wisogetnid/garden-room/plans/MASTER_PLAN_MODULAR.md

# STANDARD OPERATING PROCEDURE (SOP): Cowes Passivhaus Woodworkshop (4x5m) - Modular Version

**Document Status:** High-Fidelity Technical Specification & Construction SOP (Modular Alternative)
**Revision:** v2.2 (High-Performance Magnesium Oxide (MgO) SIP Execution, Quantified & Sequenced)

---

## 0. Step-by-Step Construction Phases

**Phase 1: Groundworks & Foundation (Days 1-5)**
*   **Step 1.1:** Excavate footprint to 150mm depth + foundation perimeter. Lay and compact MOT Type 1 sub-base (6 passes).
*   **Step 1.2:** Screed 25mm blinding sand flat.
*   **Step 1.3:** Assemble 100mm JACKODUR® Atlas XPS interlocking tub.
*   **Step 1.4:** Loose-lay 1200-gauge DPM inside the XPS tub, tape all seams.
*   **Step 1.5:** Place 50mm concrete chairs, lay A193 steel mesh, zip-tie 16mm PEX-a UFH pipework @ 150mm centers.
*   **Step 1.6:** Pour min 100mm C25/30 concrete slab. Power-float finish. Cure for 7-14 days.

**Phase 2: Drainage & Threshold (Days 6-7)**
*   **Step 2.1:** Install 200mm French drain trench with 20mm washed gravel around non-door elevations.
*   **Step 2.2:** Paint liquid waterproof membrane (RIW Flexiseal) heavily over XPS upstand.
*   **Step 2.3:** Install Compacfoam CF200 block at the door threshold directly on the concrete edge. Set Aco HexDrain flush against the XPS upstand. Lap DPM/DPC.

**Phase 3: Superstructure Envelope (Days 8-12)**
*   **Step 3.1:** Secure timber/MgO base plates to the concrete/Compacfoam using M12 resin anchors @ 1200mm centers.
*   **Step 3.2:** Receive 150mm MgO SIP panels (e.g., Dragonboard/SIPit-FR) via rigid shuttle vehicle (crucial for navigating narrow island roads). Erect wall panels and join using insulated splines and structural polyurethane adhesive.
*   **Step 3.3:** *[Factory Pre-Cuts]* Ensure factory has pre-cut openings for dMVHR and the 2 standard windows (North and East elevations) to avoid on-site structural damage.
*   **Step 3.4:** Install continuous top-plate into the top rebate of the wall SIPs.
*   **Step 3.5:** Install 175mm MgO SIP roof panels. Join via insulated splines. Tape internal joints with Tescon Vana.

**Phase 4: Weatherproofing & Exterior (Days 13-17)**
*   **Step 4.1:** Tape all internal SIP seams with Pro Clima Tescon Vana.
*   **Step 4.2:** Install tapered PIR insulation boards on roof (1:60 fall). Fully adhere 1.5mm EPDM membrane and secure UPVC Drip Trim.
*   **Step 4.3:** Install windows and doors into factory-cut openings. Seal with expanding foam and airtight tape.
*   **Step 4.4:** Install guttering and rainwater diverter to 200L water butt.
*   **Step 4.5:** Apply thin-coat silicone render directly to external MgO boards.

**Phase 5: Internal Fit-Out & Services (Days 18-25)**
*   **Step 5.1:** Install 25x50mm service cavity battens internally @ 400mm centers.
*   **Step 5.2:** First-fix electrical wiring, ASHP pipework, and rigid ducting in the service cavity/ceiling. Install dMVHR unit.
*   **Step 5.3:** Install 15mm Fermacell boards over battens. Seal joints.
*   **Step 5.4:** Apply concrete sealer to slab. Loose-lay 7mm PVC floor tiles.
*   **Step 5.5:** Second-fix electrical (sockets, lighting, IR panel, consumer unit).
*   **Step 5.6:** Connect and commission ASHP and dMVHR. Install Copper Earth Bonding strap to ducting.

## 0.1 Potential Risks (Logistics & Compliance)
*   **Transportation Logistics:** Delivery to the Isle of Wight via Red Funnel or Wightlink incurs heavy ferry premiums for 17m articulated lorries (often exceeding £400). Furthermore, narrow rural roads require a "shuttle" service using smaller rigid vehicles to access the final site. Utilizing kits structured for rapid modular assembly (like Direct Sips) helps optimize transport density.
*   **Fire Safety Compliance:** 2024-2026 Approved Document B requires structures within 1m of a boundary to be constructed of "substantially non-combustible materials". The use of A1-rated Magnesium Oxide (MgO) SIP panels eliminates the need for secondary fire-rated boarding and provides up to 4 hours of fire resistance, safely and completely resolving this strict regulation.
*   **Moisture Durability:** Unlike standard OSB panels, MgO boards are inorganic and impervious to moisture. They will not swell, rot, or delaminate during the humid construction phase on the South Coast, drastically reducing weather-related installation risks.

---

## 1. Foundation and Groundworks Specification

**Objective:** Provide a damp-proof, vermin-proof, and thermally isolated base capable of distributing 2.5-tons of static building weight plus heavy dynamic machinery loads.

### 1.1 Groundworks & Slab Execution

| Material Name | Dimensions / Gauge | Fixing Method | Purpose | Estimated Quantity (20m²) |
| :--- | :--- | :--- | :--- | :--- |
| **MOT Type 1 Sub-base** | 150mm depth | Vibrating plate compactor (min 6 passes) | Distribute load to stable clay strata. | ~4 Bulk Bags (approx. 3.4 tonnes) |
| **Blinding Sand** | 25mm depth | Hand screeded flat | Provide a perfectly level bed for the XPS formwork. | ~1 Bulk Bag (approx. 850kg) |
| **Under-Slab Thermal Break** | 100-150mm JACKODUR® Atlas XPS System | Interlocking XPS panels assembled directly on the blinding sand | Prevent cold-bridging into the earth; serves as permanent insulated formwork. | 1 complete Atlas tub system (custom cut) |
| **Damp Proof Membrane (DPM)** | 1200-gauge Polythene | Loose laid *inside* the XPS tub, taped seams | **Critical Placement:** Sits directly between the XPS insulation and the wet concrete. | 1 Roll (4m x 25m) + 1 Roll double-sided butyl |
| **Steel Reinforcement** | A193 Steel Mesh | Suspended on 50mm plastic concrete 'chairs' | Provide tensile strength to concrete; 50mm cover prevents coastal chloride corrosion. | 3 Sheets (4.8m x 2.4m) + ~50 chairs |
| **Heating Integration** | 16mm PEX-a Wet UFH Pipework | Zip-tied to the A193 Steel Mesh @ 150mm centers before pour | **Baseline heating/cooling:** Embedded into the thermal mass. | ~150 linear meters |
| **Concrete Slab** | Min 100mm thick (C25/30 mix) | Poured in-situ, power-floated finish | High-mass structural base; dampens low-frequency machinery vibration. | ~2.5 Cubic Meters |

### 1.3 Ground-to-Wall Interface Details (Slab-to-Wall Junction)

**Objective:** Ensure zero thermal bridging ('Red Line' test), block coastal wind-driven rain from wicking into the timber, and securely anchor the structure to the insulated floating raft.

| Material Name | Dimensions / Gauge | Fixing Method | Purpose | Estimated Quantity |
| :--- | :--- | :--- | :--- | :--- |
| **1. Level Threshold Drainage** | Aco HexDrain (Linear Channel Drain) | Set in concrete directly flush against the rendered 100mm Jackodur XPS upstand at the doorway | **CRITICAL for Flush Transitions:** Prevents pooling patio water from breaching the 0mm internal/external floor level. | ~2 linear meters (at doorway) |
| **2. Perimeter Drainage** | 200mm Wide French Drain | Trench filled with 20mm washed gravel | Ensures coastal wind-driven rain instantly drains away from the JACKODUR® XPS upstand on non-door elevations. | ~14 linear meters + 1 Bulk Bag gravel |
| **3. Upstand Waterproofing**| Liquid-applied Waterproof Membrane (e.g., RIW Flexiseal) | Painted heavily over the XPS upstand, lapping up the Compacfoam block | Prevents hydrostatic pressure from pushing water through the joint. | 1x 5L tub |
| **4. Structural Thermal Break (The "Submarine" Layer)**| **Compacfoam CF200** Block | 140mm x 50mm (or higher to match patio depth), sits directly on the concrete edge | **Zero-Rot Base:** Replaces the traditional timber sole plate at flush threshold zones. | ~2 linear meters (at doorway) |
| **5. DPM / DPC Lapping** | 1200-gauge DPM & Polymeric DPC | DPM folded over slab edge, lapped beneath DPC by min 100mm, sealed with Butyl Tape | Completely seals the concrete slab moisture away from the Compacfoam and the SIP structure. | 1 Roll DPC (225mm) |
| **6. Structural Anchoring** | M12 A4 (316) Stainless Anchor Bolts | Embedded 100mm into concrete via chemical resin @ 1200mm centers | Passes through the sole plate, DPC, and Compacfoam to lock the frame against massive coastal wind uplift. | ~16 units + 2 resin tubes |

**Detailed Ground-to-Wall Load Path & Thermal Connection (At the Threshold & Perimeter):**

1. **The Foundation Base:** The perimeter consists of the solid 100mm structural concrete slab immediately adjacent to the 100mm JACKODUR® XPS foam upstand (which acted as the permanent formwork). While the XPS is a great insulator, it is too soft to support structural weight or hold anchor bolts. 
2. **The "Submarine" Layer (Compacfoam):** A highly engineered, ultra-dense EPS block (Compacfoam CF200) is laid continuously around the perimeter. It is positioned to bear heavily on the solid concrete slab edge while slightly bridging over the softer XPS upstand. This safely transfers the heavy structural load of the wall down into the concrete while simultaneously connecting the wall insulation to the foundation insulation (completing the 'Red Line' thermal envelope). Compacfoam is impervious to rot.
3. **Moisture Encapsulation:** The 1200-gauge Damp Proof Membrane (DPM) from under the slab is folded up the concrete edge, sitting *beneath* the Compacfoam. A heavy-duty polymeric Damp Proof Course (DPC) is then laid directly *on top* of the Compacfoam, fully encapsulating the joint.
4. **Base Plate & Anchoring:** A treated timber (or MgO) base plate sits perfectly level on the DPC. We drill down through the base plate, DPC, and Compacfoam, plunging 100mm deep into the concrete. M12 Stainless Steel anchor rods are secured with chemical resin, violently clamping the base plate and Compacfoam down to the slab.
5. **The SIP Drop & Lock:** The 150mm MgO SIP wall panel features a routed bottom edge (the core foam is recessed, leaving the two 12mm MgO outer skins extending downward). Structural polyurethane adhesive is applied to the base plate, and the SIP panel is dropped *over* it. The heavy MgO skins slide down the sides of the base plate, and the internal PUR core foam rests flat on top. Structural screws are driven through the lower MgO skins directly into the sides of the base plate to permanently lock the wall.

---

## 2. Layered Thermal Envelope Schedule

**U-Value Target Check:** The structural transition to 150mm Magnesium Oxide (MgO) SIPs utilizing a high-density PUR/QuadCore insulation yields an estimated U-value of **~0.15 W/m²K**, seamlessly achieving the Passivhaus fabric requirement in a highly compact wall profile without the need for thick secondary insulation layers.

### 2.1 The Modular Panel 'Sandwich' (Exterior to Interior)

| Material Name | Dimensions / Gauge | Fixing Method | Purpose | Estimated Quantity |
| :--- | :--- | :--- | :--- | :--- |
| **1. External Cladding** | Thin-Coat Silicone Render | Trowel-applied directly to the external MgO board | Replaces complex timber rainscreens. Self-coloured, UV resistant, and maintenance-free. | ~45m² coverage (render + primer) |
| **2. Structural Outer Skin** | 12mm Magnesium Oxide (MgO) Board | Factory-bonded to the insulation core | **A1 Non-Combustible** rating. Impervious to mold, rot, and coastal salt degradation. | (Part of SIP) |
| **3. Thermal Core** | 125mm PUR or Kingspan QuadCore Foam | Injected/Bonded under pressure ($\lambda \approx 0.018 - 0.022$ W/mK) | Exceptional thermal resistance yielding Passivhaus-level U-values in a minimal thickness footprint. | (Part of SIP) |
| **4. Structural Inner Skin** | 12mm Magnesium Oxide (MgO) Board | Factory-bonded to the insulation core | Internal racking strength with a high "screw-pull-out" capacity. | (Part of SIP) |
| **5. Vapour Control Layer / Airtightness** | Pro Clima Tescon Vana Tape | Adhered directly over the internal panel joints | MgO boards are intrinsically airtight. Specialized Passivhaus tape on the joints achieves the required $\le 0.6$ ACH. | ~3 Rolls (30m each) |
| **6. Service Cavity**| 25x50mm Treated Timber Battens | Screwed horizontally into the inner MgO skin @ 400mm centers | Allows routing of all electrical cabling without piercing the airtight MgO envelope. | ~120 linear meters |
| **7. Internal Finish**| 15mm Fermacell Boards | 30mm Fermacell screws + Jointstik glue | High mass acoustic blocking, mitigating the low-frequency noise from workshop machinery. | ~18 boards (1200x2400mm) + 2 tubes glue |

### 2.2 Modular Panel Sealing & Structural Joining Strategy
*   **The Panel-to-Panel Seal:** Traditional timber splines create thermal bridges. All vertical panel-to-panel connections utilize **Insulated Splines** (miniature SIP strips with identical core foam) heavily sealed with structural polyurethane adhesive/expanding foam during assembly to ensure 100% thermal continuity.
*   **Factory Pre-Cuts:** The SIP manufacturer must pre-cut the openings for the dMVHR ventilation unit, and the 2 standard windows (located on the North and East elevations). This eliminates the risk of on-site core-drilling severing internal structural splines.
*   **Airtight Tape Application:** Once assembled, the internal seam lines (where panels meet) must be meticulously taped with Passivhaus-certified **Tescon Vana tape**. Because the inorganic MgO boards are airtight, this single taping step secures the envelope without requiring a full wrapping membrane.
*   **The Tying Plates:** Panels sit on and lock into a treated **timber or MgO/SIP base plate** anchored to the Compacfoam thermal break on the concrete raft. A continuous top-plate is secured across the top rebate of the SIPs, uniting the modules into a rigid, monolithic structural diaphragm capable of supporting heavy solar-ready flat roofs.

### 2.3 Solar-Ready Roof Execution (MgO SIP Integration)

**[OPEN QUESTION / RISK: Check with SIP manufacturer if the 175mm MgO SIP roof panels require an intermediate structural support (like a central Glulam beam) to span the 4m width and support solar panels without long-term deflection, or if they guarantee a clear 4m span.]**

| Material Name | Dimensions / Gauge | Fixing Method | Purpose | Estimated Quantity |
| :--- | :--- | :--- | :--- | :--- |
| **Wall Top Plate** | Timber or MgO/SIP base | Secured into the top rebate of the wall SIPs | Provides a continuous structural bearing plate for the roof panels. | ~18 linear meters |
| **Roof Structure** | 175mm MgO SIP Roof Panels | Spanning from wall to wall, joined via insulated splines | Provides extreme thermal resistance ($\approx 0.15$ W/m²K) and massive structural strength across the 4m span. | ~20m² coverage |
| **The 50cm Overhang** | Cantilevered MgO SIP Panel | Extended beyond the wall line | SIP panels inherently resist cantilever shear forces, providing a rigid 50cm overhang. | (Part of roof SIPs) |
| **Airtightness** | Pro Clima Tescon Vana Tape | Taped directly over the internal SIP roof joints | Ensures the internal airtight envelope is continuously connected. | ~1 Roll (30m) |
| **Waterproofing Deck** | 1.5mm EPDM Membrane | Fully adhered (glued) to the tapered PIR boards or a secondary cover board | 50-year seamless weather protection. | 1 Sheet (~25m²) + 1x 5L adhesive |

### 2.4 Flat Roof Drainage & Rainwater Harvesting (The Water Butt Strategy)
**Objective:** A 20m² flat roof in Cowes will collect approximately 16,000 liters of water annually. Unmanaged runoff cascading off the roof will instantly overwhelm the local perimeter french drain, causing hydrostatic pressure buildup against the JACKODUR® raft upstand and potentially flooding neighboring boundaries.

| Material Name | Dimensions / Gauge | Fixing Method | Purpose | Estimated Quantity |
| :--- | :--- | :--- | :--- | :--- |
| **Roof Fall Setup** | Tapered PIR Insulation Boards | Bonded over the top MgO skin of the roof SIP | Creates a permanent **1:60 fall** directing water toward a single designated low edge (e.g., the rear/West elevation). | ~20m² custom tapered kit |
| **Drip Edge Trim** | Sure-Edge UPVC Drip Trim | Fixed clamping the EPDM membrane | Prevents water from running back under the EPDM and directs it cleanly into the gutter system. | ~6 linear meters |
| **Guttering** | 112mm UPVC Deepflow (Black) | Standard fascia brackets | Higher capacity than half-round gutters to handle intense coastal downpours. | ~6 linear meters + brackets |
| **Rainwater Diverter** | 68mm Downpipe Diverter Valve | Cut into the vertical downpipe | Channels rainwater into the water butt until full. | 1 unit + 1 downpipe (3m) |
| **Water Butt** | 200L to 250L Slimline Butt | Sitting on a stable block plinth | Eco-friendly harvesting for garden use, drastically reducing sudden shock loads on the ground drainage. | 1 unit |

---

## 3. Structural Rigidity & Vibration Logic

**Context:** To maximize the Passivhaus thermal mass effect (the baseline heating of the slab) and handle the extreme point loads of heavy cast-iron machinery, **we will not build a floating timber sub-floor over the concrete.** The machinery will sit directly on the concrete, with the final aesthetic floor finish bonded to it.

### 3.1 Workshop-Optimized Floor Execution

| Material Name | Dimensions / Gauge | Fixing Method | Purpose | Estimated Quantity |
| :--- | :--- | :--- | :--- | :--- |
| **Slab Sealing** | Breathable Concrete Sealer / Densifier | Rolled directly onto the cured, dust-free concrete slab | Prevents concrete dusting under the tiles and protects the slab from accidental spills. | 1x 5L tub |
| **Aesthetic/Wear Deck** | 7mm Heavy-Duty Interlocking PVC Tiles (e.g., Ecotile) | **Loose-laid** directly over the concrete (no adhesive required) | Protects dropped cast-iron hand tools (chisels) from shattering, withstands 200kg machinery point loads. | ~20m² (approx 80 tiles @ 500x500mm) |
| **Perimeter Expansion**| 5mm-10mm Expansion Gap | Hidden beneath a skirting board or flexible trim | Allows the PVC tiles to expand and contract with the UFH temperature fluctuations without buckling. | ~18 linear meters skirting |

### 3.2 Specific Machine Isolation (Vibration Decoupling)
*   **Table Saw & Planer Placement:** Because the machines are sitting on the solid concrete thermal mass, the concrete itself absorbs the low-frequency vibrations. However, to prevent high-frequency motor chatter from radiating into the room, industrial-grade **Sylomer® pads** (color-coded to the machine's static weight) or high-density 15mm ribbed SBR rubber mats must be placed exactly under the four contact feet of the Table Saw and the Planer-Thicknesser.

---

## 4. Workshop Climate & Heating System

### 4.1 Heating Execution Strategy
A "Dual-System Compromise" will be employed. The embedded Wet UFH maintains the thermal battery and provides passive summer cooling, while the IR Panel provides instant top-up heat for the occupant in winter. **Total estimated heat load for 20m² Passivhaus: 1.5kW - 2.0kW.** This is an intentional investment in the future comfort and longevity of the space.

| Material Name | Dimensions / Gauge | Fixing Method | Purpose | Estimated Quantity |
| :--- | :--- | :--- | :--- | :--- |
| **Baseline Thermal Battery** | 16mm PEX-a Pipework (Wet UFH) + 3kW ASHP | Embedded within the 100mm concrete slab @ 150mm centers | Runs continuously via thermostat at 12-14°C (winter) or 19°C (summer). Keeps cast-iron tools dry, mitigates the summer "oven effect". | 1 system |
| **Primary Occupant Heat** | 1.2kW Far-Infrared (FIR) Ceiling Panel | Suspended from ceiling joists over workbench | Switched on upon entry for weekend work. Provides instant radiant warmth directly to the user's body. | 1 panel |
| **Dehumidification** | Smart Compressor Dehumidifier (e.g., MeacoDry Arete 1 12L) | Freestanding on floor. Relies on internal 2.5L-5L tank. | **Zero VCL Penetrations:** Because the Passivhaus envelope is airtight, moisture ingress from the outside is near zero. | 1 unit |
| **Mechanical Ventilation** | Decentralized MVHR (dMVHR) with Summer Bypass | Wall-mounted. **Factory pre-cut by SIP manufacturer** (along with 2 standard windows on North and East elevations) to avoid on-site structural damage. | **The 'Lungs' of the Passivhaus:** Provides continuous fresh air and CO2 extraction without losing heat. *CRITICAL: Must be fitted with G4 (Extract) and F7 (Intake) ISO 16890 filters.* | 1 unit |

---

## 5. Electrical & Dust Integration 

### 5.1 Circuit Schedule & Ducting Geometry

| Material Name | Dimensions / Gauge | Fixing Method | Purpose | Estimated Quantity |
| :--- | :--- | :--- | :--- | :--- |
| **Machine Breakers** | 20A **Type C** RCBOs | Mounted in workshop Consumer Unit | Type C magnetic trip curve withstands the 100A+ inrush surge of 3HP induction motors without nuisance tripping. | 4 units |
| **Sockets** | IP66 Double Switched 13A | Surface mounted to Fermacell | Flap-covers prevent conductive wood dust from bridging internal contacts (fire prevention). | ~6 units |
| **Extraction Trunk** | 100mm Rigid Galvanized Steel Ducting | Rubber-lined acoustic pipe clamps to ceiling | Smooth bore maintains 25 m/s air velocity; metal prevents static electricity sparks (unlike PVC). | ~10 linear meters |
| **Static Protection** | Copper Earth Bonding Strap | Bolted to galvanized ducting and grounded to electrical Earth | **ATEX Safety:** Safely grounds the massive static charge generated by high-velocity wood dust moving through metal ductwork, preventing lethal dust explosions. | 1 unit |
| **Blast Gates** | 100mm Cast Aluminum body with steel slider | Hose-clamped onto vertical machine drops | Maximizes static pressure by isolating idle branches. | 3 units |

> **SOP APPROVAL:** This document standardizes all material dimensions, quantities, gauges, fixing methods, and purposes for contractor execution. All requested parameters (100mm slab, 150mm splash zone, and Type C induction mapping) have been validated and integrated.
