wisogetnid/garden-room/prompts/orchestration.md

@architect: Update the Master Plan with the new [specific change, e.g., external wall insulation specs].

Once finished: @foreman, review the Architect's changes and rework the Step-by-Step execution plan. Ensure the weekend tasks are still viable and that we don't leave the timber frame exposed to Cowes' coastal rain while the user is at work during the week.
