wisogetnid/garden-room/prompts/workshop-research-areas.md

## High-Performance Insulation for Year-Round Workshop Use

This prompt focuses on "Phase Change" and "Vapour Control"—essential for a room that goes from cold (daytime) to warm (evening) quickly.

    Prompt for @librarian:
    "Research a 'High-Thermal-Inertia' insulation strategy for a 20m² workshop in Cowes, UK.

        Compare PIR Boards (100mm+) vs. Superior Multi-foil (e.g., SuperFOIL SF40) for evening use. Calculate the 'Warm-up Time' for each when using a 2kW heater in 5°C external temperatures.

        Document the 'Dew Point' risk for a coastal workshop. When I turn on the heat in the evening, where will the condensation form? Research the necessity of a continuous, taped Vapour Control Layer (VCL) on the warm side to protect cast-iron tool tables from 'flash rusting.'

        Research 'Cold Roof' vs. 'Warm Roof' construction for a 5-degree pitch. Which is less prone to interstitial condensation in the humid Isle of Wight climate?

        Find specs for Breathable Membranes (e.g., Tyvek Housewrap) that offer high salt-spray resistance for coastal locations.
        Save to research/insulation_and_climate.md."

## Planning & Permitted Development (PD)

Cowes has specific areas of Conservation and Article 4 Directions (where PD rights are removed). This prompt forces the agent to check the local Isle of Wight Council rules.

    Prompt for @librarian:
    "Conduct a legal audit for a 4x5m (20m²) detached outbuilding in Cowes, Isle of Wight.

        Verify Permitted Development (Class E) height limits: Confirm the 2.5m total height rule if within 2m of a boundary.

        Check the Isle of Wight Council Planning Portal for 'Article 4 Directions' in Cowes that might restrict outbuildings.

        Research the 'Incidental Use' clause: Does a 'Professional Woodworking Workshop' (potentially generating noise/dust) still qualify as 'incidental,' or does it risk being classified as 'Business Use' requiring Full Planning?

        Document Building Regulations Part L and Part P: Since the room is 20m², it is exempt from most Regs unless it’s within 1m of a boundary. Find the 'Non-combustible cladding' requirements (Part B) for buildings between 15m² and 30m² sited near a fence.
        Save to research/planning_and_regs.md."

## Acoustic & Environmental Impact (The "Good Neighbor" Research)

Since you’ll be working weekends and evenings, noise from a planer or table saw will be highly noticeable in a quiet residential area of Cowes.

    Prompt for @librarian:
    "Research noise mitigation strategies for a residential woodworking shop.

        Find the Rw (Weighted Sound Reduction Index) for a standard timber wall vs. one with Acoustic Mineral Wool (e.g., Rockwool RWA45) and double-layer 15mm Soundbloc plasterboard.

        Document 'Vibration Decoupling' for the floor: Research using 'Resilient Bars' or 'U-Boats' for joists to stop tool vibrations traveling through the ground to the neighbor's house.

        Research 'Acoustic Hoods' for dust extractors and air-intake silencers.

        Find local Cowes/IOW noise ordinance 'quiet hours' to ensure weekend work is compliant.
        Save to research/acoustic_strategy.md."

## Structural Rigidity & Vibration Damping

A standard garden room floor will "bounce" when a 200kg table saw or planer starts up. This ruins precision and creates noise.

    Prompt for @librarian:
    "Research industrial floor specifications for timber-frame workshops.

        Compare Double-Joisting (300mm centers) vs. Engineered I-Joists for a 4m span to eliminate deflection.

        Document the use of Anti-vibration pads (e.g., Sylomer) between the machinery and the floor.

        Research 'Torsion Box' floor construction for maximum rigidity in small footprints.

        Analyze the impact of a 100mm reinforced concrete 'floating' hearth for heavy machinery vs. a standard 22mm P5 chipboard deck.
        Save to research/structural_vibration.md."

## Power & Electrical Load Management

Woodworking tools like thicknessers and dust extractors have high "startup surges" that can trip standard domestic breakers.

    Prompt for @librarian:
    "Conduct a deep dive into Workshop Electrical Systems (UK BS 7671 2026 standards).

        Research Motor Start-up Currents (Inrush Current) for 3HP induction motors and the necessity of Type C or Type D Breakers (MCBs) to prevent nuisance tripping.

        Document the requirements for a Sub-Main Feed from the house: Calculate the voltage drop for a 25m run of 10mm² or 16mm² SWA (Steel Wire Armoured) cable under a 40A load.

        Research 'Emergency Stop' (E-Stop) circuit integration—is a 'shunted' trip for the whole workshop required for safety?

        Analyze the placement of Dust-proof (IP66) sockets to prevent sawdust ingress causing shorts.
        Save to research/electrical_and_machinery.md."

## Dust Extraction & Air Quality (COSHH Compliance)

In a 20m² space, fine dust (MDF/Hardwood) becomes a health and explosion risk within minutes without a proper "Local Exhaust Ventilation" (LEV) system.

    Prompt for @librarian:
    "Analyze dust management systems for small-scale workshops.

        Compare Single-Stage Bag Extractors vs. Two-Stage Cyclones. Find the CFM (Cubic Feet per Minute) requirements for a 100mm duct run over 5 meters.

        Research 'Static Dissipative' Ducting (Grounding)—document the risk of static discharge in PVC pipes causing sawdust explosions.

        Find specs for M-Class or HEPA filtration units that recycle air back into the room to maintain heat vs. venting outside.

        Research ambient air cleaners (overhead units) and their effectiveness in a 50m³ volume.
        Save to research/dust_extraction_physics.md."

## Foundation & Soil Mechanics (The "Ground" Deep-Dive)

    Prompt for @librarian:
    "Research soil-specific structural risks for 2026. Compare Ground Screws (specifically Grade S235 steel or better) against Mini-piles and Concrete Rafts.

        Find the 'heave' risk and 'shrink-swell' data for clay-heavy soils in the UK/Northern Europe.

        Document the necessary torque requirements for ground screws to support a timber-frame building with a live/dead load of 250kg/m².

        Research sub-floor ventilation—how many air bricks or what size of a 'void' is required to prevent joist rot in a 12m² building?
        Save to research/foundations_structural.md."

## The "Smart" Envelope (Energy & Automation 2026)

    Prompt for @librarian:
    "Investigate 2026 smart-glass and high-spec glazing trends.

        Compare Vacuum Insulated Glazing (VIG) vs. Triple Glazing. Find the U-value difference and the weight-per-square-meter (to see if the timber frame needs extra bracing).

        Research Matter-compatible motorized blind systems that can be integrated into the window frame during construction.

        Find the cost-benefit of Solar Reflective Coatings for South-facing garden rooms to prevent the 'greenhouse effect' without using AC.
        Save to research/glazing_and_automation.md."

## Thermal Mass vs. Instant Heat (Climate Strategy)

    Prompt for @librarian:
    "Analyze the physics of heating a small, detached timber structure.

        Compare Infrared (IR) Heating Panels (radiant) vs. Air-to-Air Heat Pumps (convection).

        Specifically research 'Heat Up Time' vs. 'Energy Usage' for a building that is used 8 hours a day vs. one used 24/7.

        Look for data on Phase Change Materials (PCM)—can we add a small amount of thermal mass to a timber wall to keep it warm at night?
        Save to research/climate_control_strategy.md."

## The "Sustainability Scorecard" (Materials & Toxins)

    Prompt for @librarian:
    "Conduct a sustainability and health audit of common garden room materials.

        Research the VOC (Volatile Organic Compound) levels in OSB/3 vs. Plywood vs. Medite Tricoya.

        Compare the Embodied Carbon of Siberian Larch cladding (imported) vs. Thermally Modified British Ash or Box Profile Steel.

        Find the 'End of Life' recyclability of EPDM rubber vs. Zinc roofing.
        Save to research/sustainability_audit.md."

## The Moisture & Rust Management Prompt

    Prompt for @librarian:
    "Research a comprehensive 'Moisture & Anti-Corrosion' strategy for a 20m² timber workshop in the coastal environment of Cowes, Isle of Wight.

        The 'Dew Point' Analysis: Calculate the condensation risk for a building that is unheated during the day but heated to 18°C in the evenings. Where is the dew point likely to sit in a wall with 100mm PIR insulation?

        Membrane Specification:

            Compare Vapour Control Layers (VCL) vs. Intelligent/Variable Membranes (e.g., pro clima INTELLO) that can dry towards the inside in summer.

            Specify a Marine-Grade Breather Membrane for the external side that resists salt-spray degradation.

        Tool Protection (Micro-climates):

            Research the use of Desiccant Dehumidifiers (which work at low temperatures) vs. Compressor models for a workshop environment.

            Investigate 'GoldenRod' style dehumidifier heaters for enclosed tool cabinets.

        Ventilation vs. Rust:

            Document the trade-off between Passive Vents (which bring in salty, humid air) and a Mechanical Ventilation Heat Recovery (MVHR) unit for a small 20m² space.

            Analyze how Dust Accumulation acts as a 'sponge' for coastal moisture and accelerates tool corrosion.

        Floor & Ground Moisture:

            Specify the overlap and sealing requirements for the Damp Proof Membrane (DPM) to the Damp Proof Course (DPC) on a timber-sole plate.
            Save findings to research/moisture_and_rust_prevention.md."
