wisogetnid/garden-room/plans/first-draft.md

# **Technical Engineering and Implementation Analysis for a High-Efficiency Insulated Raft Foundation in Cowes**

This technical plan details the construction of a high-efficiency insulated raft foundation for a 4m x 5m wood workshop in Cowes, Isle of Wight. Utilizing the Jackodur Atlas system, this design provides a thermal-bridge-free envelope suitable for Passivhaus-standard performance, optimized for a manual, solo build with restricted site access.

## **1\. Geotechnical Context: Cowes Clay**

The site in Cowes is characterized by cohesive clay (Hamstead Member and Bembridge Marls), which is susceptible to seasonal volume changes.1 A raft foundation is appropriate as it "floats" on the soil, distributing loads evenly to minimize differential settlement in reactive clay. To ensure stability, the structure is decoupled from the clay via a non-frost-susceptible hardcore base, and a specialized drainage system is used to allow for a flush ground-level finish.

## **2\. Technical Specification and Build-Up (Flush Finish)**

This specification is designed for a flush ground-level finish to provide seamless access while maintaining a super-insulated envelope for humidity control.

| Layer | Thickness | Material/Technical Detail |
| :---- | :---- | :---- |
| **Concrete Slab** | 150mm | Reinforced C25/30 mix; serves as the thermal mass for the UFH system.3 |
| **Separation Layer (DPM)** | \<1mm | 1200-gauge DPM placed **over** the insulation to prevent grout loss and act as a moisture barrier. |
| **Main Insulation** | 150mm | Jackodur Atlas XPS ($R\_D \\approx 4.25 \\text{ m}^2\\text{K/W}$); eliminates thermal bridging. |
| **Blinding Layer** | 25mm | Sharp sand; provides a precision-leveled substrate for the insulation elements. |
| **Sub-Base** | 150mm | MOT Type 1; compacted in two 75mm layers for maximum stability. |
| **Total Build-Up** | **475mm** | Total vertical depth from Finished Floor Level (FFL) to the substrate. |

### **Weather-Proofing & Access Strategy**

* **Flush Finish:** The slab is set flush with the ground for aesthetics and access.  
* **Perimeter French Drain:** A 150mm-wide trench filled with 16/32mm clean filter gravel surrounds the structure to break the capillary bridge and direct surface water to the hardcore layer.  
* **Linear Threshold Drain:** An ACO linear drain is installed at the doorway to provide a solid bridge for heavy tools while intercepting water runoff.

## **3\. Logistical Engineering: The Manual Transit Challenge**

Moving materials 30m via a wheelbarrow-width path requires strict volume management.

### **Excavation Volume and Effort**

The Jackodur system requires a 40cm "over-dig" beyond the slab edge for the perimeter elements, creating a 4.8m x 5.8m footprint ($27.84 \\text{ m}^2$).5

* **Total Excavation Depth:** 475mm below natural ground level.  
* **Undisturbed Volume (Bank):** \~13.22 $\\text{m}^3$ of clay subsoil.  
* **Bulked Volume (Loose):** Clay expands by \~30% when disturbed. Total loose material: **\~17.2 $\\text{m}^3$**.6  
* **Transport Logistics:** Moving 17.2 $\\text{m}^3$ with an 85L barrow loaded to 50L (0.05 $\\text{m}^3$) requires approximately **344 round trips**.8  
* **Estimated Duration:** At a rate of 1 $\\text{m}^3$ per 5–8 hours in stiff clay, excavation will take **85 to 135 man-hours**.10

## **4\. Work-Plan: Phased Implementation**

### **Phase 1: Substrate Preparation & Drainage**

1. **Datum Setting:** Establish the FFL using a laser level, flush with the highest natural ground point.  
2. **Manual Dig-Out:** Excavate the area to 475mm depth. Create a 150mm shoulder for the gravel drain and a deeper pocket at the door for the linear drain bedding.  
3. **Hardcore:** Lay 150mm of MOT Type 1 in two 75mm lifts. Compact each lift thoroughly with a hired petrol wacker plate.  
4. **Blinding:** Apply 25mm of sharp sand. Level to a tolerance of $+/- 1$ cm over 5m to ensure the Jackodur boards fit without gaps.5

### **Phase 2: Insulation, Membrane & UFH**

1. **Jackodur Installation:** Assemble the 150mm Jackodur Atlas perimeter and area elements according to the custom plan.  
2. **DPM Separation Layer:** Install the 1200-gauge DPM **over** the top of the insulation boards. Lap the DPM up the inside of the vertical formwork upstands and secure it so it can eventually be joined to the wall's DPC.5  
3. **Reinforcement:** Place A393 steel mesh on 40/50mm grade plate spacers (wide bases prevent membrane punctures).12  
4. **UFH Piping:** Secure the 16mm pipe to the mesh at 200mm centers. Pressure test the 100m loop to 6 bar for 24 hours before the pour.14

### **Phase 3: Threshold & Concrete**

1. **Linear Drain:** Bed the threshold drain channel on 50mm of concrete at the doorway. Ensure the grate is 3-5mm below the slab level.  
2. **Line Pump Pour:** Pump 3.5 $\\text{m}^3$ of C25/30 concrete from the parking area via a 30m flexible hose.16  
3. **Finishing:** Level the concrete flush with the Jackodur formwork and the threshold drain edge.5  
4. **Perimeter Fill:** Once set, fill the remaining 150mm trench with 16/32mm clean filter gravel.

## **5\. Tools, Consumables, and Price Points (Isle of Wight Estimates)**

| Item | Quantity/Spec | Est. Cost (inc. VAT) | Source |
| :---- | :---- | :---- | :---- |
| **Jackodur Atlas (150mm)** | 20 $\\text{m}^2$ System | £2,300 \- £2,700 |  |
| **MOT Type 1** | 10 Bulk Bags | £550 \- £620 | 18 |
| **Sharp Sand** | 1 Bulk Bag | £62 \- £68 | 20 |
| **A393 Steel Mesh** | 4 Sheets (2.0m x 3.6m) | £250 \- £320 | 22 |
| **Concrete C25/30** | 3.5 $\\text{m}^3$ (inc. pump mix) | £550 \- £650 | 24 |
| **Concrete Line Pump** | 1 Day Hire | £280 \- £350 | 25 |
| **Linear Threshold Drain** | 1m Kit \+ Connectors | £50 \- £80 |  |
| **Filter Gravel (16/32mm)** | 1 Bulk Bag | £65 \- £75 | 21 |
| **Soil/Clay Skips** | 4 x 6-yard Inert Skips | £760 \- £820 | 27 |
| **Wacker Plate Hire** | Weekend Hire | £80 \- £100 | 29 |
| **1200g DPM Roll** | 4m x 20m | £40 \- £60 | 31 |
| **UFH 16mm Pipe & Manifold** | 120m Coil \+ 2-Port | £250 \- £350 | 33 |
| **Total Est. Budget** |  | **£5,337 \- £6,273** |  |

#### **Works cited**

1. Geology as a control on landslides on the Isle of Wight: an overview \- NERC Open Research Archive, accessed February 22, 2026, [https://nora.nerc.ac.uk/id/eprint/16091/1/Jenkins\_Landslides\_PGEOLA-D-11-00038R1.pdf](https://nora.nerc.ac.uk/id/eprint/16091/1/Jenkins_Landslides_PGEOLA-D-11-00038R1.pdf)  
2. Coastal Slope Stability at Cowes and Gurnard, Isle of Wight, accessed February 22, 2026, [https://digitalservices.iow.gov.uk/documents/download/coastal-slope-stability-at-cowes-and-gurnard-isle-of-wight-advice-to-homeowners-leaflet](https://digitalservices.iow.gov.uk/documents/download/coastal-slope-stability-at-cowes-and-gurnard-isle-of-wight-advice-to-homeowners-leaflet)  
3. Concrete Cost per m³ \- Concretecalculate.co.uk, accessed February 22, 2026, [https://concretecalculate.co.uk/concrete-cost-estimators/concrete-cost-per-m%C2%B3/](https://concretecalculate.co.uk/concrete-cost-estimators/concrete-cost-per-m%C2%B3/)  
4. How Much Does Ready Mix Concrete Cost? \- MyBuilder, accessed February 22, 2026, [https://www.mybuilder.com/new-build/price-guides/ready-mix-concrete-cost](https://www.mybuilder.com/new-build/price-guides/ready-mix-concrete-cost)  
5. bewi\_jackodur-atlas\_training.pdf  
6. Bulking Spoil Volume In Excavations \[Free Online Calculator\] \- THS Concepts, accessed February 22, 2026, [https://www.ths-concepts.co.uk/how-to-calculate-earthwork-bulking/](https://www.ths-concepts.co.uk/how-to-calculate-earthwork-bulking/)  
7. Material Density Tables to Help Estimate Earthwork Volumes | Cat | Caterpillar, accessed February 22, 2026, [https://www.cat.com/en\_US/articles/ci-articles/earthwork-volumes-reference-tables.html](https://www.cat.com/en_US/articles/ci-articles/earthwork-volumes-reference-tables.html)  
8. How many wheelbarrows make one cubic? \- Quora, accessed February 22, 2026, [https://www.quora.com/How-many-wheelbarrows-make-one-cubic](https://www.quora.com/How-many-wheelbarrows-make-one-cubic)  
9. 4\. Earthmoving Methods, accessed February 22, 2026, [https://www.fao.org/fishery/docs/CDrom/FAO\_Training/FAO\_Training/General/x6708e/x6708e04.htm](https://www.fao.org/fishery/docs/CDrom/FAO_Training/FAO_Training/General/x6708e/x6708e04.htm)  
10. Manual excavation duration \- 1 Cu. Mtr. \- Planning Planet, accessed February 22, 2026, [https://planningplanet.com/forums/planning-scheduling-programming-discussion/560899/manual-excavation-duration-1-cu-mtr](https://planningplanet.com/forums/planning-scheduling-programming-discussion/560899/manual-excavation-duration-1-cu-mtr)  
11. Excavation Man Hours Guide | PDF | Manufactured Goods | Transport \- Scribd, accessed February 22, 2026, [https://www.scribd.com/document/505106326/EXCAVATION-MAN-HOUR](https://www.scribd.com/document/505106326/EXCAVATION-MAN-HOUR)  
12. 40/50mm Plastic Grade Plate Spacers \- Builder Depot, accessed February 22, 2026, [https://www.builderdepot.co.uk/40-50mm-plastic-grade-plate-spacers](https://www.builderdepot.co.uk/40-50mm-plastic-grade-plate-spacers)  
13. 10mm A393 Steel Reinforcement Mesh 1200mm x 2400mm \- Builder Depot, accessed February 22, 2026, [https://www.builderdepot.co.uk/10mm-a393-high-tensile-steel-reinforcement-mesh-sheet-1200mm-x-2400mm](https://www.builderdepot.co.uk/10mm-a393-high-tensile-steel-reinforcement-mesh-sheet-1200mm-x-2400mm)  
14. Water Underfloor Heating Guide & Installation Instructions \- The Floor Heating Warehouse, accessed February 22, 2026, [https://www.thefloorheatingwarehouse.co.uk/underfloor-heating-guide/](https://www.thefloorheatingwarehouse.co.uk/underfloor-heating-guide/)  
15. Sizing UFH systems when using heat pumps \- P\&H Engineering, accessed February 22, 2026, [https://www.pandhengineering.co.uk/advice/sizing-ufh-systems-when-using-heat-pumps](https://www.pandhengineering.co.uk/advice/sizing-ufh-systems-when-using-heat-pumps)  
16. Concrete Pump Hire | 2 Brothers Concrete & Pumping, accessed February 22, 2026, [https://www.2brothers.uk/services/concrete-pump-hire](https://www.2brothers.uk/services/concrete-pump-hire)  
17. Concrete Pumping Alton \- 01420 370 247, accessed February 22, 2026, [https://www.concrete247.com/services/concrete-pump-hire-alton](https://www.concrete247.com/services/concrete-pump-hire-alton)  
18. Type 1 MOT Granite \- Bulk Bags \- Mick George, accessed February 22, 2026, [https://www.mickgeorge.co.uk/product/aggregates/bulk-bags/type-1-mot-granite](https://www.mickgeorge.co.uk/product/aggregates/bulk-bags/type-1-mot-granite)  
19. MOT Type 1 Sub Base Bulk Bag \- Trade Superstore Online, accessed February 22, 2026, [https://www.tradesuperstoreonline.co.uk/products/g-938251](https://www.tradesuperstoreonline.co.uk/products/g-938251)  
20. 0-4mm Grit Sharp Sand \- Bulk Bag only £47.00 \- KPT Timber, accessed February 22, 2026, [https://www.kpttimber.co.uk/bulk-bags/0-4mm-grit-sharp-sand/](https://www.kpttimber.co.uk/bulk-bags/0-4mm-grit-sharp-sand/)  
21. Building Materials and Aggregates \- Isle of Wight, accessed February 22, 2026, [https://www.westwightskips.com/building-materials/](https://www.westwightskips.com/building-materials/)  
22. A393 Reinforcing Mesh 10mm Dia Bar 3.6mx2m \- Lawsons, accessed February 22, 2026, [https://www.lawsons.co.uk/a393-reinforcing-mesh-10mm-dia-bar-36mx2m-g10060010](https://www.lawsons.co.uk/a393-reinforcing-mesh-10mm-dia-bar-36mx2m-g10060010)  
23. A393 Mesh \- In Stock Now | 10mm Rebar Mesh | RPO \- Reinforcement Products Online, accessed February 22, 2026, [https://www.reinforcementproductsonline.co.uk/a393-standard-mesh.html](https://www.reinforcementproductsonline.co.uk/a393-standard-mesh.html)  
24. Ready Mix Concrete Prices London 2026, accessed February 22, 2026, [https://rmsconcrete.co.uk/ready-mix-concrete-prices-2026/](https://rmsconcrete.co.uk/ready-mix-concrete-prices-2026/)  
25. Ready Mix Concrete: Cost Breakdown 2026 | Try Our Job Estimator Tool \- Checkatrade, accessed February 22, 2026, [https://www.checkatrade.com/blog/cost-guides/ready-mix-concrete-cost/](https://www.checkatrade.com/blog/cost-guides/ready-mix-concrete-cost/)  
26. uk line pump pricing, accessed February 22, 2026, [http://concretepumping.com/topic/uk-line-pump-pricing](http://concretepumping.com/topic/uk-line-pump-pricing)  
27. Isle of Wight Skip Hire, accessed February 22, 2026, [https://www.westwightskips.com/skip-hire-on-the-isle-of-wight/](https://www.westwightskips.com/skip-hire-on-the-isle-of-wight/)  
28. Skip Hire Prices \- Isle of Wight Skip Hire, accessed February 22, 2026, [https://www.isleofwightskiphire.co.uk/skip-prices/](https://www.isleofwightskiphire.co.uk/skip-prices/)  
29. Wacker Medium Petrol Compactor Plate \- Island Hire Centre, accessed February 22, 2026, [https://www.islandhirecentre.co.uk/product/56/Medium-Petrol-Compactor-Plate/](https://www.islandhirecentre.co.uk/product/56/Medium-Petrol-Compactor-Plate/)  
30. Tool hire | TradePoint, accessed February 22, 2026, [https://www.trade-point.co.uk/tool-hire.cat](https://www.trade-point.co.uk/tool-hire.cat)  
31. Visqueen Radon R400 Membrane 4m x 20m (80m2) | insulationuk.co.uk, accessed February 22, 2026, [https://www.insulationuk.co.uk/products/visqueen-radon-r400-membrane-4m-x-25m-100sqm](https://www.insulationuk.co.uk/products/visqueen-radon-r400-membrane-4m-x-25m-100sqm)  
32. Visqueen Radon Membrane R400 (4m x 20m) \- Drainage & Civils Direct, accessed February 22, 2026, [https://drainageandcivilsdirect.co.uk/product/visqueen-radon-membrane-r400-4m-x-20m/](https://drainageandcivilsdirect.co.uk/product/visqueen-radon-membrane-r400-4m-x-20m/)  
33. 20m2 Water Underfloor Heating Kit \- Renewable Products Warehouse, accessed February 22, 2026, [https://renewableproductswarehouse.co.uk/products/20m2-underfloor-heating-kit](https://renewableproductswarehouse.co.uk/products/20m2-underfloor-heating-kit)  
34. Single Circuit Mixing Underfloor Manifold Valve Unit \- Up To 20m2, accessed February 22, 2026, [https://theunderfloorheatingsite.co.uk/shop/water-under-floor-heating/underfloor-heating-manifolds/single-circuit-mixing-valve-unit-up-to-20m2/](https://theunderfloorheatingsite.co.uk/shop/water-under-floor-heating/underfloor-heating-manifolds/single-circuit-mixing-valve-unit-up-to-20m2/)
