wisogetnid/garden-room/research/passivhaus-requirements-research.md

# **Technical Specification and Certification Roadmap: Elevating the Cowes Woodworkshop to Passive House Standards**

The realization of the Cowes Passivhaus Woodworkshop, as outlined in the provided master plan, represents an ambitious intersection of industrial utility and high-performance building science. Achieving the Passive House standard for a small-scale, detached structure requires a rigorous departure from conventional UK garden room construction. While traditional outbuildings are often exempted from the stringent thermal requirements of Approved Document Part L, the commitment to the Passive House standard necessitates a holistic, fabric-first strategy that addresses the unique thermodynamic challenges inherent in small buildings.1 At the core of this endeavor is the fundamental requirement to minimize energy demand for heating and cooling to less than 15 kWh/m² per year, while ensuring a level of airtightness—specifically $\\leq 0.6$ air changes per hour at 50 Pascals—that is nearly twenty times more demanding than standard UK building regulations.4  
The physics of small-scale structures introduces a significant hurdle known as the surface-area-to-volume ($A/V$) ratio. In larger buildings, the ratio of the external envelope to the internal heated volume is relatively low, providing a natural buffer against heat loss. However, a garden workshop typically possesses a high $A/V$ ratio, meaning there is a larger proportional "skin" through which energy can be transferred. This physical reality dictates that for the Cowes workshop to achieve certification, its insulation levels must be significantly higher than those of a larger detached house to compensate for the higher relative heat loss.7 This report analyzes the existing master plan against the international Passive House criteria, providing detailed engineering pathways to ensure the structure meets the rigorous demands of the Passive House Institute.2

## **The Thermodynamics of Small-Scale Detached Structures**

When assessing the feasibility of Passive House standards for the workshop, one must first address the "small house problem." In building modeling, energy demand is often expressed as a function of the treated floor area. For a structure like the Cowes workshop, which may occupy a footprint of only 20 to 30 square meters, the heat loss through every junction, window frame, and door threshold becomes disproportionately significant.10 The Passive House Planning Package (PHPP) accounts for these non-linearities, but it often reveals that smaller buildings require "super-insulation" thicknesses approaching 300mm to 400mm to achieve the same annual heating demand as a larger building with 200mm of insulation.7  
The environmental context of Cowes, located on the Isle of Wight, adds a layer of complexity regarding maritime humidity and wind loading. High wind speeds increase the pressure differential across the building envelope, which can exacerbate any minor leaks in the air barrier.12 Consequently, the airtightness strategy must not only meet the $n\_{50} \= 0.6$ ACH threshold but must also be robust enough to withstand fluctuating coastal pressures without degrading over time.14

| Metric | Passive House Requirement | UK Building Regulations (Part L 2021\) | Cowes Workshop Target |
| :---- | :---- | :---- | :---- |
| Space Heating Demand | $\\leq 15$ kWh/m²/year | $\\approx 40$ \- $60$ kWh/m²/year | $\\leq 15$ kWh/m²/year |
| Primary Energy Demand | $\\leq 60$ kWh/m²/year | N/A | $\\leq 60$ kWh/m²/year |
| Airtightness ($n\_{50}$) | $\\leq 0.6$ ACH @ 50 Pa | $8.0$ $\\text{m}^3/(\\text{h}\\cdot\\text{m}^2)$ | $0.6$ ACH @ 50 Pa |
| Thermal Comfort | $\\leq 10\\%$ hours $\> 25^{\\circ}\\text{C}$ | No specific limit | $\\leq 5\\%$ hours $\> 25^{\\circ}\\text{C}$ |
| Typical Wall U-Value | $0.10 \- 0.15$ W/m²K | $0.18$ W/m²K | $0.14$ W/m²K |

4

## **Substructure and Foundation Engineering**

The master plan specifies the use of the JACKODUR® Atlas XPS System, which is a critical choice for Passive House certification. Conventional foundations often create a massive thermal bridge where the floor slab meets the external walls, allowing heat to conduct directly into the ground.7 The Atlas system solves this by creating an "insulated tub" that completely decouples the structural concrete from the soil.3 This eliminates the perimeter cold bridge and ensures the slab itself becomes a thermal battery, stabilizing the internal temperature.18  
The choice of 150mm of MOT Type 1 sub-base, compacted to distribute loads to the clay strata, provides the necessary structural stability for heavy woodworking machinery.3 In a woodworking context, vibration control is as important as thermal performance. The master plan’s inclusion of Sylomer® pads or SBR rubber mats to decouple machinery from the power-floated concrete slab is a sophisticated measure that protects the building’s airtight seals from mechanical fatigue.3 Continuous vibration could potentially stress the taped joints of the vapor control layer (VCL), making this decoupling essential for long-term airtightness.14  
Moisture management at the foundation level is achieved through a 1200-gauge Polythene Damp Proof Membrane (DPM) with taped seams.1 For Passive House certification, this membrane must be perfectly integrated with the wall’s VCL to form a continuous air barrier. The transition from the floor membrane to the wall VCL is a frequent failure point in blower door tests; therefore, a specialized airtightness tape, such as Pro Clima Tescon Vana, must be used at this junction.3

## **Hybrid Wall Construction: Multi-Foil and Fiber Integration**

The wall assembly described in the master plan is a multi-functional system designed to optimize thermal resistance while maintaining hygrothermal safety.3 The 140mm C24 timber studs, infilled with Rockwool RW3, provide the primary structural and acoustic core.3 However, timber studs themselves have a thermal conductivity ($\\lambda \\approx 0.13 \\text{ W/mK}$) that is significantly higher than the insulation between them ($\\lambda \\approx 0.035 \\text{ W/mK}$), creating what is known as a "repeating thermal bridge".11  
To mitigate this, the master plan incorporates 50mm of rigid wood fiber board applied externally.3 This layer acts as a continuous thermal wrap, "shading" the timber studs from the external environment and significantly reducing the overall U-value of the wall.22 Wood fiber is uniquely suited for this application because it is "vapor-open," allowing moisture within the frame to migrate safely to the outside, thus preventing mold or rot.21  
The integration of SuperFOIL SF19+ multifoil insulation is the technical catalyst that brings the wall U-value down to the target 0.14 W/m²K.3 Multifoil insulation addresses three modes of heat transfer: conduction through its internal wadding, convection through the air gaps it requires, and radiation through its nano-coated foil layers.25 In a maritime climate like Cowes, the radiant barrier property is particularly valuable, as it reflects solar heat gain during summer months, reducing the cooling load on the air source heat pump.27

| Layer | Material | Function | Thickness |
| :---- | :---- | :---- | :---- |
| External Cladding | James Hardie Fibre Cement | Fire-rated rainscreen | 8-10mm |
| Ventilation Path | Timber Battens | Moisture evaporation | 25mm |
| External Insulation | Wood Fibre Board | Thermal bridge elimination | 50mm |
| Core Structure | C24 Timber / Rockwool RW3 | Structure and acoustics | 140mm |
| Radiant Barrier | SuperFOIL SF19+ | Radiation and VCL | 45mm |
| Interior Board | Fermacell | Fire and acoustic mass | 15mm |

1

## **Roof Design: Warm Roof Physics and Solar Future-Proofing**

The workshop’s roof is specified as a "warm roof" design, utilizing 150mm of rigid PIR boards.3 In a warm roof configuration, the insulation is placed above the structural joists, keeping the entire timber structure at a consistent, warm temperature.1 This is superior to "cold roof" designs common in garden rooms, which require complex ventilation paths to prevent condensation within the joist space.1 For Passive House compliance, the roof must achieve a U-value of approximately 0.11 to 0.15 W/m²K, which the 150mm PIR thickness supports.16  
The master plan’s specification of 47x150mm C24 joists at 400mm centers is a critical forward-looking decision.3 Standard roof joists are often spaced at 600mm, but the closer centers are necessary to support the significant dead load of a future solar photovoltaic (PV) array.3 Because the workshop aims for high performance, solar energy will be vital to offset the electrical loads of heavy machinery and the air source heat pump.4  
Waterproofing is provided by a 1.5mm EPDM membrane with a 50-year life expectancy.3 EPDM is highly durable but requires careful detailing at the eaves to maintain the continuity of the airtight layer. The tapered PIR boards, creating a 1:60 fall, ensure that rainwater is efficiently harvested into 200L–250L water butts, aligning the building with broader sustainable water management goals.3

## **The "Red Line" Strategy for Airtightness and Vapor Control**

The most rigorous aspect of Passive House certification is the airtightness requirement of $\\leq 0.6$ air changes per hour ($n\_{50}$).5 This is not merely an energy-saving measure; it is essential for the protection of the building's fabric. If warm, moist indoor air leaks into the cold structure, it will condense, leading to interstitial condensation and structural decay.12  
The master plan utilizes Pro Clima Intello Plus as the primary vapor control and airtightness layer.3 Intello Plus is an "intelligent" membrane; its vapor resistance varies depending on the average humidity.19 In the winter, it becomes more resistant to protect the timber frame from moisture ingress; in the summer, it becomes more permeable to allow the wall to dry toward the inside if necessary.19 This dual-action behavior is particularly important in a woodworking workshop where moisture levels can spike during finishing or wood drying processes.32  
To achieve the 0.6 ACH target, the "Red Line" method must be employed during the design phase. An architect traces a continuous line around the building’s section to represent the air barrier.13 Every time the line is broken—for a pipe, a wire, or a window—a specific detail must be drawn to seal that penetration. In the workshop, the primary penetrations will include:

1. **Electrics:** Sockets should be surface-mounted on the internal Fermacell board to avoid puncturing the VCL, as specified in the master plan’s use of IP66 surface-mounted sockets.3  
2. **HVAC:** The air source heat pump lines and MVHR ducts must use specialized EPDM grommets where they pass through the envelope.14  
3. **Dust Extraction:** If venting outside, this creates a massive $100\\text{mm}$ to $150\\text{mm}$ hole in the air barrier, which requires a specialized airtight damper.35

| Component | Airtightness Material | Typical Failure Point |
| :---- | :---- | :---- |
| Floor to Wall | Tescon Vana Tape | Creases in the membrane at corners |
| Wall to Roof | Intello Plus Overlap | Insufficient adhesive pressure |
| Windows/Doors | Contega Fivo Tape | Incorrect seal to the frame profile |
| Pipe Penetrations | Kaflex/Roflex Grommets | Sizing the grommet too large for the pipe |

14

## **Fenestration: Triple-Glazing and Frame Thermal Performance**

In a garden room, windows and doors are traditionally the weakest thermal links.20 To reach Passive House standards, the workshop must move beyond standard double-glazing. Passive House windows are characterized by whole-window U-values ($U\_w$) of less than 0.8 W/m²K.5 This is achieved through triple-glazing with two low-emissivity coatings and insulated spacers that reduce heat loss at the glass edge.29  
The frames themselves must be highly insulated. Brands such as Internorm, Norrsken, and AT-ECO provide frames made from timber-aluminum composites or uPVC with integrated thermal breaks.37 The master plan notes the importance of compliant doors and windows with safety glazing.3 For a woodworking workshop, the choice of window opening style is critical; "Tilt and Turn" windows are often preferred because they utilize compression seals that provide a more airtight closure than standard sliding or outward-opening casements.19  
A secondary benefit of these high-performance windows is acoustic insulation. The triple-pane configuration, combined with the airtight seals, will significantly reduce the noise of machinery escaping the workshop, which is a vital consideration for garden buildings in residential areas.1

## **Mechanical Ventilation with Heat Recovery (MVHR) and IAQ**

In a highly airtight building, natural ventilation through gaps and cracks is non-existent. Without mechanical ventilation, carbon dioxide, humidity, and pollutants would quickly reach dangerous levels.32 An MVHR system is the mandatory "lung" of a Passive House.42 It extracts stale air and uses its heat to warm incoming fresh air with an efficiency of up to 90%.42  
For the Cowes workshop, the MVHR system must be sized for the volume of the space and the number of occupants. A standard rate of 30 $\\text{m}^3/\\text{h}$ per person is recommended, but in a workshop, the system may need to handle additional particulate filtration.31 The system should include F7 pollen filters to remove external pollutants and protect the heat exchanger from workshop dust.32  
Furthermore, the master plan includes a 1.2kW Far-Infrared (FIR) Ceiling Panel.3 Infrared heat does not warm the air; it warms objects and people directly. This is an ideal complement to an MVHR system because it provides instant comfort for the woodworker even if the air temperature is set to a lower "baseline" of $12\\text{-}14^{\\circ}\\text{C}$ to save energy.3

## **The Industrial Extraction Paradox: Dust vs. Airtightness**

The most significant challenge for a woodworking workshop pursuing Passive House standards is the Local Exhaust Ventilation (LEV) system. Woodworking machinery requires a high-volume dust extractor, which typically moves air at rates between 350 and 900 CFM.48 In an airtight Passive House, if this air is extracted and vented outside, the building will instantly depressurize. This creates a vacuum that can prevent doors from opening, strain the extractor motor, and potentially backdraft any combustion appliances in the main house if they are on a shared system.36

### **Strategy 1: The Internal Recirculating System**

The most efficient approach is to use an extractor with a high-efficiency filter (M-Class or H-Class) that cleans the air and returns it directly to the workshop.33 This keeps the air pressure balanced and preserves the energy used to heat the air.33 The master plan’s emphasis on heavy-mass Fermacell boards and Rockwool insulation will help dampen the noise from an internal extractor.3

### **Strategy 2: Motorized Makeup Air**

If the extractor must vent outside—for example, when using high-VOC finishes or sprays—the building must have an automated makeup air system.49 This involves a motorized damper, such as the Broan MD6TU or MD10TU, which is interlocked with the dust extractor.36 When the extractor turns on, the damper opens to allow fresh outdoor air in at the same rate, preventing depressurization.49 This air should ideally be filtered and tempered to maintain the workshop's comfort levels.49

| Extractor Type | Pros | Cons | Passive House Suitability |
| :---- | :---- | :---- | :---- |
| Internal Recirculating | Retains 100% of heat; maintains pressure | Requires high-grade HEPA filters | High |
| External Vent (Open) | Removes all odors and fine dust | Causes vacuum; loses all heat | Low |
| External Vent (with Damper) | Balanced pressure; high air quality | Higher capital cost; energy loss | Medium |

33

## **Energy Modeling and Internal Heat Gains (IHG)**

The success of a Passive House design is verified through the Passive House Planning Package (PHPP).2 For the Cowes workshop, the modeling must accurately account for the heat generated by woodworking machinery.56 A 3HP table saw or a large wood lathe generates significant sensible heat while running.56 In the winter, these "internal heat gains" (IHG) are beneficial, as they reduce the need for the underfloor heating system.47 However, in the summer, these gains can push the workshop toward overheating.10  
The master plan’s North-facing overhang is an excellent passive design feature that limits direct solar gain while allowing diffuse northern light, which is ideal for woodworking.3 However, the PHPP model will need to verify the risk of overheating during peak summer work sessions. The use of the power-floated concrete slab as high-mass storage is essential here; it can absorb the daytime heat from machinery and release it at night via the MVHR’s "summer bypass" or through night-time purge ventilation.3

## **Planning Permission and Building Regulations in the UK**

Building a garden room in the UK requires adherence to two sets of rules: Planning Permission (which governs aesthetics and location) and Building Regulations (which govern safety and performance).1

### **Permitted Development and Height Constraints**

Under Permitted Development rules, a garden room within 2 meters of a boundary is strictly capped at a total height of 2.5 meters.1 This is a major challenge for a Passive House build because the thick insulation required for the floor (JACKODUR Atlas) and the roof (150mm PIR) can easily take up 500mm to 600mm of the total height.3 A designer must carefully balance the foundation depth and roof pitch to ensure a usable internal ceiling height while remaining under the 2.5m legal limit.59 If the workshop is moved more than 2 meters from the boundary, the height limit increases to 3m for a flat roof or 4m for a dual-pitched roof, which is far more conducive to a high-performance build.59

### **Non-Combustibility and Boundary Rules**

For a garden room between 15 and 30 square meters that is within 1 meter of a boundary, building regulations (Part B) require the structure to be built of "substantially non-combustible materials" to prevent fire spread.30 The master plan’s use of James Hardie Fibre Cement Plank (A2 Fire-rated) for the cladding and Rockwool RW3 (non-combustible) for the wall core is an excellent strategy for compliance in tight garden spaces.1

## **Summary and Implementation Roadmap**

The Cowes Passivhaus Woodworkshop is an achievable goal that requires meticulous attention to the "unseen" details of the building envelope.2 The current master plan provides a robust foundation, particularly with the choice of JACKODUR Atlas XPS and the Pro Clima Intello Plus membrane.3 To finalize the certification path, the following steps are recommended:

1. **PHPP Calculation:** Perform a site-specific energy balance to confirm the insulation thicknesses and window specifications.54  
2. **Airtightness Detailing:** Create a 3D airtightness plan, specifically focusing on the interface between the concrete slab, the timber sole plate, and the Intello Plus membrane.14  
3. **Extraction Design:** Finalize the LEV strategy. A recirculating cyclone with a HEPA filter is the preferred choice for a Passive House environment.33  
4. **Window Specification:** Select a certified triple-glazed window system with a $U\_w$ value $\\leq 0.8$ W/m²K.19  
5. **Interim Testing:** Schedule a blower door test once the air barrier is complete but before the Fermacell boards are installed.14

By following this roadmap, the Cowes workshop will achieve a level of comfort and efficiency that far exceeds standard UK construction, providing a durable and sustainable workspace for decades to come.

#### **Works cited**

1. Garden Room Insulation Guide | Stay Comfortable All Year Round, accessed March 10, 2026, [https://www.buyinsulationonline.co.uk/blog/a-comprehensive-guide-to-garden-room-insulation-in-the-uk](https://www.buyinsulationonline.co.uk/blog/a-comprehensive-guide-to-garden-room-insulation-in-the-uk)  
2. What is Passivhaus?, accessed March 10, 2026, [https://www.passivhaustrust.org.uk/what\_is\_passivhaus.php](https://www.passivhaustrust.org.uk/what_is_passivhaus.php)  
3. MASTER\_PLAN.md  
4. Passivhaus Standard vs Building Regulations \- what are the differences? \- Arbor Architects, accessed March 10, 2026, [https://www.arborarchitects.co.uk/journal/passivhausandbuildingregulations](https://www.arborarchitects.co.uk/journal/passivhausandbuildingregulations)  
5. The complete guide to Passivhaus \- elemental, accessed March 10, 2026, [https://elementallondon.show/features/the-complete-guide-to-passivhaus/](https://elementallondon.show/features/the-complete-guide-to-passivhaus/)  
6. Building for Comfort and Efficiency: Passive House Design and Ventilation \- Fantech, accessed March 10, 2026, [https://www.fantech.net/en-us/expertise/fantech-5-hub/blog/comfort/passive\_house\_design\_and\_ventilation](https://www.fantech.net/en-us/expertise/fantech-5-hub/blog/comfort/passive_house_design_and_ventilation)  
7. Passivhaus \- MDPI, accessed March 10, 2026, [https://www.mdpi.com/2673-8392/1/1/5](https://www.mdpi.com/2673-8392/1/1/5)  
8. What shape is particularly advantageous for a passive house? \- e-genius, accessed March 10, 2026, [https://www.e-genius.at/fileadmin/user\_upload/lernfelder/energieeffiziente\_gebaeudekonzepte/alt/en/web/what\_shape\_is\_particularly\_advantageous\_for\_a\_passive\_house.html](https://www.e-genius.at/fileadmin/user_upload/lernfelder/energieeffiziente_gebaeudekonzepte/alt/en/web/what_shape_is_particularly_advantageous_for_a_passive_house.ht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)  
9. BSD-025: The Passive House (Passivhaus) Standard—A comparison to other cold climate low-energy houses | buildingscience.com, accessed March 10, 2026, [https://buildingscience.com/documents/insights/bsi-025-the-passivhaus-passive-house-standard](https://buildingscience.com/documents/insights/bsi-025-the-passivhaus-passive-house-standard)  
10. Technical Guidance \- Internal Heat Gain Assumptions in PHPP \- Passivhaus Trust, accessed March 10, 2026, [https://www.passivhaustrust.org.uk/guidance\_detail.php?gId=26](https://www.passivhaustrust.org.uk/guidance_detail.php?gId=26)  
11. Thermal insulation \[Passipedia EN\], accessed March 10, 2026, [https://passipedia.org/planning/thermal\_protection/integrated\_thermal\_protection](https://passipedia.org/planning/thermal_protection/integrated_thermal_protection)  
12. Passivhaus Airtightness Testing Guide | PDF | Condensation \- Scribd, accessed March 10, 2026, [https://www.scribd.com/document/344476273/Passivhaus-Airtightness-Guide](https://www.scribd.com/document/344476273/Passivhaus-Airtightness-Guide)  
13. Airtightness and air pressure testing in accordance with the Passivhaus standard, accessed March 10, 2026, [https://www.passivhaustrust.org.uk/UserFiles/File/Technical%20Papers/BRE\_Passivhaus\_Airtightness\_Guide.pdf](https://www.passivhaustrust.org.uk/UserFiles/File/Technical%20Papers/BRE_Passivhaus_Airtightness_Guide.pdf)  
14. Airtightness \- Passivhaus Trust, accessed March 10, 2026, [https://passivhaustrust.org.uk/UserFiles/File/Technical%20Papers/How%20to%20Build%202023/HowToBuild-Ch6.pdf](https://passivhaustrust.org.uk/UserFiles/File/Technical%20Papers/How%20to%20Build%202023/HowToBuild-Ch6.pdf)  
15. What is Airtightness and Why is it Important in a Passivhaus?, accessed March 10, 2026, [https://www.passivhausassociation.com.au/news/what-is-airtightness-and-why-is-it-important-in-a-passivhaus-7gfma](https://www.passivhausassociation.com.au/news/what-is-airtightness-and-why-is-it-important-in-a-passivhaus-7gfma)  
16. Building Regs U Values \- Insulation4Less, accessed March 10, 2026, [https://insulation4less.co.uk/blogs/guides-and-news/building-regs-u-values](https://insulation4less.co.uk/blogs/guides-and-news/building-regs-u-values)  
17. Thermal Bridging Guide | Building Performance Network, accessed March 10, 2026, [https://building-performance.network/wp-content/uploads/2023/03/Thermal-Bridging-Guide-ZCH.pdf](https://building-performance.network/wp-content/uploads/2023/03/Thermal-Bridging-Guide-ZCH.pdf)  
18. How to Build a Passivhaus, accessed March 10, 2026, [https://www.passivhaustrust.org.uk/UserFiles/File/Technical%20Papers/ROT/How%20to%20build%20a%20Passivhaus\_Chapters%201%20to%204(2).pdf](https://www.passivhaustrust.org.uk/UserFiles/File/Technical%20Papers/ROT/How%20to%20build%20a%20Passivhaus_Chapters%201%20to%204\(2\).pdf)  
19. What is Passivhaus & Our 6 Steps to Achieving a Passivhaus Build \- PYC Group, accessed March 10, 2026, [https://pycgroup.co.uk/what-is-passivhaus-our-6-steps-to-achieving-a-passivhaus-build/](https://pycgroup.co.uk/what-is-passivhaus-our-6-steps-to-achieving-a-passivhaus-build/)  
20. Passivhaus Windows UK | Passive House Doors UK \- Wolf Line, accessed March 10, 2026, [https://www.wolfline.co.uk/passivhaus-windows-doors/](https://www.wolfline.co.uk/passivhaus-windows-doors/)  
21. How to build a Passivhaus (second edition) | Passivhaus Trust ..., accessed March 10, 2026, [https://www.passivhaustrust.org.uk/UserFiles/File/Technical%20Papers/How%20to%20Build%202023/HowToBuild-Ch7.pdf](https://www.passivhaustrust.org.uk/UserFiles/File/Technical%20Papers/How%20to%20Build%202023/HowToBuild-Ch7.pdf)  
22. Wood Fibre Insulation: Cross Laminated Timber Applications \- GreenSpec, accessed March 10, 2026, [http://www.greenspec.co.uk/building-design/woodfibre-xlam-wall/](http://www.greenspec.co.uk/building-design/woodfibre-xlam-wall/)  
23. TimberBoard Wood Fiber Insulation | TimberHP, accessed March 10, 2026, [https://www.timberhp.com/products/timberboard](https://www.timberhp.com/products/timberboard)  
24. Superfoil SF19+ | Versatile Use | Nationwide Delivery \- National Insulation Supplies, accessed March 10, 2026, [https://www.nationalinsulationsupplies.com/products/superfoil-sf19-45mm-10m-x-1-2mm](https://www.nationalinsulationsupplies.com/products/superfoil-sf19-45mm-10m-x-1-2mm)  
25. SuperFOIL SF19+: Advanced Multifoil Insulation for Enhanced Efficiency, accessed March 10, 2026, [https://www.superfoil.co.uk/products/multifoil-insulation/sf19/](https://www.superfoil.co.uk/products/multifoil-insulation/sf19/)  
26. SuperFOIL SF19+ Multi-layer Foil Insulation \- Roofing Megastore, accessed March 10, 2026, [https://www.roofingmegastore.co.uk/superfoil-sf19-multi-layer-foil-insulation.html](https://www.roofingmegastore.co.uk/superfoil-sf19-multi-layer-foil-insulation.html)  
27. SuperFOIL \- Roof Giant, accessed March 10, 2026, [https://www.roofgiant.com/resources/files/brochure\_19.pdf](https://www.roofgiant.com/resources/files/brochure_19.pdf)  
28. SuperFoil SF19+ and SF40 Insulation | Warmer Solutions, accessed March 10, 2026, [https://www.warmersolutions.co.uk/superfoil-insulation/](https://www.warmersolutions.co.uk/superfoil-insulation/)  
29. U-Value Calculator (Walls, Floors & Roofs) \- Concretecalculate.co.uk, accessed March 10, 2026, [https://concretecalculate.co.uk/building-regulations-calculators/u-value-calculator-walls-floors-roofs/](https://concretecalculate.co.uk/building-regulations-calculators/u-value-calculator-walls-floors-roofs/)  
30. Do You Need Building Regulations for Garden Rooms \- My Outhouse, accessed March 10, 2026, [https://myouthouse.co.uk/blog/garden-room-building-regulations/](https://myouthouse.co.uk/blog/garden-room-building-regulations/)  
31. 8 Building services \- How to build a Passivhaus (second edition ..., accessed March 10, 2026, [https://passivhaustrust.org.uk/UserFiles/File/Technical%20Papers/How%20to%20Build%202023/HowToBuild-Ch8.pdf](https://passivhaustrust.org.uk/UserFiles/File/Technical%20Papers/How%20to%20Build%202023/HowToBuild-Ch8.pdf)  
32. PASSIVBLOG: How Passive House Can Improve Indoor Air Quality \- Australian Passivhaus Association, accessed March 10, 2026, [https://www.passivhausassociation.com.au/news/passivblog-a-breath-of-fresh-air-how-passive-house-can-improve-indoor-air-quality](https://www.passivhausassociation.com.au/news/passivblog-a-breath-of-fresh-air-how-passive-house-can-improve-indoor-air-quality)  
33. Effective Dust Extraction for Cabinetmaking Workshops, accessed March 10, 2026, [https://dustarrest.com/blogs/dust-knowledge-hub/effective-dust-extraction-for-cabinetmaking-workshops](https://dustarrest.com/blogs/dust-knowledge-hub/effective-dust-extraction-for-cabinetmaking-workshops)  
34. Passive House Air Tightness, accessed March 10, 2026, [https://passivehouse.com/former\_conferences/Passive\_House\_E/airtightness\_06.html](https://passivehouse.com/former_conferences/Passive_House_E/airtightness_06.html)  
35. Dust collector outside : r/woodworking \- Reddit, accessed March 10, 2026, [https://www.reddit.com/r/woodworking/comments/1e2pcp8/dust\_collector\_outside/](https://www.reddit.com/r/woodworking/comments/1e2pcp8/dust_collector_outside/)  
36. 6-Inch Universal Automatic Make-Up Air Damper with Pressure Sensor Kit \- Broan-NuTone, accessed March 10, 2026, [https://www.broan-nutone.com/en-us/accessory/md6tu](https://www.broan-nutone.com/en-us/accessory/md6tu)  
37. Passive House Glazing | Future-Ready Homes \- AT ECO Windows & Doors Limited, accessed March 10, 2026, [https://www.at-eco.co.uk/solutions/passive-house-windows-doors-energy-efficient.html](https://www.at-eco.co.uk/solutions/passive-house-windows-doors-energy-efficient.html)  
38. Passive House Triple Glazed Windows from Norrsken, accessed March 10, 2026, [https://www.norrsken.co.uk/collections/passive-house-windows](https://www.norrsken.co.uk/collections/passive-house-windows)  
39. Passive House Triple Glazed Doors from Norrsken, accessed March 10, 2026, [https://www.norrsken.co.uk/collections/passive-house-doors](https://www.norrsken.co.uk/collections/passive-house-doors)  
40. Member Directory • Passivhaus Trust, accessed March 10, 2026, [https://passivhaus.uk/directory/](https://passivhaus.uk/directory/)  
41. Passivhaus Windows & Doors \- Internorm UK, accessed March 10, 2026, [https://uk.internorm.com/passivhaus/](https://uk.internorm.com/passivhaus/)  
42. Mechanical Ventilation Heat Recovery | Efficient Airflow for Passive Homes \- Malvern B\&B, accessed March 10, 2026, [https://www.malvernbandb.com/blog/mechanical-ventilation-heat-recovery](https://www.malvernbandb.com/blog/mechanical-ventilation-heat-recovery)  
43. Passivhaus and MVHR Heat Recovery Ventilation \- HRV Group, accessed March 10, 2026, [https://www.hrv-group.com/blog/passivhaus-accredited-mvhr-heat-recovery](https://www.hrv-group.com/blog/passivhaus-accredited-mvhr-heat-recovery)  
44. Vento Mini Single Room Heat Recovery Ventilation Unit | HRV \- Blauberg UK, accessed March 10, 2026, [https://www.blauberg.co.uk/blauberg-mini-air-decentralised-heat-recovery-unit-single-wall-mounted-d-mvhr-ventilator-smart-wifi-control](https://www.blauberg.co.uk/blauberg-mini-air-decentralised-heat-recovery-unit-single-wall-mounted-d-mvhr-ventilator-smart-wifi-control)  
45. Passive House schools – How to go about it \[Passipedia EN\], accessed March 10, 2026, [https://passipedia.org/planning/non-residential\_passive\_house\_buildings/passive\_house\_schools/how\_go\_about\_it](https://passipedia.org/planning/non-residential_passive_house_buildings/passive_house_schools/how_go_about_it)  
46. The Ultimate MVHR Guide \- Paul Heat Recovery, accessed March 10, 2026, [https://www.paulheatrecovery.co.uk/information-on-domestic-ventilation-and-mvhr/mvhr-guide/](https://www.paulheatrecovery.co.uk/information-on-domestic-ventilation-and-mvhr/mvhr-guide/)  
47. Passive house 101, accessed March 10, 2026, [https://localimpactdesign.ca/passive-house/](https://localimpactdesign.ca/passive-house/)  
48. Setting Up the Best Woodworking Dust Collection System, accessed March 10, 2026, [https://www.rockler.com/learn/dust-collection](https://www.rockler.com/learn/dust-collection)  
49. Kitchen Makeup Air: Code-Compliant Ventilation for Tight Homes \- Fantech, accessed March 10, 2026, [https://www.fantech.net/en-us/expertise/fantech-5-hub/blog/safety/if-the-home-is-built-tight-you-need-to-provide-makeup-air](https://www.fantech.net/en-us/expertise/fantech-5-hub/blog/safety/if-the-home-is-built-tight-you-need-to-provide-makeup-air)  
50. Beginner with a small garage \- what are my dust collection options? : r/BeginnerWoodWorking \- Reddit, accessed March 10, 2026, [https://www.reddit.com/r/BeginnerWoodWorking/comments/vz4fq6/beginner\_with\_a\_small\_garage\_what\_are\_my\_dust/](https://www.reddit.com/r/BeginnerWoodWorking/comments/vz4fq6/beginner_with_a_small_garage_what_are_my_dust/)  
51. Wood Working Shop Air Dust \- Merit Research Journals, accessed March 10, 2026, [https://meritresearchjournals.org/articles/pdf/840428102024](https://meritresearchjournals.org/articles/pdf/840428102024)  
52. Makeup air in a Passive House \- Sustainable Engineering Ltd., accessed March 10, 2026, [https://sustainableengineering.co.nz/makeup-air-in-a-passive-house/](https://sustainableengineering.co.nz/makeup-air-in-a-passive-house/)  
53. Broan® 6" Universal Automatic Make-Up Air Damper with Pressure Sensor Kit | Hudson Appliance, accessed March 10, 2026, [https://www.hudsonappliance.com/product/broan-6-universal-automatic-make-up-air-damper-with-pressure-sensor-kit-md6tu-315959](https://www.hudsonappliance.com/product/broan-6-universal-automatic-make-up-air-damper-with-pressure-sensor-kit-md6tu-315959)  
54. Passive House Planning Package (PHPP), accessed March 10, 2026, [https://passivehouse.com/en/home/planning-tools/](https://passivehouse.com/en/home/planning-tools/)  
55. Utilising PHPP as a tool to design low-energy homes \- Allan Corfield Architects, accessed March 10, 2026, [https://acarchitects.biz/self-build-blog/phpp-tool-low-energy-design-ph-cat](https://acarchitects.biz/self-build-blog/phpp-tool-low-energy-design-ph-cat)  
56. INTERNAL HEAT GAINS (IHG) \- Energy-Models.com, accessed March 10, 2026, [https://energy-models.com/internal-heat-gains-ihg](https://energy-models.com/internal-heat-gains-ihg)  
57. PB 41: Planning tools for the summer situation in non-residential buildings \- Passipedia, accessed March 10, 2026, [https://passipedia.org/phi\_publications/pb\_41/planning\_tools\_for\_the\_summer\_situation\_in\_non-residential\_buildings](https://passipedia.org/phi_publications/pb_41/planning_tools_for_the_summer_situation_in_non-residential_buildings)  
58. Passivhaus Overheating: Design it out \- 86 \- Paul McAlister Architects, accessed March 10, 2026, [https://www.pmcarchitects.com/sustainability-information-blog-content/passivhaus-overheating-design-it-out](https://www.pmcarchitects.com/sustainability-information-blog-content/passivhaus-overheating-design-it-out)  
59. Garden Room Building Regulations UK: Complete Guide, accessed March 10, 2026, [https://www.harperlatterarchitects.co.uk/post/garden-room-building-regulations-uk-complete-guide](https://www.harperlatterarchitects.co.uk/post/garden-room-building-regulations-uk-complete-guide)  
60. Planning Permission \- Outbuildings \- Planning Portal, accessed March 10, 2026, [https://www.planningportal.co.uk/permission/common-projects/outbuildings/planning-permission/](https://www.planningportal.co.uk/permission/common-projects/outbuildings/planning-permission/)  
61. Garden Room Building Regs UK: What You Need to Know (2025 Guide) | Arkiplan, accessed March 10, 2026, [https://arkiplan.co.uk/2025/08/29/garden-room-building-regs-uk/](https://arkiplan.co.uk/2025/08/29/garden-room-building-regs-uk/)  
62. Good Practice Guide to Airtightness | Passivhaus Trust, accessed March 10, 2026, [https://www.passivhaustrust.org.uk/UserFiles/File/Technical%20Papers/Good%20Practice%20Guide%20to%20Airtightness%20v10.6-compressed(1).pdf](https://www.passivhaustrust.org.uk/UserFiles/File/Technical%20Papers/Good%20Practice%20Guide%20to%20Airtightness%20v10.6-compressed\(1\).pdf)  
63. Air Tightness in Passive House Design | Resources | Wilson Architectural Design, accessed March 10, 2026, [https://www.wilsonarchitecturaldesign.com/resources/air-tightness-in-passive-house-design](https://www.wilsonarchitecturaldesign.com/resources/air-tightness-in-passive-house-design)
