wisogetnid/garden-room/research/passivhaus-diy-research.md

# **High-Performance Timber Envelope Strategies for DIY Passivhaus Construction: A Comprehensive Technical Analysis of Wall and Roof Systems**

The pursuit of the Passivhaus standard within the context of self-build and DIY construction represents a significant convergence of high-performance building science and decentralized manufacturing. For the modern self-builder, particularly one operating within the constraints of timber-based materials and the avoidance of wet-trade masonry or concrete wall construction, the challenge lies in achieving stringent thermal and airtightness targets through accessible, precision-engineered assemblies. The Passivhaus standard is not merely an energy-efficiency target but a holistic quality assurance framework that ensures occupant comfort, structural longevity, and minimal operational carbon. This report evaluates advanced timber-based wall and roof strategies, scrutinizing the material science, structural logic, and assembly sequences necessary to meet these goals through DIY-compatible methods.

## **Technical Foundations: The Passivhaus Performance Mandate**

To evaluate construction strategies effectively, the baseline performance metrics of the Passivhaus standard must be contrasted with standard UK Building Regulations. As of 2024 and 2025, the UK’s Approved Document L (Part L) has tightened limiting U-values for new dwellings to 0.18 W/m²K for walls and 0.11 W/m²K for roofs.1 However, these regulatory minimums often fall short of the holistic energy balance required by the Passivhaus Institute (PHI). The Passivhaus standard typically requires external wall and roof U-values to sit between 0.10 and 0.15 W/m²K, depending on the specific climate zone.3  
The fundamental equation governing these requirements is the thermal transmittance, expressed as the U-value:

$$U \= \\frac{1}{R\_{si} \+ \\sum \\frac{d\_n}{\\lambda\_n} \+ R\_{se}}$$  
Where $R\_{si}$ and $R\_{se}$ represent internal and external surface resistances, $d\_n$ is the thickness of each material layer in meters, and $\\lambda\_n$ is the thermal conductivity in W/mK. For timber structures, the calculation must also account for the "thermal bridge" effect of structural members, where solid timber ($\\lambda \\approx 0.13$) conducts heat more readily than insulation ($\\lambda \\approx 0.038$).3

### **Comparative Performance Standards 2025**

| Performance Metric | UK Building Regs (Part L 2025\) | Passivhaus Standard (Typical) |
| :---- | :---- | :---- |
| **Wall U-Value** | 0.18 W/m²K | 0.10 – 0.15 W/m²K |
| **Roof U-Value** | 0.11 W/m²K | 0.10 – 0.15 W/m²K |
| **Airtightness (n50)** | 8.0 m³/h·m² @ 50Pa | ≤ 0.6 ACH @ 50Pa |
| **Annual Space Heating Demand** | \~100 – 120 kWh/m²/yr | ≤ 15 kWh/m²/yr |
| **Primary Energy Demand** | N/A | ≤ 135 kWh/m²/yr |
| **Thermal Comfort Range** | N/A | 17°C – 25°C Year-round |

Sources:.1  
The divergence in airtightness requirements is the most critical factor for DIYers. Achieving 0.6 air changes per hour (ACH) requires a continuous, unbroken "red-line" around the building envelope, where every junction between walls, roofs, and floors is meticulously sealed.4 This transition from "loose" construction to a precision-sealed chassis is the primary hurdle for non-professional builders.

## **Structural Strategies: Timber-Based Systems for DIY Assembly**

The requirement to avoid bricks and concrete for walls directs the focus toward four primary timber-based strategies: The Larsen Truss (Twin-Wall), Structural Insulated Panels (SIPs), the WikiHouse (CNC-modular), and the Beattie Passive (Flying Factory) system.

### **The Larsen Truss and Twin-Wall Methodology**

The Larsen Truss is a non-structural or semi-structural outer frame attached to a primary load-bearing inner wall, creating a deep cavity for insulation while minimizing thermal bridging.7 In a typical DIY application, the inner 140mm stud wall provides the structural capacity, while an outer 90mm stud is connected via plywood webs or gussets.7  
The thermal efficiency of the Larsen Truss is significantly higher than that of standard I-joists. Research into thermal bypass indicates that while a standard I-joist provides a continuous path for heat through its solid OSB web, the intermittent gussets of a Larsen Truss reduce this pathway.8 For every $100 spent on nominal R-value, a Larsen Truss delivers approximately $92.50 of actual performance, whereas an I-joist may only deliver $81.10.8 This 10% performance gap is critical when aiming for the 0.10 W/m²K threshold.  
From a DIY perspective, Larsen Trusses can be fabricated on-site using basic carpentry tools or ordered as pre-fabricated panels from specialists like Broadaxe or Timber Innovations.7 These panels often utilize Warmcel (cellulose) insulation, which is blown into the 300mm to 400mm cavities to achieve U-values ranging from 0.13 down to 0.09 W/m²K.7

### **WikiHouse: The Digital Modular Paradigm**

The WikiHouse system, specifically the Skylark 250 series, represents the most accessible "high-tech" solution for the DIYer. It utilizes 18mm spruce plywood or OSB3, precision-cut by CNC machines into interlocking blocks.11 These blocks are assembled off-site or on-site using timber "bow-tie" connectors and mallets, effectively removing the need for traditional framing skills.13  
The Skylark 250 system provides a wall thickness capable of holding 250mm of insulation, achieving a default U-value of 0.14 W/m²K.11 This value can be further improved by adding an external layer of rigid wood fiber insulation board before cladding.16 The modular nature of WikiHouse allows for rapid on-site assembly; a small team can erect a structural chassis in days, provided the foundations (typically screw piles) are level to within \+/- 10mm.12

### **Structural Insulated Panels (SIPs)**

SIPs consist of a rigid insulation core (typically EPS or Polyurethane) sandwiched between two structural OSB skins.17 SIPs are inherently airtight due to their bonded construction and minimal jointing compared to stud frames.17 For a self-builder, SIPs arrive as a "kit" of pre-cut panels that slot together using splines, which significantly reduces the risk of on-site errors in insulation installation.18  
However, SIPs present challenges for the DIYer committed to bio-based materials. Most SIPs use petrochemically derived insulation, and modifications on-site are difficult due to the precision-engineered nature of the panels.18 Furthermore, SIPs require robust mechanical ventilation because the building is essentially "wrapped in plastic," providing zero moisture-buffering capacity compared to wood-fiber or cellulose-based systems.18

### **Beattie Passive and the Flying Factory**

The Beattie Passive system is the first in the UK to achieve full certification for a complete building system from the Passivhaus Institute.5 It utilizes a patented twin-stud timber frame that creates a continuous insulation void around the entire building—walls, roof, and floor—effectively creating an unbroken "tea-cosy" effect.5  
The "Flying Factory" model is particularly relevant for the DIYer or community group. Beattie Passive provides the design, training, and specialized equipment to set up a temporary manufacturing facility on or near the build site.20 This allows semi-skilled labor to manufacture high-performance panels that consistently achieve U-values of 0.11 W/m²K and airtightness levels of 0.6 ACH or better.5

## **Bio-Based Insulation Materials: Science and Application**

In a timber-based Passivhaus, the choice of insulation governs not only the thermal transmittance but also the moisture health and acoustic performance of the structure. Bio-based materials like wood fiber, cellulose, and hemp are preferred for their hygroscopic properties and high specific heat capacity.

### **Wood Fiber Insulation**

Wood fiber is produced from forestry by-products and is available as flexible batts (for friction-fitting between studs) or rigid boards (for external sheathing and sarking).22  
The specific heat capacity of wood fiber ($c \\approx 2100$ J/kgK) is significantly higher than that of mineral wool or synthetic foams.22 This provides a high "decrement delay" or phase shift, where solar heat gain absorbed by the roof or walls during the day takes many hours to reach the interior, keeping the building cool in summer—a critical issue in lightweight timber construction.23

| Wood Fiber Product Type | Typical λ-Value (W/mK) | Common Applications | DIY Handling |
| :---- | :---- | :---- | :---- |
| **Flexible Batts (e.g., SteicoFlex)** | 0.036 – 0.038 | Between studs/rafters | Easy: Friction fit, cut with saw/knife |
| **Rigid Sheathing Board** | 0.040 – 0.048 | External wall wrap, render carrier | Moderate: Requires mechanical fixings |
| **Sarking Board (T\&G)** | 0.042 – 0.050 | External roof layer, wind-tightness | Moderate: Interlocking joints |
| **Loose-Fill (Floc)** | 0.038 – 0.040 | Blown into deep wall/roof cavities | Professional/Specialized Rental |

Sources:.22

### **Cellulose (Recycled Newspaper)**

Cellulose, often sold under brands like Warmcel, is the industry standard for deep-cavity timber framing. It is treated with natural boron salts for fire, rot, and pest resistance.7 In a Passivhaus context, cellulose is preferred because it can be blown into cavities at high densities ($\>45$ kg/m³), which prevents settlement and ensures that every nook and cranny of a complex twin-wall junction is filled.7  
For DIYers, the density is key. If the cellulose is too loose, it will settle over time, creating a thermal bridge at the top of the wall. Professional injection is common, but machines like the X-Floc Minifant are available for hire for the competent self-builder.28

### **Hygroscopic Performance and "Breathing" Construction**

A "vapor-open" or "breathing" wall construction allows moisture vapor to migrate through the structure without condensing into liquid water, which causes rot in timber.22 This is achieved by placing materials with high vapor resistance (the VCL) on the warm internal side and increasingly vapor-permeable materials toward the cold external side.25 Natural fibers are hygroscopic, meaning they can safely hold a certain amount of moisture and release it when conditions allow, providing a moisture "buffer" that synthetic foams cannot offer.22

## **Airtightness: The DIY "Red-Line" Challenge**

Airtightness is the single most common failure point for DIY Passivhaus projects. The goal of 0.6 ACH @ 50Pa requires a level of attention to detail that exceeds traditional UK building culture.

### **The Airtightness Layer Options**

In timber frame construction, the airtightness layer is usually one of three things:

1. **Intelligent Membranes**: Specialized films like Pro Clima Intello Plus that vary their vapor permeability based on humidity.33  
2. **Structural Boarding**: Taped OSB (Oriented Strand Board) on the internal face of the studs.25  
3. **Parged Masonry**: Not applicable to the user’s timber-only request, but relevant for understanding the standard.35

For the DIYer, the "Intello" system is often preferred because the transparent or semi-translucent nature of some membranes allows for visual inspection of the insulation behind it before closing the walls.33

### **Taping and Sealing Junctions**

Every penetration through the airtightness layer must be sealed with specialized tapes and grommets. Tapes like Pro Clima Tescon Vana are engineered for a 100-year lifespan and can bond to timber, OSB, and membranes.34  
Critical DIY Sealing Checklist:

* **The Sole Plate**: The junction between the timber wall and the foundation. This requires an EPDM gasket or specialized butyl tape (e.g., Tescon Naideck) to prevent air "ghosting" under the wall.13  
* **Service Penetrations**: Every pipe or cable passing through the VCL must have a dedicated EPDM grommet. Using tape alone around a moving pipe often fails over time.33  
* **Window and Door Frames**: Using pre-folded tapes (e.g., Tescon Profect) to manage the internal and external corners where the frame meets the structural opening.37  
* **The Service Void**: A 38mm battened zone between the VCL and the final plasterboard lining is essential. This allows cables and sockets to be installed without puncturing the airtightness layer.25

## **Roof Strategies: The "Warm Roof" vs. "Cold Roof"**

In a Passivhaus, the traditional UK "cold roof" (insulation at the ceiling level with a ventilated attic) is generally avoided because it creates complex airtightness junctions at the eaves and makes the attic space useless for mechanical systems like MVHR.

### **The Warm Roof Sequence**

A "warm roof" configuration places the insulation on top of and between the rafters, keeping the structural timber inside the thermal envelope.26

1. **Internal Support**: 9mm OSB or a reinforced membrane is fixed to the underside of the rafters.26  
2. **Cavity Fill**: Flexible wood fiber or cellulose is installed between the rafters. It is vital to cut batts 10-15mm wider than the cavity to ensure a "snug" friction fit with no air gaps.26  
3. **Over-Insulation**: Tongue-and-groove wood fiber sarking boards are laid over the rafters. These boards provide a secondary layer of insulation that "breaks" the thermal bridge of the rafters.23  
4. **Weatherproofing**: A breathable roofing membrane is laid over the boards, followed by counter-battens and the final roof finish.26

### **Roof-to-Wall Junctions**

The "tea-cosy" principle requires that the insulation in the wall meets the insulation in the roof without interruption. In a Larsen Truss or Beattie Passive system, the pumped insulation flows continuously from the wall cavity into the roof cavity.5 For DIY systems using batts, the builder must ensure that the insulation in the eaves is packed tightly to remove any "cold spots" that could lead to condensation.26

## **Foundation Synergy: The "No Concrete" Challenge**

While the user requested no concrete for walls, traditional foundations are almost always concrete. However, for lightweight timber structures, screw pile foundations (helical piles) offer a robust, DIY-friendly, and concrete-free alternative.

### **Screw Pile Technology**

Screw piles are galvanized steel columns with a helical screw at the end, driven into the ground to a verified torque.41 They are ideal for DIYers because:

* **No Excavation**: There is no need for deep trenches or the removal of tons of soil.41  
* **Immediate Loading**: Unlike concrete, which takes weeks to cure, a timber frame can be built on screw piles the same day they are installed.42  
* **Accuracy**: In the Isle of Wight, specialist ground screw contractors use hydraulic machinery to install piles with extreme precision, providing a level base for WikiHouse or timber frames.44

### **The Timber Ground Floor**

Once the screw piles are in place, a timber ring beam or sole plate is installed to support a suspended timber ground floor.13 This floor can be designed as a deep timber box (similar to the wall blocks) and filled with 300mm+ of cellulose or wood fiber to achieve the Passivhaus U-value of 0.10 W/m²K.6

## **Isle of Wight Context: Logistics and Sourcing**

Building a Passivhaus on the Isle of Wight introduces specific logistical constraints regarding material delivery and specialist merchants.

### **Specialist Material Sourcing**

Most Passivhaus-specific materials (Intello membranes, wood fiber, cellulose) must be sourced from mainland distributors like Ecological Building Systems or Ecomerchant and shipped via ferry.22

| Logistical Consideration | Isle of Wight Solution |
| :---- | :---- |
| **Freight Carriers** | Ferryspeed, Wightlink, Breakwells (Specialists in DIY shipping) |
| **Local Timber Merchants** | West Cowes Timber, Sydenhams, RVN Building Supplies |
| **Foundations** | Specialist ground screw contractors |
| **Ferry Routes** | Portsmouth to Fishbourne, Lymington to Yarmouth, Southampton to Cowes |

Sources:.44  
For the DIYer, consolidating orders into full lorry loads is essential to minimize the high cost of ferry transit.46 Coordination with local merchants like Sydenhams for standard C24 structural timber and OSB can be supplemented by specialized mainland deliveries for the high-performance "skin" of the building.50

## **DIY Practicalities: Skill Acquisition and Tooling**

Successfully building a Passivhaus requires a shift from "general building" to "precision assembly."

### **The "Airtightness Champion" Role**

In most Passivhaus builds, one person is designated as the "Airtightness Champion." Their role is to inspect every single piece of tape, every grommet, and every junction before it is covered by plasterboard. For a DIYer, this means self-policing with a critical eye.

### **Specialized Tooling for DIYers**

* **Insulation Saws**: Standard wood saws tear natural fibers. Specialized serrated insulation saws are needed for clean cuts in wood fiber batts.23  
* **Pressure Tools (Pressfix)**: Essential for ensuring that airtightness tape is fully bonded to the substrate; the adhesive on high-performance tapes is pressure-activated.37  
* **Moisture Meters**: Used to ensure that the timber frame is below 20% moisture content (ideally 12-15%) before the airtightness layer is installed and the building is "sealed".12  
* **Blower Door Rental**: Competent DIYers often rent a blower door kit mid-build to find and fix leaks before the final certification test.28

## **Economic and Ecological Trade-offs**

A common pitfall in Passivhaus design is the pursuit of ultra-low U-values at the expense of embodied carbon.

### **Embodied Carbon of Insulation**

While a 100mm layer of PIR foam ($\\lambda \\approx 0.022$) outperforms 100mm of wood fiber ($\\lambda \\approx 0.038$), the carbon footprint of the foam is massive. Wood fiber and cellulose actually sequester carbon, locking it into the building fabric for decades.11 For the self-builder, the slightly thicker walls required by natural fibers (e.g., 400mm vs. 300mm) are usually a worthwhile trade-off for a "carbon-negative" structure.7

### **The "Slightly More" Rule**

Passivhaus construction typically costs 10-15% more than traditional builds due to the cost of triple glazing, MVHR, and high-quality membranes.5 However, recent data suggests this gap is closing as traditional building costs soar.21 For the DIYer, the labor savings of systems like WikiHouse or the Beattie Passive "Flying Factory" can offset the higher material costs, making a Passivhaus build comparable in budget to a standard "code-minimum" home.11

## **Detailed Assembly: The WikiHouse Skylark 250 Case Study**

To illustrate the integration of these strategies, the assembly of a WikiHouse Skylark 250 chassis serves as a blueprint for the "No Concrete/No Bricks" DIYer.

### **Phase 1: Substructure and Sole Plates**

The foundation piles are installed and capped with a timber "ring beam" or "rails".13 These rails are typically C24 structural softwood.13 The rails must be perfectly level; any deviation here will multiply as the wall blocks are stacked. The rails are fixed to the screw piles or slab using concrete anchor bolts or specialized brackets like those from Rothoblaas.13

### **Phase 2: Floor and Wall Blocks**

The floor blocks are dropped into place over the rails and secured. The wall blocks follow a 600mm grid system.12 Each block is connected using timber bow-ties malleted flush with the interior and exterior panels.13 Window and door blocks are inserted into the pattern, with lintels sized according to structural engineering guides.15

### **Phase 3: The Roof and Ridge Beam**

For a pitched roof (standard 42 degrees), a glulam ridge beam is installed into pre-cut notches in the gable wall blocks.13 Roof blocks are then lifted (by a team or a "genie lift") and secured to the wall blocks using bow-ties.12 This creates a structurally stable "interlocked box".13

### **Phase 4: Insulation and Sealing**

Once the chassis is complete, the cavities are filled with insulation.12 WikiHouse recommends moisture-free, non-combustible materials like recycled plastic rolls or mineral wool, though wood fiber batts are a superior sustainable choice.12 The structure is then wrapped in a breathable external membrane (wind-tightness) and an internal airtight VCL (airtightness).12

## **The Role of MVHR in Timber Passivhaus**

It is a common myth that you cannot open windows in a Passivhaus.58 However, because the building is so airtight, it requires Mechanical Ventilation with Heat Recovery (MVHR) to maintain air quality.4  
The MVHR system works by:

1. **Extracting**: Stale, moist air is pulled from "wet" rooms (kitchens, bathrooms).  
2. **Heat Exchange**: This warm air passes through a heat exchanger, warming up the cold, fresh air being pulled from outside.  
3. **Supplying**: The fresh, pre-warmed air is delivered to living rooms and bedrooms.

For the timber DIYer, the MVHR ducting must be planned early. Systems like the Posi-Joist (metal web joists) or the service voids in WikiHouse blocks are designed to facilitate these ducts without cutting through structural members.6

## **Conclusion: Synthesizing the DIY Path**

The construction of a Passivhaus using timber-based, DIY-friendly methods is a viable and increasingly popular route for the modern self-builder. By leveraging the thermal decoupling of the Larsen Truss, the digital precision of WikiHouse, or the certified continuity of the Beattie Passive system, the DIYer can bypass the environmental and logistical burdens of traditional masonry and concrete.  
Success in this endeavor is predicated on a "Fabric First" approach:

* **Prioritize Insulation Quality**: Using bio-based materials like wood fiber and cellulose to ensure hygroscopic health and thermal buffering.22  
* **Enforce Airtightness Integrity**: Adopting a "red-line" philosophy where the airtightness layer is treated as the most critical structural component.4  
* **Utilize Precision Foundations**: Employing screw piles to provide a level, sustainable, and concrete-free base for the timber chassis.41  
* **Manage Logistics**: Especially in island settings like the Isle of Wight, planning for consolidated specialist deliveries to manage costs and ensure material compatibility.46

The timber-based Passivhaus is more than a low-energy building; it is a high-performance carbon-sequestering envelope that offers unparalleled living comfort while empowering the self-builder through modern, accessible construction technology. By following the rigorous detailing required for airtightness and thermal bridging, the DIY builder can deliver a structure that not only meets the challenges of 2025 regulations but provides a durable, healthy home for the next century.

#### **Works cited**

1. Building Regs U Values \- Insulation4Less, accessed March 10, 2026, [https://insulation4less.co.uk/blogs/guides-and-news/building-regs-u-values](https://insulation4less.co.uk/blogs/guides-and-news/building-regs-u-values)  
2. Building Regulations U Values Explained \- Plans Made Easy, accessed March 10, 2026, [https://plansmadeeasy.org/building-regulations-u-values/](https://plansmadeeasy.org/building-regulations-u-values/)  
3. Thermal insulation \[Passipedia EN\], accessed March 10, 2026, [https://passipedia.org/planning/thermal\_protection/integrated\_thermal\_protection](https://passipedia.org/planning/thermal_protection/integrated_thermal_protection)  
4. Passivhaus Standard vs Building Regulations \- what are the differences? \- Arbor Architects, accessed March 10, 2026, [https://www.arborarchitects.co.uk/journal/passivhausandbuildingregulations](https://www.arborarchitects.co.uk/journal/passivhausandbuildingregulations)  
5. Should I Use A Certified Passivhaus Build System? \- With Beattie ..., accessed March 10, 2026, [https://acarchitects.biz/self-build-blog/passivhaus-beattie-passive](https://acarchitects.biz/self-build-blog/passivhaus-beattie-passive)  
6. Passive Roof \- MBC Timber Frame, accessed March 10, 2026, [https://mbctimberframe.co.uk/passive-roof/](https://mbctimberframe.co.uk/passive-roof/)  
7. Our Building System — Broadaxe Timber Frames, accessed March 10, 2026, [https://www.broadaxetimberframes.co.uk/our-building-system](https://www.broadaxetimberframes.co.uk/our-building-system)  
8. Thermal bridging of I-Joist vs Larsen Truss \- Emu Passive, accessed March 10, 2026, [https://emupassive.com/thermal-bridging-of-i-joist-vs-larsen-truss/](https://emupassive.com/thermal-bridging-of-i-joist-vs-larsen-truss/)  
9. Larsen System | Timber Innovations, accessed March 10, 2026, [https://timberinnovations.co.uk/build-systems/larsen-system/](https://timberinnovations.co.uk/build-systems/larsen-system/)  
10. Passivhaus Timber Frame Building System \- Beattie, accessed March 10, 2026, [https://www.beattie.io/timber-frame-system/](https://www.beattie.io/timber-frame-system/)  
11. Product \- WikiHouse, accessed March 10, 2026, [https://www.wikihouse.cc/product](https://www.wikihouse.cc/product)  
12. WikiHouse Skylark Technical Specification 2025.indd, accessed March 10, 2026, [https://cdn.prod.website-files.com/6118e2d27c92cc41c39747a0/6734731aafda7cecf84adcfe\_2dadfc7234da4d7ad229f722fcb018d4\_WikiHouse%20Skylark%20Technical%20Specification%202025.pdf](https://cdn.prod.website-files.com/6118e2d27c92cc41c39747a0/6734731aafda7cecf84adcfe_2dadfc7234da4d7ad229f722fcb018d4_WikiHouse%20Skylark%20Technical%20Specification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)  
13. WikiHouse assembly, accessed March 10, 2026, [https://www.wikihouse.cc/assembly/wikihouse-assembly](https://www.wikihouse.cc/assembly/wikihouse-assembly)  
14. Skylark 250 blocks \- WikiHouse, accessed March 10, 2026, [https://www.wikihouse.cc/blocks/skylark-250](https://www.wikihouse.cc/blocks/skylark-250)  
15. Designing for WikiHouse, accessed March 10, 2026, [https://www.wikihouse.cc/design/designing-for-wikihouse](https://www.wikihouse.cc/design/designing-for-wikihouse)  
16. Insulation \- WikiHouse, accessed March 10, 2026, [https://www.wikihouse.cc/design/insulation](https://www.wikihouse.cc/design/insulation)  
17. Building with structural insulated panels: A beginner's guide \- Homebuilding & Renovating, accessed March 10, 2026, [https://www.homebuilding.co.uk/advice/structural-insulated-panels](https://www.homebuilding.co.uk/advice/structural-insulated-panels)  
18. 10 Pros & Cons of SIPs in Self Build Homes \- thistle architecture, accessed March 10, 2026, [https://www.thistlearchitecture.co.uk/self-build-sips-construction](https://www.thistlearchitecture.co.uk/self-build-sips-construction)  
19. Wikihouse vs. SIP kits \- About WikiHouse \- WikiHouse, accessed March 10, 2026, [https://community.wikihouse.cc/t/wikihouse-vs-sip-kits/685](https://community.wikihouse.cc/t/wikihouse-vs-sip-kits/685)  
20. Beattie Passive's Flying Factory \- Constructing Excellence, accessed March 10, 2026, [https://constructingexcellence.org.uk/beattie-passives-flying-factory/](https://constructingexcellence.org.uk/beattie-passives-flying-factory/)  
21. Safety net \- passivehouseplus.co.uk, accessed March 10, 2026, [https://passivehouseplus.co.uk/magazine/feature/safety-net](https://passivehouseplus.co.uk/magazine/feature/safety-net)  
22. Natural Insulation \- A Sustainable Alternative for Any Building, accessed March 10, 2026, [https://www.ecologicalbuildingsystems.com/post/natural-insulation-sustainable-alternative-any-building](https://www.ecologicalbuildingsystems.com/post/natural-insulation-sustainable-alternative-any-building)  
23. Wood Fibre Insulation: Your Guide to Eco-Friendly Home Comfort, accessed March 10, 2026, [https://www.buyinsulationonline.co.uk/blog/wood-fibre-insulation](https://www.buyinsulationonline.co.uk/blog/wood-fibre-insulation)  
24. The Ultimate Guide To Natural, Eco Friendly Insulation \- Ecomerchant, accessed March 10, 2026, [https://www.ecomerchant.co.uk/eco-friendly-insulation-guide](https://www.ecomerchant.co.uk/eco-friendly-insulation-guide)  
25. Wood Fibre Insulation: Timber Frame Applications \- GreenSpec, accessed March 10, 2026, [http://www.greenspec.co.uk/building-design/woodfibre-timber-frame-wall/](http://www.greenspec.co.uk/building-design/woodfibre-timber-frame-wall/)  
26. How to insulate a pitched roof using wood fibre insulation \- Back to Earth, accessed March 10, 2026, [https://www.backtoearth.co.uk/guide/how-to-insulate-a-pitched-roof-using-wood-fibre-insulation/](https://www.backtoearth.co.uk/guide/how-to-insulate-a-pitched-roof-using-wood-fibre-insulation/)  
27. Technical \- The Science Behind the Beattie Build System, accessed March 10, 2026, [https://www.beattie.io/technical/](https://www.beattie.io/technical/)  
28. X-Floc UK: Home, accessed March 10, 2026, [https://x-floc.co.uk/](https://x-floc.co.uk/)  
29. Aeroflocker Hire \- Portable Industrial Blown Electrostatic Flocking System, accessed March 10, 2026, [https://www.theflockingshop.co.uk/Aeroflocker-Hire---Portable-Industrial-Blown-System](https://www.theflockingshop.co.uk/Aeroflocker-Hire---Portable-Industrial-Blown-System)  
30. Airtightness systems | pro clima international, accessed March 10, 2026, [https://proclima.com/products/internal-sealing](https://proclima.com/products/internal-sealing)  
31. Top Natural Insulation Materials UK for Sustainable Home Solutions, accessed March 10, 2026, [https://eco-renovation.co.uk/top-natural-insulation-materials-uk-for-sustainable-home-solutions/](https://eco-renovation.co.uk/top-natural-insulation-materials-uk-for-sustainable-home-solutions/)  
32. A Sustainable Approach to Build Insulated External Timber Frame Walls for Passive Houses Using Natural and Waste Materials \- MDPI, accessed March 10, 2026, [https://www.mdpi.com/1999-4907/13/4/522](https://www.mdpi.com/1999-4907/13/4/522)  
33. Pro Clima Airtightness & Windtightness Solutions for Buildings, accessed March 10, 2026, [https://www.ecomerchant.co.uk/brands/pro-clima.html](https://www.ecomerchant.co.uk/brands/pro-clima.html)  
34. Pro Clima \- Airtightness & Windtightness Solutions for Buildings, accessed March 10, 2026, [https://www.ecologicalbuildingsystems.com/shop-by-brand/pro-clima](https://www.ecologicalbuildingsystems.com/shop-by-brand/pro-clima)  
35. How to Build a Passivhaus, accessed March 10, 2026, [https://www.passivhaustrust.org.uk/UserFiles/File/Technical%20Papers/ROT/How%20to%20build%20a%20Passivhaus\_Chapters%201%20to%204(2).pdf](https://www.passivhaustrust.org.uk/UserFiles/File/Technical%20Papers/ROT/How%20to%20build%20a%20Passivhaus_Chapters%201%20to%204\(2\).pdf)  
36. tescon vana \- Ty Mawr Lime, accessed March 10, 2026, [https://www.lime.org.uk/tescon-vana.html](https://www.lime.org.uk/tescon-vana.html)  
37. Pro Clima Tapes \- Ultimate Insulation Supplies, accessed March 10, 2026, [https://www.ultimate-insulation.co.uk/collections/pro-clima-tapes](https://www.ultimate-insulation.co.uk/collections/pro-clima-tapes)  
38. MBC TIMBER FRAME, accessed March 10, 2026, [https://mbctimberframe.co.uk/wp-content/uploads/130979-MBC\_TIMBER-FOLDERS\_-.pdf](https://mbctimberframe.co.uk/wp-content/uploads/130979-MBC_TIMBER-FOLDERS_-.pdf)  
39. Build a Warm Flat Roof the Right Way \- YouTube, accessed March 10, 2026, [https://www.youtube.com/watch?v=xWRLCWmqT50](https://www.youtube.com/watch?v=xWRLCWmqT50)  
40. how to construct walls to passive house \- Green Building Forum, accessed March 10, 2026, [https://www.greenbuildingforum.co.uk/newforum/comments.php?DiscussionID=6441](https://www.greenbuildingforum.co.uk/newforum/comments.php?DiscussionID=6441)  
41. Screw Pile Foundations That Protect Your Yard \- Western Timber Frame, accessed March 10, 2026, [https://www.westerntimberframe.com/screw-pile-foundations-that-protect-your-yard/](https://www.westerntimberframe.com/screw-pile-foundations-that-protect-your-yard/)  
42. Foundations for Timber Frame Houses – Why Screw Piles?, accessed March 10, 2026, [https://www.winkelmann-construction.com/en/presse-center/posts/foundations-for-wooden-and-frame-houses](https://www.winkelmann-construction.com/en/presse-center/posts/foundations-for-wooden-and-frame-houses)  
43. Residential Screw Piling, accessed March 10, 2026, [https://www.ultimatescrewpiling.co.uk/residential-screw-piling](https://www.ultimatescrewpiling.co.uk/residential-screw-piling)  
44. Ground Screw Foundations installed on the Isle of Wight, accessed March 10, 2026, [https://islandgroundscrews.co.uk/](https://islandgroundscrews.co.uk/)  
45. GroundPlug \- Screw Piles Home Foundation, accessed March 10, 2026, [https://groundplug.co.uk/application-homes/](https://groundplug.co.uk/application-homes/)  
46. Isle of Wight Freight \- Ferryspeed, accessed March 10, 2026, [https://www.ferryspeed.com/freight-services/isle-of-wight-freight-shipping/](https://www.ferryspeed.com/freight-services/isle-of-wight-freight-shipping/)  
47. Freight ferry travel to and from the Isle of Wight \- Wightlink, accessed March 10, 2026, [https://www.wightlink.co.uk/services/freight](https://www.wightlink.co.uk/services/freight)  
48. transporting goods between England and the Isle of Wight \- Freightlink, accessed March 10, 2026, [https://www.freightlink.co.uk/knowledge/articles/over-600000-tonnes-cargo-transporting-goods-between-england-and-isle-wight](https://www.freightlink.co.uk/knowledge/articles/over-600000-tonnes-cargo-transporting-goods-between-england-and-isle-wight)  
49. West Cowes Timber – Isle of Wight – For all your timber and fencing needs, accessed March 10, 2026, [https://westcowestimber.co.uk/](https://westcowestimber.co.uk/)  
50. Fence Panels Near Me in Newport, Isle Of Wight | Yell Marketplace, accessed March 10, 2026, [https://www.yell.com/s/fence+panels-newport-isle+of+wight.html](https://www.yell.com/s/fence+panels-newport-isle+of+wight.html)  
51. Builders Merchants in Cowes \- Surrey's Business Directory, accessed March 10, 2026, [https://directory.getsurrey.co.uk/search/cowes/builders-merchants](https://directory.getsurrey.co.uk/search/cowes/builders-merchants)  
52. Shipping Building Materials \- Managed Logistics, accessed March 10, 2026, [https://www.translogisticsinc.com/shipping-building-materials](https://www.translogisticsinc.com/shipping-building-materials)  
53. Timber Merchants in Cowes, Isle Of Wight \- Directory, accessed March 10, 2026, [https://directory.somersetlive.co.uk/search/cowes%2Cisle-of-wight/timber-merchants](https://directory.somersetlive.co.uk/search/cowes%2Cisle-of-wight/timber-merchants)  
54. Technical specifications, accessed March 10, 2026, [https://cdn.prod.website-files.com/6118e2d27c92cc41c39747a0/6734731aafda7cecf84adcfe\_WikiHouse%20Skylark%20Technical%20Specification%202025.pdf](https://cdn.prod.website-files.com/6118e2d27c92cc41c39747a0/6734731aafda7cecf84adcfe_WikiHouse%20Skylark%20Technical%20Specification%202025.pdf)  
55. Hire Equipment \- Netceed, accessed March 10, 2026, [https://uk-store.netceed.com/hire-equipment](https://uk-store.netceed.com/hire-equipment)  
56. The Future Benefits of Offsite Construction \- A. Proctor Group, accessed March 10, 2026, [https://files.proctorgroup.com/assets/white-papers/proctors-the-future-benefits-of-offsite-construction-white-paper.pdf](https://files.proctorgroup.com/assets/white-papers/proctors-the-future-benefits-of-offsite-construction-white-paper.pdf)  
57. How the WikiHouse structure works, accessed March 10, 2026, [https://www.wikihouse.cc/design/how-the-structure-works](https://www.wikihouse.cc/design/how-the-structure-works)  
58. Benefits \- Why Choose the Beattie Passivhaus System, accessed March 10, 2026, [https://www.beattie.io/benefits/](https://www.beattie.io/benefits/)
