wisogetnid/garden-room/research/compacfoam_perimeter_examples.md

# Compacfoam CF200 Sole Plate & Threshold Examples

| Source Type | Manufacturer/Author | Confidence Rating (1-5) | Summary | URL |
| :--- | :--- | :---: | :--- | :--- |
| **Manufacturer Specs** | Compacfoam UK | 5 | Official manufacturer documentation specifying Compacfoam for "thermally separated sill supports" and "load transfer elements in timber frame construction." | [Compacfoam Timber Construction](https://compacfoam.com/uk/area-of-application/timber-construction/) |
| **Technical Guidance** | Passivhaus Trust | 5 | "How to Build a Passivhaus (Ch.7)" detailing standard practices for minimizing thermal bridging at solid timber sole plates. | [How to Build a Passivhaus](https://www.passivhaustrust.org.uk/UserFiles/File/Technical%20Papers/How%20to%20Build%202023/HowToBuild-Ch7.pdf) |
| **Supplier Documentation** | 21 Degrees (formerly Green Building Store) | 5 | Details CF200 rigid thermoplastic insulation usage for structural thermal bridging, particularly beneath structural thresholds. | [21 Degrees Compacfoam](https://www.21degrees.com/compacfoam/) |
| **Builder / Case Study** | Self Build Blog (Passivhaus) | 4 | Real-world example of a builder routing and installing Compacfoam 200 under a structural threshold on a concrete slab to eliminate the thermal bridge. | [Self Build Blog: Compacfoam](https://selfbuild.blog/tag/compacfoam/) |
| **Technical Discussion** | BuildHub Forum | 4 | Deep-dive discussion among self-builders/architects dissecting Green Building Store's standard Compacfoam threshold details and how it interacts with the timber frame. | [BuildHub Compacfoam Threshold Detail](https://forum.buildhub.org.uk/topic/35802-compacfoam-threshold-detail-whats-actually-happening-here/) |
