wisogetnid/garden-room/research/mvhr-research.md

# **Technical Design and Regulatory Compliance of Mechanical Ventilation with Heat Recovery in Airtight Timber Workshops**

## **Introduction: The Modern Garden Workshop and the Environmental Control Challenge**

The construction of modern, high-performance garden outbuildings and workshops in the United Kingdom has undergone a significant architectural shift.1 Driven by the demand for year-round operational comfort and the necessity of structural longevity, modern timber outbuildings are designed around highly insulated, airtight envelopes.1 These envelopes utilize rigid board, foil-backed, or cavity-fill insulation, premium double-glazed fenestration, and continuous vapor barriers to eliminate thermal bridging, drafts, and moisture ingress.1  
While these passive measures succeed in regulating temperature and preventing external dampness, they simultaneously introduce severe indoor air quality hazards when the space is utilized as a woodworking workshop.1 Woodworking processes inherently generate dense volumes of particulate matter and release volatile organic compounds (VOCs) from stains, glues, and finishes.5 In an airtight envelope, these contaminants cannot escape through traditional leakage paths.6  
Relying on natural ventilation, such as opening windows or trickle vents, is highly inefficient in a conditioned workshop.1 It compromises the thermal barrier, causes rapid heat loss in winter, and introduces raw outdoor humidity that causes structural movement and volumetric distortion in stored timber.1  
To reconcile energy efficiency with health and safety, Mechanical Ventilation with Heat Recovery (MVHR) is increasingly integrated into modern workshop designs.10 However, implementing MVHR in a woodworking environment is not a simple plug-and-play task.12 It requires a sophisticated understanding of particulate dynamics, mechanical pressure balancing, multi-stage filtration cascades, and strict alignment with UK building and occupational health regulations.8

## **Wood Dust Particulates: Physical Characterization and Pathological Hazards**

Engineers must treat wood dust not merely as a housekeeping nuisance, but as a severe health hazard and a highly volatile combustible material.5 Wood dust is physically categorized into three distinct fractions based on aerodynamic diameter: coarse, fine, and respirable.5

### **Physical and Pathological Classification of Woodworking Byproducts**

Coarse dust consists of visible shavings and large wood chips produced during high-volume cutting, planing, and jointing operations.5 Due to its high mass, coarse dust settles rapidly out of the air.5 While less dangerous to deep lung tissue, it remains a primary cause of ocular irritation, upper respiratory tract inflammation in the trachea and nasal passages, and mechanical skin abrasion.5 Furthermore, dry wood dust acts as a strong skin desiccant, stripping the skin of its natural moisture barrier and increasing a worker's vulnerability to secondary dermal infections and localized allergic contact dermatitis.5  
Fine dust comprises particles smaller than  ().5 These particles are light enough to remain suspended in the air for hours under normal workshop convection currents.5 Fine dust easily bypasses the primary mechanical filtration mechanisms of the human upper airway, such as nasal hair and mucous membranes, depositing directly within the bronchial passages.5  
Respirable dust represents the most hazardous particulate fraction, consisting of microscopic particles smaller than  () down to .5 These particles are invisible to the naked eye under normal lighting.5 When inhaled, respirable dust penetrates deep into the alveolar regions of the lungs, where it cannot be easily cleared by natural biological defense mechanisms.5 Over time, repeated exposure to respirable dust leads to irreversible tissue scarring, occupational asthma, chronic obstructive pulmonary disease (COPD), and sino-nasal carcinomas.5

### **Chemical and Combustion Hazards in the Workshop Envelope**

The introduction of chemical processes adds gaseous toxicity to particulate hazards.5 The application of solvents, stains, finishes, and wood glues releases highly concentrated VOCs.5 Standard High-Volume Low-Pressure (HVLP) spraying systems, even when operated inside specialized spray tents, atomize these finishes into ultra-fine droplets.12 This atomized overspray remains suspended as a thin haze, depositing a chemical dust layer across all workshop surfaces and presenting an immediate inhalation risk.12  
Furthermore, these chemical processes present extreme fire and explosion risks.5 Fine wood dust suspended in a closed, airtight space forms a highly explosive dust-to-air mixture.14 Standard domestic vacuum cleaners are unsafe for this environment because their high-speed motor brushes and ungrounded plastic hoses generate significant static electricity, acting as direct ignition sources for a dust explosion.14  
Similarly, oily rags used to apply stains and finishes present a spontaneous combustion hazard.19 The drying process of these oils is exothermic; if rags are left piled together, the heat of oxidation cannot escape, leading to spontaneous ignition.19 This chemical reaction requires workshops to maintain a minimum temperature of  to ensure proper curing of finishes while enforcing safe, airtight disposal protocols.19

## **De-Integration: Decoupling Residential and Woodworking Ventilation Envelopes**

A critical error in residential and outbuilding design is the physical integration of a woodworking workshop's ventilation ductwork into a central, whole-house MVHR system.4 Building services guidelines dictate that workshops must be completely decoupled from residential ventilation loops.4

### **The Core-Contamination Risk and Filter Blinding**

Integrating a workshop into a home's central MVHR loop introduces severe contamination risks.4 Despite the placement of extract grilles with standard media, fine and respirable wood dust will inevitably bypass domestic-grade filters.8 This dust enters the return ductwork and accumulates inside the central heat recovery core.4  
As wood dust coats the heat exchanger plates, it acts as an insulator, drastically reducing thermal efficiency.4 This accumulation also poses a major fire hazard within the duct network and provides a breeding ground for mold and fungi when exposed to damp extract air from kitchens and bathrooms.4 Over time, cross-contamination can occur, distributing fine dust and chemical VOC vapors from the workshop into the fresh air stream delivered to residential bedrooms and living areas.4

### **Thermal Draft Induction and Volumetric Imbalance**

Whole-house MVHR systems are calibrated for balanced volumetric flow rates and a homogeneous thermal envelope.8 Extracting air from an unheated or lightly heated outbuilding workshop lowers the mean temperature of the return air entering the centralized heat exchanger.8  
This drop in return air temperature reduces the temperature of the fresh supply air distributed to the house, causing cold drafts and increasing the home's overall heating load.8 Conversely, if the central MVHR supplies warm air to an unoccupied workshop, it creates a net thermal loss from the residential space.8  
To mitigate these risks, the workshop must be treated as an isolated zone.8 For conditioned, airtight workshops, localized d-MVHR systems represent the correct technical standard.4 These wall-through units provide balanced fresh air supply and extraction, recovering heat directly within the local envelope and maintaining a separate, safe boundary from the home.4

## **Fluid Dynamics and Thermodynamic Pressure Management**

Designing a ventilation system for a woodworking outbuilding requires precise fluid dynamic calculations to determine volumetric flow rates, air change targets, and pressure balances.4

### **Volumetric Airflow Calculations**

The primary ventilation rate is determined by the Air Changes per Hour (ACH) required to dilute airborne contaminants.4 The fresh air ventilation rate  in cubic meters per hour () is calculated as:  
  
Where  is the net internal volume of the workshop in cubic meters.4 To convert this to the imperial volumetric flow rate in cubic feet per minute (), the equation is structured as:  
  
Where  is the net workshop volume in cubic feet ().4  
For a high-specification garden timber workshop matching a standard  container or modular frame footprint ( length,  width, and  ceiling height) 24, the volume is calculated as:  
  
The ventilation system must operate across two distinct mechanical states based on workshop activity 4:

* **Standby Mode:** When the workshop is unoccupied, a rate of  to  is maintained to control humidity, prevent condensation, and protect stored timber from moisture fluctuations.1  
* **Active Operational Mode:** During active woodworking, a target of  (within the standard recommended range of  to ) is required to continuously dilute airborne particulates and solvent VOCs.4

Applying the active operational mode target of  to the  workshop 4:  
  


### **Pressure Balance and Local Exhaust Ventilation (LEV) Conflicts**

This calculated flow rate represents the fresh air exchange needed for general dilution.4 However, a severe pressure-balance conflict occurs when a Local Exhaust Ventilation (LEV) system, such as a stationary dust collector or a portable extractor, is activated.5  
A standard  to  workshop dust collector typically moves between  () and  ().16 If the extraction system discharges its filtered air directly out of the building envelope, it will create a massive negative pressure gradient inside an airtight workshop.4 This negative pressure can easily exceed .7 Under these conditions, the d-MVHR unit's constant-flow fans will stall, air will be pulled rapidly through microscopic leaks in the building joints, and moisture-laden outdoor air will bypass the heat exchanger, leading to localized draft risks and interstitial condensation.3  
To resolve this conflict, woodworking dust collection must rely on high-efficiency, closed-loop recirculating filtration systems.28 By cleaning the extracted air and returning it directly to the workshop, the pressure balance is maintained (), and heated air is preserved within the thermal envelope.28  
If chemical processes or paint spraying require the LEV to exhaust outdoors, a synchronized mechanical makeup air system must be installed.27 This system utilizes a motorized damper that opens in tandem with the exhaust blower, providing a low-resistance pathway for fresh, tempered makeup air.27  


## **The Multi-Stage Filtration Cascade: Engineering the Intake and Extract Safeguards**

Integrating an MVHR system into a woodworking environment requires a multi-stage filtration strategy to protect the heat recovery core and maintain high indoor air quality.32 Relying solely on the standard filters built into MVHR units is inadequate.12 These standard filters will saturate and clog within hours, reducing airflow, causing fan motors to overheat, and risking system failure.12  
To prevent this, workshops must implement a multi-stage filtration cascade.33 This system consists of three distinct stages, starting with point-of-source capture and ending with ambient air filtration.5

### **The Three Stages of Filtration**

First, source capture serves as the primary line of defense.5 Standard power tools must be connected to dedicated extraction systems, such as a vacuum or dust extractor.5 For hand sanding and portable power tools, high-performance dust extractors (such as the Festool CT MIDI I HEPA, CT 26, or CT 36\) are highly effective.12 These units capture nearly  of fine wood dust at the point of generation, preventing it from escaping into the general room air.12  
Furthermore, to eliminate ignition hazards, all extraction hoses and ductwork must be structurally bonded and grounded to dissipate static electricity.14  
Second, inline pre-filtration is required on the extract ductwork before air enters the MVHR unit.33 Placing a galvanized steel inline filter box (such as a Blauberg KFBK or a Ducting Express unit) in the extract duct run protects the heat exchanger core from dust buildup.33  
To minimize static pressure resistance, the filter box must be oversized relative to the duct diameter.25 For example, a  duct run should utilize a larger filter housing, such as a  box with a pleated V-bank or bag filter configuration.33  
The pre-filtration stages must follow a strict sequence:

* **Stage 1 (Coarse Pre-filtration):** A low-cost, disposable ISO Coarse / G4 pleated panel filter captures large particles ().32 This filter acts as a sacrificial barrier, protecting the secondary fine filters from premature blinding.34  
* **Stage 2 (Fine Filtration):** An ISO ePM1 / F7 pocket or bag filter (such as the Ruck FT 125 with an LFT 05 F7 bag filter) captures fine and respirable particulates down to .38 This stage features a high dust-holding capacity (typically ), ensuring long-term system operation before requiring replacement.39  
* **Stage 3 (HEPA / VOC Filtration):** An optional H13 HEPA and active carbon filter can be integrated into the cascade to capture sub-micron particulates and neutralize chemical odors and VOCs.16

Third, secondary ambient air filtration manages any remaining airborne dust that escapes source capture.5 High-volume, ceiling-mounted air purifiers (such as the Jet AFS-1000C or the WEN series) continuously recirculate and clean the workshop air.12  
As a highly cost-effective alternative, many small-scale woodworkers build DIY ambient air filtration boxes.25 These setups pair an inline duct fan (such as an  high-efficacy fan) or a three-speed box fan (such as the Air King 9723\) with a deep, pleated furnace filter.43  
A standard DIY configuration utilizes a deep  MERV 13 pleated filter, with a cheap  MERV 8 pre-filter placed in front of it.43 The deep  filter provides a massive surface area (often up to  of pleated media), which significantly lowers static resistance and prevents the rapid blinding common in standard, thin domestic HEPA filters.25

## **UK Regulatory Compliance, Building Controls, and Occupational Safety**

Operating a woodworking workshop in the United Kingdom requires compliance with two primary regulatory frameworks: Building Regulations Part F and the Control of Substances Hazardous to Health (COSHH) Regulations.15

### **Building Regulations Part F (Ventilation)**

Approved Document F is split into two volumes: Volume 1 governs domestic dwellings, while Volume 2 applies to buildings other than dwellings.46 A detached garden workshop operates in a regulatory grey area.47 Under Part F1(1), adequate ventilation must be provided for people in the building.6 However, Requirement F1 does not apply to spaces where people do not normally go, areas used solely for storage, or garages used solely in connection with a single dwelling.47  
Once a garden structure is insulated, heated, and utilized regularly as a workshop, it is no longer exempt.1 If the workshop is operated as a commercial business, it must comply fully with Approved Document F: Volume 2, which mandates specific fresh air supply rates (typically  or  based on occupancy).48 Furthermore, any mechanical ventilation system must undergo physical air-flow rate testing and balancing by a certified engineer using a UKAS-calibrated anemometer.49 The commissioning certificate must be submitted to Building Control to verify that the actual air exchange matches the design performance.49

### **COSHH Regulations and LEV Compliance**

Under the Control of Substances Hazardous to Health Regulations 2002 (COSHH), wood dust is classified as a hazardous substance with a statutory Workplace Exposure Limit (WEL) defined in the HSE's EH40 publication.18 In 2020, the WEL for mixed wood dust was reduced to a maximum of  over an 8-hour Time-Weighted Average (TWA).18 Employers are legally obligated to reduce dust exposure to as low a level as is reasonably practicable.52

### **Summary of UK Statutory Ventilation and Extraction Regulations**

| Regulation | Scope | Specific Mandate | Testing Frequency |
| :---- | :---- | :---- | :---- |
| **COSHH Regulation 7** 51 | Exposure Control | Mandates the prevention or control of exposure to hazardous substances like wood dust.18 | Ongoing operational compliance.35 |
| **COSHH Regulation 9** 51 | Maintenance of Controls | Mandates that LEV systems (fixed plant and portable extractors) are kept in efficient working order.13 | Daily/weekly visual checks.51 |
| **COSHH Thorough Examination** 18 | LEV Systems | Mandates a Thorough Examination and Test (TExT) of all LEV and on-tool extraction equipment.13 | **Every 14 Months** (12 months recommended for woodworking).18 |
| **EH40 (HSE Standards)** 18 | Exposure Limits | Sets maximum limits for airborne dust concentration:  for wood dust.35 | Annual or periodic personal air sampling.35 |
| **Part F (Volume 2\)** 46 | Non-Domestic Ventilation | Dictates minimum fresh air supply rates and background air change validation.48 | Commisioning at install, plus periodic servicing.23 |

Under COSHH Regulation 9, any engineering control—including fixed ducted extraction systems and portable "on-tool" dust extractors—must undergo a Thorough Examination and Test (TExT) at least once every 14 months by a competent person.13 For professional woodworking facilities, Health and Safety Executive (HSE) guidance recommends reducing this interval to 12 months due to the rapid wear and abrasive nature of wood dust.53 Visual checks of hoods, ducting, and filters must be logged daily or weekly.51  
Failure to conduct and document these tests is a serious breach of health and safety law.13 This can result in HSE "Fee for Intervention" costs, improvement or prohibition notices, substantial corporate fines, and the invalidation of employer's liability insurance policies.53

## **Decentralized MVHR Technical Comparison and System Selection**

When selecting a decentralized MVHR unit for a highly insulated garden workshop, engineers must compare physical parameters, thermal efficiencies, and filtration capabilities.10 The Zehnder ComfoAir 70 and the Brink Air 70 are the two primary European wall-through units suitable for this application.54

### **Technical Performance Metrics of Selected d-MVHR Units**

| Design Parameter | Zehnder ComfoAir 70 | Brink Air 70 |
| :---- | :---- | :---- |
| **Maximum Airflow Capacity** | **** () 55 |  () 57 |
| **Heat Exchanger Type** | Enthalpy (Sensible & Latent) 55 | Counter-Flow (Sensible Only) 56 |
| **Thermal Efficiency (Sensible)** | Up to  55 | Up to  61 |
| **Humidity Recovery (Latent)** | Up to  55 | Negligible (unless equipped with optional rotor) 61 |
| **Power Consumption Range** | **** to  55 |  to  56 |
| **Low-Temperature Frost Limit** | **** (without preheater) 55 |  (automatic preheater activation) 56 |
| **Minimum Wall Thickness** | **** (expandable to ) 55 |  (with sleeve kits up to ) 56 |
| **Core Hole Diameter Required** | Approximately  55 | Approximately  55 |

### **Enthalpy Exchange vs. Counter-Flow Heat Exchange**

The Zehnder ComfoAir 70 utilizes a highly specialized enthalpy heat exchanger core.55 The enthalpy membrane allows for the simultaneous transfer of both sensible heat and latent water vapor between the extract and supply air streams.54  
This moisture recovery provides a major engineering benefit in a timber workshop 55:

* **Elimination of Condensate Drainage:** Standard heat recovery units generate significant condensation inside the cabinet as warm, moist exhaust air is cooled.21 This requires running a freeze-protected drain line through an external wall.62 Enthalpy cores transfer this moisture back to the dry incoming air, eliminating condensate run-off and preventing moisture streaks from staining the external facade of the building.55  
* **Prevention of Core Freezing:** Moisture transfer allows the Zehnder ComfoAir 70 to operate down to  without requiring an energy-intensive electric preheater.55 If temperatures drop lower, the unit activates frost protection down to  before entering standby mode.55  
* **timber Equilibrium Moisture Content (EMC) Control:** Wood is highly hygroscopic, swelling or shrinking in response to relative humidity.9 By recovering humidity in winter and rejecting it in summer, enthalpy exchange keeps the workshop's relative humidity within the optimal  to  range.9 This prevents stored timber from warping, cracking, or moving during projects.9

The Brink Air 70 utilizes a high-efficiency counter-flow sensible heat exchanger.56 While it achieves slightly higher peak thermal efficiency () 61, it does not transfer moisture.56 It relies on a built-in electric preheater to prevent core freezing when temperatures drop below .56  
The Brink unit is highly modular and can be paired with the "Pure Induct" air purification module, which uses ionization to trap fine dust and ultra-fine nanoparticles, keeping its static resistance lower than a traditional HEPA filter.60

## **Localized Procurement, Logistics, and Services on the Isle of Wight**

Executing an MVHR project on the Isle of Wight requires working with ventilation specialists who understand both the logistical challenges of island transit and the requirements of local Building Control officers.22

### **Accredited Regional Providers and Commissioning Engineers**

| Provider Name | Head Office / Regional Base | Core Services and Accreditations |
| :---- | :---- | :---- |
| **Island HVAC Systems** 23 | Isle of Wight (Local) 23 | • Turnkey design, supply, and installation 23 • BPEC-certified engineering and commissioning 23 • Part F airflow compliance testing and certification 23 • COSHH LEV system testing, maintenance, and repairs 23 |
| **EnviroVent** 22 | Isle of Wight / Hampshire 22 | • Vince Ward (Local Specialist): 07720 629601 22 • Email: vward@envirovent.com 22 • Free on-site surveys and air quality assessments 22 • Supply of UK-manufactured d-MVHR and PIV systems 22 |
| **Evolve Design & Build** 11 | Southsea, Portsmouth (PO4 9PR) 11 | • Phone: 07989 481389 11 • Email: evolvedesignbuildtony@gmail.com 11 • NICEIC-certified installations and commissioning 11 • Part F compliance testing for the South Coast region 11 |
| **Cinergi** 64 | Hampshire 64 | • Phone: 0800 321 3142 64 • Solid and semi-flexible radial ductwork installations 64 • Over 40 years of mechanical and electrical engineering experience 64 |

### **The Critical Role of Local BPEC Commissioning**

The isolation of the Isle of Wight makes direct on-island engineering support highly valuable.22 While many outbuilding workshops are constructed as DIY projects, the mechanical ventilation system must still be physically commissioned to comply with Building Control.23  
BPEC-qualified engineers from Island HVAC Systems can perform commissioning-only services for DIY installations.23 The commissioning process involves physically measuring and balancing the supply and extract airflow rates using a calibrated anemometer, ensuring the system meets Part F requirements.23  
Once verified, the engineer issues a Part F Commissioning Certificate, which is submitted to Building Control to confirm building compliance.23 For commercial workshops, these local engineers also provide the annual LEV testing required to maintain COSHH compliance.18

## **Comprehensive System Selection and Installation Blueprint**

To establish an energy-efficient, safe, and legally compliant garden woodworking workshop, the following design and installation blueprint must be executed:

* **De-integrate the Workshop Ventilation:** Never connect the workshop to the main house MVHR system.4 Treat the timber workshop as an independent airtight thermal envelope with its own dedicated decentralized MVHR unit (e.g., Zehnder ComfoAir 70\) to provide fresh air and control moisture.21  
* **Implement a Closed-Loop LEV System:** For tool-point dust extraction, utilize a high-efficiency dust collector or extractor that recirculates cleaned air back into the workshop.28 Ensure the collector utilizes an M-class or HEPA-grade canister filter to capture dangerous fine particulates down to .12 Recirculation prevents negative pressure drops that would stall the MVHR and draw damp air into the timber structure.3  
* **Install a Multi-Stage Inline Filter Box:** Position a galvanized steel inline filter box (such as a  Blauberg KFBK or Ruck FT) on the extract line of the d-MVHR unit.33 Use a disposable G4 pleated pre-filter to catch coarse particles, followed by an F7 pocket filter to trap fine dust.32 This cascade protects the enthalpy heat exchanger from dust buildup, preserving heat recovery performance and preventing fire hazards.8  
* **Engage Island-Based Professionals:** Contract a qualified local firm, such as Island HVAC Systems, to perform BPEC-certified balancing, commissioning, and Part F testing.23 Ensure they issue a formal airflow verification report for Building Control.49  
* **Schedule Regular Maintenance:** For commercial workshops, schedule a professional Thorough Examination and Test (TExT) of the LEV system every 12 to 14 months to maintain COSHH compliance.13 Maintain a written log of daily and weekly visual checks of filters, hood performance, and pressure gauges.35 Ensure the d-MVHR enthalpy core is washed with water and internal filters are replaced at least twice a year.55

#### **Works cited**

1. Insulated Garden Workshops | Year-Round Comfort Guaranteed, accessed May 23, 2026, [https://www.noahgardenrooms.co.uk/insulated-garden-workshops/](https://www.noahgardenrooms.co.uk/insulated-garden-workshops/)  
2. Insulated Workshops \- The Garden Room & Annexe Guide, accessed May 23, 2026, [https://www.thegardenroomguide.co.uk/types-of-garden-room/insulated-workshops/](https://www.thegardenroomguide.co.uk/types-of-garden-room/insulated-workshops/)  
3. Renovating with Passive House components \- outPHit, accessed May 23, 2026, [https://outphit.eu/media/filer\_public/6b/80/6b80ee50-72d6-4fae-87c6-fd801fa7c9ef/enerphit\_renovating\_with\_passive\_house\_components.pdf](https://outphit.eu/media/filer_public/6b/80/6b80ee50-72d6-4fae-87c6-fd801fa7c9ef/enerphit_renovating_with_passive_house_components.pdf)  
4. Garage Ventilation: How to Ventilate Garages and Workshops Safely \- Rise, accessed May 23, 2026, [https://www.buildwithrise.com/stories/garage-ventilation-how-to-ventilate-garages-and-workshops-safely](https://www.buildwithrise.com/stories/garage-ventilation-how-to-ventilate-garages-and-workshops-safely)  
5. Air Quality Control in Woodworking \- Eldridge USA, accessed May 23, 2026, [https://eldridgeusa.com/blog/air-quality-control-in-woodworking/](https://eldridgeusa.com/blog/air-quality-control-in-woodworking/)  
6. Part F Building Regulations Ventilation requirements for indoor air quality \- Marley, accessed May 23, 2026, [https://www.marley.co.uk/blog/part-f-building-regulations-ventilation-requirements-for-indoor-air-quality](https://www.marley.co.uk/blog/part-f-building-regulations-ventilation-requirements-for-indoor-air-quality)  
7. Do Airtight Houses Need Makeup Air? \- Energy Vanguard, accessed May 23, 2026, [https://www.energyvanguard.com/blog/do-airtight-houses-need-makeup-air/](https://www.energyvanguard.com/blog/do-airtight-houses-need-makeup-air/)  
8. MHVR and high volumes of dust \- Green Building Forum, accessed May 23, 2026, [https://www.greenbuildingforum.co.uk/newforum/comments.php?DiscussionID=9780](https://www.greenbuildingforum.co.uk/newforum/comments.php?DiscussionID=9780)  
9. Garage Climate Control for Woodworking: Temperature and Humidity Tips \- tempCube, accessed May 23, 2026, [https://tempcube.io/blogs/temperature-humidity/garage-climate-control-for-woodworking-temperature-and-humidity-tips](https://tempcube.io/blogs/temperature-humidity/garage-climate-control-for-woodworking-temperature-and-humidity-tips)  
10. Dust Free Living: How MVHR Systems Combat Dust in Your Home \- Filters Direct, accessed May 23, 2026, [https://filtersdirect.uk/dust-free-living/](https://filtersdirect.uk/dust-free-living/)  
11. MVHR Installations | Portsmouth & Hants \- Evolve Design & Build, accessed May 23, 2026, [https://www.evolvedesignbuild.co.uk/mvhr](https://www.evolvedesignbuild.co.uk/mvhr)  
12. Getting a workshop dust air purifier/dust collector : r/woodworking \- Reddit, accessed May 23, 2026, [https://www.reddit.com/r/woodworking/comments/1r919ll/getting\_a\_workshop\_dust\_air\_purifierdust\_collector/](https://www.reddit.com/r/woodworking/comments/1r919ll/getting_a_workshop_dust_air_purifierdust_collector/)  
13. Portable Dust Extractor LEV Thorough Examination Guide \- Velocity Safety, accessed May 23, 2026, [https://velocitysafety.co.uk/blog/portable-dust-extractor-lev-thorough-examination/](https://velocitysafety.co.uk/blog/portable-dust-extractor-lev-thorough-examination/)  
14. Dust Collection in Woodworking Shops: Compliance, Cleanup, and What Most Facilities Get Wrong \- Eurovac, accessed May 23, 2026, [https://www.eurovac.com/learn/topic/vehicle-exhaust/dust-collection-in-woodworking-shops-compliance-cleanup-and-what-most-facilities-get-wrong/](https://www.eurovac.com/learn/topic/vehicle-exhaust/dust-collection-in-woodworking-shops-compliance-cleanup-and-what-most-facilities-get-wrong/)  
15. Overview \- Ventilation in the workplace \- HSE, accessed May 23, 2026, [https://www.hse.gov.uk/ventilation/](https://www.hse.gov.uk/ventilation/)  
16. 7 Best Woodshop Air Purifiers for Sawdust & Smoke \- Your Elegant Bar, accessed May 23, 2026, [https://yourelegantbar.com/blogs/cigars/best-woodshop-air-purifiers-for-sawdust-smoke](https://yourelegantbar.com/blogs/cigars/best-woodshop-air-purifiers-for-sawdust-smoke)  
17. MVHR air quality, putting an air-purifier / filter inline \- Green Building Forum, accessed May 23, 2026, [https://www.greenbuildingforum.co.uk/newforum/comments.php?DiscussionID=17841](https://www.greenbuildingforum.co.uk/newforum/comments.php?DiscussionID=17841)  
18. LEV Testing in Woodworking: What Affects Dust Control Over Time \- Vent Tech, accessed May 23, 2026, [https://www.vent-tech.co.uk/lev-testing-in-woodworking-what-affects-dust-control-over-time/](https://www.vent-tech.co.uk/lev-testing-in-woodworking-what-affects-dust-control-over-time/)  
19. 5 considerations for setting up workshop ventilation | TIMBER MART, accessed May 23, 2026, [https://timbermart.ca/en/5-considerations-for-setting-up-workshop-ventilation/](https://timbermart.ca/en/5-considerations-for-setting-up-workshop-ventilation/)  
20. How do I create an air tight barrier between my basement workshop and furnace?, accessed May 23, 2026, [https://www.woodtalkonline.com/topic/10187-how-do-i-create-an-air-tight-barrier-between-my-basement-workshop-and-furnace/](https://www.woodtalkonline.com/topic/10187-how-do-i-create-an-air-tight-barrier-between-my-basement-workshop-and-furnace/)  
21. Integrated Garage and MVHR \- Green Building Forum, accessed May 23, 2026, [https://www.greenbuildingforum.co.uk/newforum/comments.php?DiscussionID=9043](https://www.greenbuildingforum.co.uk/newforum/comments.php?DiscussionID=9043)  
22. Ventilation Specialist in Isle of Wight \- Envirovent, accessed May 23, 2026, [https://www.envirovent.com/services/find-a-local-ventilation-specialist/local-specialist/isle-of-wight/](https://www.envirovent.com/services/find-a-local-ventilation-specialist/local-specialist/isle-of-wight/)  
23. Fresh indoor air \- Mvhr, Commissioning \- Island HVAC systems, accessed May 23, 2026, [https://islandhvacsystems.co.uk/ventilation-1](https://islandhvacsystems.co.uk/ventilation-1)  
24. Bespoke Container Conversions Manufactured in the UK \- KC Modular Buildings, accessed May 23, 2026, [https://kcmodularbuildings.co.uk/container-conversions/](https://kcmodularbuildings.co.uk/container-conversions/)  
25. Combined dust collector / air filter : r/woodworking \- Reddit, accessed May 23, 2026, [https://www.reddit.com/r/woodworking/comments/1865htf/combined\_dust\_collector\_air\_filter/](https://www.reddit.com/r/woodworking/comments/1865htf/combined_dust_collector_air_filter/)  
26. Dust Collection & Air Filtration \- Woodcraft, accessed May 23, 2026, [https://www.woodcraft.com/collections/dust-collection-air-filtration](https://www.woodcraft.com/collections/dust-collection-air-filtration)  
27. Makeup Air \- Vent Tech, accessed May 23, 2026, [https://venttech.com/residential-services/makeup-air](https://venttech.com/residential-services/makeup-air)  
28. Extraction Systems Woodworking, accessed May 23, 2026, [https://alko-extractiontechnology.com/en/applications/wood/](https://alko-extractiontechnology.com/en/applications/wood/)  
29. Recirculating cooker hoods – possibilities and challenges, accessed May 23, 2026, [https://www.aivc.org/system/files/BSH\_Recirculation%20Cooker%20Hoods\_Urban%20Home%20Ventilation%20Workshop%20Oslo2.pdf](https://www.aivc.org/system/files/BSH_Recirculation%20Cooker%20Hoods_Urban%20Home%20Ventilation%20Workshop%20Oslo2.pdf)  
30. Industrial Air Make-up Air Units, accessed May 23, 2026, [https://www.airdynamics.net/industrial-makeup-air-systems/](https://www.airdynamics.net/industrial-makeup-air-systems/)  
31. Understanding Makeup Air Systems: The Key to Efficient Kitchen Ventilation \- Proline Range Hoods, accessed May 23, 2026, [https://prolinerangehoods.com/blogs/news/understanding-makeup-air](https://prolinerangehoods.com/blogs/news/understanding-makeup-air)  
32. Anti Pollen Filter Set – Zehnder ComfoAir Q/E | Zehnder Original, accessed May 23, 2026, [https://shop.zehndergroup.com/be-en/product/zehnder-filterset-comfoairq-anti-pollen](https://shop.zehndergroup.com/be-en/product/zehnder-filterset-comfoairq-anti-pollen)  
33. Inline Filter Boxes and Spare Filters | Ducting Express, accessed May 23, 2026, [https://www.ducting-express.co.uk/category/ducting-fittings/inline-filter-box](https://www.ducting-express.co.uk/category/ducting-fittings/inline-filter-box)  
34. Using a Household Air Purifier in My Woodshop? : r/BeginnerWoodWorking \- Reddit, accessed May 23, 2026, [https://www.reddit.com/r/BeginnerWoodWorking/comments/1iwckf1/using\_a\_household\_air\_purifier\_in\_my\_woodshop/](https://www.reddit.com/r/BeginnerWoodWorking/comments/1iwckf1/using_a_household_air_purifier_in_my_woodshop/)  
35. Understanding COSHH Regulations for Dust, accessed May 23, 2026, [https://dustarrest.com/blogs/dust-knowledge-hub/understanding-coshh-regulations-for-dust](https://dustarrest.com/blogs/dust-knowledge-hub/understanding-coshh-regulations-for-dust)  
36. Blauberg Inline Air Filter Box G4 Ventilation Duct Filter 4" 5" 6" 8" 10" 12" | eBay UK, accessed May 23, 2026, [https://www.ebay.co.uk/itm/166573987599](https://www.ebay.co.uk/itm/166573987599)  
37. Inline Filter Box 125mm With G4 Filter Media \- Ducting Express, accessed May 23, 2026, [https://www.ducting-express.co.uk/product/inline-filter-box-125mm-with-g4-filter-media](https://www.ducting-express.co.uk/product/inline-filter-box-125mm-with-g4-filter-media)  
38. Ruck® air filter box for bag filter 125 mm \- FT 125 65112843 | Ventilationland, accessed May 23, 2026, [https://www.ventilationland.co.uk/en\_GB/p/ruck-r-air-filter-box-for-bag-filter-125-mm-ft-125/8325/](https://www.ventilationland.co.uk/en_GB/p/ruck-r-air-filter-box-for-bag-filter-125-mm-ft-125/8325/)  
39. LFBR 200 F7 \- Helios \- In-line Air Filter Box | L\&B Fans & Ducting Store, accessed May 23, 2026, [https://www.lbfans.co.uk/product/lfbr-200-f7-helios-in-line-air-filter-box/](https://www.lbfans.co.uk/product/lfbr-200-f7-helios-in-line-air-filter-box/)  
40. Inline Filter Boxes \- HVACQuick, accessed May 23, 2026, [https://www.hvacquick.com/products/residential/Air-Filters/Inline-Filter-Boxes](https://www.hvacquick.com/products/residential/Air-Filters/Inline-Filter-Boxes)  
41. 6 Inch 3-Layer Air Filter Box With HEPA & Carbon Filter \- For Inline Duct Fans, 300 CFM, accessed May 23, 2026, [https://www.nexus3foundation.org/reviews/product/424968](https://www.nexus3foundation.org/reviews/product/424968)  
42. Woodworking Air Filtration Systems | Air Cleaners for Workshops | JET Tools, accessed May 23, 2026, [https://jettools.com/woodworking/air-filtration](https://jettools.com/woodworking/air-filtration)  
43. PSA: Use 5 inch filters for your cheap box fan wood dust setups : r/woodworking \- Reddit, accessed May 23, 2026, [https://www.reddit.com/r/woodworking/comments/mwhqdg/psa\_use\_5\_inch\_filters\_for\_your\_cheap\_box\_fan/](https://www.reddit.com/r/woodworking/comments/mwhqdg/psa_use_5_inch_filters_for_your_cheap_box_fan/)  
44. How to make a wood shop AIR filtration system \- YouTube, accessed May 23, 2026, [https://www.youtube.com/watch?v=2N7xCF-uuDA](https://www.youtube.com/watch?v=2N7xCF-uuDA)  
45. Wood Dust's worst enemy \- air filtration \- YouTube, accessed May 23, 2026, [https://www.youtube.com/watch?v=hGKiG7W0Ng8](https://www.youtube.com/watch?v=hGKiG7W0Ng8)  
46. Ventilation: Approved Document F \- GOV.UK, accessed May 23, 2026, [https://www.gov.uk/government/publications/ventilation-approved-document-f](https://www.gov.uk/government/publications/ventilation-approved-document-f)  
47. Approved Document F: Volume 2 applies to buildings other than dwellings \- GOV.UK, accessed May 23, 2026, [https://assets.publishing.service.gov.uk/media/62a761edd3bf7f03667c667e/ADF2\_revised.pdf](https://assets.publishing.service.gov.uk/media/62a761edd3bf7f03667c667e/ADF2_revised.pdf)  
48. approved-document-f-2006.pdf \- For the Building Control Professional, accessed May 23, 2026, [https://buildingcontrol4us.co.uk/wp-content/uploads/2024/12/approved-document-f-2006.pdf](https://buildingcontrol4us.co.uk/wp-content/uploads/2024/12/approved-document-f-2006.pdf)  
49. Part F Ventilation Testing and Commissioning Certificate \- Building Performance Surveys, accessed May 23, 2026, [https://buildcomply.co.uk/services/part-f-ventilation-testing-and-commissioning-certificate](https://buildcomply.co.uk/services/part-f-ventilation-testing-and-commissioning-certificate)  
50. Part F \- Barbour ABI, accessed May 23, 2026, [https://barbour-abi.com/glossary/part-f/](https://barbour-abi.com/glossary/part-f/)  
51. COSHH LEV Testing | LEV Compliance | Dust Particles | South West \- Western Air Ducts, accessed May 23, 2026, [https://westernairducts.co.uk/coshh-lev/](https://westernairducts.co.uk/coshh-lev/)  
52. Legal Requirements For Wood Dust Extraction | TM Machinery, accessed May 23, 2026, [https://tmmachinery.co.uk/legal-requirements-for-wood-dust-extraction/](https://tmmachinery.co.uk/legal-requirements-for-wood-dust-extraction/)  
53. What Is COSHH LEV Testing and Why Does Every Employer Need to Know About It?, accessed May 23, 2026, [https://www.premierlev.com/blog/what-is-coshh-lev-testing-and-why-does-every-employer-need-to-know-about-it](https://www.premierlev.com/blog/what-is-coshh-lev-testing-and-why-does-every-employer-need-to-know-about-it)  
54. Zehnder ComfoAir 70, accessed May 23, 2026, [https://www.international.zehnder-systems.com/en/comfortable-indoor-ventilation/products/units/decentralised-ventilation-units/zehnder-comfoair-70](https://www.international.zehnder-systems.com/en/comfortable-indoor-ventilation/products/units/decentralised-ventilation-units/zehnder-comfoair-70)  
55. Zehnder ComfoAir 70, accessed May 23, 2026, [https://zehnderamerica.com/wp-content/uploads/2024/08/CA-70-Technical-Specifications.pdf](https://zehnderamerica.com/wp-content/uploads/2024/08/CA-70-Technical-Specifications.pdf)  
56. Air 70 \- Brink Climate Systems, accessed May 23, 2026, [https://www.brinkclimatesystems.nl/documenten/air-70-installation-instructions-gb-614397.pdf](https://www.brinkclimatesystems.nl/documenten/air-70-installation-instructions-gb-614397.pdf)  
57. Brink Mechanical Ventilation with Heat Recovery Units, accessed May 23, 2026, [https://www.brinkhrv.com/MVHR-Machines](https://www.brinkhrv.com/MVHR-Machines)  
58. Wall-mounted HRV Zehnder ComfoAir 70 (without mounting shell) \- Majaelpo.lv, accessed May 23, 2026, [https://elpo2.com/products/zehnder-comfoair-70](https://elpo2.com/products/zehnder-comfoair-70)  
59. Zehnder ComfoAir 70, accessed May 23, 2026, [https://www.zehnder.co.uk/en/indoor-ventilation/solutions/mechanical-ventilation-with-heat-recovery/zehnder-comfoair-70](https://www.zehnder.co.uk/en/indoor-ventilation/solutions/mechanical-ventilation-with-heat-recovery/zehnder-comfoair-70)  
60. Healthy, comfortable and energy-efficient ventilation \- Brink Climate Systems, accessed May 23, 2026, [https://www.brinkclimatesystems.nl/documenten/ventilation-systems-healthy-comfortable-and-energy-efficient-ventilation.pdf](https://www.brinkclimatesystems.nl/documenten/ventilation-systems-healthy-comfortable-and-energy-efficient-ventilation.pdf)  
61. FLAIR-RANGE \- Brink Climate Systems, accessed May 23, 2026, [https://www.brinkclimatesystems.nl/documenten/flair-series-always-the-most-excellent-air-in-the-home-614751.pdf](https://www.brinkclimatesystems.nl/documenten/flair-series-always-the-most-excellent-air-in-the-home-614751.pdf)  
62. Condensation from pipes to MVHR \- suggestions? \- Green Building Forum, accessed May 23, 2026, [https://www.greenbuildingforum.co.uk/newforum/comments.php?DiscussionID=17703](https://www.greenbuildingforum.co.uk/newforum/comments.php?DiscussionID=17703)  
63. ComfoAir 70 | Zehnder America, accessed May 23, 2026, [https://zehnderamerica.com/wp-content/uploads/2024/08/ComfoAir-70-Install-Manual-2017.08.30.pdf](https://zehnderamerica.com/wp-content/uploads/2024/08/ComfoAir-70-Install-Manual-2017.08.30.pdf)  
64. Mechanical Ventilation Heat Recovery (MVHR) \- Cinergi, accessed May 23, 2026, [https://cinergi.co.uk/services/mechanical-ventilation-heat-recovery-mvhr-installers/](https://cinergi.co.uk/services/mechanical-ventilation-heat-recovery-mvhr-installers/)

[image1]: <>

[image2]: <>

[image3]: <>

[image4]: <>

[image5]: <>

[image6]: <>

[image7]: <>

[image8]: <>

[image9]: <>

[image10]: <>

[image11]: <>

[image12]: <>

[image13]: <>

[image14]: <>

[image15]: <>

[image16]: <>

[image17]: <>

[image18]: <>

[image19]: <>

[image20]: <>

[image21]: <>

[image22]: <>

[image23]: <>

[image24]: <>

[image25]: <>

[image26]: <>

[image27]: <>

[image28]: <>

[image29]: <>

[image30]: <>

[image31]: <>

[image32]: <>

[image33]: <>

[image34]: <>

[image35]: <>

[image36]: <>

[image37]: <>

[image38]: <>

[image39]: <>

[image40]: <>

[image41]: <>

[image42]: <>

[image43]: <>

[image44]: <>

[image45]: <>

[image46]: <>

[image47]: <>

[image48]: <>

[image49]: <>

[image50]: <>

[image51]: <>

[image52]: <>

[image53]: <>

[image54]: <>

[image55]: <>

[image56]: <>

[image57]: <>

[image58]: <>

[image59]: <>

[image60]: <>

[image61]: <>

[image62]: <>

[image63]: <>

[image64]: <>

[image65]: <>

[image66]: <>

[image67]: <>

[image68]: <>

[image69]: <>

[image70]: <>

[image71]: <>

[image72]: <>

[image73]: <>
