wisogetnid/garden-room/research/sip-foundation-review.md

# **Technical Evaluation of the Structural and Geotechnical Integrity of Insulated Raft Foundations for Structural Insulated Panel Construction**

## **Comprehensive Framework for High-Performance Foundation Engineering**

The evolution of modern construction methodologies, particularly the shift toward high-performance building envelopes such as Structural Insulated Panels (SIPs), necessitates a concomitant advancement in foundation design. The traditional reliance on strip or trench-fill foundations is increasingly viewed as anachronistic in the context of energy-efficient design, primarily due to the inherent difficulty in eliminating thermal bridges at the floor-to-wall junction.1 The proposed master plan, which specifies a 150mm hardcore layer and a 100mm steel-reinforced concrete slab integrated with the Jackodur Atlas floating raft insulation system, represents a contemporary approach to foundation engineering.3 However, the validation of such a specification requires a multi-dimensional analysis that accounts for structural mechanics, building physics, geotechnical stability in specific regions like the Isle of Wight, and the additional gravitational and environmental stresses imposed by rooftop solar arrays.5  
The fundamental challenge in validating this specification lies in the intersection of lightweight superstructure requirements and the rigorous performance standards of Eurocode 2 and NHBC guidelines.8 While SIP buildings are notably lighter than traditional masonry structures, they are significantly more sensitive to differential settlement.10 The Jackodur Atlas system, utilizing high-density extruded polystyrene (XPS), offers a robust thermal and structural solution, but its efficacy is contingent upon the underlying sub-base preparation and the slab's ability to distribute loads without excessive deflection or cracking.1 This report provides an exhaustive technical validation of the proposed foundation components, examining the adequacy of the hardcore depth, the structural limits of a 100mm reinforced slab, and the complex interactions between the insulation system and the geotechnical environment.

## **Geotechnical Dynamics of the Isle of Wight: Clay Soils and Movement Risks**

The suitability of a raft foundation is inextricably linked to the underlying soil conditions. The Isle of Wight presents a complex geological landscape, characterized by significant deposits of Cretaceous and Palaeogene clays, including London Clay, Gault Clay, and Bembridge Marls.6 These clay formations are notorious for their shrink-swell potential, a characteristic where the soil volume fluctuates in response to moisture content.6

## **Shrink-Swell Potential and Foundation Depth**

Clay soils in southern England frequently experience seasonal moisture changes. During dry summer months, clays desiccate and shrink, while winter rainfall leads to saturation and expansion.6 This movement can reach up to 150mm in combined horizontal and vertical displacement, posing a severe risk to shallow foundations.6 For a SIP structure, which relies on precise joint alignments for airtightness, even minor differential settlement can be catastrophic.10

| Soil Type | Shrink-Swell Potential | Recommended Foundation Depth |
| :---- | :---- | :---- |
| London Clay | High | 900mm to 1,500mm 13 |
| Gault Clay | Significant | 1,000mm+ 14 |
| Bembridge Marls | Moderate to High | 750mm to 1,200mm 12 |
| Valley Gravel | Low | 600mm to 900mm 13 |

The proposed specification must ensure that the total depth of the foundation system—comprising the concrete, insulation, and hardcore—reaches a stable stratum or incorporates measures to mitigate frost heave and moisture sensitivity.14 UK building regulations typically mandate a minimum depth of 450mm below finished ground level to protect against frost damage.14 In clay-rich areas of the Isle of Wight, this depth often needs to be significantly greater to bypass the active moisture zone.7

## **Landslide and Slope Stability Considerations**

In addition to shrink-swell risks, the Isle of Wight’s geology is prone to landsliding, particularly where clay-rich units like the Wealden Group or Vectis Formation are exposed.17 While a raft foundation is excellent at distributing loads and minimizing localized failure, its placement on or near sloped ground requires careful analysis to prevent sliding failure.11 The Jackodur Atlas system’s BBA certificate explicitly requires that sliding resistance for lightweight structures be accounted for in the structural design, especially when lateral loads from wind or seismic activity are present.11

## **Structural Principles of the Jackodur Atlas System**

The Jackodur Atlas system represents a departure from traditional foundation methods by integrating load-bearing thermal insulation directly beneath the structural concrete slab.4 This configuration creates a "floating" raft, where the entire building mass is supported by the compressive strength of the XPS boards.2

## **Material Science of Extruded Polystyrene (XPS)**

The selection of XPS over expanded polystyrene (EPS) is a critical engineering decision. XPS is produced via an extrusion process that results in a closed-cell structure with no internal voids.19 This molecular arrangement provides superior moisture resistance, which is vital for long-term thermal and structural performance below ground.1

| Property | XPS (Jackodur Atlas) | Standard EPS |
| :---- | :---- | :---- |
| Water Absorption (Immersion) | \< 1% 1 | up to 10% 1 |
| Compressive Strength (10% def.) | 300, 500, or 700 kPa 20 | Typically 70-150 kPa 1 |
| Thermal Conductivity ($\\lambda\_D$) | 0.027 to 0.038 W/(m·K) 1 | 0.034 to 0.051 W/(m·K) 1 |
| Resistance to Freeze-Thaw | High 19 | Lower 1 |

XPS's ability to maintain its thermal conductivity even in the presence of groundwater (up to a depth of 3.5m) ensures that the building’s energy performance remains consistent over its 50-year design life.16 For most residential SIP applications, the Jackodur KF300 grade is adequate, providing a long-term design stress (compressive creep) of $130 \\, kPa$ at less than 2% deformation.22

## **Elimination of Thermal Bridging**

The primary architectural advantage of the Jackodur Atlas system is the elimination of the thermal bridge at the floor-slab-to-wall junction.1 By using interlocking Side and Formwork Elements, the insulation forms a continuous envelope that meets the external wall insulation (EWI) or SIP cladding.1 This is particularly relevant for the Isle of Wight’s coastal climate, where minimizing heat loss is essential for meeting rigorous thermal regulations such as the UK’s Part L or Passive House standards.1

## **Technical Validation of the 150mm Hardcore Layer**

The sub-base preparation is the foundation of the foundation. Its role is to provide a uniform bearing surface, manage moisture, and prevent frost from penetrating the ground beneath the raft.16

## **Compaction and Load Distribution**

A 150mm hardcore layer, typically composed of MOT Type 1 crushed stone, is a standard specification for residential extensions and smaller structures.3 For a raft foundation, the hardcore must be compacted in layers to ensure it can support the building load without settlement.14 The thickness of 150mm is generally sufficient for the bearing requirements of a lightweight SIP building, provided the underlying soil (the formation level) is competent.3  
However, the efficacy of the hardcore is contingent on the total thickness of the foundation system. In areas susceptible to frost, the "hardcore has to comply with the requirements of the planner/structural engineer" and should be non-frost susceptible.23 If the local frost penetration depth exceeds the combined thickness of the slab and hardcore, the 150mm layer may be insufficient unless additional frost insulation (a frost skirt) is employed.16

## **The Necessity of a Leveling Blinding Layer**

The Jackodur Atlas installation guide emphasizes a strict level tolerance of $\\pm 1 \\, cm$ over $5 \\, m$ for the sub-base.1 Achieving this level of precision with raw 150mm hardcore is practically impossible. Therefore, the specification must include a leveling layer—often referred to as a blinding layer—composed of 50mm of sharp sand or fine grit (e.g., 4/8mm).1

| Sub-base Component | Typical Thickness | Purpose |
| :---- | :---- | :---- |
| Compacted Hardcore | 150mm 3 | Load distribution and capillary break.24 |
| Sand/Grit Blinding | 50mm 1 | Leveling for insulation boards and protection against puncture.1 |
| DPM (1200 gauge) | \< 1mm | Vapor barrier and protection against rising damp.3 |

Without this blinding layer, the XPS boards of the Jackodur Atlas system may be subjected to uneven point loads from the crushed stone, potentially leading to localized crushing or gaps in the insulation joints that compromise the thermal envelope.2

## **Capillary Action and Moisture Management**

The 150mm hardcore layer acts as an essential capillary break, preventing groundwater from being drawn up to the underside of the insulation.26 In the context of the Isle of Wight’s clay soils, which can hold significant moisture, this layer is vital to prevent the insulation from sitting in standing water, which could lead to perimeter heat loss or, in extreme cases, the decay of the SIP sole plate due to moisture travel.26

## **Structural Analysis of the 100mm Reinforced Concrete Slab**

The proposal for a 100mm reinforced concrete slab is the most structurally sensitive aspect of the master plan. While 100mm is often considered a minimum baseline for ground-bearing slabs, its use as a structural raft for a SIP building requires rigorous validation.8

## **Raft Slab Mechanics and Thickness Standards**

A raft foundation is designed to span potential soft spots in the soil and distribute loads across the entire building footprint.28 The thickness of the slab determines its stiffness and its ability to resist bending moments.9

| Standard/Source | Typical/Minimum Thickness | Context |
| :---- | :---- | :---- |
| Jackodur Atlas BBA Cert | 200mm or 250mm 11 | Typical depths for certified residential builds. |
| NHBC Chapter 5.1 | 100mm 8 | Minimum for ground-bearing substructures. |
| Eurocode 2 | 125mm 9 | General minimum for floor slabs in buildings. |
| Single-Storey Extension | 150mm 14 | Recommended for modern extensions. |
| Proposed Plan | 100mm | Minimum possible; structurally sensitive. |

A 100mm slab is significantly thinner than the "typical" 200mm depths specified in the Jackodur Atlas BBA documentation.11 While technically possible for very light structures, the structural engineer must confirm that a 100mm slab can resist the bending and punching shear forces generated by the SIP walls and internal point loads without excessive deflection.11

## **Eurocode 2 Compliance and Concrete Cover**

The most significant constraint on a 100mm slab is the requirement for "concrete cover." Steel reinforcement must be encased in a specific depth of concrete to protect it from corrosion and fire.9 According to Eurocode 2 and NHBC guidelines, the nominal cover ($C\_{nom}$) is the sum of the minimum cover ($C\_{min}$) and an allowance for deviation ($\\Delta C\_{dev}$).9  
For a slab cast against a DPM on sand blinding, the standard cover requirements are:

* **Bottom Cover:** 40mm.9  
* **Top Cover:** 20mm to 30mm.9

In a 100mm slab, the internal space remaining for reinforcement is extremely limited:

$$100 \\, mm (Total) \- 40 \\, mm (Bottom) \- 25 \\, mm (Top) \= 35 \\, mm (Reinforcement Space)$$  
This 35mm must accommodate the thickness of the steel mesh and any required spacing between layers. For a raft foundation that must resist both upward soil pressure and downward wall loads, two layers of mesh (top and bottom) are often required.11 It is physically impossible to fit two layers of A393 or similar mesh into a 35mm space while maintaining the required spacing for aggregate flow and structural bond.33 Consequently, a 100mm slab is usually restricted to a single layer of mesh, which may be insufficient for a structural raft subject to varying moments.29

## **Concrete Grade and Performance**

To maintain the structural integrity of a thin slab, the concrete grade must be high. The Jackodur Atlas system specifies a strength class of **C32/40**.11 This mix provides the necessary compressive strength and durability, but it cannot compensate for the lack of sectional depth if the slab is subjected to significant bending forces from the SIP structure or the solar array.9

## **Structural Insulated Panel (SIP) Loading Characteristics**

SIP buildings are unique in their structural behavior. They act as "stressed skin" panels, where the OSB faces take axial and shear loads, while the core prevents buckling.10

## **Axial and Line Loads**

SIP walls create continuous line loads along the foundation perimeter.10 For a raft foundation, this is ideal as it distributes the load across the entire footprint of the Jackodur Atlas system.3 A typical 142mm or 150mm SIP panel has a high axial load capacity, often exceeding 2500 lbs per lineal foot (PLF), depending on height.36

| SIP Thickness | Panel Weight (kg/m2) | Axial Load Capacity (PLF \- 8ft height) |
| :---- | :---- | :---- |
| 100 mm | 15-18 37 | 2,750 36 |
| 150 mm | 22-26 37 | 4,000 36 |
| 200 mm | 30-33 37 | 4,000+ 36 |

While the weight of the SIP building itself is low compared to masonry, the foundation must be perfectly level. SIPs have very little tolerance for differential settlement; if the foundation shifts, the panel joints may open, leading to moisture infiltration, mold, and rot in the OSB facings.10 This reinforces the need for a stiff, robust foundation, even if the building is "light".10

## **Point Loads and Internal Framing**

Many SIP designs include internal point loads from ridge beams or floor joists.39 These concentrated loads can create significant pressure on a 100mm slab, increasing the risk of punching shear.29 If the master plan includes such features, the 100mm slab may require localized thickening (downstand beams) within the Jackodur system to safely transfer these loads to the XPS insulation.15

## **Impact of Rooftop Solar Arrays on Foundation Specifications**

The inclusion of a solar panel array on a SIP building introduces additional dead and live loads that must be accounted for in the structural validation.

## **Gravitational Dead Loads**

A standard solar panel array adds permanent weight to the roof structure. On average, a complete solar installation adds 2 to 4 pounds per square foot ($10$ to $20 \\, kg/m^2$) to the roof.5

| System Type | Added Weight (psf) | Total Load for 400 ft2 System |
| :---- | :---- | :---- |
| Anchored (Sloped Roof) | 2 to 4 5 | 800 to 1,600 lbs 5 |
| Ballasted (Flat Roof) | 5 to 10 42 | 2,000 to 4,000 lbs 42 |

For a single-family dwelling, an additional 1,000 to 2,000 lbs of dead load distributed over the perimeter walls is manageable for a raft foundation. However, the structural engineer must ensure that these loads do not exceed the $83 \\, kPa$ serviceability limit of the Jackodur Atlas insulation, particularly in areas where internal walls or posts support the roof.11

## **Environmental Live Loads: Snow and Wind**

The primary risk associated with solar panels is not the panels themselves, but how they interact with environmental loads.

1. **Snow Drifting:** Solar panels can act as barriers, causing snow to drift and accumulate in localized areas.5 This increases the downward pressure on the SIP walls and, consequently, the foundation.  
2. **Wind Uplift and Lateral Forces:** On the Isle of Wight, which is highly exposed to coastal winds, solar panels can experience significant wind uplift.5 These forces create lateral stresses on the foundation. Because SIP structures are lightweight, the foundation must provide enough mass to resist sliding or overturning.5

A 100mm slab may not provide sufficient "dead weight" to counteract wind uplift on a high-exposure site if the building has a large roof area and a high number of solar panels.5

## **Thermal Performance and Energy Standards**

The Jackodur Atlas system is a high-performance solution designed for buildings aiming for Passive House or Net-Zero standards.3

## **U-Value Calculations**

The thickness of the "Surface Element" (the insulation beneath the slab) is determined by the target U-value.1 For a SIP building, where the walls often achieve U-values of $0.15$ to $0.19 \\, W/m^2K$, the foundation should ideally match or exceed this performance to prevent a thermal weak point.3

| Insulation Thickness | U-Value (W/m2K) | Energy Rating |
| :---- | :---- | :---- |
| 100mm | \~0.35 | Building Regs Minimum 1 |
| 200mm | \~0.18 | High Performance 3 |
| 300mm | \~0.12 | Passive House Standard 1 |

The proposed master plan should specify the required thickness of the Jackodur Surface Elements to align with the building's overall energy strategy. Using a thicker insulation layer (e.g., 200mm) adds very little to the construction cost but significantly reduces long-term heating requirements.1

## **Moisture and Sole Plate Decay Risks**

A historical risk with insulated foundations is the potential for moisture to travel between the insulation and the concrete, leading to the decay of the timber sole plate in SIP or timber frame structures.26 The Jackodur Atlas system mitigates this through its tongue-and-groove joints and the use of a DPM (PE film) above the insulation to prevent cement slurry from filling joints during the pour.16 It is vital that the sole plate is positioned at least 150mm above the external ground level to prevent moisture ingress from driving rain or splashing.26

## **Execution and Installation Protocol**

The success of the Jackodur Atlas system depends on meticulous site preparation and installation.1

## **Sub-base Tolerance and Blinding**

The preparation begins with the compaction of the hardcore. Following compaction, the 50mm blinding layer is leveled using steel bars and a straight edge to achieve the required $\\pm 1 \\, cm$ tolerance.1 Any imperfections in this surface will translate into gaps between the interlocking XPS elements, creating thermal bridges and potential structural instability.1

## **Installation Sequence**

1. **Setting Out:** The building footprint is marked with a tolerance for the thickness of the insulation elements.23  
2. **Corner and Side Elements:** The initial corner element is placed, followed by the Side Elements, which form the perimeter of the raft.1  
3. **Formwork Elements:** The vertical formwork elements are inserted into the grooves of the side elements, providing the shuttering for the concrete pour.1  
4. **Surface Elements:** The horizontal surface elements are laid in a bond pattern, tightly against one another.16  
5. **DPM and Reinforcement:** A 1200 gauge DPM is laid over the insulation, and the steel mesh reinforcement is placed on bar chairs to ensure correct cover.3  
6. **Concrete Pour:** The C32/40 concrete is poured to the specific height of the Atlas formwork, compacted, and leveled.11

## **Bracing for Thick Slabs**

If the concrete thickness exceeds 300mm, vertical bracing is required every 1.2 meters to prevent the formwork from bowing under the hydrostatic pressure of the wet concrete.19 While the proposed 100mm slab does not reach this threshold, it still requires careful pouring to avoid displacing the Side Elements.19

## **Conclusion and Strategic Validation of Specifications**

The validation of the master plan foundation specification reveals a high-performance system that requires two specific adjustments to meet structural and regulatory standards.

## **Final Validation of the 150mm Hardcore Layer**

The 150mm hardcore layer is **conditionally adequate** as a structural sub-base for a lightweight SIP building.3 However, it is **insufficient** in isolation for the Jackodur Atlas system.

* **Correction Required:** The specification must include a 50mm leveling blinding layer of sand or grit on top of the hardcore to meet the $\\pm 1 \\, cm$ tolerance required for the interlocking insulation.1  
* **Geotechnical Note:** On the Isle of Wight’s clay soils, the total depth of the foundation (hardcore \+ insulation \+ concrete) should be reviewed by the structural engineer to ensure it reaches below the active moisture zone or incorporates a frost skirt.13

## **Final Validation of the 100mm Reinforced Concrete Slab**

The 100mm concrete floor is **structurally high-risk** and likely fails to meet Eurocode 2 standards for reinforced concrete.9

* **The Reinforcement Dilemma:** A 100mm slab cannot accommodate the top and bottom mesh layers required for a structural raft while maintaining the mandated concrete cover (40mm bottom, 25mm top).9  
* **Solar Loads:** While the solar panels add manageable weight, the reduction in sectional depth (100mm vs. typical 200mm) makes the slab vulnerable to cracking under uneven environmental loads like snow drifting or wind uplift.5  
* **Recommendation:** The concrete slab thickness should be increased to a minimum of **150mm to 200mm**. This allows for the installation of two mesh layers (e.g., A393) with correct cover, providing the stiffness required to support the SIP structure and solar array while ensuring the long-term durability of the foundation.9

## **Integration with Jackodur Atlas**

The use of the Jackodur Atlas system is **strongly validated** for this project.3 It provides the thermal continuity necessary for a high-performance SIP building and is an NHBC-accepted solution.4 By increasing the slab thickness to 150-200mm and adding the necessary blinding layer to the sub-base, the foundation will meet all structural, thermal, and regulatory requirements for the master plan, providing a stable and energy-efficient base for the SIP building and its renewable energy systems.

#### **Works cited**

1. The Structural Insulated Passive Slab Formwork System. \- BEWI, accessed March 20, 2026, [https://bewi.com/wp-content/uploads/2024/09/Atlas-Catalogue.pdf](https://bewi.com/wp-content/uploads/2024/09/Atlas-Catalogue.pdf)  
2. Perimeter insulation of foundation slab \- JACKON Insulation, accessed March 20, 2026, [https://www.jackon-insulation.com/applications/detail/perimeter-insulation-of-foundation-slab](https://www.jackon-insulation.com/applications/detail/perimeter-insulation-of-foundation-slab)  
3. SIPs Foundations \- ICF Building Solutions, accessed March 20, 2026, [https://www.icfbuildingsolutions.co.uk/sips-foundations/](https://www.icfbuildingsolutions.co.uk/sips-foundations/)  
4. JACKODUR® Atlas \- JACKON Insulation, accessed March 20, 2026, [https://www.jackon-insulation.com/products/detail/jackodur-atlas](https://www.jackon-insulation.com/products/detail/jackodur-atlas)  
5. How to run a structural load analysis for rooftop PV racking \- Anern Store, accessed March 20, 2026, [https://www.anernstore.com/blogs/diy-solar-guides/pv-racking-roof-load-analysis](https://www.anernstore.com/blogs/diy-solar-guides/pv-racking-roof-load-analysis)  
6. Buildings on Clay \- Building Conservation Directory, accessed March 20, 2026, [https://www.buildingconservation.com/articles/buildclay/buildclay.htm](https://www.buildingconservation.com/articles/buildclay/buildclay.htm)  
7. Foundation Solutions for Clay Soil in Southern England, accessed March 20, 2026, [https://speedeck.uk/news/all-articles/clay-soils-southern-england/](https://speedeck.uk/news/all-articles/clay-soils-southern-england/)  
8. accessed March 20, 2026, [https://www.newbuildinspections.com/knowledgebase/nhbc-standards-chapter-5-1-substructure-and-ground-bearing-floors/\#:\~:text=The%20concrete%20used%20for%20ground,sufficient%20structural%20capacity%20and%20longevity.](https://www.newbuildinspections.com/knowledgebase/nhbc-standards-chapter-5-1-substructure-and-ground-bearing-floors/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,sufficient%20structural%20capacity%20and%20longevity.)  
9. Minimum Thickness of Concrete Elements \- Heaton Manufacturing, accessed March 20, 2026, [https://heatonmanufacturing.co.uk/minimum-thickness-of-concrete-elements/](https://heatonmanufacturing.co.uk/minimum-thickness-of-concrete-elements/)  
10. Structural Insulated Panels (SIPs) | WBDG \- Whole Building Design Guide, accessed March 20, 2026, [https://www.wbdg.org/resources/structural-insulated-panels-sips](https://www.wbdg.org/resources/structural-insulated-panels-sips)  
11. JACKODUR Atlas Foundation Insulation System \- BEWI, accessed March 20, 2026, [https://bewi.com/wp-content/uploads/2023/11/Jackodur-Atlas-BBA-5812ps1i2.pdf](https://bewi.com/wp-content/uploads/2023/11/Jackodur-Atlas-BBA-5812ps1i2.pdf)  
12. Isle of Wight \- Geology, Introduction by Ian West., accessed March 20, 2026, [https://wessexcoastgeology.soton.ac.uk/wight.htm](https://wessexcoastgeology.soton.ac.uk/wight.htm)  
13. Minimum Depth of Foundations | UK Building Regulations Explained, accessed March 20, 2026, [https://southernfoundationspiling.co.uk/blog/minimum-foundation-depth/](https://southernfoundationspiling.co.uk/blog/minimum-foundation-depth/)  
14. Minimum depth of foundations for building regulations UK \- UK Underpinning Solutions, accessed March 20, 2026, [https://ukunderpinningsolutions.co.uk/blog/minimum-depth-of-foundation-for-building-regulations-uk/](https://ukunderpinningsolutions.co.uk/blog/minimum-depth-of-foundation-for-building-regulations-uk/)  
15. Minimum Foundation Depths for UK Buildings Regulations \- Extension Architecture, accessed March 20, 2026, [https://extensionarchitecture.co.uk/blog/minimum-foundation-depths-for-uk-buildings-regulations/](https://extensionarchitecture.co.uk/blog/minimum-foundation-depths-for-uk-buildings-regulations/)  
16. Insulation beneath the floor slab., accessed March 20, 2026, [https://www.jackon-insulation.com/downloads-service/download/jackodur-insulation-beneath-the-floor-slab](https://www.jackon-insulation.com/downloads-service/download/jackodur-insulation-beneath-the-floor-slab)  
17. Geology as a control on landslides on the Isle of Wight: an overview \- NERC Open Research Archive, accessed March 20, 2026, [https://nora.nerc.ac.uk/id/eprint/16091/1/Jenkins\_Landslides\_PGEOLA-D-11-00038R1.pdf](https://nora.nerc.ac.uk/id/eprint/16091/1/Jenkins_Landslides_PGEOLA-D-11-00038R1.pdf)  
18. JACKODUR® Atlas floor slab insulation system, accessed March 20, 2026, [https://www.jackon-insulation.com/applications/detail/jackodur-atlas-floor-slab-insulation-system](https://www.jackon-insulation.com/applications/detail/jackodur-atlas-floor-slab-insulation-system)  
19. Jackodur® Atlas Foundation System | BEWI, accessed March 20, 2026, [https://bewi.com/products/jackodur-atlas?lang=en-gb](https://bewi.com/products/jackodur-atlas?lang=en-gb)  
20. Thermal insulation for structural use. \- Civils Store, accessed March 20, 2026, [https://www.civilsstore.co.uk/content/large/products/6929847013e461.04760525.pdf](https://www.civilsstore.co.uk/content/large/products/6929847013e461.04760525.pdf)  
21. JACKODUR® Atlas: Quick and affordable foundation insulation with click system, accessed March 20, 2026, [https://stedenbouw.nl/en/general/jackodur-atlas-quick-and-affordable-foundation-insulation-with-click-system/](https://stedenbouw.nl/en/general/jackodur-atlas-quick-and-affordable-foundation-insulation-with-click-system/)  
22. JACKODUR Atlas \- JACKON Insulation, accessed March 20, 2026, [https://www.jackon-insulation.com/downloads-service/download/jackodur-atlas](https://www.jackon-insulation.com/downloads-service/download/jackodur-atlas)  
23. Perfect floor slab insulation for every type of house., accessed March 20, 2026, [https://www.jackon-insulation.com/downloads-service/download/jackodur-atlas-edge-system](https://www.jackon-insulation.com/downloads-service/download/jackodur-atlas-edge-system)  
24. A Guide to Building Foundations \- Heidelberg Materials UK, accessed March 20, 2026, [https://www.heidelbergmaterials.co.uk/en/ready-mixed-concrete/technical-information/building-foundation-guide](https://www.heidelbergmaterials.co.uk/en/ready-mixed-concrete/technical-information/building-foundation-guide)  
25. Building Foundations \- UK Common Practice | RPO \- Reinforcement Products Online, accessed March 20, 2026, [https://www.reinforcementproductsonline.co.uk/news/building-foundations-uk-common-practice/](https://www.reinforcementproductsonline.co.uk/news/building-foundations-uk-common-practice/)  
26. Foundation options on SIPS house \- Green Building Forum, accessed March 20, 2026, [https://www.greenbuildingforum.co.uk/newforum/comments.php?DiscussionID=7029](https://www.greenbuildingforum.co.uk/newforum/comments.php?DiscussionID=7029)  
27. What is a Raft Slab \- Cornell Engineers, accessed March 20, 2026, [https://cornellengineers.com.au/what-is-a-raft-slab/](https://cornellengineers.com.au/what-is-a-raft-slab/)  
28. Raft Foundations: Engineers' Insights on Using Them, accessed March 20, 2026, [https://sussexstructuralengineers.co.uk/raft-foundations-engineers-insights/](https://sussexstructuralengineers.co.uk/raft-foundations-engineers-insights/)  
29. Raft Foundation Design for Heavy Loads and Low Bearing Capacity Soils, accessed March 20, 2026, [https://fsm.how/building-maintenance/raft-foundation-design-heavy-loads-soils/](https://fsm.how/building-maintenance/raft-foundation-design-heavy-loads-soils/)  
30. How Thick Should a Concrete Slab Be?, accessed March 20, 2026, [https://barrowmixconcrete.com/how-thick-should-a-concrete-slab-be/](https://barrowmixconcrete.com/how-thick-should-a-concrete-slab-be/)  
31. Minimum Depth of Foundations Building Regulations UK, accessed March 20, 2026, [https://lillylewarne.co.uk/minimum-depth-foundations-uk/](https://lillylewarne.co.uk/minimum-depth-foundations-uk/)  
32. Upgrading Existing Concrete Structures with Aestuver ® Fire Protection Boards, accessed March 20, 2026, [https://www.aestuver.com/en/concrete-fire-protection](https://www.aestuver.com/en/concrete-fire-protection)  
33. Chapter 5\. Concrete Design and Construction Details \- datcp, accessed March 20, 2026, [https://datcp.wi.gov/Documents/CDSChapter5.pdf](https://datcp.wi.gov/Documents/CDSChapter5.pdf)  
34. Double-Layer Reinforcement in Reinforced Concrete \- Darda GmbH, accessed March 20, 2026, [https://www.darda.de/en/knowledge/double-layer-reinforcement](https://www.darda.de/en/knowledge/double-layer-reinforcement)  
35. How much rebar overlap can I have for concrete pad? : r/DIYUK \- Reddit, accessed March 20, 2026, [https://www.reddit.com/r/DIYUK/comments/1cnxnm9/how\_much\_rebar\_overlap\_can\_i\_have\_for\_concrete\_pad/](https://www.reddit.com/r/DIYUK/comments/1cnxnm9/how_much_rebar_overlap_can_i_have_for_concrete_pad/)  
36. Load Design Chart \- Big Sky R-Control SIPs, accessed March 20, 2026, [https://bigskyrcontrol.com/media/2684/r-control-load-design-chart.pdf](https://bigskyrcontrol.com/media/2684/r-control-load-design-chart.pdf)  
37. LOAD CHARTS \- Premier SIPS, accessed March 20, 2026, [https://sips.premierbuildingsystems.com/hubfs/Premier%20SIPS/Content%20Resources/Technical%20Docs/PSIPS\_LoadCharts\_7-22.pdf](https://sips.premierbuildingsystems.com/hubfs/Premier%20SIPS/Content%20Resources/Technical%20Docs/PSIPS_LoadCharts_7-22.pdf)  
38. Structural Insulated Panels (SIPs), accessed March 20, 2026, [https://sipbuilduk.co.uk/wp-content/uploads/2023/09/SIPs-data-sheet-final-2022.pdf](https://sipbuilduk.co.uk/wp-content/uploads/2023/09/SIPs-data-sheet-final-2022.pdf)  
39. Structural Insulated Panels (SIPs) \- Building America Solution Center, accessed March 20, 2026, [https://basc.pnnl.gov/resource-guides/structural-insulated-panels-sips](https://basc.pnnl.gov/resource-guides/structural-insulated-panels-sips)  
40. Understanding Roof Load Capacity for Solar Panels | KPost Company, accessed March 20, 2026, [https://kpostcompany.com/understanding-roof-load-capacity-for-solar-panels/](https://kpostcompany.com/understanding-roof-load-capacity-for-solar-panels/)  
41. Homeowner's Guide to Solar Panel Weight, accessed March 20, 2026, [https://www.solarenergyworld.com/blog/solar-faqs/solar-panel-weight-guide/](https://www.solarenergyworld.com/blog/solar-faqs/solar-panel-weight-guide/)  
42. Solar loads? : r/StructuralEngineering \- Reddit, accessed March 20, 2026, [https://www.reddit.com/r/StructuralEngineering/comments/1m12aqy/solar\_loads/](https://www.reddit.com/r/StructuralEngineering/comments/1m12aqy/solar_loads/)  
43. Dead load vs. live load: why lightweight solar matters \- LONGi Solar, accessed March 20, 2026, [https://eu.longi.com/blog/lightweight-panel-planning-understanding-dead-load-vs-live-load-in-rooftop-solar](https://eu.longi.com/blog/lightweight-panel-planning-understanding-dead-load-vs-live-load-in-rooftop-solar)  
44. Inquiry for JACKODUR® Atlas \- JACKON Insulation, accessed March 20, 2026, [https://www.jackon-insulation.com/downloads-service/request-jackodur-atlas](https://www.jackon-insulation.com/downloads-service/request-jackodur-atlas)
