wisogetnid/garden-room/research/iow-sip-research.md

# **Technical and Strategic Evaluation of Structural Insulated Panel Manufacturing and Implementation for the Isle of Wight Construction Sector**

The contemporary construction environment in the United Kingdom is characterized by a rapid shift toward Offsite Manufacturing (OSM) and Modern Methods of Construction (MMC). Central to this transformation is the Structural Insulated Panel (SIP), a high-performance building system that integrates structural capacity and thermal insulation into a single, factory-produced component. For stakeholders on the Isle of Wight, the adoption of SIP technology presents a unique opportunity to overcome traditional logistical barriers, such as the "island premium" on labor and materials, while meeting the increasingly stringent energy efficiency requirements of the 2025 Future Homes Standard and Passivhaus principles. This report provides an exhaustive analysis of the manufacturing landscape, technical specifications, fire safety protocols, and economic considerations for SIP implementation on the Isle of Wight and the broader South Coast.

## **The Regional Manufacturing Landscape and Proximity Analysis**

The viability of a SIP project on the Isle of Wight is heavily dictated by the proximity of the manufacturing facility to the Solent crossing points. Transporting oversized, pre-fabricated components requires careful coordination with ferry operators such as Red Funnel and Wightlink, where the costs are influenced by vehicle length, weight, and the timing of crossings.

## **Primary Regional Manufacturers: The Hampshire and South Coast Cluster**

With the removal of local island-based manufacturing options, the most geographically advantageous partners are now located in the Hampshire and New Forest regions, primarily utilizing the Lymington-Yarmouth or Southampton-East Cowes routes.

* **New Forest SIPs Ltd:** Based in Lymington, they represent the most critical local partner for Isle of Wight projects. Operating from a dedicated workshop facility, they provide end-to-end services including bespoke design, precision manufacturing, and professional installation.1 Their proximity to the Lymington-Yarmouth ferry route minimizes transit times and allows for responsive site support. They specialize in high-performance polyurethane (PUR) cores with 12mm Oriented Strand Board (OSB/3) facings.  
* **Direct Sips:** Headquartered in Blackburn but maintaining a robust support network across Hampshire (specifically Southampton, Portsmouth, and Winchester), they specialize in modular flat-pack kits optimized for transport efficiency. Their kits are designed for rapid assembly, which is vital when managing narrow island site access and limited construction windows.

Historically, SIPs Panels Ltd (SPL) was a prominent player in the Lymington area, but the company entered extraordinary voluntary liquidation in April 2024\.4 This transition underscores the necessity for self-builders to prioritize manufacturers with long-term financial stability and audited certifications such as STA Assure.

## **National Manufacturers and Specialist Suppliers**

For projects requiring specific certified systems or high-volume production, national manufacturers provide established delivery routes to the South Coast.

| Manufacturer | Core Location | Technical Specialization | Market Focus |
| :---- | :---- | :---- | :---- |
| Sips UK | Northamptonshire | Five-axis CNC machining, Large-scale production | Architects, Developers, Garden Buildings |
| Sips Eco Panels | Fife, Scotland | Passivhaus-aligned splines, EPS-core systems | New Builds, Commercial, Nationwide 6 |
| Future Rooms | Gloucester | SIP Garden Rooms & Offices, IOW installation services | Garden Offices, Studios, Annexes |
| Cave Innovations | Durham | "Pre-clad" composite SIP garden buildings | DIY Garden Buildings, Low Maintenance |
| UltraSIPs | UK-Wide | Online configurator and U-value calculators | DIY Self-Builders, Rapid Prototyping |

## **Integrated External Cladding and Finishing Solutions**

A major evolution in modular SIPs is the shift toward "integrated" cladding, where the external finish is either factory-applied or supplied as a complete, coordinated kit. This reduces on-site labor and ensures the building is weatherproofed immediately upon erection.

## **Factory-Applied and Pre-Clad Systems**

Certain manufacturers provide panels where the cladding is integrated during the manufacturing process to minimize on-site finishing:

* **Composite Pre-Clad Walls (Cave Innovations):** For garden room applications, Cave Innovations provides walls that are "provided pre-clad" with UV-stable composite cladding. This eliminates the need for site-applied finishes, allowing 2-3 people to assemble a complete, finished structure quickly.  
* **Eurocell Garden Rooms:** These units utilize composite SIP panels with integrated low-maintenance finishes available in 10 colors, ensuring the building is maintenance-free from day one.  
* **MgO Board Systems:** While not always "pre-finished" with timber, panels faced with Magnesium Oxide (MgO) from suppliers like Dragonboard serve as a high-durability external sheathing that is "decoration ready." These can be directly rendered or painted without the need for additional plywood sheathing.

## **"Full Exterior" and "Shell" Kits**

For self-builders who want a single point of responsibility without factory-bonded cladding, "Full Exterior Kits" provide all necessary finishing materials as a bundle:

* **Direct Sips Exterior Kits:** These include the SIP structure, breathable membrane, battens, and exterior cladding (timber or composite). This ensures all components are dimensionally compatible and delivered as a single package to the site.  
* **Future SIPs Wall Systems:** They offer a Building Regulations compliant wall build-up that specifies the cladding, batten size, and breather membrane as an integrated technical assembly to ensure moisture management and fire safety.

## **Structural Composition and Durability Standards**

A standard UK-manufactured SIP consists of an insulating core—typically Expanded Polystyrene (EPS), Polyurethane (PUR), or Polyisocyanurate (PIR)—sandwiched between two structural facings of OSB/3 or Magnesium Oxide (MgO).

## **Material Integrity and Lifespan**

The British Board of Agrément (BBA) typically certifies SIP systems for a minimum design life of 60 years, provided the installation remains weathertight. Reliability on the Isle of Wight is further complicated by the coastal climate. High salt content and wind-driven rain necessitate a rigorous external envelope strategy.

* **OSB Systems:** Require an immediate application of a breathable membrane (e.g., TF200) after erection to prevent moisture ingress.  
* **MgO Systems:** Offer superior moisture resistance as the boards are inorganic, impervious to water, and do not swell or delaminate in high humidity.

## **Passivhaus Alignment and Thermal Performance**

The Passivhaus standard requires opaque building elements to achieve a U-value of $\\leq 0.15 \\, W/m^2K$. SIPs are uniquely equipped for this due to the minimization of thermal bridging.

| Panel Thickness (mm) | Core Material | Typical U-Value (W/m2K) | Passivhaus Suitability |
| :---- | :---- | :---- | :---- |
| 122mm | PIR/PUR | 0.209 | High Performance |
| 142mm | PIR/PUR | 0.13 \- 0.17 | Aligned with Passivhaus 6 |
| 172mm | PIR/PUR | 0.144 | Exceeds Passivhaus |
| 197mm \- 219mm | EPS/PUR | 0.10 \- 0.13 | Ultra-Low Energy |

## **Fire Resistance and Regulatory Compliance**

In the wake of the Building Safety Act 2022 and 2024-2026 updates to Approved Document B, fire resistance is a critical specification.

## **Fire Performance Ratings (REI)**

Traditional OSB SIPs are typically Class 3 for surface spread of flame. To achieve REI30 or REI60 ratings (30 or 60 minutes of load-bearing fire resistance), the "through-wall" build-up usually requires one or two layers of fire-rated plasterboard (Type F) internally.

## **Magnesium Oxide (MgO) as a Non-Combustible Alternative**

MgO SIPs (e.g., from Dragonboard or SIPit-FR) feature A1-rated non-combustible facings. These panels can achieve up to **4 hours** of fire resistance, making them ideal for high-risk boundaries or multi-occupancy structures.

## **Fire Safety Regulations for 2024-2026**

* **Boundary Distances:** For garden rooms between 15 and 30 square meters, structures within 1 meter of a boundary must be built from "substantially non-combustible materials."  
* **2025/2026 Updates:** Approved Document B updates focus on transitioning to BS EN 13501 classifications and introducing mandatory second staircases for residential buildings over 18m.

## **Economic Modeling: Costs and Logistics for the Isle of Wight**

## **Material and Component Costs (2025/2026 Estimates)**

| Panel Type | Dimensions | Price (ex. VAT) | Price (inc. VAT) |
| :---- | :---- | :---- | :---- |
| OSB SIP 119mm | 1.2m x 2.4m | £102.24 | £122.69 |
| OSB SIP 144mm | 1.2m x 2.4m | £108.63 | £130.36 |
| MgO SIP 100mm | 1.2m x 2.4m | £103.00 | £123.60 |
| MgO SIP 115mm | 1.2m x 2.7m | £119.00 | £142.80 |

Turnkey project costs for a detached SIP home are estimated at approximately £1,377 per square meter.

## **Transport and Ferry Logistics**

For island projects, ferry fees represent a major pass-through expense. A 17-meter articulated lorry crossing via Red Funnel or Wightlink can incur significant fees, often exceeding £400 for a return car crossing and substantially more for freight.

* **Site Access:** Narrow rural roads on the Isle of Wight often require a "shuttle" service, where panels are transferred to smaller rigid vehicles for final delivery.  
* **Haulage:** Standard haulage is roughly $2 to $4 per mile from factory to port.

## **Conclusion: Strategic Recommendations for Isle of Wight Projects**

The adoption of Structural Insulated Panels on the Isle of Wight requires a sophisticated response to logistical and environmental challenges.

* **Manufacturer Selection:** Prioritize **New Forest SIPs** (Lymington) for proximity and bespoke installation expertise on the island.  
* **Integrated Cladding:** For rapid builds and garden rooms, select "pre-clad" systems from **Cave Innovations** or **Eurocell** to minimize site labor and ensure immediate weather protection in the Solent's humid environment.  
* **Safety & Compliance:** Use **MgO-faced panels** for any structure within 1m of a boundary to meet "substantially non-combustible" requirements without needing secondary fire-rated cladding.  
* **Moisture Management:** Ensure the "through-wall" build-up includes a high-performance breathable membrane and a ventilated rainscreen cavity to achieve the target 60-year design life.

#### **Works cited**

1. SIPs Contractors in Bournemouth, SIPs Installation in Hampshire, accessed March 17, 2026, [https://www.newforestsips.co.uk/](https://www.newforestsips.co.uk/)  
2. SIPs Manufacturing in Salisbury, Hampshire, Southampton, Bournemouth and All Surrounds, accessed March 17, 2026, [https://www.newforestsips.co.uk/sips-manufacturing.html](https://www.newforestsips.co.uk/sips-manufacturing.html)  
3. Garden Room Building Regs UK: What You Need to Know (2025 Guide) \- Arkiplan, accessed March 17, 2026, [https://arkiplan.co.uk/2025/08/29/garden-room-building-regs-uk/](https://arkiplan.co.uk/2025/08/29/garden-room-building-regs-uk/)  
4. SIPs Panels Ltd., accessed March 17, 2026, [https://sips-panels.co.uk/](https://sips-panels.co.uk/)  
5. SIPS PANELS LTD filing history \- Find and update company information, accessed March 17, 2026, [https://find-and-update.company-information.service.gov.uk/company/10267902/filing-history](https://find-and-update.company-information.service.gov.uk/company/10267902/filing-history)  
6. Eco-friendly SIP panels for New Build Homes, accessed March 17, 2026, [https://www.sipsecopanels.co.uk/new-builds/](https://www.sipsecopanels.co.uk/new-builds/)  
7. SIPs Panels Direct | SIPs Eco Panels, accessed March 17, 2026, [https://www.sipsdirect.co.uk/](https://www.sipsdirect.co.uk/)  
8. Hemsec SIPs panels achieve FR30 & update FR60 in new fire resistance tests to BS EN 1365-1:2012, accessed March 17, 2026, [https://hemsec.com/hemsec-sips-panels-achieve-fr30-update-fr60-in-new-fore-resistance-tests-to-bs-en-1365-1-2012/](https://hemsec.com/hemsec-sips-panels-achieve-fr30-update-fr60-in-new-fore-resistance-tests-to-bs-en-1365-1-2012/)
