wisogetnid/garden-room/research/modular-research.md

# **Advanced Modular Construction Strategies for High-Performance Garden Structures: A Technical Transition from Timber Framing to Passivhaus-Compliant Non-Combustible Systems**

The architectural paradigm for garden rooms is currently transitioning from a focus on seasonal utility to year-round, high-performance occupancy. This evolution necessitates a fundamental departure from traditional timber frame construction, which often presents limitations regarding fire safety, thermal consistency, and long-term maintenance in the face of moisture and salt-laden coastal atmospheres. The contemporary garden room context requires a building envelope that not only satisfies the rigorous criteria of the Passivhaus standard—characterized by exceptional airtightness and thermal bridge-free design—but also adheres to stringent fire safety regulations, particularly when structures are positioned within close proximity to property boundaries. To address these multifaceted demands, modular construction strategies utilizing advanced materials such as Magnesium Oxide (MgO) Structural Insulated Panels (SIPs), Insulated Concrete Formwork (ICF), and pre-finished architectural metal panels have emerged as superior alternatives to the legacy timber solution. These systems provide the precision of factory-controlled manufacturing, ensuring that the performance targets calculated during the design phase are accurately realized on-site, effectively bridging the performance gap often found in traditional construction.

## **The Technological Imperative for Modular Transition**

The move away from traditional timber framing toward modern methods of construction (MMC) is driven by the requirement for predictable structural and thermal performance. Timber frame construction, while historically proven, relies heavily on the skill of site labour to ensure the continuity of insulation and the integrity of the airtightness layer.1 In a garden room context, where the structure is exposed on all sides to environmental stressors, even minor defects in the vapor control layer or gaps in the insulation can lead to significant thermal bypassing and eventual structural decay.2 Modular systems, by contrast, are fabricated to millimetre tolerances in controlled environments, which significantly reduces the risk of on-site build error.4  
Modular construction generally bifurcates into panellised systems, where two-dimensional components are assembled on-site, and volumetric modularity, where three-dimensional units are delivered nearly 95% complete.6 For the specific constraints of the garden room context—often characterized by restricted residential access and the logistical challenges of the Isle of Wight—panellised modular systems such as MgO SIPs or ICF offer the optimal balance of off-site precision and on-site manoeuvrability.5 These systems allow for the rapid enclosure of the building envelope, often within days, minimizing site disruption and protecting internal finishes from the unpredictable UK climate.5

## **Comparative Assessment of Construction Paradigms**

| Feature | Traditional Timber Frame | Volumetric Modular | Panellised SIPs (MgO) | Insulated Concrete Formwork (ICF) |
| :---- | :---- | :---- | :---- | :---- |
| **Speed of Enclosure** | Weeks | Days | Days | Moderate |
| **Airtightness Potential** | Variable (Site Dependent) | High (Factory Controlled) | Exceptional (Inherent) | High (Monolithic) |
| **Fire Safety Rating** | Combustible (Class D/E) | Varies by Finish | Non-Combustible (Class A1) | Non-Combustible (4+ Hours) |
| **Moisture Resistance** | Susceptible to Rot | Moderate | Exceptional (Anti-microbial) | Exceptional (Hydrophobic) |
| **Maintenance Need** | High (Staining/Painting) | Low (Integrated Finish) | Minimal (Integrated Finish) | Low (Render/Clad) |
| **Thermal Mass** | Low | Low | Low | High |
| **Site Access Needs** | High Flexibility | Restricted (Crane) | Moderate (Manual Handling) | Moderate (Pump/Agitator) |

The transition to modularity also addresses the critical "Performance Gap" which is the disparity between designed energy performance and real-world outcomes. Research indicates that certified Passivhaus buildings, which rely on the geometric accuracy inherent in modular systems, show little to no performance gap compared to traditional builds.14 This predictability is essential for the long-term economic viability of the structure, ensuring that heating and cooling demands remain negligible throughout the lifecycle of the building.9

## **Passivhaus Physics and the Garden Room Envelope**

The Passivhaus standard is defined by five key technical pillars: high-quality insulation, thermal bridge-free design, airtightness, high-performance glazing, and mechanical ventilation with heat recovery (MVHR).9 In a small-scale garden room, the high surface-area-to-volume ratio makes heat loss through the building fabric much more significant than in a larger residential unit.16 Consequently, achieving the standard requires $U$-values for the walls, roof, and floor to typically fall between $0.10$ and $0.15 W/m^2K$.4  
Thermal bridges—areas where heat can easily bypass the insulation layer—are the primary cause of thermal failure in garden structures. In traditional timber frames, every structural stud acts as a thermal bridge, conducting heat faster than the surrounding insulation.2 Modular SIPs overcome this by using a continuous insulation core, with interlocking splines that maintain thermal continuity across the entire envelope.5 When these panels are manufactured with advanced insulation cores such as Kingspan’s QuadCore technology or BASF’s Elastapor PUR foam, the thermal conductivity ($\\lambda$) can be as low as $0.018 W/m \\cdot K$ to $0.019 W/m \\cdot K$, allowing for slimmer wall profiles while exceeding Passivhaus targets.18

## **Thermal Performance Metrics of Advanced Modular Cores**

| Core Material | Thermal Conductivity (λ) | Thickness for U=0.15 | Thickness for U=0.10 |
| :---- | :---- | :---- | :---- |
| **Traditional EPS** | $0.038 W/m \\cdot K$ | $250 mm$ | $380 mm$ |
| **Graphite-EPS (Neopor)** | $0.030 W/m \\cdot K$ | $200 mm$ | $300 mm$ |
| **PIR / PUR Foam** | $0.022 W/m \\cdot K$ | $145 mm$ | $220 mm$ |
| **Kingspan QuadCore** | $0.018 W/m \\cdot K$ | $120 mm$ | $180 mm$ |
| **Phenolic (Kooltherm)** | $0.020 W/m \\cdot K$ | $130 mm$ | $200 mm$ |

Achieving airtightness of $\\leq 0.6$ ACH @ 50 Pa is equally critical for Passivhaus compliance.14 Modular panels assist in this requirement by serving as a robust primary air barrier. In MgO SIP systems, the inorganic boards themselves are virtually airtight, meaning the focus of the airtightness strategy shifts entirely to the sealing of the factory-precision joints.4 This contrasts with timber frames, where the airtightness relies on a flexible membrane that can be easily punctured during the installation of services or by building movement over time.16

## **The Science of Magnesium Oxide (MgO) Structural Insulated Panels**

As a replacement for timber-faced SIPs, Magnesium Oxide (MgO) panels offer a unique combination of structural strength, fire non-combustibility, and moisture resilience. MgO board is a mineral-based building product manufactured from magnesium oxide, magnesium chloride (or sulfate), perlite, and fiberglass mesh.25 During the manufacturing process, these components undergo an exothermic reaction that creates a stone-like lattice, providing a material that is significantly more durable than Oriented Strand Board (OSB) or gypsum-based products.25  
The application of MgO boards to SIP technology creates a composite panel where the inorganic skins provide structural racking strength and fire protection, while the foam core provides thermal resistance.4 These panels are specifically engineered for high-performance building envelopes where the structure must meet Passivhaus standards while remaining impervious to environmental degradation.22

## **Structural and Fire Resilience of MgO SIPs**

MgO boards are classified as Euroclass A1 or A2-s1,d0, meaning they are non-combustible and do not contribute to flame spread, smoke production, or flaming droplets.28 This fire safety profile is a critical second-order insight: in the garden room context, using an A1-rated modular panel allows for the structure to be built close to property boundaries without the need for additional, heavy-duty fire cladding.13 Furthermore, MgO panels exhibit superior impact resistance and "screw-pull-out" strength, making them ideal for high-traffic or high-use spaces such as garden gyms or professional workshops.26

| Metric | MgO Board Performance | OSB Performance |
| :---- | :---- | :---- |
| **Fire Rating** | A1 (Non-Combustible) | D/E (Combustible) |
| **Reaction to Fire** | Zero Flame Spread | High Spread / Smoke |
| **Moisture Absorption** | Very Low | High (Swelling/Rot) |
| **Racking Strength** | High | Moderate |
| **Surface Finish** | Ready for Paint/Render | Requires Cladding/Batten |
| **VOC Emissions** | Zero | Potential Formaldehyde |

MgO is also chemically stable and does not support the growth of mold, mildew, or rot, even in humid environments.22 This makes it particularly suited to the Isle of Wight’s coastal climate, where airborne moisture and salt can quickly degrade organic materials such as timber.5 Unlike OSB, which can delaminate or swell when exposed to moisture during the build process, MgO panels remain dimensionally stable and structurally intact.5

## **Advanced Metal-Faced Architectural Panels for Minimal Maintenance**

For the user requiring minimal external cladding, pre-finished insulated metal panels (IMPs) provide a high-performance alternative to traditional construction. Manufacturers such as Kingspan and Joris Ide produce modular wall panels where the insulation core is factory-bonded between two structural skins of coated steel or aluminium.34 These systems offer an "all-in-one" solution where the structural skin also serves as the final exterior finish.21

## **Kingspan QuadCore AWP (Architectural Wall Panels)**

The QuadCore AWP system is designed for high-performance envelopes where aesthetic flexibility and speed of installation are paramount.18 These panels use a secret-fix interlocking joint that hides all fasteners within the joint of the panel, creating a clean, architectural finish with minimal effort.21

1. **Thermal Efficiency**: The QuadCore insulation core achieves an $R$-value of 8.0 per inch, which is roughly twice the performance of mineral fiber insulation.20 A $150 mm$ panel thickness achieves a $U$-value of $0.12 W/m^2K$, which is ideal for meeting Passivhaus fabric targets without excessive wall depth.18  
2. **Fire Performance**: While the PIR or QuadCore cores are technically combustible, they are classified as Euroclass B-s1,d0, indicating very limited contribution to fire and zero flaming droplets.21 For high-risk applications, mineral wool core variants like Kingspan’s K-Roc provide an A1 non-combustible rating.40  
3. **Aesthetics and Minimal Cladding**: The panels are available in various profiles, including Micro-rib, EuroBox, Flat, and Plank.18 These profiles can mimic the look of high-end zinc or timber cladding without the associated maintenance costs.35

## **Coastal Resilience and Finishing Systems**

The Isle of Wight’s proximity to the sea necessitates finishing systems that can withstand salt spray and high UV exposure. Kingspan’s Spectrum and Altaris coating systems are specifically engineered for coastal environments, offering warranties of up to 40 years.42 These coatings use metal alloy substrates that provide maximum resistance to corrosion on scratches and cut edges, ensuring that the garden room maintains its aesthetic integrity for decades.42

| Coating System | Durability Profile | Coastal Zone Suitability | Warranty |
| :---- | :---- | :---- | :---- |
| **Kingspan XL Forté** | High-build plastisol | Moderate | 25-30 Years |
| **Kingspan Spectrum** | Smooth polyurethane | High (Within 1km of coast) | Up to 40 Years |
| **PVDF** | Chemical/UV resistant | High | 25 Years |
| **Anodised Aluminium** | Natural oxide layer | Exceptional | 40+ Years |

## **Insulated Concrete Formwork (ICF) as a Heavyweight Alternative**

While SIPs and metal panels are lightweight modular solutions, Insulated Concrete Formwork (ICF) provides a heavyweight modular alternative that excels in thermal mass and acoustic insulation.3 ICF consists of interlocking blocks or panels of Expanded Polystyrene (EPS) or Neopor that are stacked on-site and filled with reinforced concrete.23

## **Thermal Mass and Passivhaus Synergy**

One of the challenges of lightweight construction (like timber or standard SIPs) is the lack of thermal mass, which can lead to overheating in the summer months if solar gain is not carefully controlled.16 ICF solves this by integrating the thermal mass of the concrete into the insulated envelope.3 The concrete core absorbs solar energy during the day and releases it at night, creating a "thermal flywheel" that stabilizes internal temperatures.3 This is particularly beneficial for the garden room context, where occupants may not want to manage complex shading or active cooling systems.16

## **Acoustic Performance and Privacy**

A garden room used as a professional office or studio requires high levels of acoustic insulation.43 The monolithic concrete core of an ICF wall provides superior sound attenuation compared to lightweight framing.3 A standard ICF wall can achieve a sound reduction index ($R\_w$) of over $50 dB$, effectively silencing the external garden environment and providing a tranquil internal space.32

## **Structural Fire Safety of ICF**

ICF is arguably the most fire-resistant modular strategy available. The concrete core is inherently non-combustible and can withstand intense heat for over four hours without losing structural integrity.3 Even though the EPS forms are technically combustible, they are manufactured with flame retardants that cause the foam to melt away from heat rather than ignite, leaving the concrete core intact as a fire barrier.3

| Property | ICF Performance | Timber Performance |
| :---- | :---- | :---- |
| **Fire Rating** | 2-4 Hours (ASTM E119) | 30-60 Minutes |
| **Acoustic Reduction** | $R\_w \> 50 dB$ | $R\_w \\approx 30-35 dB$ |
| **Thermal Mass** | High | Very Low |
| **Wall Thickness** | $250-300 mm$ | $150-200 mm$ |
| **Site Waste** | Minimal (Precision Forms) | High (Offcuts) |

## **Fire Safety Engineering and Boundary Wall Compliance**

A primary constraint for garden room construction in the UK is the proximity to property boundaries. Building Regulations (Part B) mandate that external walls within one meter of a boundary must provide a minimum of one-hour fire resistance from both sides to prevent fire spread.13 Traditional timber frames often require expensive and thick fire-rated cladding boards to meet this requirement.13

## **The Role of A1-Rated Modular Systems**

Transitioning to A1-rated modular systems like MgO SIPs or Mineral Wool-cored metal panels eliminates the need for remedial fire-cladding.4 For example, Dragonboard MgO SIPs have achieved up to four hours of fire resistance in load-bearing tests, far exceeding the regulatory requirements for domestic outbuildings.29 This simplifies the construction process and allows for a thinner wall profile, maximizing the usable internal space of the garden room.2

## **Smoke and Toxicity Management**

In a fire event, the primary cause of death is often smoke inhalation rather than the flames themselves.32 Inorganic modular materials like MgO and mineral wool are particularly safe in this regard, as they do not produce toxic smoke or flaming droplets when exposed to extreme temperatures.25 Kingspan’s QuadCore insulation, while organic, is engineered to produce up to 85% less smoke than traditional PUR or PIR cores, providing a middle ground for projects where metallic finishes are preferred over mineral boards.20

## **Minimal External Cladding: Integrated and Thin-Coat Solutions**

The user's requirement for minimal external cladding is a significant driver in material selection. Conventional builds require a complex assembly of membranes, battens, and cladding panels (such as Western Red Cedar or Larch), which are not only labour-intensive to install but require ongoing maintenance to prevent weathering and decay.13

## **Direct-Applied Render Systems**

MgO boards act as a superior render carrier compared to timber or cement-particle boards.26 Because MgO is dimensionally stable and does not expand or contract with moisture, thin-coat silicone or mineral renders can be applied directly to the board's surface.5 These render systems are self-coloured and ultra-violet (UV) resistant, meaning they never require painting and provide a seamless, contemporary finish that is both impact-resistant and breathable.49

## **Pre-Finished Composite and Metal Panels**

As discussed, pre-finished metal panels like those from Kingspan or Joris Ide remove the need for cladding entirely.35 For a more "organic" aesthetic with modular speed, composite wood-polymer cladding can be factory-applied to modular units.58 However, for the Isle of Wight context, the most durable "cladding-free" solution is the use of through-coloured mineral boards or pre-coated aluminium panels.48

## **Brick Slip Systems for Modular Envelopes**

Where a traditional aesthetic is required without the weight of full masonry, modular brick slip systems (e.g., Wetherby’s TotalWall or BrickBoard) allow real clay brick tiles to be adhesively bonded to a non-combustible modular backing board.49 These systems provide the durability and visual appeal of brickwork with the rapid installation and thermal efficiency of a SIP or steel-frame system.49

| Minimal Cladding Option | Material Composition | Maintenance Requirement | Fire Rating |
| :---- | :---- | :---- | :---- |
| **Direct Silicone Render** | Silicone-based thin coat | Zero (Self-Cleaning) | A2-s1,d0 |
| **Pre-Finished Metal** | Coated Steel/Aluminium | Periodic Wash | B-s1,d0 to A1 |
| **Through-Coloured MgO** | Mineral pigment in board | Zero | A1 |
| **Brick Slip System** | Clay slip on mineral board | Zero | A1 |
| **Fibre Cement Siding** | Cement/Cellulose | Low (Occasional wash) | A2 |

## **Manufacturing, Logistics, and the Isle of Wight Context**

The success of a modular garden room project on the Isle of Wight is heavily dependent on local supply chain logistics and the adaptability of the construction system to site constraints. Volumetric modularity, while fast, can be challenging on the island due to the cost of ferry transport for oversized units and the requirement for heavy-duty craning in residential areas.7

## **Local Manufacturing: MTL Ltd (Sandown, Isle of Wight)**

The presence of a local manufacturer, MTL Ltd (based in Sandown, PO36), provides a significant strategic advantage for island-based projects.4 MTL specializes in Magnesium Oxide (MgO) SIP panels and provides a fully integrated build system designed to meet Passivhaus standards.4 Sourcing from a local manufacturer eliminates the logistical complexities of the Solent crossing and allows for more frequent site support during the assembly phase.4

## **Site-Level Logistics and Ground Conditions**

The modular panels are typically delivered in manageable sizes (e.g., $1.2 m \\times 2.4 m$ or $1.2 m \\times 2.7 m$), allowing them to be hand-carried through narrow side gates or garden paths where crane access is impossible.4 Furthermore, the lightweight nature of SIPs allows for the use of low-impact foundation systems such as ground screws or concrete pad systems.10 Ground screws are particularly effective on the Isle of Wight as they can be installed quickly on sloped or uneven garden terrain without the need for extensive excavation or heavy concrete mixers.55

## **Technical Synthesis and Strategic Recommendations**

The transition from a timber frame to a high-performance modular strategy for the garden room context requires a synthesis of thermal physics, material science, and regulatory compliance. The evidence indicates that the optimal replacement for a timber frame is the Magnesium Oxide (MgO) Structural Insulated Panel (SIP) system.

## **Why MgO SIPs are the Superior Replacement**

MgO SIPs address the user’s requirements more comprehensively than any other modular system:

* **Passivhaus Performance**: By utilizing a high-density PUR or QuadCore insulation core, MgO SIPs achieve the $0.10$ to $0.15 U$-values necessary for Passivhaus, while the factory-precision joints and inorganic skins provide a superior airtightness layer compared to timber membranes.4  
* **Fire Safety**: The A1 non-combustible rating of the MgO skins provides a "boundary-ready" solution that is safer and more compliant than timber, without requiring additional fire-cladding.4  
* **Minimal Cladding**: The boards are moisture-stable and dimensionally consistent, allowing for the direct application of low-maintenance renders or high-performance paints, which significantly reduces the build depth and ongoing maintenance effort.5

## **Strategic Implementation Pathway**

For the implementation of the garden room described in the master plan, the following technical pathway is recommended:

1. **System Specification**: Utilize a $150 mm$ to $175 mm$ thick MgO SIP panel for walls and roof to achieve a $U$-value of $\\approx 0.15 W/m^2K$. For the floor, an insulated concrete raft or an 18mm tongue-and-groove MgO board over a SIP base is recommended to eliminate thermal bridging at the foundation level.4  
2. **Manufacturer Selection**: Prioritize local manufacturing through MTL Ltd in Sandown to minimize transport risks and support the Isle of Wight economy.4  
3. **Airtightness Detailing**: Use a high-performance spline system (such as the "Econex" connection) and Passivhaus-certified airtightness tapes on all internal panel joints to achieve $\\leq 0.6$ ACH.4  
4. **External Finish**: Apply a thin-coat silicone render directly to the MgO surface for a maintenance-free, contemporary finish that is durable in the coastal environment.49  
5. **Environmental Control**: Integrate a decentralized MVHR system to ensure constant fresh air and prevent internal humidity buildup in the highly airtight structure.9

By adopting this modular strategy, the garden room will evolve from a simple outbuilding into a high-performance, fire-safe, and durable architectural asset that fully realizes the potential of the Passivhaus standard in a modern, maintenance-free envelope.

#### **Works cited**

1. SIPs vs Timber Frame: Which Garden Room Construction Method Wins?, accessed March 16, 2026, [https://www.oecogardenrooms.co.uk/blog/sips-vs-timber-frame-which-garden-room-construction-method-wins.html](https://www.oecogardenrooms.co.uk/blog/sips-vs-timber-frame-which-garden-room-construction-method-wins.html)  
2. SIPs vs Timber Frame \- SIP Kits UK, accessed March 16, 2026, [https://www.sipkitsuk.com/information-centre/sips-vs-timber-frame/](https://www.sipkitsuk.com/information-centre/sips-vs-timber-frame/)  
3. Structural Insulated Panels (SIPs) Vs. Insulated Concrete Forms (ICFs) \- Fox Blocks, accessed March 16, 2026, [https://www.foxblocks.com/blog/sip-vs-icf](https://www.foxblocks.com/blog/sip-vs-icf)  
4. High-Quality MgO SIP Panels | MTL Ltd's Advanced Building Solutions, accessed March 16, 2026, [https://www.mtlsips.com/ourpanels](https://www.mtlsips.com/ourpanels)  
5. Why Use MgO SIP Panels, accessed March 16, 2026, [https://www.mtlsips.com/whyuse](https://www.mtlsips.com/whyuse)  
6. Guide to Modern Methods of Construction \- Partel, accessed March 16, 2026, [https://www.partel.com/blogs/news/guide-to-modern-methods-of-construction](https://www.partel.com/blogs/news/guide-to-modern-methods-of-construction)  
7. Modular Offsite Construction \- Rollalong, accessed March 16, 2026, [https://rollalong.co.uk/what-we-do/modular-construction/](https://rollalong.co.uk/what-we-do/modular-construction/)  
8. UK Modular Construction Benefits \- Why Go Modular?, accessed March 16, 2026, [https://www.go-modular.co.uk/why-go-modular](https://www.go-modular.co.uk/why-go-modular)  
9. Timber Frame vs Modular House \- Which Build Method is Best? \- Beattie Passivhaus, accessed March 16, 2026, [https://www.beattie.io/timber-frame-vs-modular-house/](https://www.beattie.io/timber-frame-vs-modular-house/)  
10. Our Building Process | Quality Prep A Room In The Garden, accessed March 16, 2026, [https://aroominthegarden.co.uk/how-we-build/](https://aroominthegarden.co.uk/how-we-build/)  
11. What are SIP Panels? Structural Insulated Panels Explained \- My Outhouse, accessed March 16, 2026, [https://myouthouse.co.uk/blog/what-are-sip-panels/](https://myouthouse.co.uk/blog/what-are-sip-panels/)  
12. SIP Kits UK: Structural Insulated Panels | Garden Room Kits, accessed March 16, 2026, [https://www.sipkitsuk.com/](https://www.sipkitsuk.com/)  
13. Structural Insulated Panels | Future SIPs, accessed March 16, 2026, [https://www.futuresips.co.uk/product/sip-panels/](https://www.futuresips.co.uk/product/sip-panels/)  
14. Understanding the Passivhaus Standard | Kingspan GB, accessed March 16, 2026, [https://www.kingspan.com/gb/en/knowledge-articles/understanding-the-passivhaus-standard/](https://www.kingspan.com/gb/en/knowledge-articles/understanding-the-passivhaus-standard/)  
15. Fully-insulated SIPs Garden Rooms & Offices | SipsEcoPanels, accessed March 16, 2026, [https://www.sipsecopanels.co.uk/sips-garden-rooms/](https://www.sipsecopanels.co.uk/sips-garden-rooms/)  
16. How to Build a Passivhaus, accessed March 16, 2026, [https://www.passivhaustrust.org.uk/UserFiles/File/Technical%20Papers/ROT/How%20to%20build%20a%20Passivhaus\_Chapters%201%20to%204(2).pdf](https://www.passivhaustrust.org.uk/UserFiles/File/Technical%20Papers/ROT/How%20to%20build%20a%20Passivhaus_Chapters%201%20to%204\(2\).pdf)  
17. Rules of Thumb \- Passivhaus Trust, accessed March 16, 2026, [https://www.passivhaustrust.org.uk/UserFiles/File/Technical%20Papers/ROT/01\_03\_2015\_Rules%20of%20Thumb%20Guide%20Chapter%201%20to%204%20compressed.pdf](https://www.passivhaustrust.org.uk/UserFiles/File/Technical%20Papers/ROT/01_03_2015_Rules%20of%20Thumb%20Guide%20Chapter%201%20to%204%20compressed.pdf)  
18. QuadCore® AWP Wall Panel Product Data Sheet \- Kingspan, accessed March 16, 2026, [https://www.kingspan.com/content/dam/kingspan/kip-west/wall-panels/quadcore-awp-wall-panel/kingspan-quadcore-awp-wall-panel-data-sheet-en-gb-ie.pdf](https://www.kingspan.com/content/dam/kingspan/kip-west/wall-panels/quadcore-awp-wall-panel/kingspan-quadcore-awp-wall-panel-data-sheet-en-gb-ie.pdf)  
19. SIP Panels & SIPs Building Kits UK | Future SIPs, accessed March 16, 2026, [https://www.futuresips.co.uk/](https://www.futuresips.co.uk/)  
20. QuadCore® Technology | Kingspan US, accessed March 16, 2026, [https://www.kingspan.com/us/en/business-groups/kingspan-insulated-panels/quadcore/](https://www.kingspan.com/us/en/business-groups/kingspan-insulated-panels/quadcore/)  
21. KS AWP QuadCore® Architectural Wall Panel Product Data Sheet \- Kingspan, accessed March 16, 2026, [https://www.kingspan.com/content/dam/kingspan/kip-ceer/ks-south-ceme/downloads-ceme/ks-awp-quadcore-wall-panel-product-data-sheet.pdf](https://www.kingspan.com/content/dam/kingspan/kip-ceer/ks-south-ceme/downloads-ceme/ks-awp-quadcore-wall-panel-product-data-sheet.pdf)  
22. MTL Ltd | Isle of Wight | MgO SIPS Building Systems | Energy-Efficient Construction |, accessed March 16, 2026, [https://www.mtlsips.com/](https://www.mtlsips.com/)  
23. SIPs vs ICF | Imagine Architecture \- Passive House Certified Tauranga, New Plymouth, accessed March 16, 2026, [https://www.imaginearchitecture.co.nz/post/sips-vs-icf-which-building-system-best-supports-passivhaus-design](https://www.imaginearchitecture.co.nz/post/sips-vs-icf-which-building-system-best-supports-passivhaus-design)  
24. Passivhaus Insulation and Airtightness: A Guide for UK Readers, accessed March 16, 2026, [https://www.buyinsulationonline.co.uk/blog/passivhaus-insulation-and-airtightness-a-guide-for-uk-readers](https://www.buyinsulationonline.co.uk/blog/passivhaus-insulation-and-airtightness-a-guide-for-uk-readers)  
25. 7 Best Fire Resistant Wall Panels That Meet Building Codes in 2025 \- MgO boards, accessed March 16, 2026, [https://www.magmatrixboards.com/post/7-best-fire-resistant-wall-panels-that-meet-building-codes-in-2025](https://www.magmatrixboards.com/post/7-best-fire-resistant-wall-panels-that-meet-building-codes-in-2025)  
26. MGO Board \- Magnesium Oxide Panels \- UK Plywood Suppliers, accessed March 16, 2026, [https://www.spp.co.uk/mgo-magnesium-oxide-panels](https://www.spp.co.uk/mgo-magnesium-oxide-panels)  
27. MgO Board MagPanel® | Versatile Building Products | Ambient®, accessed March 16, 2026, [https://www.ambientbp.com/mgo-magnesium-oxide-boards-magboard.php](https://www.ambientbp.com/mgo-magnesium-oxide-boards-magboard.php)  
28. Magnesium Oxide Board for UK Construction, accessed March 16, 2026, [https://magnesium-oxide-board.com/mgo-board-uk/](https://magnesium-oxide-board.com/mgo-board-uk/)  
29. Structural Insulated Panel | SIPs Eco Panels for Buildings \- Dragonboard, accessed March 16, 2026, [https://dragonboard.co.uk/structural-insulated-panel/](https://dragonboard.co.uk/structural-insulated-panel/)  
30. Magnesium Oxide Boards, MgO Panels & Wallboards, accessed March 16, 2026, [https://www.magpanelmgo.com/magnesium-oxide-boards](https://www.magpanelmgo.com/magnesium-oxide-boards)  
31. Magply Magnesium Oxysulfate (MGO) Boards 12mm x 2400mm x 1200mm, accessed March 16, 2026, [https://www.ecomerchant.co.uk/magply-magnesium-oxysulfate-mgo-boards.html](https://www.ecomerchant.co.uk/magply-magnesium-oxysulfate-mgo-boards.html)  
32. Fire-certified Modular Buildings For Hire And Sale \- Pickerings, accessed March 16, 2026, [https://www.pickeringshire.co.uk/products/fire-safety-building-solutions/fire-certified-modular-buildings](https://www.pickeringshire.co.uk/products/fire-safety-building-solutions/fire-certified-modular-buildings)  
33. MgO Panel Benefits, accessed March 16, 2026, [https://usmgo.co/benefits/](https://usmgo.co/benefits/)  
34. QuadCore® KS Series | Kingspan US, accessed March 16, 2026, [https://www.kingspan.com/us/en/products/insulated-panel-systems/wall-panel-systems/quadcore-ks-series/](https://www.kingspan.com/us/en/products/insulated-panel-systems/wall-panel-systems/quadcore-ks-series/)  
35. QuadCore AWP Wall Panel | Kingspan GB, accessed March 16, 2026, [https://www.kingspan.com/gb/en/products/insulated-panels/wall-panels/quadcore-awp-wall-panel/](https://www.kingspan.com/gb/en/products/insulated-panels/wall-panels/quadcore-awp-wall-panel/)  
36. Insulated panels | Joris Ide United Kingdom, accessed March 16, 2026, [https://www.joriside.com/en-gb/product-overview-joris-ide/product-overview/insulated-panels](https://www.joriside.com/en-gb/product-overview-joris-ide/product-overview/insulated-panels)  
37. Insulated Panels | Kingspan GB, accessed March 16, 2026, [https://www.kingspan.com/gb/en/products/insulated-panels/](https://www.kingspan.com/gb/en/products/insulated-panels/)  
38. Kingspan Insulated Metal Panels: Superior Thermal Performance for Energy-Efficient Buildings, accessed March 16, 2026, [https://www.kingspan.com/us/en/knowledge-articles/insulated-metal-panels-thermal-performance/](https://www.kingspan.com/us/en/knowledge-articles/insulated-metal-panels-thermal-performance/)  
39. Insulated Metal Panels | Kingspan US, accessed March 16, 2026, [https://www.kingspan.com/us/en/products/insulated-panel-systems/](https://www.kingspan.com/us/en/products/insulated-panel-systems/)  
40. Fire Safety | Kingspan GB, accessed March 16, 2026, [https://www.kingspan.com/gb/en/Fire-safety/](https://www.kingspan.com/gb/en/Fire-safety/)  
41. Fire Performance of Insulated Panels | Kingspan GB, accessed March 16, 2026, [https://www.kingspan.com/gb/en/knowledge-articles/fire-performance-of-insulated-panels/](https://www.kingspan.com/gb/en/knowledge-articles/fire-performance-of-insulated-panels/)  
42. Colours & Coatings | Kingspan, accessed March 16, 2026, [https://www.kingspan.com/content/dam/kingspan/kip-west/kingspan-colours-and-coatings-brochure-en-gb-ie.pdf](https://www.kingspan.com/content/dam/kingspan/kip-west/kingspan-colours-and-coatings-brochure-en-gb-ie.pdf)  
43. What is the difference between a structural insulated panel (SIP) and an insulated concrete forms (ICF)? | TruTeam, accessed March 16, 2026, [https://www.truteam.com/education/what-is-the-difference-between-a-structural-insulated-panel-sip-and-an-insulated-concrete-forms-icf/](https://www.truteam.com/education/what-is-the-difference-between-a-structural-insulated-panel-sip-and-an-insulated-concrete-forms-icf/)  
44. Comparing SIP Homes vs. ICF Homes | Mighty Small Homes, accessed March 16, 2026, [https://www.mightysmallhomes.com/blog/sips-vs-icf-house-kits/](https://www.mightysmallhomes.com/blog/sips-vs-icf-house-kits/)  
45. In This Ring: SIPs VS ICFs \- Enercept, accessed March 16, 2026, [https://enercept.com/in-this-ring-sips-vs-icfs/](https://enercept.com/in-this-ring-sips-vs-icfs/)  
46. Fireline Wall Systems | Modular Fireproof and Fire Walls, accessed March 16, 2026, [https://alliedmodular.com/products/fireline-wall-system/](https://alliedmodular.com/products/fireline-wall-system/)  
47. When it comes to fire safety, just how safe is modular construction? \- Elite Systems GB, accessed March 16, 2026, [https://www.elitesystemsgb.co.uk/blog/modular-construction-fire-safety](https://www.elitesystemsgb.co.uk/blog/modular-construction-fire-safety)  
48. Luxe Clad A1® FS \- Insulated Flat Spandrel Panels \- NBS Source, accessed March 16, 2026, [https://source.thenbs.com/product/luxe-clad-a1-fs-insulated-flat-spandrel-panels/6EcJeSoybR7iJgCaNHE3kD/bz4kHA3qrK1sAZm8UKZ94Y](https://source.thenbs.com/product/luxe-clad-a1-fs-insulated-flat-spandrel-panels/6EcJeSoybR7iJgCaNHE3kD/bz4kHA3qrK1sAZm8UKZ94Y)  
49. A1 Non-Combustible EWI Systems \- Wetherby Wall Systems Ltd, accessed March 16, 2026, [https://www.wall-systems.co.uk/systems-solutions/a1-non-combustible-ewi-system/](https://www.wall-systems.co.uk/systems-solutions/a1-non-combustible-ewi-system/)  
50. DragonBoard: Home Page, accessed March 16, 2026, [https://dragonboard.com/](https://dragonboard.com/)  
51. Structural insulated panels (SIPs) \- Hemsec, accessed March 16, 2026, [https://hemsec.com/products/structural-insulated-panels-sips/](https://hemsec.com/products/structural-insulated-panels-sips/)  
52. External Wall Panels | Strong External Wall Insulation Board, accessed March 16, 2026, [https://dragonboard.co.uk/service/external-wall-panels/](https://dragonboard.co.uk/service/external-wall-panels/)  
53. A1 Cladding, A1 & A2 Rated Rainscreen Cladding \- Sotech Optima, accessed March 16, 2026, [https://sotech-optima.co.uk/a1-cladding-2-0/](https://sotech-optima.co.uk/a1-cladding-2-0/)  
54. Garden Room & Studio Specifications \- gyd modular, accessed March 16, 2026, [https://gydmodular.co.uk/garden-room-specifications/](https://gydmodular.co.uk/garden-room-specifications/)  
55. Premium Garden Room Build Specification | Hideaway Garden Rooms Surrey, accessed March 16, 2026, [https://www.hideawaygardenrooms.com/build-specification](https://www.hideawaygardenrooms.com/build-specification)  
56. TotalWall System \- 2 Hour Fire Test \- Wetherby Wall Systems Ltd, accessed March 16, 2026, [https://www.wall-systems.co.uk/systems-solutions/totalwall-system/](https://www.wall-systems.co.uk/systems-solutions/totalwall-system/)  
57. SOQEL A2 \- Fully Fire-Tested EWI System for below-DPC & Base Areas, accessed March 16, 2026, [https://www.wall-systems.co.uk/soqel/](https://www.wall-systems.co.uk/soqel/)  
58. Garden Studios Southampton | Garden Rooms, accessed March 16, 2026, [https://www.southampton-gardenrooms.co.uk/garden-studios-southampton/](https://www.southampton-gardenrooms.co.uk/garden-studios-southampton/)  
59. Garden Rooms and Studios from Composite Garden Buildings, accessed March 16, 2026, [https://www.compositegardenbuildings.co.uk/](https://www.compositegardenbuildings.co.uk/)  
60. ULT 3 Insulated Spandrel Panels \- Metalline, accessed March 16, 2026, [https://www.metalline.co.uk/products/ultima-3/](https://www.metalline.co.uk/products/ultima-3/)  
61. Aluminium Insulated Panels | FINSPAN-A1 \- Finish Facades, accessed March 16, 2026, [https://www.finishfacades.co.uk/cwct-rainscreen-systems/aluminium-spandrel-panel/](https://www.finishfacades.co.uk/cwct-rainscreen-systems/aluminium-spandrel-panel/)  
62. Brick Slip Systems | Pilgrim Construction Solutions, accessed March 16, 2026, [https://pilgrimcs.co.uk/brick-slip-systems/](https://pilgrimcs.co.uk/brick-slip-systems/)  
63. Contact | SIPS, accessed March 16, 2026, [https://www.mtlsips.com/blank-2](https://www.mtlsips.com/blank-2)
