wisogetnid/garden-room/research/future-homes-standard-research.md

# **Technical Analysis of the UK Future Homes Standard and its Strategic Application for High-Performance Garden Workshops**

The landscape of British residential construction is currently undergoing its most profound transformation since the introduction of the first building regulations, driven by the statutory requirement for the United Kingdom to achieve Net Zero carbon emissions by 2050\. At the heart of this transition is the Future Homes Standard (FHS), a rigorous regulatory framework scheduled for full implementation in 2025, with a transition period extending into 2027 and 2028\.1 The FHS is not merely a set of incremental improvements to existing codes; it represents a paradigm shift toward a "Zero-Carbon Ready" built environment where structures are designed to be decoupled from fossil fuels and optimized for high fabric efficiency.1 For specialized projects such as the proposed 20-square-meter garden workshop in Cowes, the FHS provides both a mandatory regulatory backdrop and a voluntary technical blueprint for achieving Passivhaus-level performance.4 This project, characterized by its focus on hand-tool woodworking and the critical need for humidity control to protect high-carbon steel tools, requires a synthesis of advanced building science, logistical ingenuity due to restricted site access, and strict adherence to fire safety protocols mandated for boundary constructions.4

## **The Regulatory Evolution and Strategic Timeline of the Future Homes Standard**

The genesis of the Future Homes Standard lies in the government’s commitment to reducing carbon emissions from new homes by 75-80% compared to the 2013 standards.2 This objective is achieved through a multi-faceted revision of the Approved Documents, specifically Part L (Conservation of Fuel and Power), Part F (Ventilation), and the newly introduced Part O (Overheating).7 The implementation timeline is critical for developers and DIY builders alike, as it dictates the shifting legal requirements for energy performance and heating technology.

| Milestone Date | Regulatory Action and Impact | Significance for Outbuildings |
| :---- | :---- | :---- |
| Autumn 2025 | Publication of final FHS regulations.1 | Establishes the definitive technical targets for fabric and air quality. |
| June 2025 | Solar PV becomes a functional requirement for many new builds.2 | Impacts the design of workshop roofs for future renewable integration. |
| December 2026 | FHS regulations become statutory law.1 | Mandatory compliance for any project without existing permits. |
| December 2027 | End of transition period.1 | All new residential-class structures must meet FHS. |
| 2028 onwards | Requirement for low-carbon heating plans at build outset.1 | Ensures long-term decoupling from the gas grid. |

While the FHS primary focus is on dwellings, the technical updates to Part L and Part F have immediate implications for outbuildings larger than 15 square meters, especially those intended for regular occupation or specialized use.6 The Cowes workshop, at 20 square meters, sits within a regulatory "middle ground" where it must navigate the intersection of Permitted Development rights and mandatory Building Control for aspects such as electrical safety (Part P) and fire protection (Part B) when sited near a boundary.8

## **Structural Integrity and Logistical Optimization in Restricted Sites**

The workshop project in Cowes faces significant logistical hurdles, specifically a 30-meter transit path with a width limited to a standard wheelbarrow.4 In the context of the Future Homes Standard, which emphasizes high-performance building fabric, the choice of construction material is dictated not only by thermal efficiency but by the "transportability" of the components. Traditional masonry construction is rendered impractical by the sheer volume and weight of materials required, which would lead to hundreds of man-hours of manual transit.10  
Structural Insulated Panels (SIPs) emerge as the optimal solution for this context. SIPs are precision-engineered off-site, consisting of an insulating foam core—typically Expanded Polystyrene (EPS) or Extruded Polystyrene (XPS)—sandwiched between two layers of Oriented Strand Board (OSB).12 The lightweight nature of these panels (available in thicknesses such as 142mm or 172mm) allows them to be moved by hand or wheelbarrow through narrow passages.10 Furthermore, SIPs align perfectly with the FHS goal of "Zero-Carbon Ready" homes because they are inherently more airtight than traditional timber frames and minimize thermal bridging due to the continuous nature of the insulation core.11  
The structural performance of SIPs is characterized by their composite action. Under loading, the OSB skins act as the flange of an I-beam, while the foam core acts as the web, providing exceptional strength-to-weight ratios.12 For a DIY builder in Cowes, using SIPs reduces on-site construction time and minimizes waste, both of which are key tenets of sustainable modern construction.10 The panels are joined using timber splines or insulated splines, which maintain the continuity of the thermal envelope—a requirement that becomes increasingly difficult to meet as the FHS pushes toward U-values as low as 0.11 $W/m^2K$ for roofs and 0.15 $W/m^2K$ for walls.2

## **Advanced Thermal Engineering and Material Science**

The Cowes workshop aims for a performance standard similar to "Passive House" (Passivhaus), which is significantly more rigorous than even the upcoming Future Homes Standard.4 While the FHS focuses on carbon reduction and "zero-carbon readiness," Passivhaus focuses on absolute energy demand, limiting annual space heating to 15 $kWh/m^2/year$.5 To bridge the gap between these standards in a small 20-square-meter footprint, the builder must employ advanced insulation materials that offer high R-values without excessive thickness.

| Material Type | Thermal Conductivity (λ) | Suitability for Restricted Access | Fire Performance |
| :---- | :---- | :---- | :---- |
| Polyisocyanurate (PIR) | 0.022 $W/mK$ 17 | High; lightweight boards. | Class E/F (Combustible).17 |
| Wood Fibre Board | 0.038 $W/mK$ 18 | Medium; bulky but sustainable. | Better summer heat delay.18 |
| Aerogel | 0.015 $W/mK$ 17 | Very High; ultra-thin blankets. | Class A1 (Non-combustible).19 |
| Vacuum Insulation Panels (VIPs) | 0.007 $W/mK$ 17 | Low; fragile, cannot be cut. | Highest performance per mm.17 |

For the Cowes project, where the boundary height restriction of 2.5 meters limits the total depth of the roof and floor build-up, material selection becomes a game of millimeters.4 A traditional "cold roof" or thick mineral wool assembly might consume 300mm of vertical space, whereas a high-performance SIP or PIR-based assembly could achieve superior U-values in half that thickness.10 Aerogel blankets, although expensive (costing 8-10 times more than rigid foam), could be strategically utilized in thermal bridge junctions, such as window reveals and door frames, to ensure the continuity of the thermal envelope without compromising the clear opening of the North-facing French patio doors.4

## **Airtightness and the Science of Humidity Control**

A central requirement for the Cowes workshop is the control of humidity to prevent the corrosion of hand tools.4 This is not merely a comfort issue but a material science challenge. High-carbon steel, often found in high-quality chisels and planes, is highly susceptible to oxidation when the relative humidity (RH) exceeds 60% or when rapid temperature changes lead to condensation on metallic surfaces.23 The FHS 2025 standard moves the airtightness target from the current 8 $m^3/(h \\cdot m^2)$ toward a more stringent 3 $m^3/(h \\cdot m^2)$ at 50 Pa, which is a necessary step toward the 0.6 ACH (Air Changes per Hour) required by Passivhaus.2  
Achieving this level of airtightness in a DIY garden room requires a "Red Line" strategy: a single, continuous air barrier must encompass the entire heated volume.26 For the Cowes builder, this involves meticulously taping the joints of the SIP panels and using specialized EPDM grommets for any electrical or ventilation penetrations.22 The OSB skins of the SIPs act as a primary air barrier, but their performance is only as good as the seal at the junctions.12  
The relationship between airtightness and humidity is managed through the vapor control layer (VCL). In a workshop environment, where moisture is generated primarily through occupant respiration and the hygroscopic release from wood stocks, the VCL must be positioned on the "warm side" of the insulation to prevent water vapor from diffusing into the structural elements and condensing.26 This is particularly critical in the Isle of Wight's maritime climate, where outdoor humidity is frequently high. An airtight building envelope allows for a controlled internal environment where the humidity can be actively managed by mechanical systems, rather than being subject to the unpredictable infiltration of moist outdoor air through gaps and cracks.7

## **Mechanical Ventilation with Heat Recovery (MVHR) and Air Quality**

As buildings become increasingly airtight under the FHS and Passivhaus standards, natural "leakage" ventilation is replaced by Mechanical Ventilation with Heat Recovery (MVHR).2 In the context of a 20-square-meter wood workshop, MVHR is not a luxury but a functional necessity. The system extracts stale, moisture-laden air and replaces it with filtered fresh air, recovering up to 90% of the heat from the exhaust stream to pre-warm the intake.5  
For the Cowes project, the integration of MVHR must account for wood dust management. While the builder uses primarily hand tools, fine particulates are still generated during sanding or finishing. Standard domestic MVHR units are not designed for industrial dust loads; therefore, a multi-stage filtration strategy is required.30

1. **ISO 16890 Filtration Standards:** The system should utilize filters graded under the ISO 16890 standard, which replaced the old EN 779 classes.31  
2. **Filter Class Selection:** A G4 (coarse) filter should be used as a sacrificial pre-filter on the extract side to protect the heat exchanger from wood fibers, while an F7 (fine/pollen) filter on the intake side ensures that the internal air is free of external pollutants and allergens.30  
3. **Pressure Drop ($\\Delta P$):** Higher grade filters like F7 or HEPA introduce more resistance. The MVHR unit must be powerful enough to overcome this pressure drop without excessive noise or energy consumption, which is a common failure point in "cheap" ventilation systems.30

In a woodworking environment, the MVHR system provides the baseline ventilation required by Part F, but it should be supplemented by an ambient air cleaner (ambient filter) that circulates the workshop air through a fine filter (e.g., 1-micron or HEPA) approximately 6 times per hour to capture airborne dust that escapes source extraction.34 This combination ensures that the air quality meets health standards while maintaining the stable relative humidity (40-60%) necessary for both tool preservation and the dimensional stability of the wood projects.23

## **Environmental Stabilization and Corrosion Prevention**

The preservation of high-value hand tools in the Cowes workshop requires a sophisticated understanding of the interaction between temperature, humidity, and metallic surfaces. Corrosion on carbon steel occurs when the surface temperature drops below the dew point of the surrounding air, leading to the formation of a liquid water film.25 The FHS approach of super-insulation and airtightness creates a "thermal fly-wheel" effect, where internal temperatures remain stable even as outdoor temperatures fluctuate, significantly reducing the risk of dew point condensation.3  
To supplement the building fabric, several proactive measures can be integrated into the workshop design:

* **Low-Carbon Heating:** The FHS effectively mandates heat pumps as the primary heat source.1 For a small workshop, a small air-to-air heat pump (air conditioning unit) provides high efficiency ($\\text{COP} \> 3.0$) and serves as a powerful dehumidifier during the damp Isle of Wight winters.38  
* **Radiant Infrared Heating:** Unlike convective heaters that warm the air, infrared (IR) panels warm the objects (and tools) directly. Maintaining the tool surfaces at a slightly higher temperature than the air is an effective strategy to prevent condensation.40  
* **Corrosion Inhibitors:** For tools stored in cabinets, the use of Vapor Phase Corrosion Inhibitors (VpCI) or anti-corrosion emitters can provide a secondary layer of protection by forming a monomolecular protective layer on the metal.25

The workshop's North/North-East orientation for the French doors is strategically advantageous for a woodworker. It provides consistent, diffuse light—minimizing the harsh shadows and glare of direct Southern sun—while also reducing the risk of summer overheating, a concern addressed by Part O of the building regulations.4 This orientation, combined with triple glazing (U-values $\\approx$ 0.8 $W/m^2K$), ensures that the largest thermal aperture in the building does not become a major source of heat loss or uncontrolled solar gain.3

## **Renewables and the "Zero-Carbon Ready" Mandate**

The Future Homes Standard explicitly aims for "Zero-Carbon Ready" homes, meaning they are designed to operate without carbon emissions as the UK electricity grid continues to decarbonize.1 For the Cowes workshop, this involves the future integration of solar photovoltaic (PV) panels and battery storage.4  
The FHS 2025 notional building specification includes a solar PV array, and recent government consultations have proposed making solar panels a functional requirement for many new structures.2 For a 20-square-meter roof, a well-designed PV array could generate between 2,000 and 3,000 $kWh$ per year. Since the primary usage pattern of the workshop is evenings and weekends, a battery storage system is essential to bridge the gap between daytime generation and evening consumption.4 This configuration not only reduces the carbon footprint to nearly zero but also provides energy security and protection against fluctuating electricity prices.1

## **Fire Safety and Boundary Construction Constraints**

A critical constraint for the Cowes workshop is its location bordering neighboring fences to the south and west.4 Under UK Building Regulations, specifically Part B (Fire Safety), outbuildings between 15 and 30 square meters that are within 1 meter of a boundary must be constructed "substantially of non-combustible materials".46 This regulation is designed to prevent "boundary creep," where a fire in one garden room could easily spread to a neighbor's property or fence.  
The choice of cladding is therefore heavily restricted. Traditional timber cladding, such as untreated cedar or larch, typically carries a Euroclass D or E fire rating, which is insufficient for boundary construction.47 To comply with the regulations and ensure safety, the builder has two primary options:

1. **Fiber-Cement Cladding:** Products like Cedral Click are manufactured from a mixture of cement, sand, and cellulose fibers. They offer an A2-s1, d0 fire rating (limited combustibility) and are highly resistant to rot, insects, and decay.46 This material mimics the aesthetic of painted timber but satisfies the "non-combustible" requirement of the planning portal and building control.47  
2. **Fire-Treated Timber:** Natural timber can be vacuum-pressure impregnated with fire retardants to achieve a Euroclass B rating. While this allows for a "natural" wood look, it is more expensive and requires periodic maintenance to ensure the fire-retardant properties are not leached out by the weather.47

Given the DIY nature of the project and the restricted access, fiber-cement boards are generally preferred as they are pre-finished, dimensionally stable, and provide a 50-year life expectancy with minimal upkeep.46

## **Foundation Engineering for Restricted Access and Flush Thresholds**

The intention to keep the interior floor level with the exterior patio presents a complex foundation challenge, particularly when managing soil moisture and thermal bridging.4 In a Passivhaus-style build, the floor insulation must be continuous with the wall insulation to eliminate the "cold bridge" at the floor-to-wall junction.5

| Foundation Type | Logistical Impact (Restricted Access) | Suitability for Flush Patio | Risk Factors |
| :---- | :---- | :---- | :---- |
| Concrete Slab | Very Low; requires 2-3 $m^3$ of manual transit. | High; easy to set height. | High thermal mass; hard to insulate perfectly.51 |
| Ground Screws | Very High; lightweight, manual install. | Medium; requires timber sub-frame. | No curing time; eco-friendly.51 |
| Paving Slabs | High; modular and easy to move. | High; adjustable. | Prone to subsidence if not on deep hardcore.52 |

For the Cowes workshop, ground screws offer a highly attractive alternative to traditional concrete.51 They can be installed by a single person or a small team without heavy machinery, and they provide a stable base for a timber or SIP sub-floor.51 To achieve a flush threshold with the patio, the ground screws are driven to a precise depth, allowing the top of the structural floor (including insulation and finish) to align perfectly with the exterior surface. This approach also allows for an "air gap" beneath the structure, preventing rising damp and providing ventilation to the underside of the floor joists—a critical factor in the longevity of any timber-based outbuilding.53

## **The Physics of Heat Transfer and Moisture Content in Woodworking**

A deep research into the FHS requires an analysis of the underlying physics that govern the workshop's performance. For a 20sqm structure, the total heat loss can be calculated using the simplified formula:

$$Q \= (U\_{fabric} \\cdot A \+ \\rho \\cdot c\_p \\cdot \\dot{V}) \\cdot \\Delta T$$  
Where $U\_{fabric}$ is the average U-value of the walls, roof, and floor, $A$ is the total surface area, $\\rho$ and $c\_p$ are the density and specific heat capacity of air, and $\\dot{V}$ is the ventilation rate.5 In an FHS-compliant build, the $U \\cdot A$ component is minimized through super-insulation, and the ventilation loss is minimized through the heat recovery efficiency of the MVHR unit.5  
For the woodworker, the "Equilibrium Moisture Content" (EMC) of the timber is the most important metric. Wood's MC is a function of the ambient temperature and relative humidity. At 20°C and 50% RH, wood will reach an EMC of approximately 9%.24 If the RH fluctuates between 30% and 70%, the wood will constantly "breathe," leading to dimensional changes that can ruin precision joinery.23

$$MC \\approx f(T, RH)$$  
By achieving the airtightness and thermal stability mandated by the FHS and Passivhaus, the Cowes builder creates a "climate-controlled" envelope where the EMC of the wood stock and the dew point of the tool surfaces are under total control.24 This proactive engineering is the key to a successful workshop that serves its primary purpose: the creation of lasting wood products and the protection of the precision tools used to make them.55

## **Conclusions and Expert Recommendations for the Cowes Workshop**

The integration of the Future Homes Standard into the Cowes workshop project provides a rigorous framework for success. While the FHS sets the baseline for carbon reduction and energy efficiency, the project's ambition to reach Passivhaus levels of performance ensures that the critical functional requirements of a wood workshop—humidity control, air quality, and thermal comfort—are met with a high degree of confidence.  
The restricted site access dictates a lightweight, modular approach, making SIPs and ground screws the most logical structural choices. The proximity to boundaries necessitates the use of fiber-cement cladding to satisfy Part B fire safety regulations. Finally, the specialized nature of hand-tool woodworking requires a sophisticated mechanical ventilation and environmental control strategy that goes beyond standard domestic requirements, incorporating high-level filtration and active humidity management.  
By treating the garden room not as a "shed" but as a precision-engineered piece of the UK’s future housing stock, the builder in Cowes will create a facility that is not only "Zero-Carbon Ready" but is optimized for the craftsmanship it is intended to house. The alignment with the FHS ensures that the building is future-proofed against rising energy costs, changing climate conditions, and evolving national standards, setting a benchmark for high-performance DIY outbuildings in the UK.

#### **Works cited**

1. Future Homes Standard & Building Regulations & Changes 2025 ..., accessed March 8, 2026, [https://kensa.co.uk/housing-developments/future-homes-standard](https://kensa.co.uk/housing-developments/future-homes-standard)  
2. Future Homes Standard — Complete Guide | HEM Guide, accessed March 8, 2026, [https://home-energy-model.co.uk/future-homes-standard/](https://home-energy-model.co.uk/future-homes-standard/)  
3. The Future Homes Standard 2025 explained \- Norrsken, accessed March 8, 2026, [https://www.norrsken.co.uk/blogs/regulations/the-future-homes-standard-2025-explained](https://www.norrsken.co.uk/blogs/regulations/the-future-homes-standard-2025-explained)  
4. workshop-research-context.md  
5. Building Certification PHI \- Passive House Institute, accessed March 8, 2026, [https://passivehouse.com/en/home/building-certification/](https://passivehouse.com/en/home/building-certification/)  
6. Garden Room Building Regulations for UK Homes in 2025, accessed March 8, 2026, [https://www.gardenroomsolutionsltd.co.uk/news/garden-room-building-regulations-for-uk-homes-in-2025/](https://www.gardenroomsolutionsltd.co.uk/news/garden-room-building-regulations-for-uk-homes-in-2025/)  
7. How the Future Homes Standard 2025 Will Transform Building ..., accessed March 8, 2026, [https://enviroscreen.org.uk/the-future-homes-standard-2025-will-transform-buildings/](https://enviroscreen.org.uk/the-future-homes-standard-2025-will-transform-buildings/)  
8. Navigating Building Regulations for Garden Room Construction ..., accessed March 8, 2026, [https://smartbuildprojects.co.uk/blog/navigating-building-regulations-for-garden-room-construction/](https://smartbuildprojects.co.uk/blog/navigating-building-regulations-for-garden-room-construction/)  
9. Outbuildings: Enhancing Your Outdoor Space \- Plans Made Easy, accessed March 8, 2026, [https://plansmadeeasy.org/outbuildings/](https://plansmadeeasy.org/outbuildings/)  
10. Small, Challenging Plots and SIPs Construction, accessed March 8, 2026, [https://www.clays.com/knowledge-hub/small-challenging-plots-and-sips-construction](https://www.clays.com/knowledge-hub/small-challenging-plots-and-sips-construction)  
11. SIP Kits UK: Structural Insulated Panels | Garden Room Kits, accessed March 8, 2026, [https://www.sipkitsuk.com/](https://www.sipkitsuk.com/)  
12. SIP Panels & SIPs Building Kits UK | Future SIPs, accessed March 8, 2026, [https://www.futuresips.co.uk/](https://www.futuresips.co.uk/)  
13. Blank SIP Panels | SIPS DIRECT – We Cut to Size for DIY and Trade, accessed March 8, 2026, [https://www.sipsdirect.co.uk/blank-sip-panels-sips-direct-we-cut-to-size-for-diy-and-trade/](https://www.sipsdirect.co.uk/blank-sip-panels-sips-direct-we-cut-to-size-for-diy-and-trade/)  
14. Specification Tips Around U-Values for Passivhaus Certified Windows, accessed March 8, 2026, [https://window.rehau.com/uk-en/specification-tips-passivhaus](https://window.rehau.com/uk-en/specification-tips-passivhaus)  
15. Passivhaus Standard vs Building Regulations \- what are the differences? \- Arbor Architects, accessed March 8, 2026, [https://www.arborarchitects.co.uk/journal/passivhausandbuildingregulations](https://www.arborarchitects.co.uk/journal/passivhausandbuildingregulations)  
16. BSD-025: The Passive House (Passivhaus) Standard—A comparison to other cold climate low-energy houses | buildingscience.com, accessed March 8, 2026, [https://buildingscience.com/documents/insights/bsi-025-the-passivhaus-passive-house-standard](https://buildingscience.com/documents/insights/bsi-025-the-passivhaus-passive-house-standard)  
17. The Definitive Guide to the Thinnest Wall Insulation for UK Homes, accessed March 8, 2026, [https://www.buyinsulationonline.co.uk/blog/the-definitive-guide-to-the-thinnest-wall-insulation-for-uk-homes](https://www.buyinsulationonline.co.uk/blog/the-definitive-guide-to-the-thinnest-wall-insulation-for-uk-homes)  
18. Comparing Flat Roof Insulation Thicknesses QA \- GBE \- Green Building Encyclopaedia, accessed March 8, 2026, [https://greenbuildingencyclopaedia.uk/uncategorized/comparing-flat-roof-insulation-thicknesses-qa/](https://greenbuildingencyclopaedia.uk/uncategorized/comparing-flat-roof-insulation-thicknesses-qa/)  
19. Aerogel vs Traditional Insulation: Technical Comparison, Thickness & Costs, accessed March 8, 2026, [https://ecohaus.hr/gb/blog/news/aerogel-vs-traditional-insulation-technical-comparison-costs-and-when-it-really-pays-off](https://ecohaus.hr/gb/blog/news/aerogel-vs-traditional-insulation-technical-comparison-costs-and-when-it-really-pays-off)  
20. Innovations in Insulation: Why Aerogels and Vacuum Insulated Panels Are Interesting—But Why Massachusetts Homeowners Still Choose Rigid Foam, accessed March 8, 2026, [https://greeninsulationgroup.com/innovations-in-insulation-why-aerogels-and-vacuum-insulated-panels-are-interesting-but-why-massachusetts-homeowners-still-choose-rig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](https://greeninsulationgroup.com/innovations-in-insulation-why-aerogels-and-vacuum-insulated-panels-are-interesting-but-why-massachusetts-homeowners-still-choose-rig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)  
21. Outbuildings in Your Garden: Planning Rules Explained, accessed March 8, 2026, [https://www.planninggeek.co.uk/gpdo/house/outbuildings/](https://www.planninggeek.co.uk/gpdo/house/outbuildings/)  
22. Self-Build House Extension Using SIP Panels : r/DIYUK \- Reddit, accessed March 8, 2026, [https://www.reddit.com/r/DIYUK/comments/1oytxw3/selfbuild\_house\_extension\_using\_sip\_panels/](https://www.reddit.com/r/DIYUK/comments/1oytxw3/selfbuild_house_extension_using_sip_panels/)  
23. Humidity Control for Timber Working and Storage \- Sealpump Engineering Ltd, accessed March 8, 2026, [https://www.sealpump.com/humidity-control-for-timber-working-and-storage/](https://www.sealpump.com/humidity-control-for-timber-working-and-storage/)  
24. Why Humidify... For Woodworking \- Condair, accessed March 8, 2026, [https://www.condair.com/humidifiers-for-woodworking](https://www.condair.com/humidifiers-for-woodworking)  
25. 5 Ways to Prevent Tool Corrosion in Humid Environments | HUB Industrial Supply, accessed March 8, 2026, [https://www.hubindustrial.com/resources/tool-maintenance-and-optimization/5-ways-to-prevent-tool-corrosion-in-humid-environments.html](https://www.hubindustrial.com/resources/tool-maintenance-and-optimization/5-ways-to-prevent-tool-corrosion-in-humid-environments.html)  
26. Airtightness and air pressure testing in accordance with the Passivhaus standard, accessed March 8, 2026, [https://www.passivhaustrust.org.uk/UserFiles/File/Technical%20Papers/BRE\_Passivhaus\_Airtightness\_Guide.pdf](https://www.passivhaustrust.org.uk/UserFiles/File/Technical%20Papers/BRE_Passivhaus_Airtightness_Guide.pdf)  
27. Create an Airtight Home: Getting Airtightness Right in Self Builds \- Build It, accessed March 8, 2026, [https://www.self-build.co.uk/eco-design-guide-make-house-airtight/](https://www.self-build.co.uk/eco-design-guide-make-house-airtight/)  
28. Workshop Ventilation System: What to Know? | United Enertech, accessed March 8, 2026, [https://unitedenertech.com/news/workshop-ventilation-system](https://unitedenertech.com/news/workshop-ventilation-system)  
29. Different MVHR Filter Types Explained, accessed March 8, 2026, [https://filtersdirect.uk/mvhr-filter-types-explained/](https://filtersdirect.uk/mvhr-filter-types-explained/)  
30. The meaning and difference between G4 and F7 filters, accessed March 8, 2026, [https://rukatech-filter.de/en/blogs/news/meaning-difference-g4-f7-filter](https://rukatech-filter.de/en/blogs/news/meaning-difference-g4-f7-filter)  
31. Filter Class Table – G4, F7 & HEPA According to ISO 16890 \- CarbonActive, accessed March 8, 2026, [https://carbonactive.com/en/insights/cannabis-insights/filter-class-table-g4-f7-hepa-iso-16890/](https://carbonactive.com/en/insights/cannabis-insights/filter-class-table-g4-f7-hepa-iso-16890/)  
32. F7 and G4 filters: What are the differences? \- Deltrian, accessed March 8, 2026, [https://www.deltrian.com/news/article/f7-filter-g4-filter](https://www.deltrian.com/news/article/f7-filter-g4-filter)  
33. MVHR Filters Overview \- Paul Heat Recovery, accessed March 8, 2026, [https://www.paulheatrecovery.co.uk/mvhr-and-mev-ducting-components/mvhr-filters/](https://www.paulheatrecovery.co.uk/mvhr-and-mev-ducting-components/mvhr-filters/)  
34. Dust Extraction Buyers Guide What Type of Extractor Should I Use?, accessed March 8, 2026, [https://www.machinery4wood.co.uk/extraimages/Buyers%20Guide%20to%20Dust%20Extraction.pdf](https://www.machinery4wood.co.uk/extraimages/Buyers%20Guide%20to%20Dust%20Extraction.pdf)  
35. Dust Extractor | Dust Extraction For Your Workshop | Buying Guide \- Axminster Tools, accessed March 8, 2026, [https://www.axminstertools.com/ideas-advice/dust-extractors/](https://www.axminstertools.com/ideas-advice/dust-extractors/)  
36. How to Protect Your Tools from Humidity and Heat in Austin's Climate, accessed March 8, 2026, [https://affordableportable.com/how-to-protect-your-tools-from-humidity-and-heat-in-austins-climate/](https://affordableportable.com/how-to-protect-your-tools-from-humidity-and-heat-in-austins-climate/)  
37. Garage conditioning to keep machinery from rusting? : r/woodworking \- Reddit, accessed March 8, 2026, [https://www.reddit.com/r/woodworking/comments/196bjub/garage\_conditioning\_to\_keep\_machinery\_from\_rusting/](https://www.reddit.com/r/woodworking/comments/196bjub/garage_conditioning_to_keep_machinery_from_rusting/)  
38. Low Carbon Heating Options for UK Homes: A Guide to Warmth and Sustainability, accessed March 8, 2026, [https://www.sl-energy.co.uk/low-carbon-heating-options-for-uk/](https://www.sl-energy.co.uk/low-carbon-heating-options-for-uk/)  
39. Low Carbon Heating Systems \- EndoTherm, accessed March 8, 2026, [https://www.endotherm.co.uk/low-carbon-heating/](https://www.endotherm.co.uk/low-carbon-heating/)  
40. Energy-Efficient Workshop Heating \- Climate & Heating Systems by Schwank, accessed March 8, 2026, [https://schwank.co.uk/energy-efficient-workshop-heating/](https://schwank.co.uk/energy-efficient-workshop-heating/)  
41. Efficient Workshop Heater Solutions | Winrow Ltd, accessed March 8, 2026, [https://www.winrowltd.co.uk/workshop-heaters](https://www.winrowltd.co.uk/workshop-heaters)  
42. Budget Heating for Your Workshop or Garage \- Heatingpoint, accessed March 8, 2026, [https://heatingpoint.com/advice-centre/blog/budget-heating-for-workshops-and-garages/](https://heatingpoint.com/advice-centre/blog/budget-heating-for-workshops-and-garages/)  
43. Anti-Corrosion Emitters \- Lee Valley Tools, accessed March 8, 2026, [https://www.leevalley.com/en-ca/shop/tools/workshop/tool-maintenance/59367-anti-corrosion-emitters](https://www.leevalley.com/en-ca/shop/tools/workshop/tool-maintenance/59367-anti-corrosion-emitters)  
44. The Future Homes and Buildings Standards: 2023 consultation \- GOV.UK, accessed March 8, 2026, [https://www.gov.uk/government/consultations/the-future-homes-and-buildings-standards-2023-consultation/the-future-homes-and-buildings-standards-2023-consultation](https://www.gov.uk/government/consultations/the-future-homes-and-buildings-standards-2023-consultation/the-future-homes-and-buildings-standards-2023-consultation)  
45. Passivhaus Compared to the Proposed FHS 2025, accessed March 8, 2026, [https://passivhaus.uk/wp-content/uploads/2025/03/PH-compared-to-FHS-2025-v1.2-250320.pdf](https://passivhaus.uk/wp-content/uploads/2025/03/PH-compared-to-FHS-2025-v1.2-250320.pdf)  
46. Building regulation compliant garden office, accessed March 8, 2026, [https://www.gardenofficeguide.co.uk/building-regulation-compliant-garden-office/](https://www.gardenofficeguide.co.uk/building-regulation-compliant-garden-office/)  
47. Garden Building Fire Safety and Cladding Fire Ratings \- Oilcanfinish Outdoor Living, accessed March 8, 2026, [https://oilcanfinish.com/2022/01/10/garden-building-cladding-fire-ratings/](https://oilcanfinish.com/2022/01/10/garden-building-cladding-fire-ratings/)  
48. Fire Resistant Cladding | Cladco, accessed March 8, 2026, [https://www.cladco.co.uk/blog/post/fire-resistant-cladding](https://www.cladco.co.uk/blog/post/fire-resistant-cladding)  
49. Extend your living space with a Cedral garden room \- Cedral, accessed March 8, 2026, [https://www.cedral.world/en-gb/cladding/blog/236729/extend-your-living-space-with-a-cedral-garden-room/](https://www.cedral.world/en-gb/cladding/blog/236729/extend-your-living-space-with-a-cedral-garden-room/)  
50. Timber Cladding Fire Retardancy \- Hewins Oak, accessed March 8, 2026, [https://hewinsoak.com/help/articles/37-timber-cladding-fire-retardancy](https://hewinsoak.com/help/articles/37-timber-cladding-fire-retardancy)  
51. How To Prepare A Foundation For A Garden Room, accessed March 8, 2026, [https://gardenhouse24.ie/blog/how-to-prepare-a-foundation-for-a-garden-room/](https://gardenhouse24.ie/blog/how-to-prepare-a-foundation-for-a-garden-room/)  
52. Guide To Garden Room Foundations From Rubicon, accessed March 8, 2026, [https://www.rubicongardenrooms.co.uk/blogs/blog/garden-room-foundations-1](https://www.rubicongardenrooms.co.uk/blogs/blog/garden-room-foundations-1)  
53. Build on a Solid Foundation | Freedom Room, accessed March 8, 2026, [https://freedomroom.com/pages/build-on-a-solid-foundation-for-your-freedom-room](https://freedomroom.com/pages/build-on-a-solid-foundation-for-your-freedom-room)  
54. How to Build a Garden Room Base – Step by Step Guide & Ideas, accessed March 8, 2026, [https://www.leisurebuildings.com/how-to-build-garden-room-base-ideas-guide/](https://www.leisurebuildings.com/how-to-build-garden-room-base-ideas-guide/)  
55. Wood humidity control in production | Airtec A/S, accessed March 8, 2026, [https://airtecsolutions.com/productive-benefits/wood](https://airtecsolutions.com/productive-benefits/wood)  
56. Woodworking Humidification Systems \- Fogco, accessed March 8, 2026, [https://fogco.com/humidification-systems/woodworking/](https://fogco.com/humidification-systems/woodworking/)  
57. Mastering Climate Control on the Job Site: Essential Tips for Woodworkers, accessed March 8, 2026, [https://awinet.org/mastering-climate-control-on-the-job-site-essential-tips-for-woodworkers-to-maintain-wood-quality/](https://awinet.org/mastering-climate-control-on-the-job-site-essential-tips-for-woodworkers-to-maintain-wood-quality/)
