wisogetnid/garden-room/research/glazing-research.md

# **Technical Specification and Strategic Integration of Fenestration Systems for Coastal Garden Workshops: A Case Study of Cowes, Isle of Wight**

The architectural development of a garden room workshop in Cowes, England, presents a sophisticated set of environmental and regulatory challenges that necessitate a high-performance approach to glazing and window design. Given its location on the northern tip of the Isle of Wight, the site is characterized by an aggressive maritime microclimate, high humidity, and significant salt-laden aerosols originating from the Solent. Furthermore, the specific site constraints—including 1.8-meter boundary fences on the south and west elevations, a north-facing primary entrance, and an east-facing view toward a neighboring property—demand a nuanced strategy for solar gain, thermal retention, and privacy management. The following report provides an exhaustive technical analysis of material resilience, glazing technologies, and compliance strategies, specifically tailored for a professional-grade workshop environment.

## **Material Resilience in Aggressive Coastal Environments**

The selection of window frame materials in Cowes is primarily dictated by the electrochemical interactions between the building envelope and the coastal atmosphere. Salt-laden air, common along the Solent coastline, accelerates the wear and tear of standard window frames and fittings through the deposition of salt crystals which, when combined with moisture, create a corrosive electrolytic film.1 This process is particularly damaging to standard metals and organic finishes, leading to pitting, blistering, and structural failure over time.4

### **Aluminum and Marine-Grade Performance**

For structures requiring slim sightlines and large glazed spans—common in modern workshop designs—aluminum is often the preferred substrate due to its high strength-to-weight ratio.2 However, raw or standard-anodized aluminum is insufficient for the Cowes environment. The technical requirement for this project is marine-grade, powder-coated aluminum, which provides a specialized protective envelope against salt air.4  
Marine-grade powder coating is more than an aesthetic layer; it is a thick, continuous barrier designed to resist the penetration of chloride ions. The application process ensures high UV stability, preventing the "chalking" or fading that often occurs when finishes are exposed to the high levels of reflected sunlight typical of seaside locations.2 When properly specified, these frames can maintain their structural integrity and appearance for up to 45 years, provided they are subjected to a routine cleaning regime.4

### **uPVC and Composite Alternatives**

As a non-conductive polymer, uPVC (unplasticised polyvinyl chloride) offers a naturally immune alternative to salt corrosion, moisture, and UV damage.6 Unlike timber or aluminum, uPVC does not rot, rust, or warp in response to humidity fluctuations, making it a highly cost-effective and low-maintenance choice for coastal outbuildings.1 Modern uPVC frames utilize multi-chambered profiles that provide excellent thermal insulation, often achieving A+ energy ratings.2  
For a workshop environment where aesthetic continuity with the main dwelling is required, composite frames—combining timber interiors for thermal performance with aluminum or uPVC exteriors for weather resistance—offer a premium solution.7 These systems leverage the natural insulation of wood while shielding the vulnerable organic material behind a protective coastal-grade cladding.7

| Material Property | Marine-Grade Aluminum | High-Performance uPVC | Composite (Timber/Alu) |
| :---- | :---- | :---- | :---- |
| **Corrosion Resistance** | Superior (with coating) 4 | Immune 7 | High 7 |
| **Structural Integrity** | Highest (Slim profiles) 2 | Moderate 7 | High 7 |
| **Thermal Conductivity** | Moderate (with thermal break) 2 | Low 6 | Lowest 7 |
| **Expected Lifespan** | 40–45 Years 6 | 20–25 Years 6 | 30–40 Years 7 |
| **Maintenance Level** | Low (Rinse every 3 months) 2 | Lowest 7 | Moderate 7 |

### **Metallurgy of Coastal Hardware**

The reliability of a workshop's fenestration depends heavily on its moving parts. In Cowes, standard 304-grade stainless steel hardware is prone to "tea staining" and pitting due to its lack of molybdenum. The mandatory specification for hinges, handles, and locks is 316 Marine Grade Stainless Steel.8 The chemical composition of 316-grade steel, which includes approximately 2-3% molybdenum, significantly increases resistance to chloride-induced corrosion.9 Brands such as Coastal BLU offer 316-grade hardware that is salt-spray tested for over 1,000 hours, ensuring that window stays and tilt-and-turn handles remain operational in the harsh maritime air.10

## **Strategic Light Capture and Shadow Mitigation**

The presence of 1.8-meter fences on the south and west boundaries of the garden room workshop presents a significant challenge to daylighting. In the northern hemisphere, the south elevation is the primary source of consistent, high-intensity sunlight and passive solar gain.13 A fence of this height, particularly if positioned close to the building, will cast long shadows during the winter months when the solar altitude is low.16

### **Solar Geometry and Clerestory Windows**

To circumvent the shadow cast by boundary fencing, the design must prioritize high-level glazing. Clerestory windows—horizontal panes positioned near the roofline—allow for the capture of direct sunlight that passes over the 1.8m fence line.15 This strategy is particularly effective for workshops, as it ensures that natural light reaches deep into the interior space while preserving lower wall areas for equipment mounting and storage.15  
In Cowes, the winter sun sits at a low angle (approximately 16 degrees at noon during the winter solstice). A 1.8m fence positioned 2 meters from the building would cast a shadow approximately 6.2 meters long, potentially shading the entire lower half of the garden room. By placing the sill of the south-facing windows above the 1.8m threshold, the workshop can maintain direct solar access throughout the year, reducing the need for artificial lighting and contributing to passive heating.15

### **Reflective Surfaces and Fencing Strategies**

The impact of high fences can be further mitigated through the use of light-colored or reflective materials. Pale or white-painted fences can reflect ambient light into the workshop through lower windows, softening the harsh shadows created by direct sunlight.16 Furthermore, replacing solid fence panels with lattice or open-slat designs (where privacy allows) can permit filtered, "dappled" light to enter the garden space, reducing the "closed-in" feeling of a small, fenced plot.16

## **Glazing Technology: Thermal Performance and Solar Control**

The 2025 updates to Part L of the Building Regulations introduce more stringent U-value requirements for outbuildings and extensions, moving toward a "Future Homes Standard" that prioritizes fabric energy efficiency.23 For the Cowes workshop, the glazing must not only admit light but also prevent excessive heat loss during the winter and minimize solar overheating during the summer.23

### **Triple Glazing vs. Vacuum Insulated Glazing (VIG)**

The choice between triple glazing and Vacuum Insulated Glazing (VIG) is central to the workshop’s thermal strategy. Triple glazing achieves low U-values (typically 0.6 to 1.0 $W/m^2K$) through the use of three panes of glass and two gas-filled cavities.26 However, triple glazing is heavy and requires thick frames (often 36mm-44mm), which can be structurally demanding and aesthetically bulky.26  
Vacuum Insulated Glazing, such as the Fineo system, represents a significant technological advancement. By replacing the gas-filled cavity with a microscopic 0.1mm vacuum gap, VIG can achieve a U-value of 0.7 $W/m^2K$ with a total thickness of only 7.7mm.26 This allows the glazing to be fitted into slimmer, more elegant frames while providing thermal performance that exceeds triple glazing.28 Furthermore, VIG offers superior light transmission (up to 15% more daylight than triple glazing) and better solar heat gain ($g$-value), which is vital for the south-facing windows aiming to capture low winter sun.26

| Glazing Type | U-Value (W/m2K) | Thickness (mm) | Light Transmission | Acoustic Reduction (dB) |
| :---- | :---- | :---- | :---- | :---- |
| **Standard Double** | 1.2 – 1.4 30 | 24 – 28 | \~80% | 30 – 32 |
| **High-Spec Triple** | 0.6 – 0.8 27 | 36 – 44 | 71% 26 | 32 – 35 28 |
| **Vacuum (Fineo)** | 0.4 – 0.7 27 | 7.7 – 10 | 80% 26 | 35 – 39 26 |

### **North-Facing Door and Thermal Breaks**

The north-facing door represents a major point of thermal vulnerability. North-facing elevations receive no direct sunlight, meaning the door will be a consistent source of heat loss through conduction.13 To mitigate this, a thermally broken frame is essential. A thermal break consists of a non-conductive material (such as polyamide, resin, or fiberglass) placed between the inner and outer sections of the door frame.31 This barrier interrupts the flow of thermal energy, preventing the interior frame from becoming cold enough to cause condensation—a critical factor for protecting workshop tools from moisture damage.31

## **Privacy Management and Neighbor Proximity**

The eastern elevation of the workshop faces the garden and a neighboring house, requiring a balance between the desire for an expansive view and the necessity of privacy. In suburban contexts like Cowes, "overlooking" issues can lead to planning disputes or neighbor tension, especially if the workshop floor is raised above the natural ground level.36

### **Switchable Smart Glass and Directional Glazing**

For the east-facing view, switchable smart glass (PDLC technology) provides a dynamic solution. This glass can transition from clear to opaque at the touch of a button, allowing the occupant to maintain a connection to the garden when desired or to ensure total privacy during sensitive work.37 Switchable glass is more durable than surface-applied films, as the liquid crystal layer is laminated between two sheets of tempered glass, protecting it from the moisture and dust typical of a workshop environment.38  
Alternatively, "directional glazing" or obscured glass can be used on the eastern side to permit light while blocking direct sightlines.36 Sandblasted or acid-etched glass provides a permanent frosted effect that scatters light, ensuring the workshop remains bright without exposing the interior.40 If a view is preferred, "one-way" mirror glass can be utilized, though its effectiveness depends on the lighting differential between the interior and exterior.42

### **Natural Screening and Sightline Control**

Beyond the glass itself, site-level screening can manage privacy concerns. Pleached trees—where the canopy is trained on a high-level frame—can provide a "green fence" above the 1.8m boundary line, blocking views from the neighbor's first-floor windows without taking up significant garden space.22 Similarly, the use of lattice panels atop the existing fence can add height and support climbing plants, further obscuring the workshop's eastern view while maintaining airflow.22

## **Regulatory Compliance: The 2025 Standards**

The construction of a garden room workshop in Cowes must adhere to the UK Building Regulations, specifically Parts L (Energy), K (Safety), and A (Structure).

### **Part L: The 25% Glazing Rule and Compensatory Measures**

Under Part L 2025, the total area of windows, doors, and rooflights in an extension or non-exempt outbuilding should typically not exceed 25% of the internal floor area.25 For a workshop that requires significant natural light, exceeding this limit is often necessary. To comply while exceeding the 25% threshold, the designer must demonstrate through SAP 10 (Standard Assessment Procedure) calculations that the overall energy performance of the building is not compromised.25  
This is achieved through compensatory measures, such as:

1. **Enhanced Fabric Insulation:** Increasing the thickness of insulation in the walls, floor, and roof to achieve U-values significantly lower than the minimum requirements (e.g., $0.12 W/m^2K$ for the roof instead of the mandatory $0.16 W/m^2K$).30  
2. **Superior Glazing:** Utilizing VIG or Krypton-filled triple glazing to minimize the heat loss through the glass panes themselves.25  
3. **Airtightness:** Ensuring professional sealing of all window and door junctions to reduce uncontrolled air infiltration.23

### **Part K: Safety and Impact Protection**

Safety glazing is mandatory in "critical locations" as defined by Part K. This includes all glass below 800mm from the floor and glass in or near doors up to 1500mm.23 The glass must be either toughened (BS EN 12150\) or laminated (BS EN ISO 12543), with permanent marking to certify its standard.23 In a workshop, laminated glass is often preferred for its ability to hold together upon impact, providing a higher degree of security and preventing glass shards from contaminating work areas.30

### **Part A: Structural Wind Loading in Cowes**

The coastal location of Cowes necessitates a rigorous assessment of wind loading. The Solent area is subject to high wind speeds and pressure changes during coastal storms.4 The glazing and frame systems must be engineered to withstand these lateral loads without excessive deflection, which could otherwise lead to seal failure or frame distortion.23 Professional installers typically design to a minimum wind loading of $0.6-0.65 kN/m^2$, ensuring that the large expanses of glass remain stable in all weather conditions.47

## **Lighting Ergonomics and Workspace Optimization**

The lighting strategy for a workshop must integrate natural light capture with high-quality artificial sources to ensure a safe and productive work environment.

### **Managing Glare and Task Illumination**

While natural light is essential for well-being, direct sunlight on work surfaces can cause significant glare and eyestrain.20 Positioning workbenches perpendicular to windows allows the light to hit the surface from the side, minimizing reflections on tools and digital screens.20 The north-facing door and any north-facing auxiliary windows are valuable here, as they provide consistent, soft, and diffused light throughout the day, which is ideal for color-sensitive tasks.13

### **Artificial Lighting and Color Rendering**

Artificial lighting should supplement the natural light capture. For a professional workshop, LED fixtures with a high Color Rendering Index (CRI) of 90 or above are recommended to ensure that colors appear accurate and true.20 The color temperature of the lighting should be tailored to the function: cooler tones (4000K-5000K) are best for alert, focused work, while warmer tones (2700K-3000K) can be used for relaxation areas.20

| Lighting Type | Temperature (K) | Function in Workshop | Recommended Placement |
| :---- | :---- | :---- | :---- |
| **Daylight LED** | 5000K – 6500K | High-detail task work 49 | Overhead panels 20 |
| **Cool White** | 3500K – 4500K | General alertness/focus 49 | Ambient ceiling spots 19 |
| **Warm White** | 2700K – 3000K | Relaxation/Evening use 48 | Floor lamps/Accent strips 21 |

## **Maintenance Protocols for Coastal Longevity**

The aggressive salt air of Cowes requires a proactive maintenance schedule to prevent the deterioration of the window systems.

### **Cleaning Regimes and Material Care**

The primary defense against coastal corrosion is regular rinsing with fresh water.3 This washes away the salt deposits before they can accumulate and react with the metal surfaces. For more thorough cleaning, a non-abrasive solution of warm water, mild soap, and a small amount of vinegar is effective at dissolving salt crusts without etching the glass.50

* **Quarterly Rinsing:** Every three months, the exterior of all frames and glass should be hosed down with fresh water, particularly after high-wind events that carry sea spray inland.2  
* **Hardware Lubrication:** Moving parts such as hinges and locks should be lubricated every six months with a silicone-based spray, which resists the accumulation of salt and dust better than oil-based alternatives.3  
* **Seal Inspection:** Weather stripping and seals should be inspected annually for signs of shrinkage or cracking, as any breach in the seal will allow salt air to reach the internal mechanisms of the window.3

## **Technical Synthesis and Strategic Implementation**

The successful design of the Cowes garden room workshop hinges on a "system-wide" approach to fenestration. By combining marine-grade aluminum frames with Vacuum Insulated Glazing (VIG), the building can achieve high levels of natural light through south-facing clerestory windows while maintaining a high-performance thermal envelope that exceeds the 2025 Building Regulations.  
The use of 316-grade stainless steel hardware ensures long-term operational reliability in the salt-laden Solent air, while switchable smart glass on the eastern elevation manages privacy concerns with the neighboring property without sacrificing daylight. By integrating these advanced materials and strategies, the workshop will function as a durable, energy-efficient, and professional space that capitalizes on its garden setting while mitigating the significant site-specific challenges of its coastal location.  
The final strategy must prioritize:

1. **South Elevation:** High-level clerestory VIG windows to clear the 1.8m fence and maximize winter solar gain.  
2. **East Elevation:** Switchable smart glass to manage the "overlooking" conflict with the neighbor while providing a connection to the garden.  
3. **North Elevation:** A thermally broken door with a high-insulation core to prevent conductive heat loss and condensation.  
4. **Materiality:** 316-grade hardware and marine-grade powder-coated aluminum to resist the Solent’s corrosive microclimate.

Through this meticulous selection and integration of fenestration technologies, the Cowes garden room workshop will be established as a benchmark for high-performance outbuilding design in the modern regulatory and environmental landscape.

#### **Works cited**

1. How To Choose Durable Window Frames For Coastal Homes, accessed March 8, 2026, [https://www.accoladewindows.co.uk/durable-window-frames-coastal-homes/](https://www.accoladewindows.co.uk/durable-window-frames-coastal-homes/)  
2. Coastal Considerations: Choosing Windows for South Wales Seafront Properties, accessed March 8, 2026, [https://www.futureglazewindows.co.uk/blog/coastal-windows](https://www.futureglazewindows.co.uk/blog/coastal-windows)  
3. How Coastal Homes Can Prevent Corrosion of Window Hardware & Hinges, accessed March 8, 2026, [https://clearmaxwindows.com/post/how-coastal-homes-can-prevent-corrosion-of-window-hardware-hinges/](https://clearmaxwindows.com/post/how-coastal-homes-can-prevent-corrosion-of-window-hardware-hinges/)  
4. What Is the Best Window Type for Coastal Homes? | UK Doors Online, accessed March 8, 2026, [https://www.ukdoorsonline.co.uk/what-is-the-best-window-type-for-coastal-homes/](https://www.ukdoorsonline.co.uk/what-is-the-best-window-type-for-coastal-homes/)  
5. How To Prevent Saltwater Damage to Windows | Absolute Window & Door, accessed March 8, 2026, [https://www.absolutewindowanddoor.net/blog/the-impact-of-saltwater-corrosion-on-coastal-home-windows-prevention-tips/](https://www.absolutewindowanddoor.net/blog/the-impact-of-saltwater-corrosion-on-coastal-home-windows-prevention-tips/)  
6. Protect Your Home From Coastal Elements | Premier Windows & Doors \- UK.COM, accessed March 8, 2026, [https://www.premierwindows.uk.com/news/protect-your-home-destructive-coastal-elements](https://www.premierwindows.uk.com/news/protect-your-home-destructive-coastal-elements)  
7. What Are the Best Window Frames for Coastal Areas?, accessed March 8, 2026, [https://www.windoworldltd.co.uk/what-are-the-best-window-frames-for-coastal-areas/](https://www.windoworldltd.co.uk/what-are-the-best-window-frames-for-coastal-areas/)  
8. 316 Marine Grade Stainless Steel \- Coastal Specialist Ironmongery, accessed March 8, 2026, [https://www.coastal-group.com/Brochures/LIT-BRO-Coastal-BLU-Book\_WEB.pdf](https://www.coastal-group.com/Brochures/LIT-BRO-Coastal-BLU-Book_WEB.pdf)  
9. 316 Marine Grade Stainless Steel \- Window-warehouse.co.uk, accessed March 8, 2026, [https://www.window-warehouse.co.uk/app/uploads/2022/02/LIT-CAT-BLU-B06\_LR.pdf](https://www.window-warehouse.co.uk/app/uploads/2022/02/LIT-CAT-BLU-B06_LR.pdf)  
10. 316 Marine-Grade Stainless Steel...Spotlight On \- Suffolk Latch Company, accessed March 8, 2026, [https://www.suffolklatchcompany.com/blogs/news/spotlight-316-marine-grade-stainless-steel-built-to-perform-and-impress](https://www.suffolklatchcompany.com/blogs/news/spotlight-316-marine-grade-stainless-steel-built-to-perform-and-impress)  
11. BLU Tilt & Turn Window Handle 32.5 x 69 x 14mm 316 Satin Stainless Steel \- M Brock, accessed March 8, 2026, [https://mbrock.co.uk/product/blu-tilt-turn-window-handle-32-5-x-69-x-14mm-316-satin-stainless-steel/](https://mbrock.co.uk/product/blu-tilt-turn-window-handle-32-5-x-69-x-14mm-316-satin-stainless-steel/)  
12. Stainless Steel Door & Window Furniture \- BLU® | Coastal Group, accessed March 8, 2026, [https://www.coastal-group.com/brand/blu-hardware](https://www.coastal-group.com/brand/blu-hardware)  
13. Maximizing Natural Light: Tips for Optimizing Window Placement and Design, accessed March 8, 2026, [https://www.windowmakeoveratlanta.com/maximizing-natural-light-tips-for-optimizing-window-placement-and-design/](https://www.windowmakeoveratlanta.com/maximizing-natural-light-tips-for-optimizing-window-placement-and-design/)  
14. Maximize Natural Light in Your Home with Strategic Window Placement, accessed March 8, 2026, [https://wmgb.com/blog/maximize-natural-light-in-your-home-with-strategic-window-placement/](https://wmgb.com/blog/maximize-natural-light-in-your-home-with-strategic-window-placement/)  
15. Maximizing Natural Light with Window Installation \- Florida Window & Door Solutions, accessed March 8, 2026, [https://www.floridawds.com/maximizing-natural-light-with-window-installation/](https://www.floridawds.com/maximizing-natural-light-with-window-installation/)  
16. Fence Placement Strategies to Optimize Light for Thriving Plants, accessed March 8, 2026, [https://perryfencing.com/fence-placement-strategies-to-optimize-light-for-thriving-plants/](https://perryfencing.com/fence-placement-strategies-to-optimize-light-for-thriving-plants/)  
17. 5\. Technical specifications | schoolbuildings.vic.gov.au \- Victorian School Building Authority, accessed March 8, 2026, [https://www.schoolbuildings.vic.gov.au/building-quality-standards-handbook/technical-specifications](https://www.schoolbuildings.vic.gov.au/building-quality-standards-handbook/technical-specifications)  
18. Installation Appearance Plan \- NAVFAC Pacific, accessed March 8, 2026, [https://pacific.navfac.navy.mil/Portals/72/Marianas/Documents/MCBG%20Installation%20Appearance%20Plan%20APR2011.pdf](https://pacific.navfac.navy.mil/Portals/72/Marianas/Documents/MCBG%20Installation%20Appearance%20Plan%20APR2011.pdf)  
19. Garden Room Lighting Ideas & Layout Tips | Hawksbeck, accessed March 8, 2026, [https://hawksbeck.co.uk/making-the-most-of-shorter-days-lighting-layout-tips-for-garden-rooms/](https://hawksbeck.co.uk/making-the-most-of-shorter-days-lighting-layout-tips-for-garden-rooms/)  
20. Lighting Design Tips for Your Garden Studio Room, accessed March 8, 2026, [https://essexgardenstudios.co.uk/lighting-design-tips-for-your-garden-studio-room/](https://essexgardenstudios.co.uk/lighting-design-tips-for-your-garden-studio-room/)  
21. Utilising Lighting That Effectively Suits Day And Night In Your Garden Room, accessed March 8, 2026, [https://southwalesgardenrooms.co.uk/utilising-lighting-that-effectively-suits-day-and-night-in-your-garden-room/](https://southwalesgardenrooms.co.uk/utilising-lighting-that-effectively-suits-day-and-night-in-your-garden-room/)  
22. Creative Ways To Screen Your Garden from Overlooking Neighbours, accessed March 8, 2026, [https://heathlandscapes.co.uk/blog/screen-garden-from-overlooking-neighbours/](https://heathlandscapes.co.uk/blog/screen-garden-from-overlooking-neighbours/)  
23. UK Building Regulations for Large Glass Openings (2025 Guide), accessed March 8, 2026, [https://cherwellwindows.co.uk/blog/building-regulations-large-glass-openings-uk-2025/](https://cherwellwindows.co.uk/blog/building-regulations-large-glass-openings-uk-2025/)  
24. UK Building Regulations Part L Windows Renovation 2025 | A Homeowner's Guide, accessed March 8, 2026, [https://cherwellwindows.co.uk/blog/uk-building-regulations-part-l-windows-renovation-2025/](https://cherwellwindows.co.uk/blog/uk-building-regulations-part-l-windows-renovation-2025/)  
25. The 25% Glazing Limit: How Much Glass Can You Have in a UK Extension?, accessed March 8, 2026, [https://skylights-rooflanterns.co.uk/blogs/news/the-25-glazing-limit-how-much-glass-can-i-have-in-my-extension](https://skylights-rooflanterns.co.uk/blogs/news/the-25-glazing-limit-how-much-glass-can-i-have-in-my-extension)  
26. Vacuum Glazing or Triple Glazing: There's Only One Winner, accessed March 8, 2026, [https://fineo-vacuum-glazing.co.uk/vacuum-glazing-or-triple-glazing/](https://fineo-vacuum-glazing.co.uk/vacuum-glazing-or-triple-glazing/)  
27. Insulated glass and thermal efficiency: A comprehensive guide \- Six Over Six Windows, accessed March 8, 2026, [https://sixoversixwindows.co.uk/blog/insulated-glass/](https://sixoversixwindows.co.uk/blog/insulated-glass/)  
28. Triple glazing vs vacuum insulated glazing \- Parsons Joinery, accessed March 8, 2026, [https://parsonsjoinery.com/blog/triple-glazing-versus-vacuum-insulated-glazing](https://parsonsjoinery.com/blog/triple-glazing-versus-vacuum-insulated-glazing)  
29. Benefits of Vacuum Glazing Vs Triple Glazing | George Barnsdale, accessed March 8, 2026, [https://www.georgebarnsdale.co.uk/blog/vacuum-glazing-vs-triple-glazing-which-is-best/](https://www.georgebarnsdale.co.uk/blog/vacuum-glazing-vs-triple-glazing-which-is-best/)  
30. Building Regulations for Glass Extensions: What Your Installer Must Get Right, accessed March 8, 2026, [https://www.roomoutside.com/glass-extension-building-regulations-guide/](https://www.roomoutside.com/glass-extension-building-regulations-guide/)  
31. Thermal Break in Doors: What you need to know\! \- DAWSON, accessed March 8, 2026, [https://www.dawsonmetal.com/thermal-break](https://www.dawsonmetal.com/thermal-break)  
32. The Science Behind Thermal Break Doors \- Window Works Co., accessed March 8, 2026, [https://www.windowworksnc.com/the-science-behind-thermal-break-doors-how-they-work-to-improve-your-homes-energy-efficiency/](https://www.windowworksnc.com/the-science-behind-thermal-break-doors-how-they-work-to-improve-your-homes-energy-efficiency/)  
33. Understanding Thermal Breaks in Building and Construction \- Kawneer, accessed March 8, 2026, [https://www.kawneer.com/news/understanding-thermal-breaks-in-building-and-construction/](https://www.kawneer.com/news/understanding-thermal-breaks-in-building-and-construction/)  
34. Structural Thermal Breaks for Building Efficiency \- Armatherm, accessed March 8, 2026, [https://www.armatherm.com/structural-thermal-breaks-enhancing-building-efficiency-and-sustainability/](https://www.armatherm.com/structural-thermal-breaks-enhancing-building-efficiency-and-sustainability/)  
35. Thermally Broken Doors | Statement Pivot & Hinge Front Doors \- Modern Steel Doors, accessed March 8, 2026, [https://modernsteeldoors.com/thermally-broken-doors/](https://modernsteeldoors.com/thermally-broken-doors/)  
36. Overlooking and Privacy Issues With Garden Rooms \- My Outhouse, accessed March 8, 2026, [https://myouthouse.co.uk/blog/overlooking-and-privacy-issues-with-garden-rooms/](https://myouthouse.co.uk/blog/overlooking-and-privacy-issues-with-garden-rooms/)  
37. Clarity-View | Switchable Privacy Glass, accessed March 8, 2026, [https://www.privacyglasssolutions.com/products/clarity-view-switchable-privacy-glass/](https://www.privacyglasssolutions.com/products/clarity-view-switchable-privacy-glass/)  
38. Why You Should Opt for Switchable Glass and Window Film \- smartprivacyglass.net, accessed March 8, 2026, [https://www.smartprivacyglass.net/post/why-switchable-glass](https://www.smartprivacyglass.net/post/why-switchable-glass)  
39. Which Switchable Glass Product Is Best For Me? Smart Glass or Smart Film?, accessed March 8, 2026, [https://www.smartglasscountry.com/news/difference-smart-glass-or-smart-film](https://www.smartglasscountry.com/news/difference-smart-glass-or-smart-film)  
40. Optimizing Window Placement: Boosting Aesthetics & Light \- Tom's River Door & Window, accessed March 8, 2026, [https://tomsriverdoorandwindow.com/blog/optimizing-window-placement-boosting-aesthetics-light/](https://tomsriverdoorandwindow.com/blog/optimizing-window-placement-boosting-aesthetics-light/)  
41. Residential \- Privacy Glass Solution, accessed March 8, 2026, [https://www.privacyglasssolutions.com/residential/](https://www.privacyglasssolutions.com/residential/)  
42. One-Way-Mirror Film or Glass: Which to Choose? \- window tint installer, accessed March 8, 2026, [https://mgtfilms.com/blog/one-way-mirror-film-or-glass-which-to-choose/](https://mgtfilms.com/blog/one-way-mirror-film-or-glass-which-to-choose/)  
43. A designer's guide to creating privacy in the garden with tips on how to screen your garden from overlooking neighbours, accessed March 8, 2026, [https://www.gardensillustrated.com/garden-design/garden-privacy-ideas](https://www.gardensillustrated.com/garden-design/garden-privacy-ideas)  
44. Landscaping for Privacy \- Harmony in the Garden, accessed March 8, 2026, [https://harmonyinthegarden.com/2021/05/landscaping-for-privacy/](https://harmonyinthegarden.com/2021/05/landscaping-for-privacy/)  
45. What can I do if the glazing in my extension exceeds to allowed 25%?, accessed March 8, 2026, [https://cncbuildingcontrol.gov.uk/faqs/can-galzing-extension-exceeds-allowed-25/](https://cncbuildingcontrol.gov.uk/faqs/can-galzing-extension-exceeds-allowed-25/)  
46. Building Regulations Part L1 | Architectural Glazing to New Build Dwellings | IQ Glass, accessed March 8, 2026, [https://www.iqglassuk.com/technical-advice/building-regulations-part-l1-architectural-glazing-to-new-build-dwellings/s88691/](https://www.iqglassuk.com/technical-advice/building-regulations-part-l1-architectural-glazing-to-new-build-dwellings/s88691/)  
47. Wind Resistance and Loading for Architectural Glazing \- Technical Article | IQ Glass, accessed March 8, 2026, [https://www.iqglassuk.com/technical-advice/architectural-glazing-wind-resistance-and-loading/s88403/](https://www.iqglassuk.com/technical-advice/architectural-glazing-wind-resistance-and-loading/s88403/)  
48. Creative Lighting Ideas for Garden Rooms and Offices \- Summerhouse24 Ireland, accessed March 8, 2026, [https://summerhouse24.ie/blog/lights-for-garden-rooms/](https://summerhouse24.ie/blog/lights-for-garden-rooms/)  
49. Illuminating Your Garden Room: Tips from Into The Garden, accessed March 8, 2026, [https://intothegardenroom.com/lluminating-your-garden-room-ideas/](https://intothegardenroom.com/lluminating-your-garden-room-ideas/)  
50. Prevent Salt Water Damage on Home Windows, accessed March 8, 2026, [https://www.advancemyhome.com/how-salt-water-is-damaging-your-windows/](https://www.advancemyhome.com/how-salt-water-is-damaging-your-windows/)  
51. How Salt Air Creates Unique Coastal Window Cleaning Problems in Westcliff-on-Sea, accessed March 8, 2026, [https://canveywindowcleaners.co.uk/coastal-window-cleaning-problems/](https://canveywindowcleaners.co.uk/coastal-window-cleaning-problems/)
