wisogetnid/garden-room/research/warm-roof-research.md

# **High-Performance Structural Integration of Warm Roof Systems and Cantilevered Junctions for Solar-Ready Timber Frame Garden Rooms**

The contemporary garden room has transcended its origins as a seasonal outbuilding to become a sophisticated extension of the primary residence, requiring rigorous architectural standards for thermal efficiency, structural integrity, and long-term durability. Central to this evolution is the implementation of the warm roof system, a design strategy that places the primary thermal barrier above the structural deck, effectively maintaining the building’s timber skeleton within the conditioned envelope. This configuration is particularly advantageous for multi-functional spaces where internal volume and ceiling height are prioritized. When such a structure is specified with a 50cm north-facing overhang and the requirement for future solar panel integration, the design complexity increases significantly. The lack of direct solar drying on a north-facing aspect, combined with the substantial cantilever and the localized point loads of a photovoltaic (PV) array, necessitates a meticulous approach to material selection and junction detailing to ensure the building performs optimally over its fifty-year design life.1

## **Theoretical Foundations of Warm Roof Thermodynamics and Layering**

The thermodynamic superiority of the warm roof system in a timber frame context is rooted in its management of the dew point. In traditional cold roof constructions, the insulation is fitted between the rafters, necessitating a ventilated cavity of at least 50mm above the insulation to mitigate the risk of interstitial condensation. Conversely, the warm roof "wraps" the structural timber in a continuous thermal blanket, shifting the dew point to the exterior of the structural deck. This arrangement eliminates the need for cross-flow ventilation, which is often difficult to achieve effectively in low-profile garden rooms where height is restricted by Permitted Development rules.2  
The standard architectural build-up for a high-specification warm roof begins with the structural rafters, which, for a project of this nature, are typically $47 \\times 150\\text{mm}$ or $47 \\times 200\\text{mm}$ C24 graded timber. These support a primary structural deck, usually $18\\text{mm}$ OSB3 or structural grade plywood, which provides the necessary diaphragm strength and a stable substrate for subsequent layers. Above this deck, a high-performance vapor control layer (VCL) is applied. The VCL is critical; it prevents the migration of warm, moist air from the interior into the insulation layer, where it could otherwise condense if it reaches a cold surface. In a warm roof, this VCL is situated on the "warm side" of the primary insulation, ensuring that the structural deck remains dry and protected.2

| Component Layer | Material Specification | Primary Function |
| :---- | :---- | :---- |
| Waterproofing | $1.2\\text{mm}$ or $1.5\\text{mm}$ EPDM Membrane | Primary weather and UV barrier 1 |
| Secondary Deck | $9\\text{mm}$ or $11\\text{mm}$ OSB3 (optional) | Protection for insulation/substrate for glue 2 |
| Thermal Insulation | PIR, XPS, or Stone Wool | Thermal resistance and load support 8 |
| Vapor Control Layer | Reinforced Foil-backed Membrane | Prevention of interstitial condensation 2 |
| Primary Deck | $18\\text{mm}$ OSB3 or Plywood | Structural diaphragm and VCL substrate 2 |
| Structural Frame | C24 Timber Rafters | Load transfer to wall plates 13 |

The thermal insulation layer follows the VCL. In the UK market, Polyisocyanurate (PIR) boards are the industry standard due to their high R-value per millimeter, which is essential for meeting Building Regulations Part L while maintaining a low building profile.5 Finally, the build-up is capped with a waterproofing membrane, most commonly a single-ply EPDM rubber sheet, which is renowned for its durability and resistance to ozone and UV degradation, with a typical life expectancy exceeding fifty years.1

## **Material Science of High-Performance Insulants**

Selecting the appropriate insulation for a solar-ready garden room requires a multi-dimensional analysis of thermal conductivity, compressive strength, and moisture resistance. While thermal resistance is the primary driver for energy efficiency, the capacity of the insulation to support the dead loads of solar panels and the live loads of maintenance traffic without deformation is the primary driver for structural longevity.

### **Polyisocyanurate (PIR) and Phenolic Foams**

PIR insulation is favored for its exceptional thermal conductivity ($\\lambda$) values, typically ranging from $0.021$ to $0.028 \\text{ W/mK}$.15 The chemical structure of PIR, a thermoset plastic produced as a foam and usually faced with low-emissivity aluminum foil, allows for very thin roof profiles. For a garden room attempting to stay under a 2.5m eaves height, PIR is often the only viable material that can achieve a U-value of $0.18 \\text{ W/m}^2\\text{K}$ or better.3  
However, the compressive strength of standard PIR boards, which generally falls between $120\\text{kPa}$ and $150\\text{kPa}$ at 10% compression, requires careful consideration when planning for solar arrays.8 While this is sufficient for occasional foot traffic, long-term point loads from solar mounting brackets or the distributed weight of a ballasted system can lead to localized "creep" or depression. In high-specification builds, a high-density cover board or a secondary deck of OSB may be placed over the PIR to distribute these loads across a larger surface area.9

### **Extruded Polystyrene (XPS)**

XPS is often considered when compressive strength is the paramount requirement. Unlike Expanded Polystyrene (EPS), which is manufactured from fused beads, XPS is produced through an extrusion process that creates a uniform, closed-cell structure. This results in superior compressive strength, ranging from $250\\text{kPa}$ to $700\\text{kPa}$, and nearly zero water absorption.10 These properties make XPS ideal for ballasted solar systems on flat roofs, where the insulation may be subject to high static loads and potential moisture exposure in an inverted roof configuration.6 However, XPS has a higher thermal conductivity than PIR (typically $0.030\\text{--}0.036 \\text{ W/mK}$), requiring a thicker layer to achieve the same thermal performance.16

### **Stone Wool and Mineral Fiber**

Stone wool, such as Rockwool, provides excellent fire resistance and acoustic dampening, which is often a priority for music studios or offices in dense urban gardens.5 While stone wool is non-combustible (Euroclass A1), its compressive strength is significantly lower than rigid foams, typically around $40\\text{--}80\\text{kPa}$.8 To accommodate roof-mounted equipment like solar panels on a stone wool warm roof, specialized high-density products like ROCKDeck must be used, or the solar racking must be mechanically fixed through the insulation directly into the rafters below.8

| Property | PIR (Polyisocyanurate) | XPS (Extruded Polystyrene) | Stone Wool | Wood Fiber |
| :---- | :---- | :---- | :---- | :---- |
| Thermal Cond. ($\\lambda$) | $0.022 \\text{ W/mK}$ | $0.034 \\text{ W/mK}$ | $0.039 \\text{ W/mK}$ | $0.040 \\text{ W/mK}$ |
| Compressive Strength | $120\\text{--}150\\text{ kPa}$ | $300\\text{--}700\\text{ kPa}$ | $50\\text{--}80\\text{ kPa}$ | $50\\text{--}200\\text{ kPa}$ |
| Fire Classification | Euroclass B/E | Euroclass E | Euroclass A1 | Euroclass E |
| Acoustic Absorption | Poor (Rigid) | Poor (Rigid) | Excellent | Good |
| Environmental Impact | High Embodied Carbon | High Embodied Carbon | Moderate | Carbon Sequestration |

Source: 8

## **Structural Engineering of the Wall-to-Roof Junction**

The junction between the timber frame wall and the warm roof is a critical nexus for structural load transfer and thermal continuity. In a garden room project, the walls are typically constructed using $47 \\times 100\\text{mm}$ CLS (Canadian Lumber Standard) studs at 400mm or 600mm centers.14 For a solar-ready structure, 400mm centers are strongly recommended as they provide more frequent fixing points for the roof rafters and increase the overall lateral stability of the building.14

### **The Double Top Plate and Rafter Bearing**

The top of the wall frame must be capped with a double top plate. This is a standard UK construction detail that serves several functions: it ties the individual wall panels together into a monolithic structure, and it provides a continuous bearing surface for the roof joists. Crucially, the double top plate allows for the roof joists to be positioned anywhere along the length of the wall, rather than having to align perfectly with the studs below, although alignment is still preferred for direct load path efficiency.14  
The connection between the rafter and the top plate must resist both the downward gravitational loads of the roof and solar array and the upward suction forces caused by wind. This is typically achieved through the use of structural timber screws or inverted joist hangers. In the context of a significant 50cm overhang, the risk of wind uplift is magnified, as the overhanging section acts as a lever arm.13

### **Thermal Bridging Mitigation: The "Plugging" Strategy**

One of the most common failures in warm roof design is the creation of a thermal bridge at the wall-to-roof junction. While the roof and walls may be individually well-insulated, the point where they meet often has a gap in the thermal envelope. If the roof insulation only sits on top of the deck, the space between the rafters above the wall remains cold. When warm internal air enters this space, it meets the cold underside of the roof deck, leading to condensation and rot.4  
To prevent this, high-specification builds employ a "plugging" technique. This involves cutting blocks of rigid PIR insulation or tightly packing mineral wool between the rafters directly above the wall line. This "plug" must be continuous with the wall insulation below and the roof insulation above. Additionally, the Vapor Control Layer (VCL) from the wall should be lapped and taped to the VCL of the roof to ensure a continuous air and vapor-tight seal around the entire junction.4

## **Engineering the 50cm Cantilevered Overhang**

The 50cm overhang specified for the north-facing aspect presents two primary challenges: structural cantilever mechanics and hygrothermal risk management. From a structural perspective, a 50cm cantilever on a flat or low-pitch roof requires rafters of sufficient depth and stiffness to prevent deflection, especially when subject to snow accumulation or the potential installation of solar panels near the roof edge.12

### **Cantilever Mechanics and Backspan**

In structural timber engineering, a cantilevered beam is generally restricted by the "one-third/two-thirds" rule, where the overhanging portion should not exceed one-third of the total rafter length, with the remaining two-thirds acting as a backspan anchored within the structure. For a 50cm overhang, this is easily achieved in most garden room dimensions. However, the stiffness of the rafter is the deciding factor for "deflection," or sagging. Using C24 graded timber instead of the more common C16 is advisable, as it has a higher modulus of elasticity and better resistance to bending.13  
The use of an $18\\text{mm}$ OSB3 or plywood primary deck is essential for the overhang. This deck acts as a diaphragm, distributing loads across multiple rafters and providing lateral stability. In some cases, short deep counter-battens can be fitted over the overhanging rafters to further stiffen the OSB deck and prevent "shear" or sliding of the insulation layers above.12

### **Wind Uplift and Fascia Detailing**

Overhangs are aerodynamic features that can generate significant uplift during storms. Air pressure builds beneath the soffit while a vacuum is created above the roof, essentially trying to peel the roof off the walls. Secure mechanical anchoring of the rafters to the top plate is mandatory.13  
The detailing of the fascia and soffit on a warm roof overhang is frequently misunderstood. Because the primary insulation is on top of the roof deck, the rafter tails extending into the overhang are essentially "outside" the thermal envelope. To prevent cold air from infiltrating the building through the rafter cavity, the wall insulation must continue up to meet the roof deck, and a wind barrier (breathable membrane) should be sealed between the wall and the roof's sarking layer. The space behind the fascia board must be insulated to prevent it from becoming a "cold pocket" that promotes condensation at the rafter tips.4

## **Solar Array Integration: Structural and Mechanical Prerequisites**

Designing a roof to be "solar-ready" means more than just having a flat surface. It requires a structural assessment of the "dead loads" (the permanent weight of the system) and the "live loads" (snow and wind) that the roof will endure once the PV panels are installed.

### **Loading and Rafter Sizing**

A typical PV system adds between $15 \\text{ kg/m}^2$ and $25 \\text{ kg/m}^2$ to the roof.29 While this sounds modest, it represents a permanent load that standard garden room roofs, designed only for their own weight and occasional snow, may not be equipped to handle without excessive deflection over twenty years.

| Load Source | Standard Load (kN/m2) | Solar-Ready Load (kN/m2) |
| :---- | :---- | :---- |
| Self-Weight (Rafters/Deck) | $0.20\\text{--}0.30$ | $0.20\\text{--}0.30$ |
| Insulation & EPDM | $0.10\\text{--}0.15$ | $0.10\\text{--}0.15$ |
| PV Array & Racking | $0.00$ | $0.20\\text{--}0.30$ |
| Snow Load (UK Avg) | $0.60\\text{--}1.00$ | $0.60\\text{--}1.00$ |
| **Total Design Load** | **$0.90\\text{--}1.45$** | **$1.10\\text{--}1.75$** |

Note: $1kN/m^2 \\approx 100kg/m^2$. Source: 28  
For a 3m to 4m span, $47 \\times 150\\text{mm}$ C24 rafters at 400mm centers are generally the minimum requirement for a solar-ready warm roof. If the span exceeds 4m, or if a ballasted system is planned (which can add $50 \\text{ kg/m}^2$ or more), $47 \\times 200\\text{mm}$ joists or "sistering" (attaching two joists together) may be necessary.14

### **Mechanical Fixing Systems for EPDM Warm Roofs**

The primary challenge of solar on EPDM is making a structural connection without creating a leak. There are three main approaches used in the UK market:

1. **Ballasted Systems:** These use weighted trays or concrete blocks to hold the panels in place. While they avoid roof penetrations, the sheer weight often exceeds the structural capacity of a lightweight timber garden room and can cause the EPDM to compress the PIR insulation beneath it, leading to water ponding.7  
2. **Bonded/Glued Systems:** Lightweight frames are glued to the EPDM. This is risky, as wind uplift can peel the EPDM away from the insulation. This is particularly problematic in north-facing or exposed locations where wind speeds can be higher.7  
3. **Mechanical Fixings (Integrated Fixing Points):** Systems like the Nicholson Rooftrak IFP are considered the gold standard. These are stainless steel anchor points that are bolted through the insulation and decks directly into the rafters. The anchor is factory-fitted with an EPDM flange that is then hot-bonded or glued to the main roof membrane. This provides a 100% waterproof seal and transfers all wind and snow loads directly into the building's timber frame.23

For a solar-ready project, the Rooftrak IFP units should be installed during the initial roof build. This allows the installer to precisely locate them over the rafters and ensure the membrane seal is integrated perfectly into the primary waterproofing layer.33

## **Hygrothermal Risks of North-Facing Orientations**

The north-facing aspect of the 50cm overhang and the roof slope itself introduces a specific set of moisture management risks. In the northern hemisphere, north-facing surfaces receive significantly less direct solar radiation. This is not merely an issue for solar energy generation; it is a critical building science concern because solar radiation provides "drying energy" that helps evaporate moisture that has accumulated within the building fabric.37

### **The Lack of Solar Drying and Condensation Risk**

On a south-facing roof, the heat from the sun creates a "vapor drive" that pushes moisture toward the cooler exterior. On a north-facing roof, the surface stays colder for longer, particularly in the UK’s damp winter months. This increases the "time of wetness" for the EPDM and the timber beneath it. If internal moisture penetrates the VCL, it is far less likely to be driven out by solar heat, potentially leading to a gradual accumulation of moisture—a phenomenon known as "interstitial moisture build-up".37  
To mitigate this, the north-facing garden room requires:

* **A High-Resistance VCL:** A foil-backed bitumen membrane or a high-gauge polyethylene VCL with all joints taped using specialist airtightness tapes.2  
* **Breathable Membranes:** The use of a Class W1 (water-resistant but vapor-permeable) membrane on the exterior of the walls and above the roof deck (but below the insulation in some designs) to allow any incidental moisture to escape.39  
* **Effective Ventilation:** While the warm roof itself is unventilated, the external cladding must be fitted onto battens to create a 25mm to 38mm air gap. This "rainscreen" allows air to circulate behind the cladding, carrying away moisture and protecting the structural sheathing from damp.39

### **Microclimate and the 50cm Overhang**

The 50cm overhang will create a permanent shadow on the north wall of the garden room. This microclimate is prone to algae growth and dampness. Ensuring that the breathable membrane is lapped correctly at the eaves and that the soffit is constructed from moisture-resistant materials (such as treated softwood or fiber-cement board) is essential to prevent rot at the wall-to-roof junction.39

## **Regulatory Compliance and Permitted Development**

In England and Wales, garden rooms are typically built under Permitted Development rights, which impose strict height limits. If the building is within 2 meters of a boundary, the maximum eaves height must be no more than 2.5 meters.3

### **The 2.5m Height Conflict**

A warm roof build-up is inherently thicker than a cold roof because the insulation sits on top of the rafters rather than between them. Managing this thickness while achieving a habitable internal ceiling height and staying under 2.5m is the primary design hurdle.

| Layer | Standard Depth (mm) | Slimline Strategy (mm) |
| :---- | :---- | :---- |
| Floor Base & Joists | $150\\text{--}200$ | $100$ (using steel/concrete slab) |
| Internal Ceiling Height | $2100$ | $2050$ (minimum for doors) |
| Structural Rafters | $150$ | $125$ (using C24 timber) |
| Roof Decks ($2 \\times 18\\text{mm}$) | $36$ | $18$ (using single deck) |
| PIR Insulation (Part L) | $120\\text{--}150$ | $100$ (Hybrid: PIR between/above) |
| EPDM & Fall ($1:40$) | $50$ | $40$ |
| **Total Height** | **$2606\\text{--}2636$** | **$2433$** |

Source: 3  
To achieve "solar readiness" within these limits, a "hybrid" roof is often used. This involves placing roughly half of the insulation between the rafters (with a 50mm ventilated gap above it, or fully filled with a VCL) and the other half above the rafters. This reduces the height added above the deck but requires careful Condensation Risk Analysis (CRA) to ensure the dew point doesn't fall within the timber rafters.6

### **MCS and Solar Planning Rules**

For solar panels on flat roofs, UK planning rules state they should not protrude more than 600mm above the highest part of the roof.43 Furthermore, the Microgeneration Certification Scheme (MCS) recommends an "edge zone" setback of 0.5m to 1m on flat roofs to prevent wind turbulence from lifting the panels. On a small garden room, this can significantly reduce the available area for PV modules.34

## **Conclusions and Technical Recommendations**

The successful delivery of a solar-ready, north-facing garden room with a 50cm overhang requires an uncompromising approach to both structural and thermal detailing. The warm roof system is the most robust choice, provided the material selections and junction details are engineered to handle the unique stresses of the project.  
For the insulation strategy, PIR remains the optimal choice for the roof to maintain height compliance, but it must be specified with a high compressive strength or protected by a structural deck to support future PV loads.8 The structural junction at the wall should utilize a double top plate and C24 rafters at 400mm centers to ensure a stable load path for the $25 \\text{ kg/m}^2$ dead load of a solar array.14  
To manage the hygrothermal risks associated with the north-facing aspect, the "plugging" of rafter voids at the wall plate is mandatory to eliminate thermal bridging and potential rot.4 The 50cm overhang must be mechanically tied to the wall plates with structural screws to resist wind uplift.13 Finally, for true "solar readiness," pre-installing mechanical fixing points such as the Nicholson Rooftrak IFP is recommended, as it preserves the integrity of the EPDM membrane while providing a direct structural connection to the timber frame.23 By adhering to these high-performance standards, the garden room will remain a thermally efficient and structurally sound space capable of supporting renewable energy generation for decades to come.

#### **Works cited**

1. Super-Insulated Garden Room \- The Timber Cooperative, accessed March 8, 2026, [https://timber.coop/project/garden-room-project/](https://timber.coop/project/garden-room-project/)  
2. Roof structure \- Garden Office Guide, accessed March 8, 2026, [https://www.gardenofficeguide.co.uk/construction/roof-structure/](https://www.gardenofficeguide.co.uk/construction/roof-structure/)  
3. Garden room roof design & the 2.5m rule, accessed March 8, 2026, [https://selfbuildgardenoffices.co.uk/garden-room-roof-design-the-2-5m-rule/](https://selfbuildgardenoffices.co.uk/garden-room-roof-design-the-2-5m-rule/)  
4. Warm Flat Roof Fascia Detail | RJ Evans Flat Roofing Limited, accessed March 8, 2026, [https://www.rjevansroofing.com/blog/warm-flat-roof-fascia-detail/](https://www.rjevansroofing.com/blog/warm-flat-roof-fascia-detail/)  
5. Garden Room Insulation Guide, accessed March 8, 2026, [https://pmggardenrooms.com/blog/garden-room-insulation-guide/](https://pmggardenrooms.com/blog/garden-room-insulation-guide/)  
6. Different Types of Roof Construction \- Kingspan, accessed March 8, 2026, [https://www.kingspan.com/kz/en/knowledge-articles/different-types-of-roof-construction/](https://www.kingspan.com/kz/en/knowledge-articles/different-types-of-roof-construction/)  
7. Fixing solar panels to membrane roofs \- Nicholson Roof Products, accessed March 8, 2026, [https://www.nicholsonsts.com/articles/fixing-solar-panels-to-membrane-roofs/](https://www.nicholsonsts.com/articles/fixing-solar-panels-to-membrane-roofs/)  
8. Understanding the Compressive Strength of Insulants (and Why It ..., accessed March 8, 2026, [https://www.taperedplus.co.uk/understanding-the-compressive-strength-of-insulants-and-why-it-matters-for-flat-roof-balconies-terraces/](https://www.taperedplus.co.uk/understanding-the-compressive-strength-of-insulants-and-why-it-matters-for-flat-roof-balconies-terraces/)  
9. Commercial Roofing Insulation \- Elevate, accessed March 8, 2026, [https://www.holcimelevate.com/us-en/roofing/insulation](https://www.holcimelevate.com/us-en/roofing/insulation)  
10. Thermal Insulation \- Sika, accessed March 8, 2026, [https://www.sika.com/en/construction/roof-systems/thermal-insulation.html](https://www.sika.com/en/construction/roof-systems/thermal-insulation.html)  
11. How To Build A Warm Roof From Start To Finish | Quick Simple Guide. \- YouTube, accessed March 8, 2026, [https://www.youtube.com/watch?v=NPVgkmrcOYg](https://www.youtube.com/watch?v=NPVgkmrcOYg)  
12. Warm roof design detail help? \- Green Building Forum, accessed March 8, 2026, [https://www.greenbuildingforum.co.uk/newforum/comments.php?DiscussionID=7380](https://www.greenbuildingforum.co.uk/newforum/comments.php?DiscussionID=7380)  
13. How to Build a Garden Room Frame \- Timber Frame Construction, accessed March 8, 2026, [https://selfbuildgardenroom.com/frame/](https://selfbuildgardenroom.com/frame/)  
14. Garden Room Timber Frame Guide: UK Sizes, Spacing & Construction Standards, accessed March 8, 2026, [https://outbuildingplanner.co.uk/blog/garden-room-timber-frame-uk](https://outbuildingplanner.co.uk/blog/garden-room-timber-frame-uk)  
15. Celotex vs Kingspan | Cost & Performance Breakdown, accessed March 8, 2026, [https://ukflatroofing.com/knowledge-hub/celotex-vs-kingspan-which-is-better](https://ukflatroofing.com/knowledge-hub/celotex-vs-kingspan-which-is-better)  
16. XPS vs. PIR insulation: Understanding the differences for your project \- Celotex, accessed March 8, 2026, [https://celotex.co.uk/blog/xps-vs-pir-insulation](https://celotex.co.uk/blog/xps-vs-pir-insulation)  
17. Solar panels on EPDM roof with gluing, accessed March 8, 2026, [https://www.raulibrackets.com/news-and-articles/solar-panels-on-epdm-roof-with-gluing](https://www.raulibrackets.com/news-and-articles/solar-panels-on-epdm-roof-with-gluing)  
18. Garden building \- warm roof but with insulation between the joists? : r/DIYUK \- Reddit, accessed March 8, 2026, [https://www.reddit.com/r/DIYUK/comments/1nh7085/garden\_building\_warm\_roof\_but\_with\_insulation/](https://www.reddit.com/r/DIYUK/comments/1nh7085/garden_building_warm_roof_but_with_insulation/)  
19. What's Under Your Solar Panels? \- OMG Roofing Products, accessed March 8, 2026, [https://www.omgroofing.com/wp-content/uploads/2024/03/OMGRoofing\_Vol11\_Issue4.pdf](https://www.omgroofing.com/wp-content/uploads/2024/03/OMGRoofing_Vol11_Issue4.pdf)  
20. Foamular 150 vs 250: Which is Best for Your Project? – Roofing4US, accessed March 8, 2026, [https://roofing4us.com/blogs/insulation-guides-news/foamular-150-vs-250](https://roofing4us.com/blogs/insulation-guides-news/foamular-150-vs-250)  
21. Warm Roof Insulation | ROCKWOOL Group, accessed March 8, 2026, [https://www.rockwool.com/group/products-and-applications/roof-insulation/flat-roof-insulation/warm-roof-insulation/](https://www.rockwool.com/group/products-and-applications/roof-insulation/flat-roof-insulation/warm-roof-insulation/)  
22. What Are The Differences Between PIR and Wood Fibre Insulation? – Can I Just Ask? – Ep.10 \- Back to Earth, accessed March 8, 2026, [https://www.backtoearth.co.uk/news/what-are-difference-between-pir-and-wood-fibre-insulation-can-i-just-ask-ep-10/](https://www.backtoearth.co.uk/news/what-are-difference-between-pir-and-wood-fibre-insulation-can-i-just-ask-ep-10/)  
23. Solar Panel Brackets: Top Choices for 2026 | E-Verve Energy, accessed March 8, 2026, [https://e-verveenergy.co.uk/library-post/solar-panel-brackets-top-choices-for-2026/](https://e-verveenergy.co.uk/library-post/solar-panel-brackets-top-choices-for-2026/)  
24. technical data sheet \- STEICO, accessed March 8, 2026, [https://www.steico.com/fileadmin/user\_upload/Public\_Docs/EUR\_en/EUR\_en\_Technical\_Data\_Sheets/1.\_Product\_information\_wood\_fibre\_insulation/STEICO\_technical-data-sheet\_base\_EUR\_en\_i.pdf](https://www.steico.com/fileadmin/user_upload/Public_Docs/EUR_en/EUR_en_Technical_Data_Sheets/1._Product_information_wood_fibre_insulation/STEICO_technical-data-sheet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)  
25. How To: Build Your Own Garden Room \- Wood Green Timber, accessed March 8, 2026, [https://www.woodgreentimber.com/how-to-build-your-own-garden-room](https://www.woodgreentimber.com/how-to-build-your-own-garden-room)  
26. Warm deck roof/timber frame wall junction: VCL placement, accessed March 8, 2026, [https://www.greenbuildingforum.co.uk/newforum/comments.php?DiscussionID=16078](https://www.greenbuildingforum.co.uk/newforum/comments.php?DiscussionID=16078)  
27. 5.6.4 Roof Sheathing 5.6.5 Roof Overhangs, accessed March 8, 2026, [https://www.uop.edu.jo/PDF%20File/uop%20uop%20\[Architecture\_Ebook\]\_Residential\_Structural\_Design\_Guide\_2000\_-\_PDR-20490\_Part125.pdf](https://www.uop.edu.jo/PDF%20File/uop%20uop%20[Architecture_Ebook]_Residential_Structural_Design_Guide_2000_-_PDR-20490_Part125.pdf)  
28. Can My Roof Support Solar Panels? Complete Structural Assessment Guide (2025), accessed March 8, 2026, [https://solartechonline.com/blog/can-roof-support-solar-panels-guide/](https://solartechonline.com/blog/can-roof-support-solar-panels-guide/)  
29. Factory Roof Weight Load for Solar Panels: Complete UK Structural Guide 2026, accessed March 8, 2026, [https://solarpanelsforfactories.co.uk/factory-roof-weight-load-solar-panels](https://solarpanelsforfactories.co.uk/factory-roof-weight-load-solar-panels)  
30. Building Regulations for solar panels \- Electrical Innovations, accessed March 8, 2026, [https://elec-inn.co.uk/what-are-the-building-regulations-for-solar-panels/](https://elec-inn.co.uk/what-are-the-building-regulations-for-solar-panels/)  
31. How to Determine if Your Roof Needs Structural Reinforcement for Solar: 5-Step Guide 2026, accessed March 8, 2026, [https://www.bostonsolar.us/solar-blog-resource-center/blog/how-to-determine-if-your-roof-needs-structural-reinforcement-for-solar-5-step-gu/](https://www.bostonsolar.us/solar-blog-resource-center/blog/how-to-determine-if-your-roof-needs-structural-reinforcement-for-solar-5-step-gu/)  
32. Can You Put Solar Panels on an EPDM Roof? \- Roper Roofing, accessed March 8, 2026, [http://roperroofingandsolar.com/epdm-roof/can-you-put-solar-panels-on-epdm-roof/](http://roperroofingandsolar.com/epdm-roof/can-you-put-solar-panels-on-epdm-roof/)
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
