wisogetnid/garden-room/research/suppliers/jackodur-suppliers.md

# **Technical Analysis of Jackodur Atlas Foundation Systems: Supplier Landscape and Logistical Optimization for the Isle of Wight and Southern United Kingdom**

The construction of high-performance building envelopes in the contemporary regulatory environment requires a sophisticated approach to sub-structure thermal management. In the United Kingdom, the shift toward the Future Homes Standard and the increasing prevalence of Passivhaus-certified designs have elevated the importance of foundation systems that eliminate thermal bridging while providing structural stability. The Jackodur Atlas system, a proprietary solution developed by Jackon Insulation and now part of the international BEWI Group, represents a market-leading integration of formwork and extruded polystyrene (XPS) insulation.1 This report provides an exhaustive evaluation of the supplier infrastructure supporting the Jackodur Atlas system, specifically focused on the logistical constraints of the Isle of Wight and the broader Southern UK coastal region. The analysis examines the intersection of material science, maritime logistics, and the specific needs of the self-builder market for small-scale projects such as premium garden rooms.

## **The Structural and Thermal Evolution of the Jackodur Atlas System**

The Jackodur Atlas foundation system is founded upon the chemical and mechanical advantages of extruded polystyrene (XPS). Since the acquisition of Jackon Insulation by the BEWI Group in October 2022, the system has been positioned within a larger framework of sustainability and circular economy principles, ensuring that the production of raw materials and the end-of-life recycling of the components align with modern environmental mandates.1 The system is fundamentally designed to provide a continuous, high-performance thermal break between the building's floor slab and the ground, utilizing an innovative interconnection system that facilitates rapid installation without the necessity of traditional timber shuttering.3  
For the self-builder or the developer of a small-scale garden room, the choice of XPS over expanded polystyrene (EPS) is often dictated by the requirement for moisture resistance and long-term compressive strength. XPS is manufactured through a process of melting polystyrene beads and injecting carbon dioxide, resulting in a closed-cell structure that is virtually impervious to water.2 Data indicates that while standard EPS can absorb up to 10% moisture over its lifespan—leading to a potential 50% degradation in its insulative properties—XPS from the BEWI Jackodur range maintains water absorption below 1% even when subjected to high pressure or frequent freeze-thaw cycles.2 This characteristic is of paramount importance for construction on the Isle of Wight, where coastal humidity and fluctuating water tables can compromise the integrity of less robust materials.

## **Technical Performance and Compressive Gradations**

The Jackodur Atlas system is available in several compressive strength iterations, which allow for precise engineering according to the load-bearing requirements of the structure. For lightweight garden rooms, the Atlas 300 grade is the industry standard, whereas more substantial residential projects may require the Atlas 500 or 700 grades to satisfy the Serviceability Limit State (SLS) requirements.4

| Grade Specification | Compressive Stress (10% Deformation) | 50-Year Design Load (Deformation \< 2%) | Thermal Conductivity (λD) |
| :---- | :---- | :---- | :---- |
| **Atlas 300** | $300 kPa$ | $130 kPa$ | $0.034 \- 0.036 W/(m·K)$ |
| **Atlas 500** | $500 kPa$ | $180 kPa$ | $0.034 \- 0.038 W/(m·K)$ |
| **Atlas 700** | $700 kPa$ | $250 kPa$ | $0.034 \- 0.038 W/(m·K)$ |
| 4 |  |  |  |

The thermal performance of the system is equally customizable. $U$-values achieved by the Atlas system range from $0.15 W/(m^2K)$ with a $160 mm$ surface element thickness to as low as $0.10 W/(m^2K)$ or $0.11 W/(m^2K)$ with a $280 mm$ or $320 mm$ thickness, respectively.5 For a garden room intended for year-round occupancy, these values ensure a thermal mass that retains heat effectively, translating into significantly reduced energy consumption for heating and cooling.8

## **Proximity and Geographic Distribution: Mapping Suppliers Near the Isle of Wight**

Logistical efficiency for an Isle of Wight project is heavily dependent on the proximity of the supplier to the key ferry terminals in Southampton, Portsmouth, and Lymington. The cost of maritime transport often scales with the distance traveled on the mainland, making a "closer is better" strategy essential for maintaining project budgets.

## **Renders World / Renders Direct (Southampton)**

Situated in Southampton, Renders World represents the most geographically proximal official distributor for Atlas products.9 As a premier builders’ superstore with a specialized focus on External Wall Insulation (EWI) and foundation systems, they are uniquely positioned to serve the Isle of Wight market via the Red Funnel ferry route.9 Their specialization in XPS foundation boards—ranging from $10 mm$ to $200 mm$ in thickness—allows for immediate availability of components that might otherwise require long lead times from general merchants.9  
The reliability of Renders World is underscored by their 4.7 Trustpilot rating, with specific customer feedback citing swift stock verification and rapid dispatch.11 For the self-builder, their ability to provide technical support for both trade and homeowners is a significant advantage, particularly when navigating the complexities of a first-time insulated raft foundation installation.9

## **Civils Store (Southern Branch)**

The Civils Store operates as an independent, expert supplier of civil engineering and groundworks materials, with a dedicated Southern depot located at Area 41, The Vinery, Poling, West Sussex (BN18 9PY).13 While slightly further from the immediate Southampton ferry terminals than Renders World, their location remains highly accessible for the Portsmouth (Wightlink) ferry route, which serves Fishbourne on the Isle of Wight.  
Civils Store is a recognized partner for BEWI and stocks the Jackodur Atlas system.1 Their reliability is reinforced by their recognition as the "Civils Merchant of the Year" at the 2024 Builders Merchants Awards.13 A unique aspect of their business model is the profit-sharing scheme, where 20% of profits are shared with all employees every three months; the company suggests this fosters a higher level of customer service and technical investment from their staff.13 This "favored supplier" ethos is particularly relevant for small projects where personalized service can prevent costly ordering errors.

## **Johnson’s Insulation Supplies (Eastleigh and West Sussex)**

Johnson’s Insulation Supplies has provided thermal, acoustic, and fire protection materials across the South since 1984\.15 Their Eastleigh depot (SO50 6RS) is located just north of Southampton, offering an excellent geographic compromise for projects sourcing materials for the island.  
A critical service provided by Johnson’s at their Hampshire and West Sussex bases is the "cut-to-size" facility.15 Using industry-standard machinery, they can provide precision-cut insulation materials to meet specific project specifications, which is a vital resource for garden rooms with non-standard footprints or intricate detailing.15 While their primary focus is often on general insulation boards (PIR, EPS, Phenolic), they maintain partnerships with leading manufacturers and offer rapid collection or delivery within their primary target areas of Hampshire and Sussex.15

## **ICF Southern (West Sussex)**

Based in West Sussex, ICF Southern specializes in the supply of insulated concrete formwork and associated materials.16 While they are primarily recognized as authorized distributors for Nudura products, their extensive experience in the Southern UK construction market—including specific projects on the Isle of Wight—makes them a valuable technical resource.16 They provide not only materials but also specialized training through their ICF Training Academy, which offers intensive courses in installation techniques for various ICF-adjacent systems.16

## **Economic Evaluation: Pricing Structures and System Costs**

The financial commitment required for a Jackodur Atlas foundation is typically viewed as a "system cost" rather than a simple material purchase. This is because the price encompasses not only the insulation but also the formwork, the reduction in labor, and the elimination of off-site waste.

## **System-Level Pricing and Quotation Requirements**

For the Jackodur Atlas Raft Foundation System, pricing typically starts at approximately $£40/m^2$.5 This baseline cost is subject to variation based on the thickness of the insulation required and the specific engineering demands of the site. To obtain an accurate quote, suppliers generally require a layout plan of the proposed concrete slab, the required concrete thickness (typically $200 mm$ to $250 mm$), and the target $U$-value.1

| Component / System | Pricing Detail (Estimates) | Supplier Reference |
| :---- | :---- | :---- |
| **Jackodur Atlas Raft System** | From $£40.00 / m^2$ | 5 |
| **Jackodur CFR 10mm XPS Board** | $£5.99 (Inc. VAT) / Sheet$ | 18 |
| **Jackodur CFR 6mm XPS Board** | $£4.79 (Inc. VAT) / Sheet$ | 18 |
| **Board-Fix Adhesive (290ml)** | $£16.79 (Inc. VAT)$ | 19 |
| **Full Pallet (200 Boards) 10mm** | $£1198.20 (Inc. VAT)$ | 18 |
| **Half Pallet (100 Boards) 6mm** | $£428.40 (Inc. VAT)$ | 18 |
| 18 |  |  |

The transition to the BEWI ownership has also brought price adjustments within the supply chain. For instance, in early 2025, various suppliers notified the market of price increases ranging from 6% to 12% across products like ClayMaster and generic insulation ranges due to energy surcharges and manufacturing cost escalations.13 Prospective builders should account for these market fluctuations when finalizing their budgets.

## **Economic Benefits of the "Zero-Waste" System**

One of the most profound third-order effects of the Atlas system for a small project is the mitigation of waste disposal costs. On the Isle of Wight, skip hire and construction waste management are expensive due to the necessity of transporting waste back to the mainland for processing. The Atlas system is supplied pre-cut and numbered to match the specific floor plan of the garden room, ensuring that only the necessary materials are delivered to the site.4 This "precision-cut" approach not only saves on material costs but also reduces the physical footprint of the construction site, a critical factor for small residential gardens where space is at a premium.

## **Logistical Strategy for the Isle of Wight: Maritime and Overland Transport**

The "last mile" of delivery for a garden room on the Isle of Wight involves significant logistical friction. The selection of a supplier must therefore account for their delivery fleet's capability and their integration with pallet networks.

## **Merchant Delivery Policies and Ferry Surcharges**

Merchants like Jewson, which have a presence both on the mainland and the island, offer free delivery for online orders over $£200$ (ex. VAT) for guest users and $£150$ for account customers.23 However, as specialized items like the Jackodur Atlas are often not held in local island stock, they may be subject to "non-standard delivery area" fees.23  
For larger orders, specialized freight partners like Breakwells or Barrington Freight offer dedicated logistics to the Isle of Wight. Breakwells, for instance, provides a "No Transhipment Service," guaranteeing that the goods stay on the same vehicle for the entire journey from the warehouse to the final destination on the island.24 This is particularly important for XPS boards, which can suffer edge damage if handled excessively during transit.

## **Pallet Network Costs and Efficiency**

For the self-builder sourcing from more distant specialist suppliers, such as ICF Building Solutions in Yorkshire, the pallet network is the most common delivery mechanism.

| Logistics Provider | Load Specification | Service Type | Price Estimate (Exc. VAT) |
| :---- | :---- | :---- | :---- |
| **National Pallets** | $1000kg$ Full Pallet | 2-Day Standard | $£49.80$ |
| **National Pallets** | $500kg$ Half Pallet | 2-Day Standard | $£44.80$ |
| **National Pallets** | $250kg$ Quarter Pallet | 2-Day Standard | $£37.80$ |
| **Defenda Couriers** | Dedicated Vehicle | Same-Day Pallet | $\< £15.00 / Pallet$ (Volume dependent) |
| 25 |  |  |  |

It is important to note that many couriers apply an "island surcharge" for the Isle of Wight, which can range from $£10$ to $£50$ depending on the carrier and the size of the consignment.27 Standard small parcels (under $10kg$) may be sent via Royal Mail or Evri for as little as $£5.36$ to $£6.95$, but these are only suitable for small accessories like adhesives or sealing tapes.27

## **Reliability, Trust, and Professional Validation**

In the construction sector, reliability is measured through third-party certification and institutional acceptance. The Jackodur Atlas system possesses several key credentials that offer security to the self-builder.

## **BBA and NHBC Acceptance**

The system is covered by BBA Certificate 20/5812, which validates its performance in the UK's unique climatic and regulatory environment.2 Furthermore, the BEWI Jackodur Atlas system has achieved NHBC Acceptance, which simplifies the insurance and warranty process for residential builds.2 This is a major point of difference compared to some generic raft systems, as it provides construction companies and individual builders with a heightened level of confidence during the specification phase.28

## **Performance in Sustainable Construction**

The Atlas system's reliability in high-performance builds is demonstrated by its certification by the Passive House Institute.3 This certification indicates that the system has been rigorously tested for its ability to eliminate thermal bridges, a critical requirement for achieving "A" ratings in energy efficiency.8 For the garden room project, this means the foundation will perform consistently over its 50-year design life without the "thermal sagging" or moisture ingress that can plague traditional concrete-on-EPS foundations.2

## **Support for the Self-Builder: Navigating the Small Project**

The self-builder often lacks the extensive plant equipment and multi-disciplinary teams of large contractors. The Jackodur Atlas system is engineered to mitigate these gaps through its "simple inter-connection system".3

## **Pre-Cut Customization and Site Management**

For a garden room, the "JRS System" (standard size elements) or the "Full Bespoke System" can be selected based on the complexity of the footprint.31 The full bespoke system is particularly well-suited for self-builders as it includes a custom installation plan and pre-cut parts that require no specialized tools for assembly.4 The "tongue-and-groove" joints act as a guide, reducing the margin for error during the initial layout phase.3

## **Technical Support Infrastructure**

BEWI and its distributors provide a comprehensive support network, including:

1. **Training Manuals:** Detailed modules covering site preparation, rebar installation, and concrete pouring.31  
2. **Dedicated Sales Teams:** National experts available for technical presentations and specific advice for individual self-build projects.32  
3. **On-Site Practical Support:** Many specialist suppliers, including ICF Building Solutions, offer turn-key solutions that include on-site guidance to ensure the integrity of the concrete pour.5

## **Conclusion: Strategic Supplier Selection for the Isle of Wight**

For the construction of an insulated garden room on the Isle of Wight, the optimal supplier choice is a function of logistical proximity and the depth of technical support.  
**Renders World (Southampton)** emerges as the primary recommendation for immediate proximity and established reliability in the Southern region. Their location significantly minimizes mainland haulage and maximizes the efficiency of the Red Funnel ferry crossing. Their expertise in Atlas products and high customer satisfaction ratings suggest a high degree of trust for the small-scale builder.9  
**Civils Store (Southern)** represents the best choice for those requiring a broad range of groundworks materials beyond just the insulation system. Their "Merchant of the Year" status and expert local knowledge provide a safety net for self-builders navigating the complexities of civil engineering.13  
**ICF Building Solutions** remains the premier choice for the self-builder who requires a "hand-holding" approach. Despite their northern base, their turn-key design and engineering support for the Jackodur Atlas raft system can be a decisive factor in the success of a first-time build, potentially offsetting the higher logistical costs through the prevention of on-site errors.5  
The implementation of the Jackodur Atlas system on the Isle of Wight is a technically sound and economically defensible strategy. By integrating thermal insulation and formwork into a single, moisture-resistant XPS system, the builder ensures a structure that is both energy-efficient and resilient to the coastal environment, satisfying the most stringent modern building standards while simplifying the construction process for the self-builder.

#### **Works cited**

1. Thermal insulation for structural use. \- Civils Store, accessed March 19, 2026, [https://www.civilsstore.co.uk/content/large/products/6929847013e461.04760525.pdf](https://www.civilsstore.co.uk/content/large/products/6929847013e461.04760525.pdf)  
2. Jackodur® Atlas Foundation System | BEWI, accessed March 19, 2026, [https://bewi.com/products/jackodur-atlas?lang=en-gb](https://bewi.com/products/jackodur-atlas?lang=en-gb)  
3. JACKODUR® Atlas floor slab insulation system, accessed March 19, 2026, [https://www.jackon-insulation.com/applications/detail/jackodur-atlas-floor-slab-insulation-system](https://www.jackon-insulation.com/applications/detail/jackodur-atlas-floor-slab-insulation-system)  
4. JACKODUR Atlas \- JACKON Insulation, accessed March 19, 2026, [https://www.jackon-insulation.com/downloads-service/download/jackodur-atlas](https://www.jackon-insulation.com/downloads-service/download/jackodur-atlas)  
5. Insulated Raft Foundations • Jackodur Atlas® • Passivhaus \- ICF Building Solutions, accessed March 19, 2026, [https://www.icfbuildingsolutions.co.uk/raft-foundation/](https://www.icfbuildingsolutions.co.uk/raft-foundation/)  
6. JACKODUR Atlas Foundation Insulation System \- BEWI, accessed March 19, 2026, [https://bewi.com/wp-content/uploads/2023/11/Jackodur-Atlas-BBA-5812ps1i2.pdf](https://bewi.com/wp-content/uploads/2023/11/Jackodur-Atlas-BBA-5812ps1i2.pdf)  
7. JACKODUR® Atlas: Quick and affordable foundation insulation with click system, accessed March 19, 2026, [https://stedenbouw.nl/en/general/jackodur-atlas-quick-and-affordable-foundation-insulation-with-click-system/](https://stedenbouw.nl/en/general/jackodur-atlas-quick-and-affordable-foundation-insulation-with-click-system/)  
8. JACKON by BEWI showcases the future of building \- Architects' Datafile, accessed March 19, 2026, [https://www.architectsdatafile.co.uk/news/jackon-by-bewi-showcases-the-future-of-building/](https://www.architectsdatafile.co.uk/news/jackon-by-bewi-showcases-the-future-of-building/)  
9. Renders World, accessed March 19, 2026, [https://renders-world.co.uk/](https://renders-world.co.uk/)  
10. accessed March 19, 2026, [https://www.google.com/search?q=Renders+World+Southampton+reviews+Trustpilot+Google](https://www.google.com/search?q=Renders+World+Southampton+reviews+Trustpilot+Google)  
11. Renders Direct Reviews | Read Customer Service Reviews of rendersdirect.co.uk, accessed March 19, 2026, [https://www.trustpilot.com/review/rendersdirect.co.uk](https://www.trustpilot.com/review/rendersdirect.co.uk)  
12. Renders Direct Reviews | Read Customer Service Reviews of rendersdirect.co.uk | 4 of 7, accessed March 19, 2026, [https://ca.trustpilot.com/review/rendersdirect.co.uk?page=4](https://ca.trustpilot.com/review/rendersdirect.co.uk?page=4)  
13. Civils Store \- Civil Engineering Materials, accessed March 19, 2026, [https://www.civilsstore.co.uk/](https://www.civilsstore.co.uk/)  
14. Civils Store Southern, accessed March 19, 2026, [https://www.civilsstore.co.uk/depot-locations/civils-store-southern/](https://www.civilsstore.co.uk/depot-locations/civils-store-southern/)  
15. Johnson's Insulation Supplies, accessed March 19, 2026, [https://www.johnsonsinsulation.com/](https://www.johnsonsinsulation.com/)  
16. Reliable insulated concrete formwork | ICF Southern, accessed March 19, 2026, [https://icfsouthern.co.uk/about-icf-southern/](https://icfsouthern.co.uk/about-icf-southern/)  
17. ICF Southern, accessed March 19, 2026, [https://icfsouthern.co.uk/](https://icfsouthern.co.uk/)  
18. Jackoboard Jackodur \- Pro Tiler Tools, accessed March 19, 2026, [https://www.protilertools.co.uk/categories/tile-backer-boards/jackoboard/jackoboard-jackodur](https://www.protilertools.co.uk/categories/tile-backer-boards/jackoboard/jackoboard-jackodur)  
19. JACKOBOARD Jackodur CFR 10mm XPS Insulation Board 1200 x 600mm, accessed March 19, 2026, [https://www.flooringmaterials.co.uk/product/jackoboard-jackodur-cfr-10mm-xps-insulation-board-1200-x-600mm](https://www.flooringmaterials.co.uk/product/jackoboard-jackodur-cfr-10mm-xps-insulation-board-1200-x-600mm)  
20. JACKOBOARD Jackodur CFR 10mm XPS Insulation Board 1200 x 600mm Full Pallet (200 Boards) | Flooring Materials, accessed March 19, 2026, [https://www.flooringmaterials.co.uk/product/jackoboard-jackodur-cfr-10mm-xps-insulation-board-1200-x-600mm-full-pallet--200-boards-](https://www.flooringmaterials.co.uk/product/jackoboard-jackodur-cfr-10mm-xps-insulation-board-1200-x-600mm-full-pallet--200-boards-)  
21. Jackon \- Brands \- Trade Tiling, accessed March 19, 2026, [https://www.tradetiling.co.uk/brands/jackon](https://www.tradetiling.co.uk/brands/jackon)  
22. Delivery \- Civils Store, accessed March 19, 2026, [https://www.civilsstore.co.uk/delivery/](https://www.civilsstore.co.uk/delivery/)  
23. Jewson online delivery & collection information, accessed March 19, 2026, [https://www.jewson.co.uk/need-help/delivery-collection-information](https://www.jewson.co.uk/need-help/delivery-collection-information)  
24. Isle of Wight Courier, Haulage & Shipping Services \- Breakwells, accessed March 19, 2026, [https://breakwells.com/isle-of-wight/](https://breakwells.com/isle-of-wight/)  
25. Southampton Couriers \- Express Same Day Parcel & Pallet Delivery, accessed March 19, 2026, [https://www.defendacouriers.co.uk/courier-service/same-day-delivery/southampton-couriers-express-same-day-courier-delivery-of-parcels-pallets/](https://www.defendacouriers.co.uk/courier-service/same-day-delivery/southampton-couriers-express-same-day-courier-delivery-of-parcels-pallets/)  
26. Send a full pallet from £49.80 exc VAT \- National Pallets, accessed March 19, 2026, [https://www.nationalpallets.co.uk/content/pallet-sizes/full-pallet](https://www.nationalpallets.co.uk/content/pallet-sizes/full-pallet)  
27. Cheap Parcel Delivery And Sending Mail To The Isle Of Wight 2026, accessed March 19, 2026, [https://www.isleofwightguru.co.uk/cheap-parcel-delivery-and-sending-mail-to-the-isle-of-wight.html](https://www.isleofwightguru.co.uk/cheap-parcel-delivery-and-sending-mail-to-the-isle-of-wight.html)  
28. BEWI achieves NHBC-acceptance for its Jackodur® Atlas Foundation System, accessed March 19, 2026, [https://architectsdatafile.co.uk/news/bewi-achieves-nhbc-acceptance-for-its-jackodur-atlas-foundation-system/](https://architectsdatafile.co.uk/news/bewi-achieves-nhbc-acceptance-for-its-jackodur-atlas-foundation-system/)  
29. JACKODUR ® Atlas \- The high performance insulation system for slabs (or platforms), accessed March 19, 2026, [https://trends.archiexpo.com/jackon-insulation/project-59334-272349.html](https://trends.archiexpo.com/jackon-insulation/project-59334-272349.html)  
30. The Pros and Cons of ICF Construction in the UK \- ThermoHouse, accessed March 19, 2026, [https://thermohouse.co.uk/blog/the-pros-and-cons-of-icf/](https://thermohouse.co.uk/blog/the-pros-and-cons-of-icf/)  
31. Insulated Raft Foundation System \- BEWI, accessed March 19, 2026, [https://bewi.com/wp-content/uploads/2023/11/BEWI-330a-KW-TrainingManual-JackobdurAtlas-WEB.pdf](https://bewi.com/wp-content/uploads/2023/11/BEWI-330a-KW-TrainingManual-JackobdurAtlas-WEB.pdf)  
32. Jackon UK \- Build It Live 2026, accessed March 19, 2026, [https://builditlive.co.uk/exhibitor/jackon-construction/](https://builditlive.co.uk/exhibitor/jackon-construction/)
