wisogetnid/garden-room/research/suppliers/window-research-and-supply.md

# **Strategic Architectural Specification of High-Performance Glazing Systems for SIPs-Based Garden Structures in Cowes, Isle of Wight**

The architectural synthesis of structural insulated panel (SIPs) technology with advanced glazing systems represents the current pinnacle of high-performance garden room design. For a project situated in Cowes, on the Isle of Wight, the environmental and regulatory context adds layers of complexity that necessitate a rigorous analytical approach to window selection. A garden room with a footprint of approximately $20\\,m^{2}$ serves as a significant thermal and structural volume, requiring a precise equilibrium between natural illumination, thermal retention, and coastal durability. This report provides an exhaustive analysis of standard window dimensions, glazing technologies—specifically comparing triple and vacuum-insulated glass (VIG)—and the local economic landscape of suppliers on the Isle of Wight, all framed within the structural requirements of the Master Plan SIPs system.

## **Structural Foundations and the Geometry of SIPs Integration**

The fundamental logic of window placement and sizing in a garden room is dictated by the structural properties of the SIPs panels themselves. The Master Plan SIPs system typically utilizes a modular width of $1200\\,\\text{mm}$ for its raw panels.1 This $1200\\,\\text{mm}$ module is the primary governing factor in achieving an optimal price-to-value ratio. When window apertures are designed to align with these modular increments, the structural integrity of the wall is preserved with minimal intervention, reducing the need for complex timber lintels and localized reinforcement that can introduce thermal bridges.3  
Standard SIPs panels are engineered as a sandwich of two Oriented Strand Board (OSB/3) facings, usually $12\\,\\text{mm}$ thick, bonded to a core of high-performance insulation such as Expanded Polystyrene (EPS) or Polyisocyanurate (PIR).1 The thermal conductivity ($\\lambda$) of the OSB/3 facings is approximately $0.13\\,W/mK$, while the foam core can achieve values as low as $0.022\\,W/mK$.1 Cutting apertures into these panels requires careful planning to ensure the load-bearing capacity is maintained, particularly for the roof loads which, in a garden room, are often supported directly by the wall panels.2

### **Modular Aperture Planning**

For a $20\\,m^{2}$ room, wall heights are generally designed to stay within a $2.4\\,\\text{m}$ to $2.5\\,\\text{m}$ range to facilitate compliance with Permitted Development rights.6 By selecting window widths that match the $1200\\,\\text{mm}$ panel width, or half-modules of $600\\,\\text{mm}$, the builder can ensure that the window reveals fit precisely between the structural splines that join the panels.1 These joining splines are themselves critical components; they are often insulated to ensure the continuity of the thermal envelope.4  
The following table details the relationship between standard SIPs dimensions and recommended window aperture sizes to maximize structural efficiency:

| SIPs Component | Standard Dimension (mm) | Recommended Window Width (mm) | Structural Rationale |
| :---- | :---- | :---- | :---- |
| Full Panel Width | 1200 | 1200 | Aligns with panel joints; minimizes OSB waste.1 |
| Half Panel Width | 600 | 600 | Ideal for smaller "ventilation" units.9 |
| Standard Height | 2400 | 1050 \- 1500 | Allows for appropriate lintel and cill space.9 |
| Panel Thickness | 125 \- 162 | N/A | Dictates the depth of the window reveal and frame.1 |

By adhering to these dimensions, the project benefits from a reduction in labor costs associated with on-site cutting and the potential for pre-manufactured apertures, which arrive on-site ready for immediate window installation.2

## **Standardization and the Acquisition of Market-Ready Window Sizes**

In the United Kingdom, the window manufacturing industry has converged around several "standard" sizes that account for the vast majority of production volume. For a garden room project, choosing these standard sizes is the most effective way to ensure ease of acquisition and the best price-to-value ratio. Custom sizes, while architecturally flexible, often incur a price premium of $20\\%$ to $50\\%$ and significantly longer lead times.12

### **Primary Window Dimensions for Garden Structures**

The proposed configuration of the garden room requires a mix of large and small windows across four elevations. Analysis of standard UK window sizes reveals several dimensions that are frequently stocked by both national and local suppliers.9

1. **Large Units (North and West Elevations):** The industry standard for a large casement window is $1200 \\times 1200\\,\\text{mm}$.10 This size is highly efficient as it utilizes the full width of a standard SIPs panel. Other common large sizes include $1200 \\times 1350\\,\\text{mm}$ and $1200 \\times 1500\\,\\text{mm}$, which provide a more vertical aesthetic.9  
2. **Small Units (East and South Elevations):** For secondary light sources and ventilation, sizes such as $600 \\times 900\\,\\text{mm}$, $915 \\times 1050\\,\\text{mm}$, and $600 \\times 1200\\,\\text{mm}$ are considered standard.9 A $600 \\times 600\\,\\text{mm}$ square unit is also widely available and cost-effective for south-facing elevations where smaller apertures help manage solar gain.9

### **Functional Typology: Casement vs. Tilt-and-Turn**

The mechanical operation of the window affects both its cost and its performance in a garden room setting. Casement windows, which open outward on side or top hinges, are the most common and economical style in the UK.12 They are versatile and available in many configurations, though they do not have a single industry-defined "standard" size, manufacturers gravitate toward the $600\\,\\text{mm}$ and $1200\\,\\text{mm}$ width modules.14  
Tilt-and-turn windows offer enhanced functionality, allowing the sash to tilt inward for secure ventilation or swing inward for easy cleaning.9 While they are typically more expensive than casements, their inward-opening nature makes them ideal for garden rooms where external space for an outward-swinging sash might be limited by landscaping or boundaries.12

| Window Type | Height (mm) | Width (mm) | Estimated Cost (Double Glazed) |
| :---- | :---- | :---- | :---- |
| Standard Casement | 1200 | 1200 | $\\pounds 300 \- \\pounds 700$.12 |
| Small Casement | 900 | 600 | $\\pounds 250 \- \\pounds 450$.10 |
| Tilt-and-Turn | 1200 | 1200 | $\\pounds 600 \- \\pounds 1,000$.12 |
| Utility/South Unit | 600 | 600 | $\\pounds 200 \- \\pounds 350$.10 |

## **Glazing Science: A Comparative Analysis of Triple and Vacuum Systems**

The requirement for triple or vacuum glazing in the garden room reflects a necessity to match the high thermal performance of the SIPs walls, which can have $U$-values as low as $0.15\\,W/m^{2}K$.5 Standard double glazing, with a typical $U$-value of $1.2$ to $1.4\\,W/m^{2}K$, often becomes the primary source of heat loss in an otherwise well-insulated structure.17

### **The Physics of Triple Glazing**

Triple glazing utilizes three panes of glass separated by two cavities, typically filled with Argon or Krypton gas. This configuration creates additional thermal barriers that reduce heat transfer through conduction and convection. Typical center-pane $U$-values for triple glazing are in the range of $0.8$ to $1.0\\,W/m^{2}K$, representing a $40\\%$ improvement over modern double glazing.17  
However, triple glazing introduces significant structural and aesthetic considerations:

1. **Massive Weight:** The addition of a third $4\\,\\text{mm}$ glass pane increases the weight of the sash by $50\\%$. This places higher stress on hinges and window hardware and may require more robust framing within the SIPs aperture.18  
2. **Profile Depth:** Triple glazed units are usually $36\\,\\text{mm}$ to $44\\,\\text{mm}$ thick, necessitating "chunkier" frames to accommodate the deep glass units.17 This can detract from the sleek, modern aesthetic often desired in garden studios.  
3. **Light Transmission:** The third pane of glass reduces the light transmission factor to approximately $71\\%$, compared to over $80\\%$ for double or vacuum glazing.18 In a north-facing window, this could result in a perceptibly darker interior.

### **The Innovation of Vacuum-Insulated Glazing (VIG)**

Vacuum-insulated glazing, such as the Fineo or LandVac systems, represents a paradigm shift in glass technology. Instead of using gas-filled cavities, VIG removes the air between two panes of glass to create a vacuum. Because a vacuum cannot conduct heat, the thermal performance is drastically improved in a unit that is remarkably thin.18  
A Fineo 8 unit is only $7.7\\,\\text{mm}$ thick yet achieves a center-pane $U$-value of $0.7\\,W/m^{2}K$, outperforming many 36mm triple glazed units.18 Because it is as thin as traditional single glazing, it can be fitted into much slimmer, more elegant frames.17

| Performance Metric | Triple Glazing (Standard) | Vacuum Glazing (Fineo 8\) |
| :---- | :---- | :---- |
| Center-Pane $U$-value | $0.8\\,W/m^{2}K$ 18 | $0.7\\,W/m^{2}K$.21 |
| Total Thickness | $36 \- 44\\,\\text{mm}$ 18 | $7.7\\,\\text{mm}$.21 |
| Sound Reduction ($R\_{w}$) | $32\\,dB$ 18 | $35\\,dB$.21 |
| Light Transmission | $71\\%$ 18 | $80\\%$.21 |
| Expected Lifespan | $20 \- 25$ Years 17 | $60+$ Years.18 |

The primary drawback of VIG is the cost. It is often cited as being $35\\%$ more expensive than triple glazing and up to $60\\%$ more than standard double glazing.17 However, for a 20 square meter garden room, the long-term durability and superior aesthetics often justify the initial investment, particularly given that the glass units themselves are $100\\%$ recyclable and do not suffer from the gas leakage that eventually degrades triple glazed units.18

## **Environmental Illumination and Solar Geometry for the Cowes Site**

Proper lighting in a garden room is not merely about the quantity of glass but the strategic orientation of that glass relative to the sun's path. For a $20\\,m^{2}$ space, the architectural "rule of thumb" suggests that the total glazing area should be at least $20\\%$ of the floor area to ensure adequate daylighting throughout the year.27 This equates to approximately $4\\,m^{2}$ of total glass.

### **Orientation Analysis and Aperture Sizing**

The proposed configuration of windows must balance the need for light with the risks of seasonal overheating and heat loss.

#### **North Elevation: Consistent Diffused Light**

The "large" north-facing window is the most critical for functional tasks, such as painting or computer work, as it provides consistent, glare-free light.28 Because it receives no direct sunlight, this window can be large without the risk of summer overheating. A $1200 \\times 1200\\,\\text{mm}$ unit provides $1.44\\,m^{2}$ of glazing.

#### **West Elevation: Afternoon Warmth and Glare**

The "large" west-facing window will capture the late afternoon and evening sun. While this can provide useful "free" solar heating in the winter, it can cause intense glare and overheating in the summer.28 High-performance glazing with a low solar factor ($g$-value) is essential here. Another $1200 \\times 1200\\,\\text{mm}$ unit adds $1.44\\,m^{2}$.

#### **East Elevation: Morning Illumination**

The "small" east-facing window provides early morning light, which is psychologically beneficial but has less impact on the room's overall heat balance. A $600 \\times 900\\,\\text{mm}$ unit provides $0.54\\,m^{2}$.

#### **South Elevation: Solar Gain Management**

The south-facing elevation receives the most intense solar radiation. The proposal for 1-2 small windows is wise, as it allows for controlled solar gain. Two $600 \\times 600\\,\\text{mm}$ "utility" windows provide a combined $0.72\\,m^{2}$ of glazing.

#### **Cumulative Light Assessment**

| Elevation | Size (mm) | Glazing Area (m2) | Total for Configuration |
| :---- | :---- | :---- | :---- |
| North (Large) | $1200 \\times 1200$ | 1.44 | 1.44 |
| West (Large) | $1200 \\times 1200$ | 1.44 | 1.44 |
| East (Small) | $600 \\times 900$ | 0.54 | 0.54 |
| South (Small x2) | $600 \\times 600$ | 0.36 | 0.72 |
| **Total Area** |  |  | **4.14** |

With a total glazing area of $4.14\\,m^{2}$, the configuration provides a glazing-to-floor ratio of $20.7\\%$, perfectly meeting the optimal target for illumination.27 This ensures the $20\\,m^{2}$ room will feel spacious and well-lit even on overcast days common to the Isle of Wight.

## **Coastal Resilience: Material Selection for the Cowes Microclimate**

Cowes is a coastal town characterized by high winds, salt spray, and significant humidity. These factors drastically influence the lifespan and maintenance requirements of window frames. Salt air is particularly corrosive to metals and can cause unprotected timber to rot more quickly than it would in an inland location.30

### **Frame Material Comparative Performance**

The selection of frame material is as important as the glazing itself for long-term value.

1. **uPVC (Unplasticized Polyvinyl Chloride):** uPVC is widely considered the most cost-effective and durable material for coastal locations. It is naturally resistant to salt corrosion, UV degradation, and moisture.30 Modern uPVC frames do not warp or rot and require only occasional cleaning with soap and water to remove salt buildup.30  
2. **Aluminium:** Aluminium is prized for its slim profiles and modern aesthetic. However, in a coastal environment like Cowes, it must be either anodized or powder-coated to prevent pitting and oxidation.30 While aluminium is more expensive than uPVC, it offers superior structural strength, which can be an advantage for larger windows in wind-exposed sites.30  
3. **Timber:** While aesthetically superior for heritage-style garden rooms, timber requires high maintenance near the coast. Salt air draws moisture into the wood grain, necessitating frequent painting or sealing every 2-5 years to prevent structural failure.31

| Material | Coastal Durability | Maintenance Level | Price-Value Rank |
| :---- | :---- | :---- | :---- |
| uPVC | Excellent 30 | Very Low 30 | 1st (Best Value) |
| Aluminium (Coated) | Good 30 | Low 30 | 2nd |
| Timber (Softwood) | Poor 31 | Very High 31 | 4th |
| Timber (Hardwood) | Fair 31 | High 31 | 3rd |

For a garden room in Cowes, uPVC in a grey or black finish often provides the best balance of coastal durability and contemporary style, mimicking the appearance of aluminium at a significantly lower price point.12

## **Local Supplier Landscape and Economic Projections**

The Isle of Wight possesses a concentrated market of window suppliers and installers, many of whom are based in the Newport area, less than five miles from Cowes. This proximity reduces logistical costs and ensures that local knowledge of the island's unique planning and weather conditions is utilized.

### **Key Suppliers on the Isle of Wight**

1. **Everest (Isle of Wight Service):** Although a national company, Everest operates a dedicated local installation network for the Isle of Wight. They are a primary source for high-performance triple glazing and offer a range of uPVC and aluminium products with long-term guarantees (10-15 years).14  
2. **Joedan Windows & Doors (Newport):** Based on the Dodnor Industrial Estate, Joedan is a regional specialist known for high-quality aluminium and uPVC products. Their showroom allows for direct comparison of different glazing profiles, which is essential for assessing the thickness of triple vs. vacuum units.38  
3. **White Windows Limited (Newport):** Located in Dodnor Park, White Windows has a long-standing reputation on the island. They provide "A" rated windows as standard and use 28mm Argon-filled units for their base double glazing, with upgrades to triple glazing available.39  
4. **Trinity Windows IOW (Ryde/Newport):** A family-run business that serves the entire island, including Cowes. They specialize in uPVC installations and are Certass certified, ensuring that all work complies with the latest building regulations.40  
5. **Stylish Windows & Conservatories (Newport):** Based at The Old Dairy on Long Lane, they offer bespoke joinery and uPVC services, including trade supply for DIY SIPs builders.41

### **Estimated Project Cost Breakdown (2025/2026 Projections)**

The following ballpark prices represent the total cost for the 5-window configuration (2 large, 3 small), including professional installation and VAT. Prices for vacuum glazing are significantly higher due to the material costs of the glass and specialized delivery surcharges for the Isle of Wight.12

| Glazing Specification | Per Large Unit (1.44m2) | Per Small Unit (≈0.5m2) | Total 5-Window Package |
| :---- | :---- | :---- | :---- |
| Triple Glazed (uPVC) | $\\pounds 850 \- \\pounds 1,150$ | $\\pounds 450 \- \\pounds 650$ | **$\\pounds 3,050 \- \\pounds 4,250$** |
| Triple Glazed (Aluminium) | $\\pounds 1,050 \- \\pounds 1,400$ | $\\pounds 600 \- \\pounds 850$ | **$\\pounds 3,900 \- \\pounds 5,350$** |
| Vacuum Glazed (uPVC) | $\\pounds 1,400 \- \\pounds 1,850$ | $\\pounds 850 \- \\pounds 1,100$ | **$\\pounds 5,350 \- \\pounds 7,000$** |

Note: These estimates are derived from 2025 market averages where triple glazing adds a $\\pounds 100-\\pounds 300$ premium per unit over double glazing.12 Vacuum glazing costs include the $\\approx \\pounds 340/m^{2}$ glass price plus specialized framing and a $\\pounds 550$ delivery surcharge often applied by mainland VIG distributors like Fineo.26

## **Planning Policy and Regulatory Constraints in Cowes**

The garden room's location in Cowes necessitates an understanding of the local planning landscape, particularly as Cowes contains several Conservation Areas with strict rules regarding external modifications.

### **Permitted Development Rights**

For most properties in Cowes, a garden room of $20\\,m^{2}$ can be built under Permitted Development (PD) rights, provided it remains "incidental" to the main dwelling.6 The key constraints for the Master Plan are:

* **Boundary Proximity:** If any part of the garden room is within $2\\,\\text{m}$ of a boundary, the maximum eaves height must be $2.5\\,\\text{m}$. This is a critical design constraint that often dictates a flat or mono-pitched roof.6  
* **Garden Coverage:** The total area of outbuildings must not exceed $50\\%$ of the "original" garden area.7

### **The Cowes Conservation Area**

If the site falls within the Cowes Conservation Area, PD rights may be more restricted. While internal changes and like-for-like repairs are usually permitted, new structures often require full planning applications to ensure they do not detract from the area's historic character.45  
Current reports indicate that Cowes does not currently have "Article 4 Directions" that specifically restrict window replacement or the installation of outbuildings beyond standard PD rules.47 However, if the garden room is visible from a public highway or the Solent waterfront, the local planning authority may demand high-quality materials, such as aluminium or timber-effect uPVC, rather than basic white plastic.48 Vacuum glazing is particularly advantageous in this context, as its slim profile ($7.7\\,\\text{mm}$) mimics the look of traditional single glazing while providing modern thermal performance, often making it the only acceptable solution for properties with heritage sensitivities.18

## **Final Synthesis and Strategic Recommendations**

The successful realization of the garden room in Cowes depends on a specification that respects both the structural modularity of the SIPs system and the aggressive coastal environment of the Isle of Wight. Based on the exhaustive research provided, the following strategic recommendations are proposed:

### **Window Sizing and Configuration**

To achieve the best price-to-value ratio, the "large" windows should be specified as $1200 \\times 1200\\,\\text{mm}$ standard casements. This aligns perfectly with the $1200\\,\\text{mm}$ SIPs panel width, minimizing structural rework and waste. The "small" windows should be $600 \\times 900\\,\\text{mm}$ (East) and $600 \\times 600\\,\\text{mm}$ (South), utilizing half-module panel cuts. This configuration provides $4.14\\,m^{2}$ of glazing, meeting the $20\\%$ illumination target for a $20\\,m^{2}$ room while maintaining a manageable solar gain profile.

### **Glazing Selection**

While triple glazing is the most common high-performance option on the island, vacuum glazing (VIG) is the recommended specification for the West elevation to manage solar gain and for its superior 60-year lifespan. For the North, East, and South elevations, triple glazing offers a more cost-effective way to achieve high thermal retention. If the budget allows, a full VIG package provides a future-proof, ultra-slim aesthetic that is more sustainable and visually appealing in a modern garden room.

### **Material and Supply Chain**

uPVC frames in a dark grey (RAL 7016\) or black finish are the optimal choice for Cowes. They offer total resistance to salt-air corrosion with zero maintenance, unlike timber or untreated aluminium. Sourcing from Newport-based suppliers such as Joedan or White Windows is recommended to minimize delivery lead times and ensure that local installers, who understand the Isle of Wight's planning nuances, are responsible for the fitting.  
By following this specification, the garden room will function as a thermally efficient, well-lit, and durable extension of the home, providing year-round utility in the unique environment of Cowes.

#### **Works cited**

1. SIPs Specifications \- SIP Build UK, accessed March 31, 2026, [https://sipbuilduk.co.uk/sips-explained/sips-specifications-3-2/](https://sipbuilduk.co.uk/sips-explained/sips-specifications-3-2/)  
2. SIP Roof Panels & SIPs roof construction | SipsEcoPanels, accessed March 31, 2026, [https://www.sipsecopanels.co.uk/building-with-sips/sip-roof-panels/](https://www.sipsecopanels.co.uk/building-with-sips/sip-roof-panels/)  
3. Type D \- (3m x 2.63m) • SuperSips \- SIP Panels and Garden Studios, accessed March 31, 2026, [https://supersips.uk.com/product/pu-standard-studio-kits/type-d](https://supersips.uk.com/product/pu-standard-studio-kits/type-d)  
4. 4.2m x 3m SIPs Kit \- Simply Sips, accessed March 31, 2026, [https://www.simplysips.co.uk/product/4-2m-x-3m-sips-kit/](https://www.simplysips.co.uk/product/4-2m-x-3m-sips-kit/)  
5. 162mm Structural Insulated Sandwich Panel SIPs PIR and Plywood \- InsulationGo LTD, accessed March 31, 2026, [https://insulationgo.co.uk/162mm-structural-insulated-panel-8x4-sips-pir-and-plywood-sip-2400mm-1200mm-thermal-ply/](https://insulationgo.co.uk/162mm-structural-insulated-panel-8x4-sips-pir-and-plywood-sip-2400mm-1200mm-thermal-ply/)  
6. Planning Permission Garden Room: What You Need, accessed March 31, 2026, [https://plansmadeeasy.org/planning-permission-garden-room/](https://plansmadeeasy.org/planning-permission-garden-room/)  
7. Planning Permission for Garden Rooms: Your Complete 2025 Guide \- Crown Pavilions, accessed March 31, 2026, [https://www.crownpavilions.com/news/news/planning-permission-for-garden-rooms-your-complete-2025-guide/](https://www.crownpavilions.com/news/news/planning-permission-for-garden-rooms-your-complete-2025-guide/)  
8. SIP Kits UK: Structural Insulated Panels | Garden Room Kits, accessed March 31, 2026, [https://www.sipkitsuk.com/](https://www.sipkitsuk.com/)  
9. The Easy Guide To Standard UK Window Sizes \- Mitchell Glass, accessed March 31, 2026, [https://www.mitchellglass.co.uk/latestnews/standard-house-window-size/2025/05/](https://www.mitchellglass.co.uk/latestnews/standard-house-window-size/2025/05/)  
10. UK Standard Window Sizes in mm: Complete Chart by Room & Property Era, accessed March 31, 2026, [https://www.harringtonwindows.com/post/average-window-size](https://www.harringtonwindows.com/post/average-window-size)  
11. Stop Guessing: Here's the UK Standard Window Sizes, accessed March 31, 2026, [https://www.firstclasswindowsanddoors.co.uk/blog/standard-house-window-size/2025/05/](https://www.firstclasswindowsanddoors.co.uk/blog/standard-house-window-size/2025/05/)  
12. How Much Do uPVC Windows Cost? Pricing and Factors in 2025 \- Secure Glaze, accessed March 31, 2026, [https://secureglaze-windows.co.uk/upvc-windows-cost/](https://secureglaze-windows.co.uk/upvc-windows-cost/)  
13. uPVC Window Prices in 2025: Cost Factors & Breakdown, accessed March 31, 2026, [https://windowpriceonline.co.uk/upvc-window-prices-breakdown/](https://windowpriceonline.co.uk/upvc-window-prices-breakdown/)  
14. What Are the Standard Window Sizes in the UK? \- Everest, accessed March 31, 2026, [https://www.everest.co.uk/windows/standard-house-window-size/](https://www.everest.co.uk/windows/standard-house-window-size/)  
15. Accurate Guide to Standard Window Sizes UK, accessed March 31, 2026, [https://www.edenwindows.co.uk/blog/standard-house-window-size/2025/05/](https://www.edenwindows.co.uk/blog/standard-house-window-size/2025/05/)  
16. How Much Do uPVC Windows Cost? A Complete 2025 Price Guide, accessed March 31, 2026, [https://www.uniqueglazing.co.uk/news/how-much-do-upvc-windows-cost-2025](https://www.uniqueglazing.co.uk/news/how-much-do-upvc-windows-cost-2025)  
17. Is vacuum glazing worth it for UK homes? \- MissLJBeauty, accessed March 31, 2026, [https://www.missljbeauty.com/2025/12/is-vacuum-glazing-worth-it-for-uk-homes.html](https://www.missljbeauty.com/2025/12/is-vacuum-glazing-worth-it-for-uk-homes.html)  
18. Vacuum Glazing or Triple Glazing: There's Only One Winner, accessed March 31, 2026, [https://fineo-vacuum-glazing.co.uk/vacuum-glazing-or-triple-glazing/](https://fineo-vacuum-glazing.co.uk/vacuum-glazing-or-triple-glazing/)  
19. Vacuum Glazing Vs Triple Glazing \- ERW Joinery, accessed March 31, 2026, [https://erwltd.co.uk/2024/12/08/vacuum-glazing-vs-triple-glazing/](https://erwltd.co.uk/2024/12/08/vacuum-glazing-vs-triple-glazing/)  
20. Triple Glazing vs Vacuum \- which is best? \- Excell Timber Windows, accessed March 31, 2026, [https://excelltimberwindows.co.uk/triple-glazing-vs-vacuum-which-is-best/](https://excelltimberwindows.co.uk/triple-glazing-vs-vacuum-which-is-best/)  
21. Fineo Vacuum Glazing: Vacuum Glazing for Listed Buildings UK | Slimline Retrofit for Sash & Timber Windows, accessed March 31, 2026, [https://fineo-vacuum-glazing.co.uk/](https://fineo-vacuum-glazing.co.uk/)  
22. Transform Your Period Windows with FINEO Vacuum Glazing \- The London Sash Window Company, accessed March 31, 2026, [https://www.londonsash.com/fineo-vacuum-glazing/](https://www.londonsash.com/fineo-vacuum-glazing/)  
23. Vacuum glazing \- Mitchell & Dickinson, accessed March 31, 2026, [https://mitchellanddickinson.co.uk/service/vacuum-glazing/](https://mitchellanddickinson.co.uk/service/vacuum-glazing/)  
24. Fineo Vacuum Glazing \- Salisbury Joinery, accessed March 31, 2026, [https://www.salisburyjoinery.com/fineo-vacuum-glazing](https://www.salisburyjoinery.com/fineo-vacuum-glazing)  
25. Vacuum Glass \- 1st Glass Services, accessed March 31, 2026, [https://1stglassservices.co.uk/vacuum-glass/](https://1stglassservices.co.uk/vacuum-glass/)  
26. Vacuum Glazing Vs Triple Glazing \- which is best? \- George Barnsdale, accessed March 31, 2026, [https://www.georgebarnsdale.co.uk/blog/vacuum-glazing-vs-triple-glazing-which-is-best/](https://www.georgebarnsdale.co.uk/blog/vacuum-glazing-vs-triple-glazing-which-is-best/)  
27. Glazing percentage: handy rule of thumb to prevent overheating, accessed March 31, 2026, [https://sustainableengineering.co.nz/glazing-percentage-handy-rule-of-thumb-to-prevent-overheating/](https://sustainableengineering.co.nz/glazing-percentage-handy-rule-of-thumb-to-prevent-overheating/)  
28. Window ratio to floor area advice \- Renew, accessed March 31, 2026, [https://renew.org.au/sanctuary-magazine/ideas-advice/window-ratio-to-floor-area-advice/](https://renew.org.au/sanctuary-magazine/ideas-advice/window-ratio-to-floor-area-advice/)  
29. How to Build a Garden Room: Expert Tips from Pete Guerin, accessed March 31, 2026, [https://pmggardenrooms.com/blog/how-to-build-a-garden-room/](https://pmggardenrooms.com/blog/how-to-build-a-garden-room/)  
30. What Are the Best Window Frames for Coastal Areas?, accessed March 31, 2026, [https://www.windoworldltd.co.uk/what-are-the-best-window-frames-for-coastal-areas/](https://www.windoworldltd.co.uk/what-are-the-best-window-frames-for-coastal-areas/)  
31. Which specific window frames do you recommend to prevent rot or corrosion in Coastal Alabama's salt-air environment?, accessed March 31, 2026, [https://acadianwindows.com/learn/which-specific-window-frames-do-you-recommend-to-prevent-rot-or-corrosion-in-coastal-alabamas-salt-air-environment/](https://acadianwindows.com/learn/which-specific-window-frames-do-you-recommend-to-prevent-rot-or-corrosion-in-coastal-alabamas-salt-air-environment/)  
32. The Best Window Types for Coastal Homes, accessed March 31, 2026, [https://spacewindows.com.au/the-best-window-types-for-coastal-homes/](https://spacewindows.com.au/the-best-window-types-for-coastal-homes/)  
33. accessed March 31, 2026, [https://www.windoworldltd.co.uk/what-are-the-best-window-frames-for-coastal-areas/\#:\~:text=uPVC%20is%20widely%20regarded%20as,homes%20exposed%20to%20coastal%20weather.](https://www.windoworldltd.co.uk/what-are-the-best-window-frames-for-coastal-areas/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,homes%20exposed%20to%20coastal%20weather.)  
34. Best Window Frame Material for Bay Area Coastal Weather Conditions \- Insight Glass, accessed March 31, 2026, [https://www.insightglass.com/best-window-frame-material/](https://www.insightglass.com/best-window-frame-material/)  
35. How Much Do Aluminium Windows Cost in 2026? | Checkatrade, accessed March 31, 2026, [https://www.checkatrade.com/blog/cost-guides/cost-aluminium-windows/](https://www.checkatrade.com/blog/cost-guides/cost-aluminium-windows/)  
36. How to Choose the Right Window Frame Material for Coastal Humidity, accessed March 31, 2026, [https://selecthi.com/how-to-choose-the-right-window-frame-material-for-coastal-humidity/](https://selecthi.com/how-to-choose-the-right-window-frame-material-for-coastal-humidity/)  
37. Double Glazing, Triple Glazing & Doors for the Isle of Wight \- Everest, accessed March 31, 2026, [https://www.everest.co.uk/local/isle-of-wight/](https://www.everest.co.uk/local/isle-of-wight/)  
38. Joedan Newport Showroom, Isle of Wight | Windows & Doors, accessed March 31, 2026, [https://www.conservatoryoutlet.co.uk/showrooms/newport-showroom/](https://www.conservatoryoutlet.co.uk/showrooms/newport-showroom/)  
39. White Windows Isle of Wight Conservatories Double Glazing, accessed March 31, 2026, [https://www.whitewindows.co.uk/](https://www.whitewindows.co.uk/)  
40. Trinity Windows IOW: Double Glazing, accessed March 31, 2026, [https://www.trinitywindowsiow.co.uk/](https://www.trinitywindowsiow.co.uk/)  
41. Windows and conservatories | Stylish Windows & Conservatories, accessed March 31, 2026, [https://www.stylishwindows.co.uk/](https://www.stylishwindows.co.uk/)  
42. Fineo glass price and lead times \- Six Over Six Windows, accessed March 31, 2026, [https://sixoversixwindows.co.uk/blog/fineo-glass-price/](https://sixoversixwindows.co.uk/blog/fineo-glass-price/)  
43. How Much Do New Windows Cost? (2025 Updated Guide), accessed March 31, 2026, [https://www.staywarmwindows.co.uk/how-much-do-new-windows-cost-2025-updated-guide/](https://www.staywarmwindows.co.uk/how-much-do-new-windows-cost-2025-updated-guide/)  
44. Planning Permission \- Outbuildings \- Planning Portal, accessed March 31, 2026, [https://www.planningportal.co.uk/permission/common-projects/outbuildings/planning-permission/](https://www.planningportal.co.uk/permission/common-projects/outbuildings/planning-permission/)  
45. Planning Permission in Conservation Areas: The Essential Homeowner Guide \- SurePlan, accessed March 31, 2026, [https://www.getsureplan.co.uk/blog/planning-permission-in-conservation-areas](https://www.getsureplan.co.uk/blog/planning-permission-in-conservation-areas)  
46. Conservation Area Planning Restrictions Guide \- Christopher David Design, accessed March 31, 2026, [https://www.christopher-david.co.uk/conservation-area-planning-restrictions/](https://www.christopher-david.co.uk/conservation-area-planning-restrictions/)  
47. Existing Conservation Areas \- Isle of Wight Council, accessed March 31, 2026, [https://digitalservices.iow.gov.uk/documents/download/cowes-conservation-area](https://digitalservices.iow.gov.uk/documents/download/cowes-conservation-area)  
48. How to Install a Garden Building in a Conservation Area: Rules & Tips \- Cabin Master, accessed March 31, 2026, [https://www.cabinmaster.co.uk/blog/installing-a-garden-building-in-a-conservation-area](https://www.cabinmaster.co.uk/blog/installing-a-garden-building-in-a-conservation-area)
