wisogetnid/garden-room/research/suppliers/sip-suppliers.md

# **In-Depth Analysis of Structural Insulated Panel Suppliers for the Isle of Wight and South Coast Construction Markets**

The construction environment of the Isle of Wight has entered a transitional phase following the cessation of operations by MTL Ltd, previously the Island’s primary local manufacturer of Magnesium Oxide (MgO) Structural Insulated Panels (SIPs). This market vacuum has forced developers, architects, and self-builders to look toward mainland suppliers, primarily concentrated in Hampshire, Dorset, and West Sussex, to fulfill the demand for high-performance, sustainable, and rapid-build envelopes. This report provides an exhaustive evaluation of the SIPs supplier landscape, analyzing the technical, logistical, and economic variables inherent in transporting and assembling these systems on the Island. Particular attention is paid to fire performance, price comparisons, and the specialized support available for small-scale projects such as garden rooms.

## **The Paradigm Shift in Island Construction**

Structural Insulated Panels represent a significant advancement in Modern Methods of Construction (MMC), offering a high-strength, thermally efficient alternative to traditional timber frame or masonry. The system typically consists of an insulating foam core—composed of Polyurethane (PUR), Polyisocyanurate (PIR), or Expanded Polystyrene (EPS)—sandwiched between two layers of structural board, most commonly Oriented Strand Board (OSB/3). The resulting composite panel acts as a stressed-skin structure that handles axial, racking, and flexural loads with high efficiency.1  
With the exit of MTL Ltd from the market, the specialized focus on Magnesium Oxide (MgO) panels has diminished in the immediate vicinity.4 MgO panels were historically favored for their superior fire resistance and moisture management. However, the current market is dominated by OSB-faced panels, which achieve equivalent or superior performance through precision engineering and advanced protective linings.3 For the Isle of Wight, the shift to mainland suppliers necessitates a sophisticated understanding of transport logistics across the Solent, as ferry surcharges and lead times now play a decisive role in project viability.7

## **Structural Mechanics and Thermal Physics of SIP Systems**

The efficacy of a SIP system is rooted in the synergy between its component materials. The OSB skins provide the structural "flanges" that resist tension and compression, while the foam core acts as the "web," providing shear resistance and preventing the skins from buckling. This mechanical arrangement allows for thinner wall profiles that outperform significantly thicker traditional walls in both strength and insulation.10

## **Thermal Performance and U-Value Metrics**

Thermal efficiency is measured by the U-value ($W/m^2K$), which quantifies the rate of heat transfer through a structure. A primary advantage of SIPs is the minimization of thermal bridging. Unlike traditional timber frames, where studs interrupt the insulation every 400mm or 600mm, SIPs provide a continuous layer of insulation.13  
The following table details the thermal performance of various panel thicknesses commonly supplied by regional manufacturers like Simply SIPs and Ecologic SIPs:

| Panel Thickness (mm) | Core Material | U-Value (W/m2K) | Primary Application |
| :---- | :---- | :---- | :---- |
| 97 | EPS / PUR | 0.30 \- 0.38 | Garden Rooms / Offices |
| 122 | EPS / PUR | 0.22 | Extensions / Annexes |
| 147 | EPS / PUR | 0.20 | Residential New Builds |
| 172 | EPS / Graphite EPS | 0.18 | Low-Energy Housing |
| 222 | Graphite EPS | 0.11 \- 0.14 | Passivhaus Standards |

Data suggests that even the entry-level 97mm panels, often used for garden studios, provide a thermal envelope that remains habitable in temperatures as low as $-18^\\circ C$.14 For high-specification residential projects, suppliers such as Ecologic SIPs offer 222mm panels that achieve U-values as low as 0.11 $W/m^2K$ when combined with appropriate membranes, facilitating the construction of buildings with minimal active heating requirements.6

## **Structural Integrity and Acoustic Mitigation**

The stressed-skin properties of SIPs provide a significant advantage in the Isle of Wight’s coastal areas, where high wind loads are a standard design consideration. SIPs have been documented to withstand category 4 and 5 hurricanes, a testament to their racking strength and structural rigidity.18  
Acoustic performance is an often-overlooked benefit for garden rooms used as music studios or quiet home offices. SIP structures can achieve a sound reduction of 40-50dB, which is particularly beneficial in more densely populated areas of the Island like Newport or Ryde.20 This performance is achieved through the dense composite nature of the panels, which damps vibration more effectively than hollow-cavity timber frames.

## **Fire Dynamics and Regulatory Compliance**

One of the most frequent inquiries from self-builders regarding SIPs concerns their fire safety, particularly after the closure of MTL Ltd, which specialized in inherently fire-resistant MgO boards.4 It is critical to distinguish between "fire proof" and "fire resistant." Modern OSB-based SIPs are classified as combustible, but when integrated into a complete wall or roof assembly, they achieve high levels of fire resistance that meet or exceed UK Building Regulations.5

## **Achievement of 30 and 60-Minute Ratings**

Fire resistance in SIPs is typically achieved through the application of internal linings. For example, the Kingspan TEK system, utilized by suppliers like Lansdowne Green and McVeigh Offsite, requires only a single layer of 12.5mm Fire Check plasterboard to achieve a 60-minute fire rating.5  
Ecologic SIPs has achieved a notable milestone by being one of the few companies in the UK to confirm a 60-minute fire resistance rating specifically with an EPS (Expanded Polystyrene) core.21 Their panels often incorporate a flame-retardant graphite additive within the insulation core and are complemented by intumescent coatings or fire-rated OSB skins.20

## **Comparison of Fire Performance by System Type**

| Supplier System | Core Type | Protective Lining | Fire Rating |
| :---- | :---- | :---- | :---- |
| Kingspan TEK | PUR | 12.5mm Fire Check Plasterboard | 60 Minutes |
| Ecologic SIPs | Graphite EPS | 12mm Fire-Resistant Plasterboard | 60 Minutes |
| Redcliffe Gardeners | EPS | Fire-rated OSB / Intumescent | BS EN 1365-1 |
| Standard Garden Kit | EPS / PUR | 12.5mm Plasterboard | 30 Minutes |

For garden rooms located within one meter of a property boundary, achieving a high fire rating is a legal requirement under Building Regulations Part B. The ability of suppliers like Ecologic SIPs and Lansdowne Green to provide certified fire test reports is a significant factor in their reliability and suitability for projects on the Isle of Wight.5

## **Regional Supplier Evaluation: Distance, Trust, and Reliability**

The logistical challenge of the Solent crossing makes geographical proximity a primary factor in supplier selection. Suppliers located near the ferry terminals in Lymington, Southampton, and Portsmouth have a distinct advantage in mobilization and delivery logistics.

## **New Forest SIPs (Lymington, Hampshire)**

Located in Lymington, New Forest SIPs is geographically the closest mainland supplier to the Isle of Wight, situated just minutes from the Wightlink ferry terminal to Yarmouth.10

* **Reliability and Experience:** The company boasts over 20 years of experience in the design, manufacture, and installation of SIPs. They manage the entire process in-house, ensuring consistent quality control.10  
* **Project Support:** They explicitly cater to both domestic and commercial clients, offering bespoke SIP manufacturing that can accommodate complex architectural designs, such as open ceilings and statement glulam beams.10  
* **Trust Metric:** Their "Project Diaries" and active social media presence provide transparency into their construction standards and successful project completions.10

## **Ecologic SIPs (Bransgore, Dorset)**

Ecologic SIPs is situated in the New Forest, near the Dorset/Hampshire border, providing excellent access to the Southampton and Lymington ferry routes.6

* **Trust and Accreditation:** They hold the "STA Assure Gold" status, the highest level of quality assurance provided by the Structural Timber Association. This is a critical trust marker for self-builders.6  
* **Performance Leadership:** As the winner of the "Best SIPs Home" at the Build It Awards 2023, they have a proven track record of delivering award-winning eco-homes.6  
* **Self-Builder Support:** They offer workshop tours and have a dedicated partnership with BuildStore to provide specialized SIP-friendly mortgages, which is a significant benefit for self-builders on the Island.6  
* **Technical Transparency:** They provide a comprehensive 3D SIPs detail pack, allowing architects and engineers to see exactly how junctions and connections are engineered.6

## **Lansdowne Green (Brighton/South East)**

While located further east in Sussex, Lansdowne Green is a primary delivery partner for the Kingspan TEK system, which is widely regarded as one of the most technically advanced SIP systems in the UK.5

* **System Integrity:** The Kingspan TEK system is recognized by all major building warranty providers and the Council of Mortgage Lenders. This makes it an ideal choice for residential projects requiring a mortgage.5  
* **Professional Services:** They provide full SIP design, structural engineering, and a dedicated project manager who serves as a single point of contact throughout the construction period.5  
* **Fire Safety:** Their system's ability to achieve a 60-minute fire rating with minimal internal lining makes them a favorite for projects with strict safety requirements.5

## **Direct Sips (Lancashire / Nationwide Service)**

Direct Sips operates as a high-volume manufacturer and supplier, providing a wide range of standardized garden room kits.14

* **Distance and Delivery:** Although based in the North, they offer nationwide delivery and installation. They utilize flat-pack kits that allow multiple buildings to be delivered on a single wagon, which can help distribute the ferry costs across several units.15  
* **Product Range:** Their catalog is extensive, featuring offices ("Sanctuary"), leisure rooms ("Opulence"), and modular annexes.14  
* **Self-Build Focus:** They provide everything needed for a "shell build," including insulated splines, fixing kits, and breathable membranes, making them highly suitable for the small projects identified in the user query.15

## **Logistical Economics: Managing the Solent Crossing**

Transporting SIP panels to the Isle of Wight involves navigating the specific constraints and costs of the Solent ferry services. The absence of a local manufacturer means that every panel must be shipped from the mainland, introducing a cost variable that is not present in mainland projects.

## **Ferry Route Comparison for Commercial Deliveries**

The three primary vehicle ferry routes are Lymington to Yarmouth, Portsmouth to Fishbourne, and Southampton to East Cowes. For large-scale deliveries involving 13m (40ft) trucks, costs are significantly higher than standard car fares.7

| Route | Operator | Typical Foot Passenger | Average Car Return | Delivery Suitability |
| :---- | :---- | :---- | :---- | :---- |
| Lymington \- Yarmouth | Wightlink | £16.00 \- £33.40 | £40.50 \- £100.00 | Best for New Forest / Dorset suppliers |
| Portsmouth \- Fishbourne | Wightlink | £33.40 | £40.50 \- £100.00 | Best for Sussex / Midlands suppliers |
| Southampton \- East Cowes | Red Funnel | £19.36 \- £26.30 | £40.50 \- £100.00 | Best for central Hampshire suppliers |

Commercial ferry prices for freight are often calculated by the meter and can reach £300+ during peak periods.8 Furthermore, many mainland suppliers, such as Simply SIPs, explicitly exclude the Isle of Wight from their standard delivery zones, requiring a bespoke quote that accounts for the ferry surcharge and potential driver overnight stays.7

## **Just-in-Time Delivery Challenges**

On an island, the timing of delivery is critical. Unlike a mainland site where a delayed truck might arrive a few hours late, a missed ferry slot can delay a project by a full day or more. Suppliers like Supersips and Simply SIPs mitigate this by running their own fleet of vehicles and drivers, ensuring they have control over the scheduling and can handle the specific parking and access requirements of the Island's narrow roads.7  
For the self-builder, it is essential to ensure that there is adequate parking for a 13m truck and trailer near the site. Kerbside delivery is the standard service, and if the site is inaccessible to large vehicles, the panels must be "trans-shipped" onto smaller vehicles at a local depot, adding further cost.7

## **Pricing Matrix: SIP Panels and Building Kits**

Pricing for SIPs is generally divided into two categories: "supply-only" panels and "building kits." For a garden room project, a kit is often more cost-effective as it includes the necessary joining splines, timber, and fixings.

## **Individual Panel Prices**

For those designing their own structure from scratch, individual panel prices provide a baseline for material costs. The following data is derived from current market rates for OSB/3 panels with an EPS or PUR core.26

| Panel Size | Thickness (mm) | Price (Approx. Exc. VAT) | Supplier Reference |
| :---- | :---- | :---- | :---- |
| $2.44m \\times 1.22m$ | 97 | £72.00 | Simply SIPs |
| $2.44m \\times 1.22m$ | 122 | £81.00 | Simply SIPs |
| $2.44m \\times 1.22m$ | 147 | £99.00 | Simply SIPs |
| $3.00m \\times 1.20m$ | 122 | £113.00 | Simply SIPs |
| $2.44m \\times 1.22m$ | 100-200 | £86.00 \- £121.00 | Direct Sips |

## **Garden Room and Building Kit Prices**

Kits are pre-cut and labeled for easy assembly. They typically include floor, wall, and roof panels.27

| Kit Dimensions | Application | Price (Approx. Exc. VAT) | Supplier Reference |
| :---- | :---- | :---- | :---- |
| $2.44m \\times 2.44m$ | Micro Office | £1,508.00 | Simply SIPs |
| $3.00m \\times 2.40m$ | Standard Studio | £1,760.00 | Simply SIPs |
| $3.60m \\times 3.00m$ | Large Garden Room | £2,948.00 | Simply SIPs |
| $4.27m \\times 3.66m$ | Multi-Room Suite | £3,996.00 | Simply SIPs |
| 10-Night Package | Modular Living | £1,250.00 (USD equiv) | Direct Sips |

Note: Prices often reflect a 10% discount for seasonal offers or volume orders and exclude Isle of Wight delivery surcharges.15  
Building with a kit rather than a factory-built modular room can save significant money, as the "initial outlay" is lower and the owner-occupier provides the labor or hires a local contractor to assemble the shell.15

## **Support Ecosystem for Self-Builders and Small Projects**

The "Self-Builder" category encompasses a wide range of experience levels, from "novice" homeowners to competent DIYers. SIP suppliers have developed several support mechanisms to cater to this demographic.

## **Design and Engineering Services**

Modern SIP construction is heavily reliant on Computer-Aided Design (CAD). Suppliers like Ecologic SIPs, McVeigh Offsite, and UltraSIPs offer full 3D SIPs design services.3 This process involves:

1. **Drafting:** Converting a client's architectural drawings into a SIP-friendly layout.  
2. **Engineering:** Calculating structural loads and ensuring the design meets building regulations.  
3. **CNC Cutting:** Using five-axis CNC machines to cut panels to the exact specifications, including door and window apertures.2

This "precision-built" approach means that when the kit arrives on the Isle of Wight, it fits together like a giant 3D puzzle, significantly reducing the risk of errors and onsite waste.11

## **The Role of "Fixing Kits" and Instructions**

For a successful self-build, the "peripherals" are as important as the panels. A standard fixing kit from a supplier like Simply SIPs includes:

* **Specialized Screws:** Ranging from 30mm to 180mm to accommodate different panel thicknesses and structural connections.9  
* **Adhesive:** Essential for creating an airtight seal at the jointing splines and soleplates.9  
* **Lorry/Ratchet Straps:** Used to pull the panels tight and ensure the structure is vertically square before final fixing.9  
* **Temporary Protection:** DPM plastic sheets to cover the structure until the final cladding or roofing membrane is applied.9

Suppliers like Future SIPs and uSIPs provide full assembly instructions and drawings, enabling a competent builder to erect a garden room shell in as little as one or two days.11

## **Sustainability and Lifecycle Analysis**

The Isle of Wight's status as a UNESCO Biosphere Reserve makes the environmental credentials of building materials a high priority. SIPs are among the most sustainable construction methods available today.

## **Energy Efficiency and Carbon Footprint**

The "Fabric First" approach is central to SIPs. By creating a highly insulated and airtight envelope, the long-term energy consumption of the building is drastically reduced. SIP structures are estimated to be 40-60% more energy-efficient than traditional timber frames.33 This is achieved through:

* **Airtightness:** Minimal air leakage compared to "stick-built" structures.3  
* **High R-Values:** Superior thermal resistance measurements over 50 years of scientific data.33  
* **Low U-Values:** Down to 0.11 $W/m^2K$ for roof and wall sections.6

## **Recyclability and Waste Management**

SIP panels utilize OSB made from small-diameter, fast-growing trees, avoiding the need for old-growth timber.1 Furthermore, the EPS and PUR cores are often 100% recyclable, non-toxic, and biologically inert.23  
On-site waste is a major concern for Island projects due to high skip hire costs. Because SIPs are factory-fabricated to the exact project dimensions, on-site waste is reduced by up to 60% compared to traditional lumber construction.3 This "cleaner" site environment is also beneficial for garden projects where space is limited and protection of existing landscaping is desired.

## **Strategic Conclusions and Recommendations**

The cessation of MTL Ltd on the Isle of Wight has created a reliance on mainland suppliers that must be managed with logistical precision. For the resident or developer seeking a SIP solution, the choice of supplier should be dictated by a balance of distance, technical certification, and project support.

## **Decision Matrix for Supplier Selection**

| Project Type | Recommended Supplier | Justification |
| :---- | :---- | :---- |
| **High-End Eco Home** | Ecologic SIPs | STA Gold status, Passivhaus expertise, award-winning design.6 |
| **Bespoke Extension** | New Forest SIPs | Local proximity to Lymington, in-house installers, bespoke manufacturing.10 |
| **DIY Garden Office** | Simply SIPs / Direct Sips | Standardized kits, transparent pricing, comprehensive fixing kits.15 |
| **Mortgage-Led Build** | Lansdowne Green | Kingspan TEK system is widely accepted by all major lenders.5 |
| **Fast-Track Studio** | uSIPs | 7-day delivery commitment and custom-size flexibility.32 |

## **Summary of Actionable Insights**

1. **Logistical Mitigation:** Given the high cost of ferry transport, suppliers in the New Forest (Ecologic and New Forest SIPs) offer the most logical connection to the Island. Their proximity reduces mobilization costs for installation teams and minimizes the risk of transit delays.  
2. **Fire Safety Assurance:** For garden rooms near boundaries, self-builders should insist on systems that have achieved a 60-minute fire rating (e.g., Kingspan TEK or Ecologic SIPs) rather than relying on standard 30-minute ratings.  
3. **Trust Verification:** The "STA Assure Gold" status is the gold standard for reliability in the SIPs industry. Choosing an accredited supplier provides a layer of security regarding factory production control and structural integrity.  
4. **Economic Strategy:** While factory-built modular units offer convenience, building with a SIP kit from a manufacturer like Direct Sips or Simply SIPs offers significant cost savings for the budget-conscious project, provided the owner can manage the assembly phase.  
5. **Technical Integration:** Engaging with a supplier who provides 3D modeling and structural engineering (like McVeigh Offsite or Ecologic) is essential for projects that deviate from standard rectangular forms, ensuring that every panel is precision-cut to the architectural intent.

The Isle of Wight market is well-served by a cluster of high-performance SIP suppliers on the South Coast of England. By understanding the mechanical advantages, fire safety requirements, and transport economics of these systems, Islanders can continue to build structures that are thermally superior and structurally resilient, despite the absence of a local manufacturing base.

#### **Works cited**

1. Sip Building Systems: SIP Insulated Panels | SIPS UK | Structural Insulated Panels, accessed March 20, 2026, [https://www.sipbuildingsystems.co.uk/](https://www.sipbuildingsystems.co.uk/)  
2. SIPS UK: Structural Insulated Panels | SIP Suppliers & Manufacturers, accessed March 20, 2026, [https://www.sips.uk.com/](https://www.sips.uk.com/)  
3. SIP Panels, Construction & Contracting, accessed March 20, 2026, [https://www.mcveighoffsite.com/](https://www.mcveighoffsite.com/)  
4. MTL Ltd | Isle of Wight | MgO SIPS Building Systems | Energy-Efficient Construction |, accessed March 20, 2026, [https://www.mtlsips.com/](https://www.mtlsips.com/)  
5. Lansdowne Green: SIPs construction builders Sussex, accessed March 20, 2026, [https://www.lansdownegreen.co.uk/](https://www.lansdownegreen.co.uk/)  
6. Ecologic SIPs | Sustainable SIP Structures, accessed March 20, 2026, [https://www.ecologic-sips.co.uk/](https://www.ecologic-sips.co.uk/)  
7. UK Wide Delivery \- Simply Sips Fixing Kits for you, accessed March 20, 2026, [https://www.simplysips.co.uk/blog/uk-wide-delivery/](https://www.simplysips.co.uk/blog/uk-wide-delivery/)  
8. Isle Of Wight Ferry Beginners Guide 2025, accessed March 20, 2026, [https://www.isleofwightguru.co.uk/isle-of-wight-ferry-beginners-guide.html](https://www.isleofwightguru.co.uk/isle-of-wight-ferry-beginners-guide.html)  
9. Our Fixing Kit \- Simply Sips Fixing Kits for you, accessed March 20, 2026, [https://www.simplysips.co.uk/blog/our-fixing-kit/](https://www.simplysips.co.uk/blog/our-fixing-kit/)  
10. SIPs Contractors in Bournemouth, SIPs Installation in Hampshire, accessed March 20, 2026, [https://www.newforestsips.co.uk/](https://www.newforestsips.co.uk/)  
11. SIPs Panels Bristol \- SIP Supplier South West of England \- Future Sips, accessed March 20, 2026, [https://www.futuresips.co.uk/sips-bristol/](https://www.futuresips.co.uk/sips-bristol/)  
12. SIPs Panels Ltd., accessed March 20, 2026, [https://sips-panels.co.uk/](https://sips-panels.co.uk/)  
13. SIP's Bespoke Garden Room Building | Garden Rooms Southwest | United Kingdom, accessed March 20, 2026, [https://www.gardenroomsouthwest.co.uk/](https://www.gardenroomsouthwest.co.uk/)  
14. Hampshire \- Direct Sips, accessed March 20, 2026, [https://directsips.co.uk/areas-we-cover/hampshire/](https://directsips.co.uk/areas-we-cover/hampshire/)  
15. Direct Sips | Self Build Garden Rooms & Offices, accessed March 20, 2026, [https://directsips.co.uk/](https://directsips.co.uk/)  
16. Panel Thickness Upgrade \- Simply Sips Fixing Kits for you, accessed March 20, 2026, [https://www.simplysips.co.uk/blog/panel-thickness-upgrade/](https://www.simplysips.co.uk/blog/panel-thickness-upgrade/)  
17. FAQ | EcologicSIPs, accessed March 20, 2026, [https://www.ecologic-sips.co.uk/faq](https://www.ecologic-sips.co.uk/faq)  
18. SIPs Contractors in Wiltshire, SIPs Manufacturing in Wiltshire \- New Forest SIPs Ltd, accessed March 20, 2026, [https://www.newforestsips.co.uk/wiltshire.html](https://www.newforestsips.co.uk/wiltshire.html)  
19. Building with SIP panels Archives \- Factory Cabins LV Blog, accessed March 20, 2026, [https://www.logcabinslv.co.uk/blog/logcabins/building-with-sip-panels/](https://www.logcabinslv.co.uk/blog/logcabins/building-with-sip-panels/)  
20. SIP Garden Rooms \- Redcliffe Landscape Gardeners, accessed March 20, 2026, [https://www.redcliffegardeners.co.uk/garden-buildings/sip-garden-rooms/](https://www.redcliffegardeners.co.uk/garden-buildings/sip-garden-rooms/)  
21. Downloads | EcologicSIPs, accessed March 20, 2026, [https://www.ecologic-sips.co.uk/resources](https://www.ecologic-sips.co.uk/resources)  
22. Accreditations and Warranty | EcologicSIPs, accessed March 20, 2026, [https://www.ecologic-sips.co.uk/accreditations-and-warranty](https://www.ecologic-sips.co.uk/accreditations-and-warranty)  
23. What are SIPs | EcologicSIPs, accessed March 20, 2026, [https://www.ecologic-sips.co.uk/innovate-and-insulate](https://www.ecologic-sips.co.uk/innovate-and-insulate)  
24. Somerset \- Direct Sips, accessed March 20, 2026, [https://directsips.co.uk/areas-we-cover/somerset/](https://directsips.co.uk/areas-we-cover/somerset/)  
25. Delivery \- SuperSips \- SIP Panels and Garden Studios, accessed March 20, 2026, [https://supersips.uk.com/delivery](https://supersips.uk.com/delivery)  
26. Rustic Bothy \- Direct Sips, accessed March 20, 2026, [https://directsips.co.uk/product/rustic-bothy/](https://directsips.co.uk/product/rustic-bothy/)  
27. Products \- Simply Sips, accessed March 20, 2026, [https://www.simplysips.co.uk/products/](https://www.simplysips.co.uk/products/)  
28. What We Supply \- Simply Sips Fixing Kits for you, accessed March 20, 2026, [https://www.simplysips.co.uk/blog/what-we-supply/](https://www.simplysips.co.uk/blog/what-we-supply/)  
29. SIPs Panels vs Timber Frame Construction, accessed March 20, 2026, [https://www.simplysips.co.uk/blog/sips-panels-vs-timber-frame-construction/](https://www.simplysips.co.uk/blog/sips-panels-vs-timber-frame-construction/)  
30. UltraSIPs LTD Reviews 1 \- Trustpilot, accessed March 20, 2026, [https://www.trustpilot.com/review/ultrasips.com](https://www.trustpilot.com/review/ultrasips.com)  
31. SIPS Panels UK • Structural Insulated Panels, accessed March 20, 2026, [https://www.clays.com/](https://www.clays.com/)  
32. uSIPs: Structurally Insulated Panels Supplier, accessed March 20, 2026, [https://usips.co.uk/](https://usips.co.uk/)  
33. SIPs for Contractors & Builders \- Premier SIPS, accessed March 20, 2026, [https://sips.premierbuildingsystems.com/builders](https://sips.premierbuildingsystems.com/builders)
