wisogetnid/garden-room/research/suppliers/skip-hire-suppliers.md

# **A Comprehensive Strategic Analysis of Waste Management Logistics and Skip Hire Provisions for Residential and Self-Build Projects on the Isle of Wight**

The management of construction and domestic waste on the Isle of Wight represents a complex intersection of geographical isolation, specialized local regulation, and a diverse market of service providers. For the self-builder or the homeowner engaged in a discrete project such as the construction of a garden room, the logistical considerations extend far beyond simple price comparisons. The island’s unique infrastructure, characterized by narrow rural arteries and historic urban centers like Cowes, necessitates a nuanced understanding of skip hire dynamics, permit requirements, and the specific waste streams associated with modern construction methods such as Structural Insulated Panels. This report provides an exhaustive evaluation of the skip hire sector on the Isle of Wight, offering a comparative analysis of pricing, reliability, and the technical support available for small-scale residential developments.

## **The Economic Landscape of Skip Hire and Waste Disposal**

The fiscal structure of waste management on the Isle of Wight is heavily influenced by the costs associated with mainland transport for certain waste types and the operational overheads of maintaining localized transfer stations. Statistical data for the year 2026 indicates that the average cost of skip hire on the island is approximately £320, with a low-end average of £240 and a high-end average reaching £368 for more intensive requirements.1 These figures represent the total job cost, which typically incorporates labor for installation (averaging £64) and the core waste removal component (averaging £256).1  
Pricing is rarely uniform across the island, as providers utilize different models based on waste categorization. For example, Waste King positions itself as a budget-friendly option with prices starting at £165 plus VAT, emphasizing a digital-first approach to booking and quote generation.2 In contrast, local mainstays like Isle of Wight Skip Hire provide a highly granular price list that distinguishes between mixed waste, inert materials, rubble, and green waste.4 This distinction is critical for the self-builder, as the segregation of materials can lead to substantial cost reductions. Rubble-only skips are the most economical, as materials like old concrete and brick can be crushed into hardcore for reuse, whereas mixed waste is significantly more expensive due to the intensive sorting required at licensed mechanical recycling facilities.5

## **Comparative Pricing Matrix for Standard Skip Sizes and Waste Streams**

The following table provides a detailed breakdown of pricing across various waste categories and skip sizes, based on current market data from leading island providers.

| Skip Size | Mixed Waste (Inc. VAT) | Inert Waste (Inc. VAT) | Rubble Only (Inc. VAT) | Green Waste (Inc. VAT) | Typical Project Utility |
| :---- | :---- | :---- | :---- | :---- | :---- |
| 2 Yard (Mini) | £155.00 | £135.00 | £75.00 | £105.00 | Small garden jobs, minor DIY refits 4 |
| 3 Yard (Midi) | £195.00 | £155.00 | £80.00 | £125.00 | Bathroom refits, moderate garden clearouts 4 |
| 4 Yard (Midi) | £235.00 | £170.00 | £85.00 | £160.00 | Kitchen renovations, small building works 4 |
| 6 Yard (Builder) | £290.00 | £195.00 | £95.00 | £180.00 | General construction site waste, bulky items 4 |
| 8 Yard (Large) | £330.00 | POA | POA | N/A | Full house clearances, heavy construction 4 |
| 10 Yard (Maxi) | £499.00 | N/A | N/A | £210.00 | Large-scale domestic clearouts, furniture 7 |
| 12 Yard (Maxi) | £485.00 | N/A | N/A | N/A | Commercial-grade light waste disposal 4 |

Fiscal variability is also introduced through supplementary services and potential penalties. For instance, lockable skips, which are essential in vulnerable or high-traffic areas to prevent unauthorized tipping, can incur additional charges ranging from £50 to £150.8 Furthermore, overfill charges are a common fiscal risk; by law, skip providers are prohibited from transporting skips loaded beyond their vertical sides, and attempts to do so can result in significant surcharges or the refusal of collection.4

## **Qualitative Assessment of Provider Reliability and Market Trust**

Reliability in the island's skip hire market is defined by several key metrics: punctuality of delivery and collection, transparency in final billing, and the professional competence of drivers in navigating difficult terrains. The market is characterized by a high concentration of family-owned firms with decades of operational history. West Wight Mini Skips, based in Yarmouth, has been trading for over 40 years, which has allowed them to cultivate a loyal customer base and a reputation for "prompt, efficient, and friendly service".7  
Trust is further established through industry affiliations and licensing. Reputable firms such as Cheap Skips (IW) Ltd and West Wight Mini Skips are members of the Federation of Small Businesses (FSB), and all major players hold Waste Carrier Licenses issued by the Environment Agency.10 The analysis of consumer testimonials reveals that the most highly valued trait in a provider is the ability to adhere to agreed-upon timelines. Users such as Mike Duffy and Denise Greep have highlighted experiences of "delight" with providers who deliver early and collect promptly when a skip is full, which is vital for maintaining the momentum of a construction project.7

## **Analysis of Trust Indicators and Service Longevity**

The following table summarizes the reliability profiles of the island's primary skip hire organizations.

| Service Provider | Operational Longevity | Primary Service Area | Key Trust Indicator | Unique Selling Proposition |
| :---- | :---- | :---- | :---- | :---- |
| West Wight Mini Skips | 40+ Years | West Wight/Island-wide | FSB Membership | Integrated groundwork and plant hire services 10 |
| Cheap Skips (IW) Ltd | 25+ Years | Newport/Central | 5-star Yell rating | 24/hour assistance and emergency response 12 |
| Westridge Skip Hire | 20+ Years | Newport/Central | Licensed Recycling Facility | Large-scale RoRo capabilities and aggregates 6 |
| Isle of Wight Skip Hire | Established | Coast to Coast | Online Payment Options | Technical site reconnaissance for access 4 |
| Waste King | National/Local | Cowes/Newport focus | Award-winning team | Digital quote generation and permit management 3 |
| Reliable Skip | Regional | Island-wide | High volume of reviews | Fixed-period hire (1-14 days) included 7 |

A recurring theme in the qualitative data is the role of the driver in the service experience. Professionalism at the point of delivery is cited as a significant trust factor. For example, Patrick C. and Sam M. specifically noted the meticulous placement of skips and the proactive advice provided by drivers regarding what materials could and could not be included.14 This level of expertise is particularly beneficial for self-builders who may be managing waste segregation for the first time and need to avoid the inclusion of prohibited items like hazardous chemicals or electronic waste.5

## **Logistical Dynamics and Geographical Coverage**

The geographical distribution of skip hire depots on the Isle of Wight significantly impacts response times and delivery costs. Newport serves as the logical center of the island’s waste management infrastructure, housing major facilities like Westridge Skip Hire and Cheap Skips (IW) Ltd.6 This central positioning allows for efficient dispatch to any point on the island, although firms like West Wight Mini Skips maintain a dominant presence in the western regions (Yarmouth, Freshwater, Totland) due to their proximity.1  
For projects located in Cowes (PO31), the logistics are particularly challenging. The town's narrow streets and limited off-road parking frequently necessitate the placement of skips on public highways. Waste King and Isle of Wight Skip Hire both emphasize their capability to serve Cowes effectively, offering next-day delivery and full management of the necessary paperwork and permits.3 When site access is physically impossible for a standard skip lorry—a common occurrence in the older parts of Cowes—alternative services such as "Wait and Load" become the primary solution. This involves a vehicle remaining on-site while it is loaded, typically within a 15-to-30-minute window, thereby eliminating the need for a long-term highway permit.17

## **Access Assessment and Technical Site Logistics**

Providers have developed various methodologies to assist customers in determining whether a skip lorry can safely access a site. This is a critical step for self-builders working on garden rooms, which are often located at the rear of properties with restricted access. The following protocols are utilized by top-tier providers:

* **Google Street View Analysis**: Firms like Isle of Wight Skip Hire use satellite and street-level imagery to perform a preliminary assessment of gate widths and turning circles.4  
* **Physical Reconnaissance**: In cases of extreme ambiguity, providers can dispatch a member of staff to perform a site visit to confirm that the laws of physics will permit a lorry's entry.4  
* **Driveway Measurement Protocols**: Customers are encouraged to communicate the exact dimensions of their driveways, as skip lorries require significant clearance and a firm surface to avoid damage to paving.7  
* **Alternative Placement Advice**: If a driveway is unsuitable, providers can suggest alternative placement on private land or assist in the application for a roadside permit.7

For the self-builder in Cowes, the central question is often whether the skip can be delivered at all. The evidence suggests that most local providers are highly experienced in "tight-access" deliveries, utilizing smaller vehicles where necessary or recommending "Grab Bags" for smaller volumes of waste in extremely confined spaces.7

## **Supporting the Self-Builder and the Garden Room Project**

The construction of a garden room presents a specific waste management lifecycle that differs from a standard house renovation. These projects typically involve three distinct phases: groundworks and excavation, structural assembly, and internal finishing. Each phase produces different waste streams, requiring a strategic approach to skip selection to maintain cost-efficiency.

## **Foundational and Groundworks Waste**

The initial phase of a garden room project involves the excavation of topsoil, clay, and potentially old concrete or stone to create a level base for foundations. This is "heavy" waste. The most efficient choice for this phase is an 8-yard "Inert" skip, which is the largest size permitted for heavy materials due to the weight limits of the hydraulic arms on skip lorries.5 Providers like West Wight Mini Skips are particularly valuable here, as they also offer plant hire, such as 1-tonne mini diggers and skip-loading dumpers, allowing the self-builder to integrate their excavation and waste removal through a single logistical point of contact.10

## **Structural Assembly and SIPS Waste Management**

Modern garden rooms are increasingly constructed using Structural Insulated Panels (SIPS). SIPS are a highly sustainable construction method that utilizes a core of insulating foam (EPS, PIR, or PUR) sandwiched between two layers of Oriented Strand Board (OSB).23 Research indicates that the use of SIPS can reduce job-site waste by up to 60% compared to traditional stick-framed construction, as panels are often pre-cut in the factory to exact project specifications.25  
For the self-builder, this means the waste profile of the structural phase is characterized by fewer, albeit bulkier, off-cuts. While SIPS waste is largely non-hazardous, the volume of foam and timber off-cuts can fill a small skip quickly if not packed down.23 A 6-yard "Mixed Waste" skip—often referred to as the "builder's skip"—is the national standard for this phase, providing enough capacity (50-60 bin bags) for these bulky materials.5

## **Internal Finishing and Specialized Waste Streams**

The final phase involves internal plastering, flooring, and electrical work. A significant regulatory hurdle in this phase is the disposal of plasterboard. Current UK legislation prohibits the mixing of plasterboard with general construction waste in a standard skip.20 Plasterboard must be segregated to prevent the release of hydrogen sulfide gas when buried with biodegradable waste.  
To manage this, self-builders can utilize "Grab Bags" or "Bulk Bags" specifically for plasterboard. Providers like RL Skip Hire and Isle of Wight Gardening and Landscaping offer 1-tonne plasterboard bags for approximately £150, which includes the cost of the bag, delivery, and collection.20 This is often more cost-effective for a garden room than hiring a dedicated plasterboard skip, which would likely go under-utilized.

## **Regulatory Framework and Environmental Compliance**

The Isle of Wight Council and the Environment Agency enforce strict regulations regarding the transfer and disposal of waste, particularly with the withdrawal of the Regulatory Position Statement (RPS) 250 on September 1, 2023\.27 This regulatory change has profound implications for waste wood recycling. Certain types of wood from buildings constructed before 2007, such as roof timbers, barge boards, and external joinery, are now automatically deemed hazardous unless a test certificate proves otherwise.27  
For the self-builder of a new garden room, this is primarily a concern if an existing structure is being demolished. Any waste wood originating from a pre-2007 structure must be handled with care. Small commercial waste contractors on the island have expressed concern that this regulation will increase disposal costs, as all wood must now be thoroughly checked at waste transfer stations.27 However, the Council has clarified that these rules do not apply to domestic recycling of waste wood at household waste recycling centers (HWRCs) like Lynnbottom, provided the waste is truly domestic.27

## **The Role of Mechanical Recycling Facilities**

Environmental stewardship is a significant point of differentiation among island providers. Westridge Skip Hire operates a licensed mechanical recycling facility on an 18-acre site, where they process waste to divert thousands of tonnes from landfills.6 They have also invested in environmentally friendly fleet vehicles, such as Euro 6 trucks, to minimize the carbon footprint of their operations.6 This focus on the "circular economy" is a critical consideration for self-builders who prioritize sustainability in their garden room projects.

## **Permits, Licenses, and Public Highway Obligations**

A mandatory requirement for any skip placed on public land on the Isle of Wight is the acquisition of a permit from Island Roads, the private contractor managing the island’s highway network.29 This is a legal requirement under the Highways Act 1980 and is intended to ensure that skips do not pose a danger to road users or pedestrians.

## **The Permitting Process and Fiscal Requirements**

The administration of skip permits is a high-friction point in project scheduling. The following data points outline the current permitting landscape on the island:

* **Financial Cost**: A skip license currently costs £42.00 per week when issued by Island Roads.29 Some providers, like Westridge, have quoted internal processing fees as low as £24 for seven days, but the standard council-mandated fee remains the primary benchmark.4  
* **Mandatory Lead Time**: A minimum of 10 working days is required to process a permit application.4 This timeline is absolute and cannot be fast-tracked, meaning self-builders must plan their waste management at least two weeks in advance of construction commencement.  
* **Duration and Renewal**: Permits are typically valid for 7 to 28 days.30 Extensions require a new application and fee.  
* **Liability and Safety**: The permit holder is responsible for ensuring the skip is appropriately lit at night and does not obstruct visibility at junctions.29

Most skip hire firms on the island offer to handle the permit application on behalf of the customer, integrating the cost into the final quote.3 For a self-builder, especially in a high-density area like Cowes, this service is invaluable as it transfers the administrative burden and legal liability to the professional provider.

## **Strategic Synthesis and Practical Recommendations**

The research into the Isle of Wight skip hire market reveals a robust and highly localized industry that is well-equipped to support small-scale residential developments like garden rooms. The central challenge for the consumer is not a lack of options, but rather the need for meticulous planning regarding waste streams and site access. The island's geography necessitates a provider who is not only price-competitive but also logistically agile.

## **Recommended Provider Selection by Project Need**

The following table serves as a strategic guide for matching specific project requirements with the most suitable service provider profiles identified in this study.

| Project Profile | Primary Need | Recommended Provider Strategy | Strategic Reasoning |
| :---- | :---- | :---- | :---- |
| **New Garden Room (SIPS)** | Eco-friendly disposal | Westridge Skip Hire | Extensive recycling facilities and Euro 6 fleet match the sustainability goals of SIPS projects.6 |
| **Groundwork Intensive** | Integrated services | West Wight Mini Skips | The ability to hire a mini digger and a skip from the same source simplifies logistical coordination.10 |
| **Restricted Cowes Site** | Technical access | Isle of Wight Skip Hire | Their willingness to perform site reconnaissance minimizes the risk of delivery failure in narrow lanes.4 |
| **High-Volume DIY** | Digital ease | Waste King | A streamlined online booking system and transparent pricing are ideal for tech-savvy self-builders.2 |
| **Small-Scale Interior Fix** | Specialized waste | RL Skip Hire | Focus on grab bags for plasterboard ensures compliance with segregation laws without the cost of a full skip.20 |

## **Final Recommendations for Self-Builders**

1. **Prioritize Waste Segregation**: The fiscal data clearly shows that "Inert" and "Rubble" skips are 50-60% cheaper than "Mixed Waste" skips.4 A self-builder should aim to use a dedicated rubble skip for foundations and a separate mixed skip for the structural phase.  
2. **Respect the 10-Day Rule**: The absolute requirement for 10 working days' notice for roadside permits is the single most common cause of project delays.5 Planning skip delivery alongside material delivery is essential.  
3. **Utilize "Wait and Load" for High-Traffic Areas**: In Cowes, the cost of a permit (£42) plus the potential for neighborhood friction may make "Wait and Load" a more attractive and cost-neutral option for quick waste removals.17  
4. **Confirm Insurance and Licenses**: Always verify that the chosen provider holds a current Waste Carrier License and public liability insurance.7 This protects the homeowner in the event of property damage during skip placement.  
5. **Address Plasterboard Separately**: Do not attempt to hide plasterboard in a general waste skip. The penalties for contaminated waste can far exceed the £150 cost of a dedicated plasterboard grab bag.26

In summary, the Isle of Wight offers a mature skip hire market with several high-trust, long-tenured providers. For a garden room project, the optimal strategy involves a tiered approach to waste: using inert skips for groundworks, mixed skips for structural components, and specialized bags for finishing materials. By leveraging the local expertise of Newport and Yarmouth-based firms, the self-builder can ensure their project remains compliant, cost-effective, and environmentally responsible.

#### **Works cited**

1. Skip Hire in Isle Of Wight and local area | Get Local Reviewed Skips, accessed March 19, 2026, [https://www.local-quotes.co.uk/skip-hire/isle-of-wight](https://www.local-quotes.co.uk/skip-hire/isle-of-wight)  
2. Skip Hire Isle of Wight, accessed March 19, 2026, [https://www.waste-king-skip-hire.co.uk/locations/skip-hire-isle-of-wight/](https://www.waste-king-skip-hire.co.uk/locations/skip-hire-isle-of-wight/)  
3. Skip Hire Cowes \- Cheap Skip Hire Prices, accessed March 19, 2026, [https://cheapskiphireprices.co.uk/locations/skip-hire-cowes/](https://cheapskiphireprices.co.uk/locations/skip-hire-cowes/)  
4. Isle of Wight Skip Hire, accessed March 19, 2026, [https://www.isleofwightskiphire.co.uk/](https://www.isleofwightskiphire.co.uk/)  
5. How to Hire a Skip \- Isle of Wight Skip Hire, accessed March 19, 2026, [https://www.isleofwightskiphire.co.uk/how-to-hire-a-skip/](https://www.isleofwightskiphire.co.uk/how-to-hire-a-skip/)  
6. Westridge Skip Hire, accessed March 19, 2026, [https://westridge-skip-hire.co.uk/](https://westridge-skip-hire.co.uk/)  
7. Skip Hire Isle of Wight \- Top Choices, Pricing & Reviews \- Local Pick, accessed March 19, 2026, [https://localpick.co.uk/skip-hire-isle-of-wight/](https://localpick.co.uk/skip-hire-isle-of-wight/)  
8. Skip Hire Near Me in Isle Of Wight | Yell Marketplace, accessed March 19, 2026, [https://www.yell.com/s/skip+hire-isle+of+wight.html](https://www.yell.com/s/skip+hire-isle+of+wight.html)  
9. Skip Hire Near Me in Newport, Isle Of Wight | Yell Marketplace, accessed March 19, 2026, [https://www.yell.com/s/skip+hire-newport-isle+of+wight.html](https://www.yell.com/s/skip+hire-newport-isle+of+wight.html)  
10. West Wight Mini Skips: Skip Hire and Building Materials, accessed March 19, 2026, [https://www.westwightskips.com/](https://www.westwightskips.com/)  
11. Isle of Wight Skip Hire, accessed March 19, 2026, [https://www.westwightskips.com/skip-hire-on-the-isle-of-wight/](https://www.westwightskips.com/skip-hire-on-the-isle-of-wight/)  
12. Cheap Skips (IW) Ltd: Skip hire company, accessed March 19, 2026, [https://www.iowcheapskips.com/](https://www.iowcheapskips.com/)  
13. Skip Bags Near Me in Newport, Isle Of Wight | Yell Marketplace, accessed March 19, 2026, [https://www.yell.com/s/skip+bags-newport-isle+of+wight.html](https://www.yell.com/s/skip+bags-newport-isle+of+wight.html)  
14. Skip Hire \- Reliable Skip \- Local Skip Hire Near You, accessed March 19, 2026, [https://www.reliableskip.com/](https://www.reliableskip.com/)  
15. Reliable Skip Hire Isle of Wight \- Affordable Skip Hire \[Variety Of Sizes\], accessed March 19, 2026, [https://www.reliableskiphireisleofwight.co.uk/](https://www.reliableskiphireisleofwight.co.uk/)  
16. Cheap Skips I W Ltd, Newport | Skip Hire \- Yell, accessed March 19, 2026, [https://www.yell.com/biz/cheap-skips-i-w-ltd-newport-8403736/](https://www.yell.com/biz/cheap-skips-i-w-ltd-newport-8403736/)  
17. Skip Hire Isle of Wight, accessed March 19, 2026, [https://ckbskiphire.co.uk/skip-hire-isle-of-wight/](https://ckbskiphire.co.uk/skip-hire-isle-of-wight/)  
18. Wait and Load Skip Hire \- Mick George \- From £99 \- Next Day Delivery, accessed March 19, 2026, [https://www.mickgeorge.co.uk/waste-management/skip-hire/wait-and-load](https://www.mickgeorge.co.uk/waste-management/skip-hire/wait-and-load)  
19. Wait and Load Skip Hire \- Waste Management \- Mick George, accessed March 19, 2026, [https://www.mickgeorge.co.uk/product/waste/skips/wait-and-load-skip-hire-online](https://www.mickgeorge.co.uk/product/waste/skips/wait-and-load-skip-hire-online)  
20. 1-tonne grab bags at a competitive rate. \- Skip Hire Isle of Wight, accessed March 19, 2026, [https://www.rlskiphireisleofwight.co.uk/grab-bags](https://www.rlskiphireisleofwight.co.uk/grab-bags)  
21. Residential & Commercial Waste Removal in St Helens \- THE SKIP HIRE, accessed March 19, 2026, [https://www.theskiphire.co.uk/st-helens](https://www.theskiphire.co.uk/st-helens)  
22. Plant hire on the Isle of Wight \- West Wight Mini Skips, accessed March 19, 2026, [https://www.westwightskips.com/plant-hire/](https://www.westwightskips.com/plant-hire/)  
23. UKSIPs Tech Bulletin \- Sustainability:Layout 1 \- Sips Industries, accessed March 19, 2026, [https://www.sipsindustries.com/wp-content/uploads/2018/08/UK-SIPs-Technical-Bulletin-Sustainability.pdf](https://www.sipsindustries.com/wp-content/uploads/2018/08/UK-SIPs-Technical-Bulletin-Sustainability.pdf)  
24. Environment | SIP Builders \- SIPS UK, accessed March 19, 2026, [https://www.sips.uk.com/about-us/environment/](https://www.sips.uk.com/about-us/environment/)  
25. Trash Talk: How SIPs Reduce Construction Jobsite Waste, accessed March 19, 2026, [https://sips.premierbuildingsystems.com/blog/trash-talk-how-sips-reduce-construction-jobsite-waste](https://sips.premierbuildingsystems.com/blog/trash-talk-how-sips-reduce-construction-jobsite-waste)  
26. Plasterboard Waste Collection \- Isle of Wight Gardening Services, accessed March 19, 2026, [https://www.isleofwightgardeningandlandscaping.co.uk/product/plasterboard-bulk-bag/](https://www.isleofwightgardeningandlandscaping.co.uk/product/plasterboard-bulk-bag/)  
27. Isle of Wight waste contractors face new restrictions on wood recycling \- OnTheWight, accessed March 19, 2026, [https://onthewight.com/isle-of-wight-waste-contractors-face-new-restrictions-on-wood-recycling/](https://onthewight.com/isle-of-wight-waste-contractors-face-new-restrictions-on-wood-recycling/)  
28. Asbestos and plasterboard \- Isle of Wight Council, accessed March 19, 2026, [https://www.iow.gov.uk/article/2571/Asbestos-and-plasterboard](https://www.iow.gov.uk/article/2571/Asbestos-and-plasterboard)  
29. Skip and Scaffolding Licences \- Island Roads, accessed March 19, 2026, [https://islandroads.com/our-services/skip-and-scaffolding-licences/](https://islandroads.com/our-services/skip-and-scaffolding-licences/)  
30. How to hire a skip \- Westridge Skip HireWestridge Skip Hire, accessed March 19, 2026, [https://westridge-skip-hire.co.uk/skip-hire-prices-on-the-isle-of-wight/how-to-hire-a-skip/](https://westridge-skip-hire.co.uk/skip-hire-prices-on-the-isle-of-wight/how-to-hire-a-skip/)  
31. Hire a Skip on the Isle of Wight, Skip Hire IOW UK, accessed March 19, 2026, [http://www.skiphireisleofwight.co.uk/skip-hire-faqs-skips-iow/](http://www.skiphireisleofwight.co.uk/skip-hire-faqs-skips-iow/)  
32. How Much Does Skip Hire Cost? (2025 Pricing Guide) \- The Waste Group, accessed March 19, 2026, [https://www.thewastegroup.co.uk/news/how-much-does-skip-hire-cost/](https://www.thewastegroup.co.uk/news/how-much-does-skip-hire-cost/)
