wisogetnid/garden-room/plans/cad-drawing/elevation-views.pdf

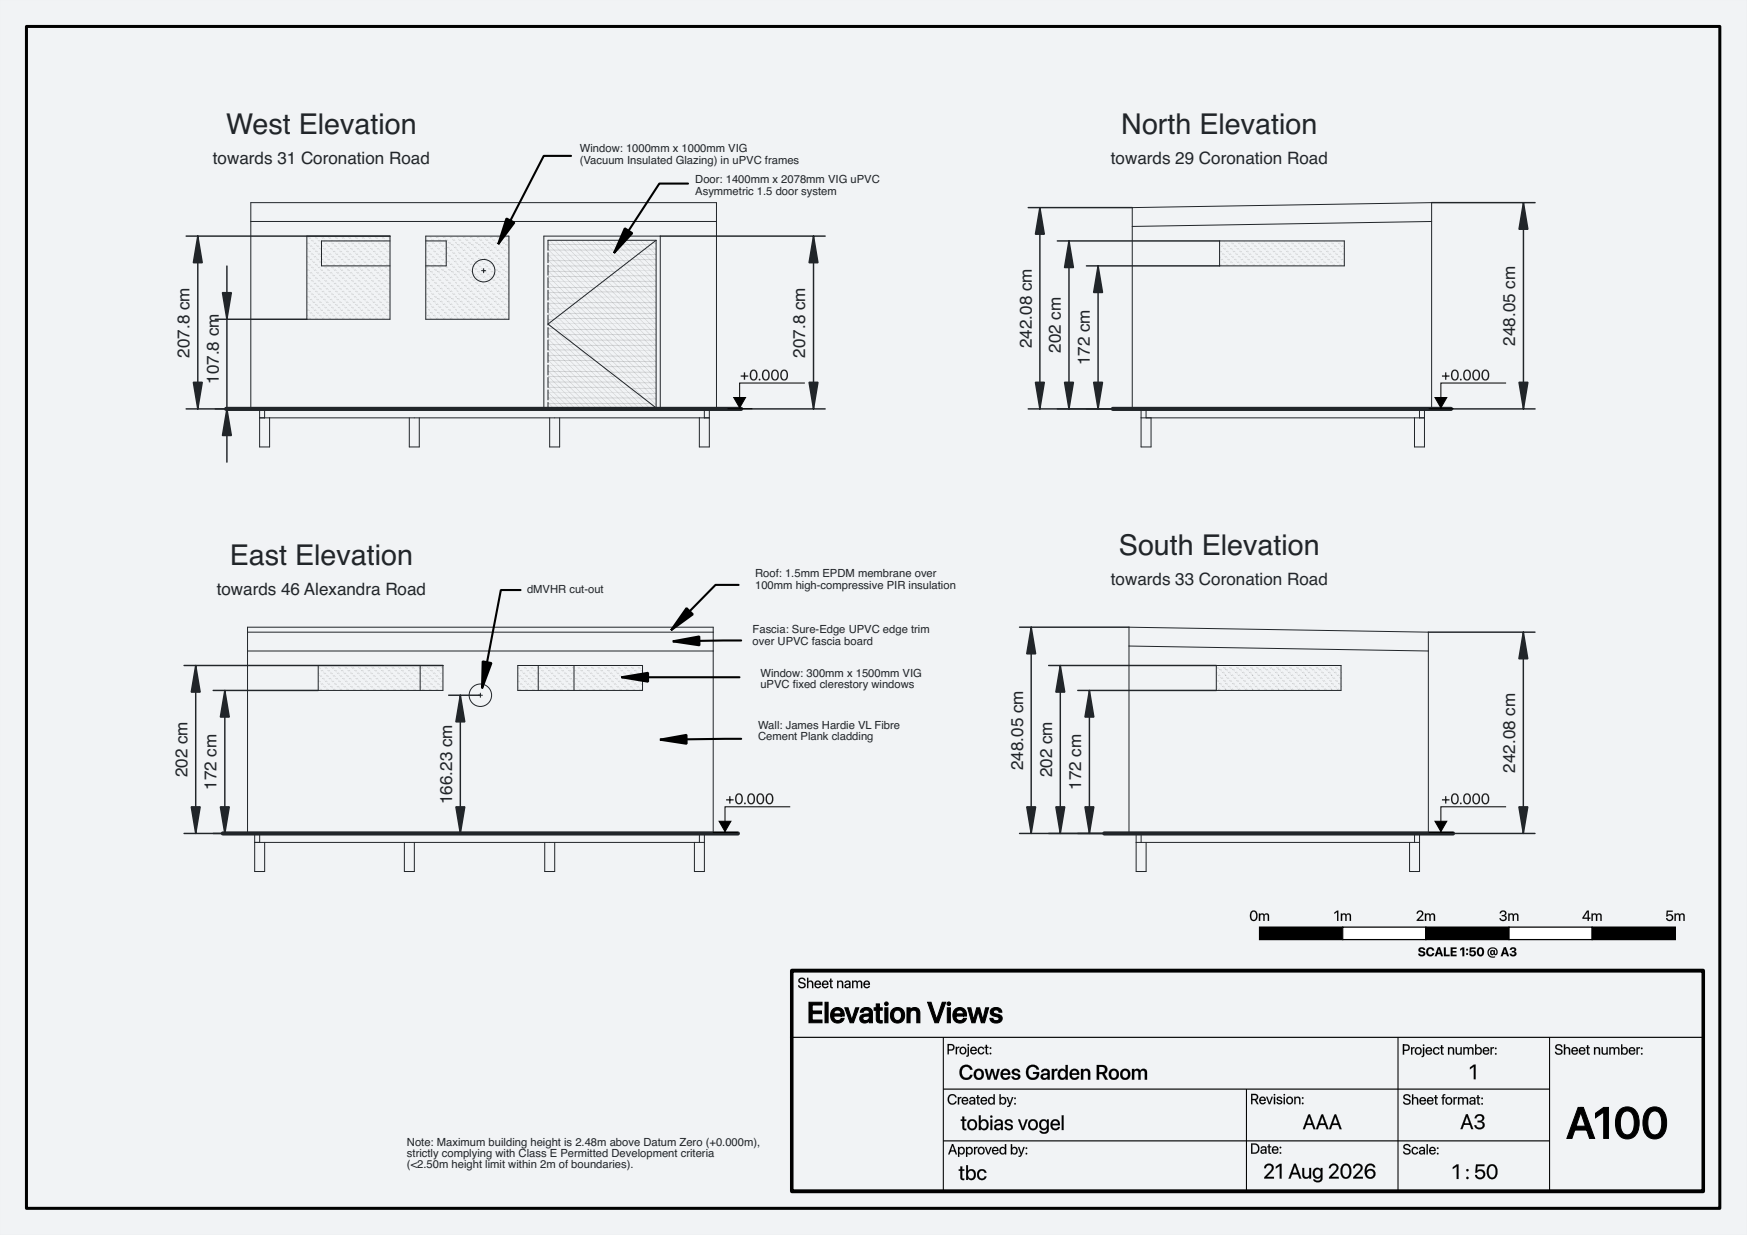
[picture p20: page 1]
West Elevation; North Elevation; East Elevation; South Elevation

Window: 1000mm x 1000mm VIG
(Vacuum Insulated Glazing) in uPVC frames Door: 1400mm x 2078mm VIG uPVC

towards 31 Coronation Road

towards 29 Coronation Road

Asymmetric 1.5 door system

Roof: 1.5mm EPDM membrane over 100mm high-compressive PIR insulation

towards 33 Coronation Road

towards 46 Alexandra Road

dMVHR cut-out

Fascia: Sure-Edge UPVC edge trim
over UPVC fascia board

Window: 300mm x 1500mm VIG
uPVC fixed clerestory windows

Wall: James Hardie VL Fibre Cement Plank cladding

Note: Maximum building height is 2.48m above Datum Zero (+0.000m), strictly complying with Class E Permitted Development criteria

(<2.50m height limit within 2m of boundaries).
