wisogetnid/garden-room/plans/cad-drawing/section-cut.pdf

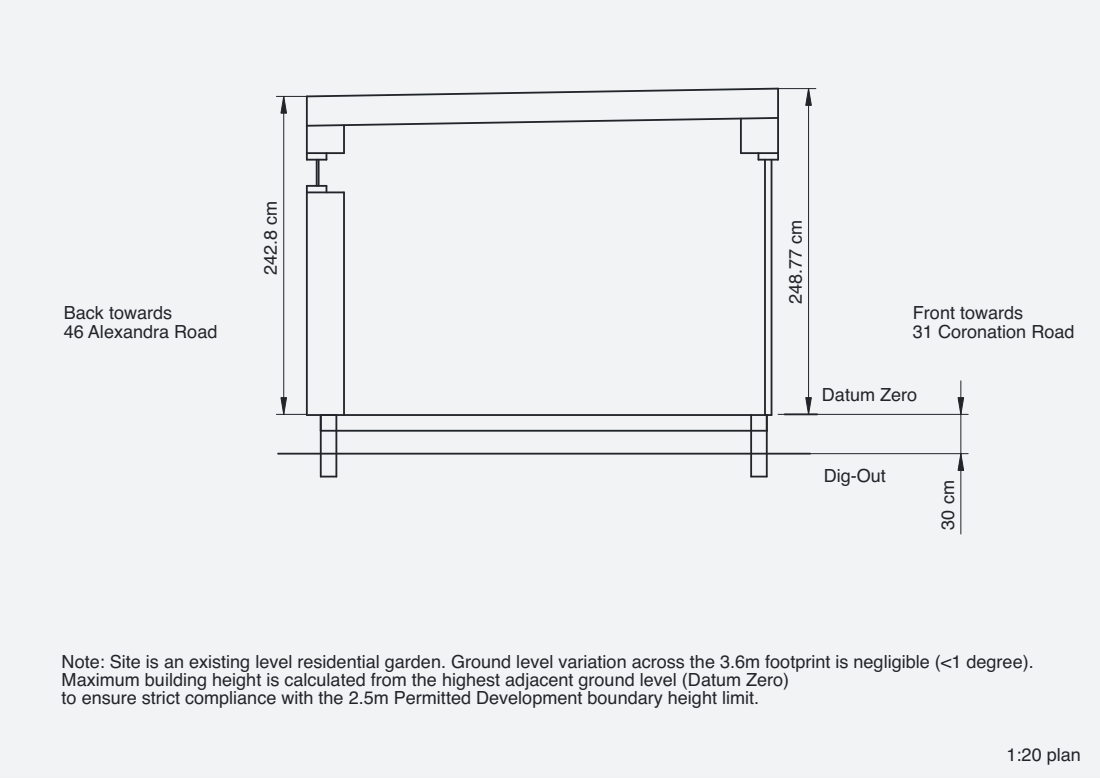
[picture p21: page 1]
Front towards 31 Coronation Road; Back towards 46 Alexandra Road; Datum Zero; 1:20 plan

Note: Site is an existing level residential garden. Ground level variation across the 3.6m footprint is negligible (<1 degree). Maximum building height is calculated from the highest adjacent ground level (Datum Zero)

to ensure strict compliance with the 2.5m Permitted Development boundary height limit.
