wisogetnid/garden-room/plans/cad-drawing/floorplan.pdf

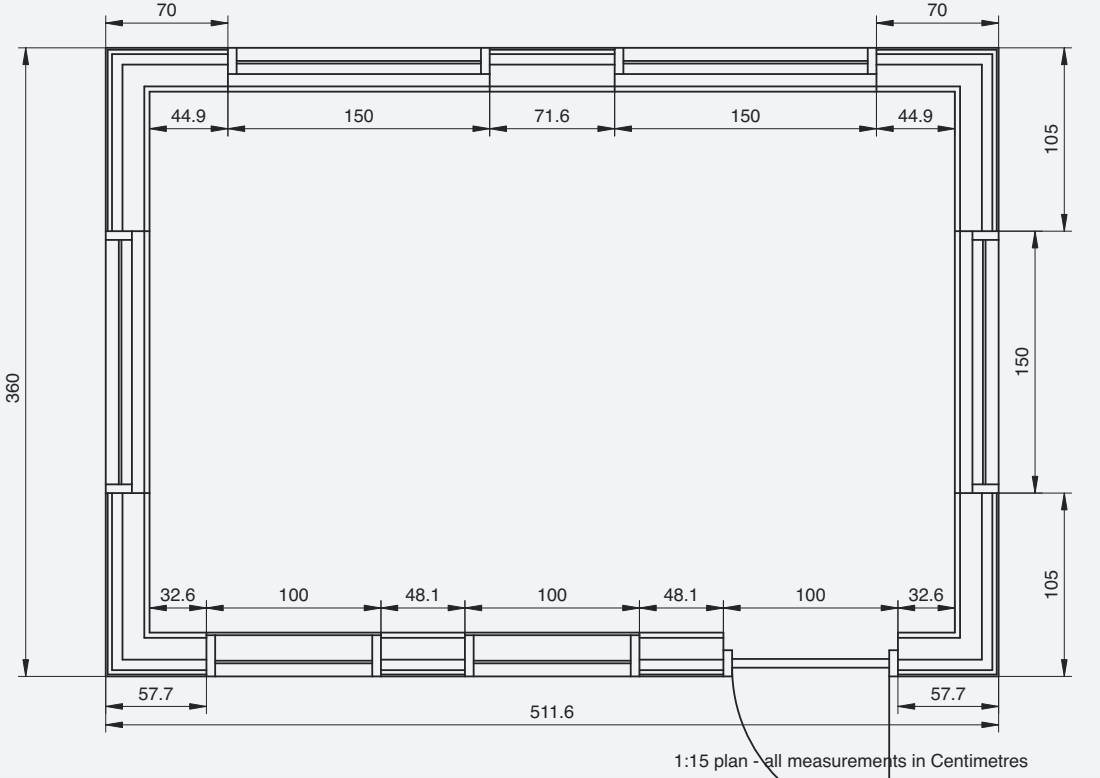
[picture p24: page 1]

1:15 plan - all measurements in Centimetres
