wisogetnid/garden-room/plans/cad-drawing/boundary-plan.pdf

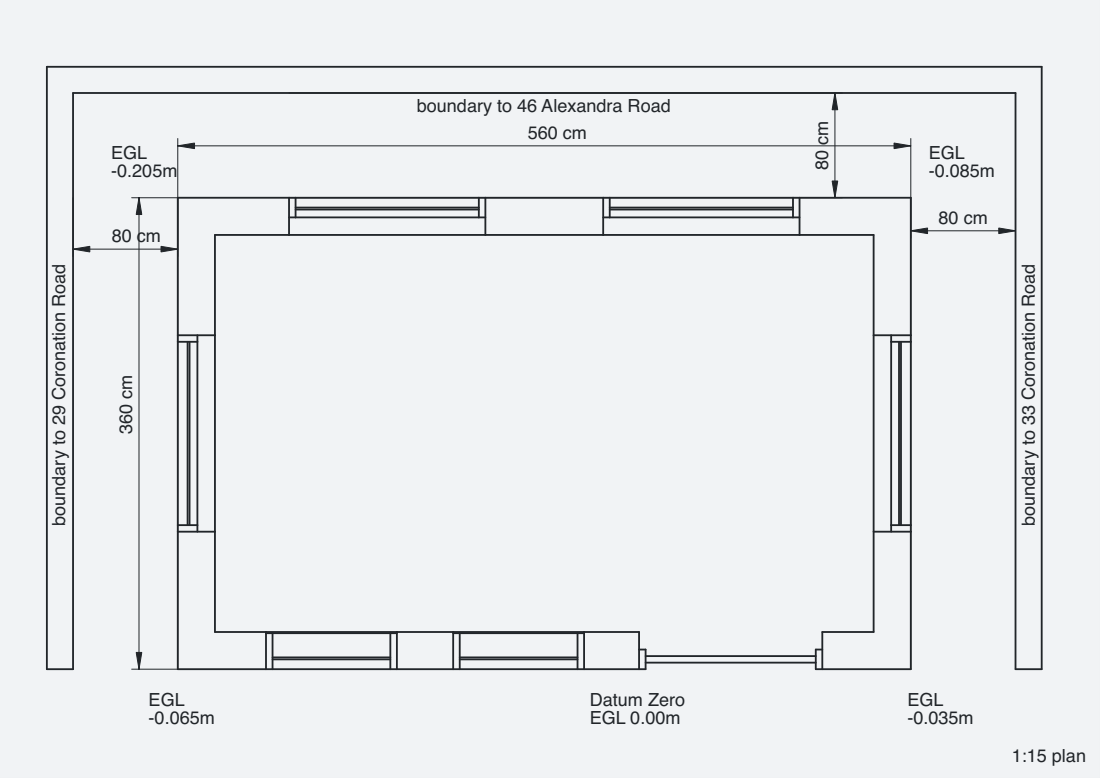
[picture p25: page 1]
ary to

boundary to 29 Coronation Road

boundary to 33 Coronation Road 1:15
